ned14/HouseBuild/designs/20230313 Earth Tube Layout.pdf

Revision | Date | Details

NOTES

ALL DRAWINGS TO BE PRINTED AT 100% SCALE. DO NOT FIT TO PRINTER MARGINS WHEN PRINTING. DO NOT SCALE DIMENSIONS FROM THE DRAWING. USE FIGURED DIMENSIONS ONLY.

1. | This | drawing | is | copyright | of | Rebel Design Studio.
Reproduction is only to take place with written authority.

### 2. These plans are subject to Planning & Building Regulation

Approval or any other statute in law before building work commences.

### 3. Any structural work where mentioned on this drawing is

subject to a qualified structural and civil engineer calculations before building work commences.

### 4. All boundaries are assumed. To be confirmed on site before

building work commences.

### 5. Any discrepancies are to be brought to the attention of Rebel

Design Studio for rectification. If in doubt, ASK.

### 6. Only drawings marked as CONSTRUCTION status can be used to

build or manufacture from.

### 7. All windows and doors shown on schedules and drawings are

indicative only and no manufacturing should be carried out until a site survey has been conducted by manufacturer.

### 8. The survey information shown on this drawing is based on a

survey prepared by a third party. Rebel Design Studio accept no responsibility for the accuracy or completeness of the survey.

Project Leader | SOL

# Douglas - Ard Na Si, Banteer

Drawing:

Stage:

# Earth Tube Layout

Project

Revision

Project Number | 21/020

# Technical Design

Drawing Number
110-101
Date | 13 March 2023

## 1:200, 1:100 Scale

Address | Ard Na Si Banteer Cork. 22 Chestnut Avenue,

Yiewsley,
West Drayton, UB78BT

info@rebeldesign-studio.com rebeldesign-studio.com

## 3,000 6,000 6,000 6,000 6,000 Approx. 3m 1,000

1,000

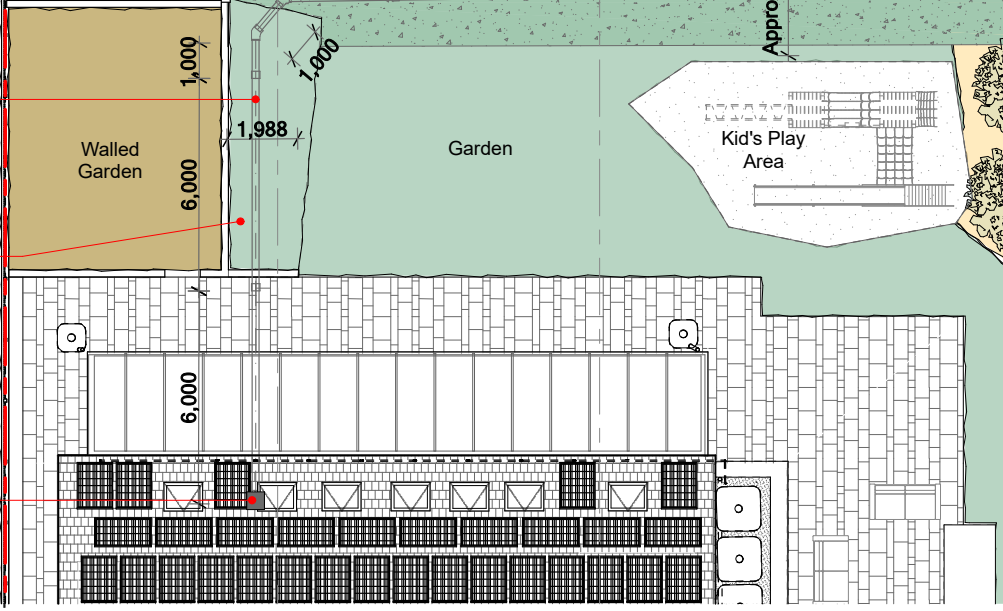
[picture p7: figure]
Walled Garden; Garden; Kid's Play Area

## Terrace Area

B
C

# Awadukt Thermo pipe DN 200 to have min. 1500mm cover . Exisng ground

levels to be made up where required.

# Condensaon collecon chamber DN 315/200 to be located in the Ulity

Room.

# Exisng mound to be excavated to allow for the installaon of the earth tube pipes. Mound to be be built up

to provide min. 1500mm cover.

# Exisng ground levels to be made up locally here to create 1500mm ground

cover - exact levels TBC on site.

# GAHE air inlet

tower DN 200.

## Reed Bed

+83,282

+80,259

+74,800 ²,700

+82,354 | Min. 1500mm cover
+74,534 | +74,493 | 2,200

1,000

## 6 m²

# Exisng tree and shrub planted embankment

and drainage channel.

# Secon of exisng embankment/ground to

be removed to allow for earth tube installaon.

# New earth tube laid at 4% fall from air inlet point

to change in direcon.

Approx. line of exisng embankment.

# New approx. outline of embankment to be created. Top of mound to be approx. 2.2m above the

proposed ground level for the enre length of the mound.

# New 2500mm deep condensaon collecon

sha. | New earth tube laid at 3%
| fall to chamber from
| change in direcon.

# Make up exisng ground levels locally to provide 1500mm min. ground

cover to earth tube run. | boundary line 2,500 | 500

1:100
0 | 2.5 | 5 | 7.5

1:200
0 | 7.5 | 15m

# Proposed GA Site Plan - Earth Tube Layout

1:200

# Proposed Secon CC - Earth Tube Dwg

1:100
