ned14/HouseBuild/designs/20220715 Diagram of works.pdf

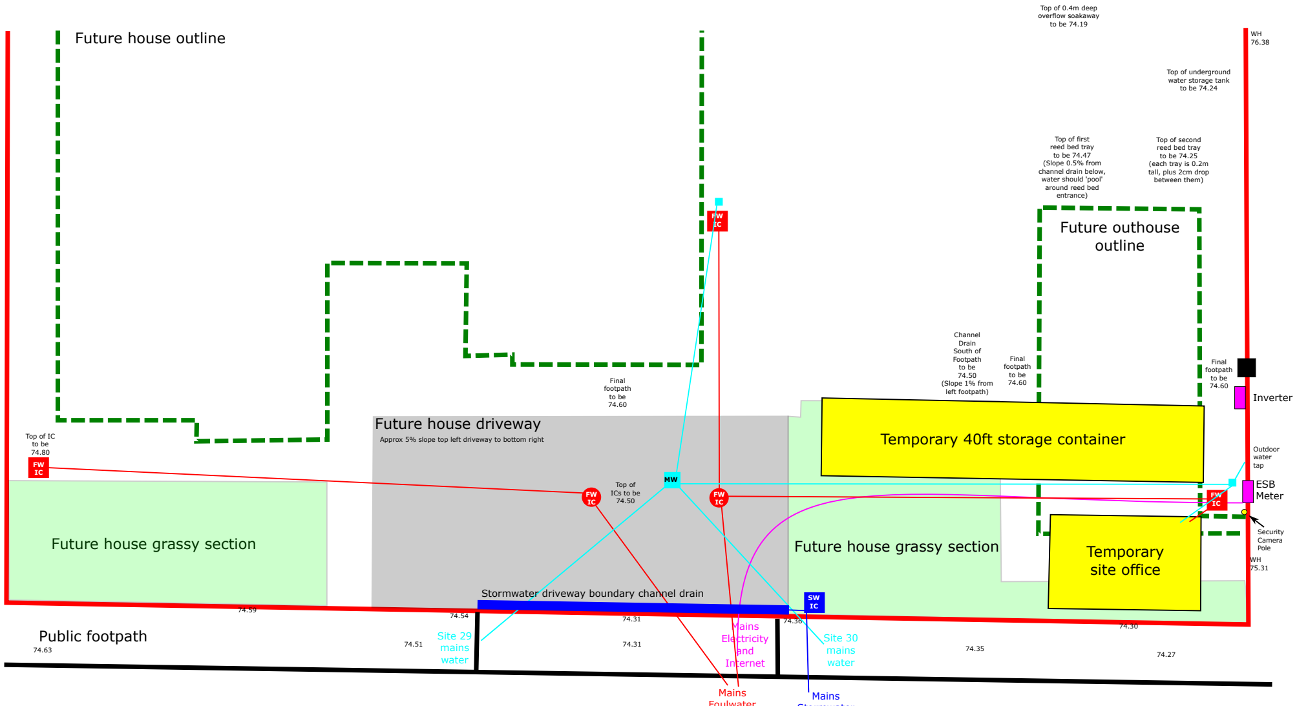
[picture p8: figure]
Future house driveway; Future house outline; Public footpath; Future outhouse outline; Final footpath to be 74.60; Top of IC to be 74.80; Channel Drain South of Footpath to be 74.50 (Slope 1% from left footpath); Top of first reed bed tray to be 74.47 (Slope 0.5% from channel drain below, water should 'pool' around reed bed entrance); Top of second reed bed tray to be 74.25 (each tray is 0.2m tall, plus 2cm drop between them); Top of ICs to be 74.50; Top of 0.4m deep overflow soakaway to be 74.19; Top of underground water storage tank to be 74.24; Temporary 40ft storage container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

Future house grassy section | Future house grassy section
74.36 | 74.27

Approx 5% slope top left driveway to bottom right

## Foulwater Stormwater

## Stormwater driveway boundary channel drain
