ned14/HouseBuild/tech_docs/CIG965 - Greenhouse.pdf

### Dimensions

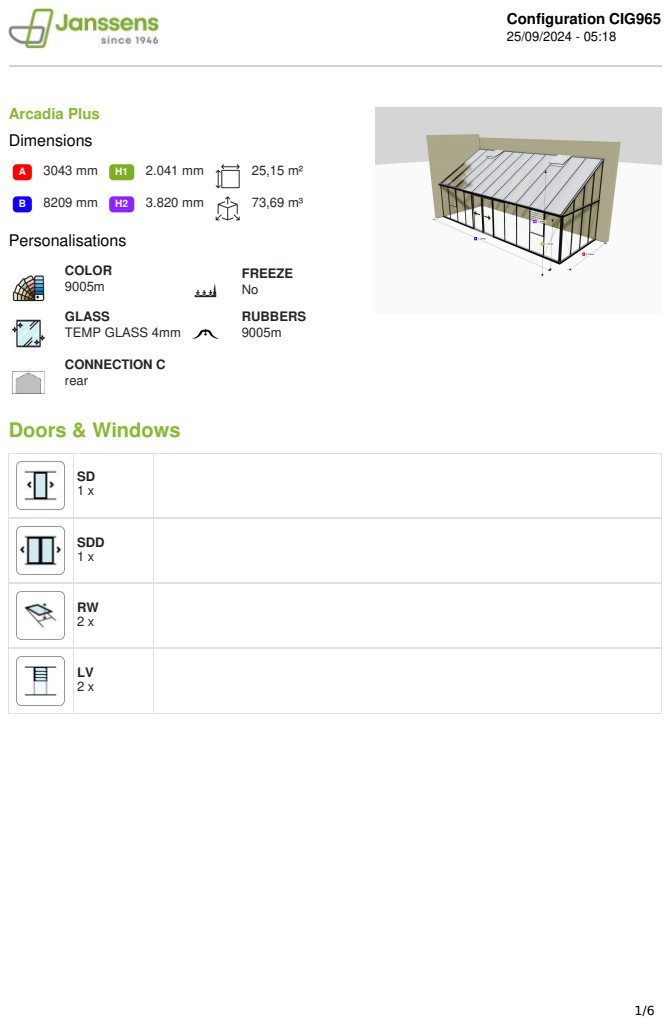
[picture p9: page 1]
Arcadia Plus; Personalisations; COLOR 9005m; FREEZE No; GLASS TEMP GLASS 4mm; RUBBERS 9005m; CONNECTION C rear; Doors & Windows; Configuration CIG965 25/09/2024 - 05:18

SDD 1 x

## 3D view

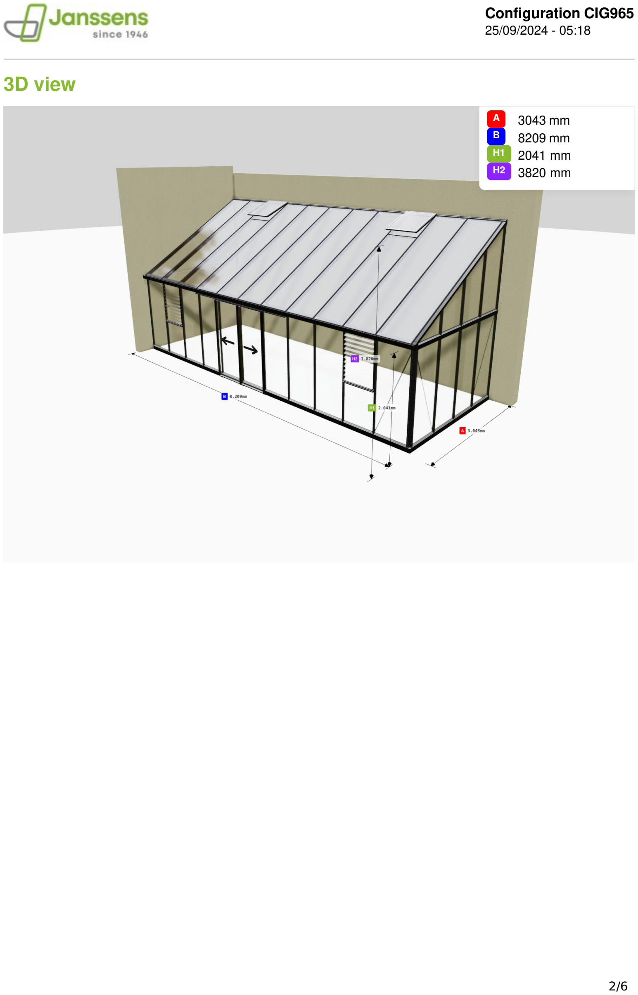
[picture p10: page 2]

25/09/2024 - 05:18

A
B
H1
H2

3043 mm
8209 mm
2041 mm
3820 mm

## Front side 1/100

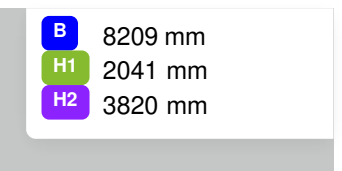
[picture p11: figure]

100cm

## Left side 1/100

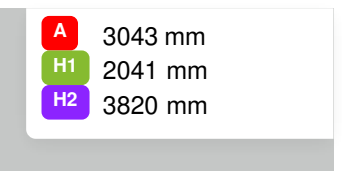
[picture p12: figure]

100cm

## Right side 1/100

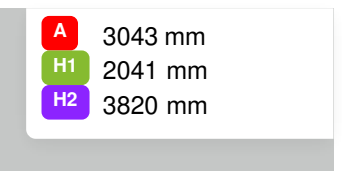
[picture p13: figure]

100cm

## Top side 1/100

100cm

A
B

3043 mm
8209 mm
