ned14/HouseBuild/tech_docs/LWR744 - Pool.pdf

### Dimensions

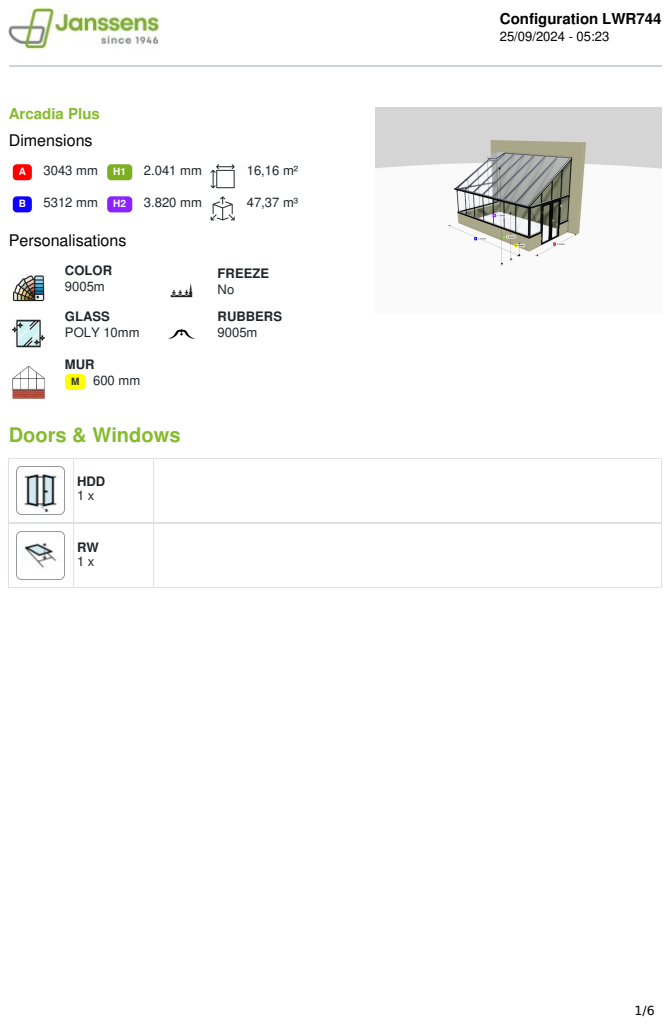
[picture p14: page 1]
Arcadia Plus; Personalisations; COLOR 9005m; FREEZE No; GLASS POLY 10mm; RUBBERS 9005m; MUR M 600 mm; Doors & Windows; Configuration LWR744 25/09/2024 - 05:23

HDD 1 x

## 3D view

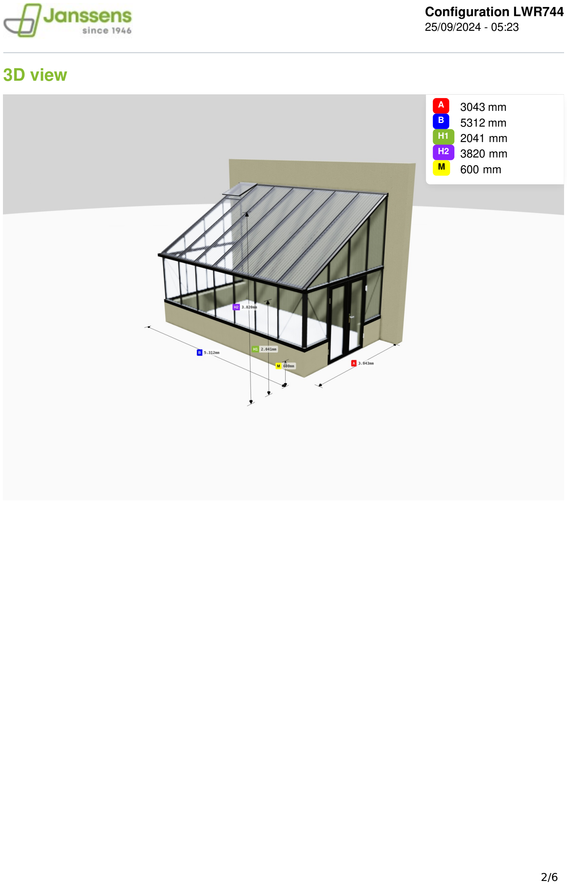
[picture p15: page 2]

25/09/2024 - 05:23

A
B
H1
H2
M

3043 mm
5312 mm
2041 mm
3820 mm
600 mm

## Front side 1/50

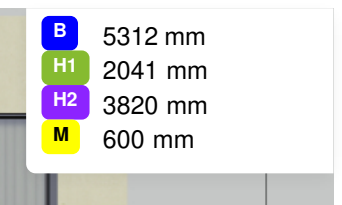
[picture p16: figure]

50cm

## Left side 1/50

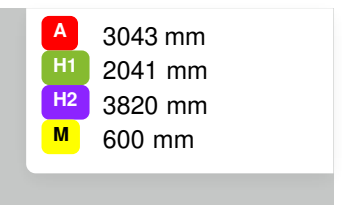
[picture p17: figure]

50cm

## Right side 1/50

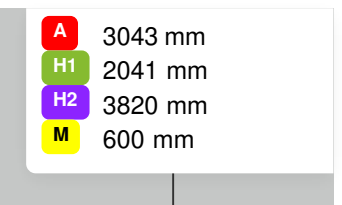
[picture p18: figure]

50cm

## Top side 1/50

50cm

A
B

3043 mm
5312 mm
