ned14/HouseBuild/tech_docs/ULS758 - Conservatory.pdf

### Dimensions

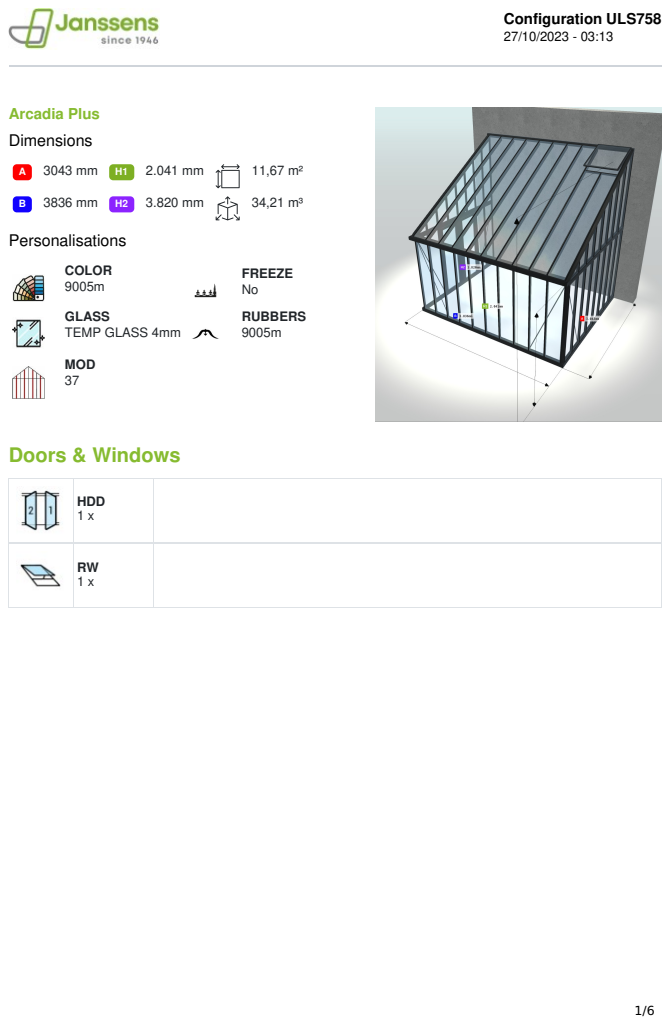
[picture p19: page 1]
Arcadia Plus; Personalisations; COLOR 9005m; FREEZE No; GLASS TEMP GLASS 4mm; RUBBERS 9005m; MOD 37; Doors & Windows; Configuration ULS758 27/10/2023 - 03:13

HDD 1 x

## 3D view

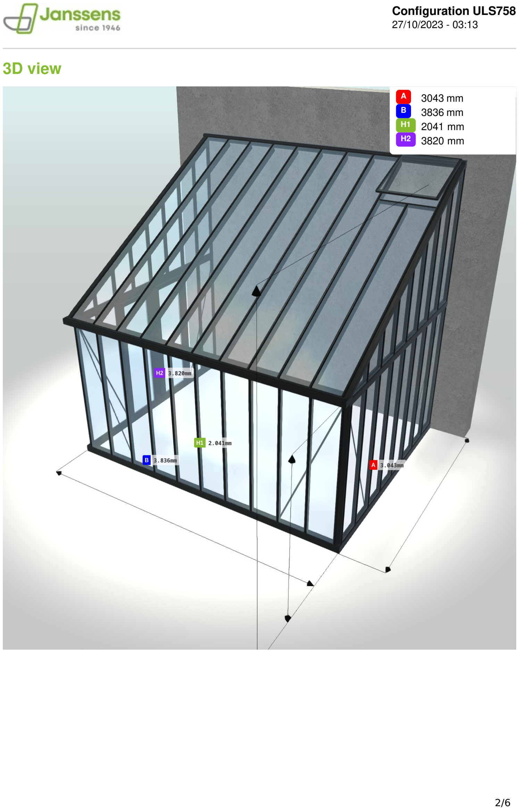
[picture p20: page 2]

27/10/2023 - 03:13

A
B
H1
H2

3043 mm
3836 mm
2041 mm
3820 mm

## Front side 1/50

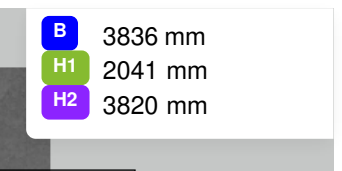
[picture p21: figure]

50cm

## Left side 1/50


50cm

## Right side 1/50

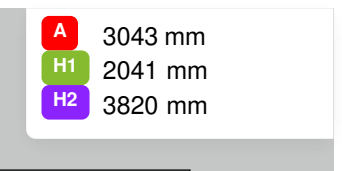
[picture p22: figure]

50cm

## Top side 1/50

50cm

A
B

3043 mm
3836 mm
