ned14/HouseBuild/designs/20210511 Original garden concept before house design.pdf

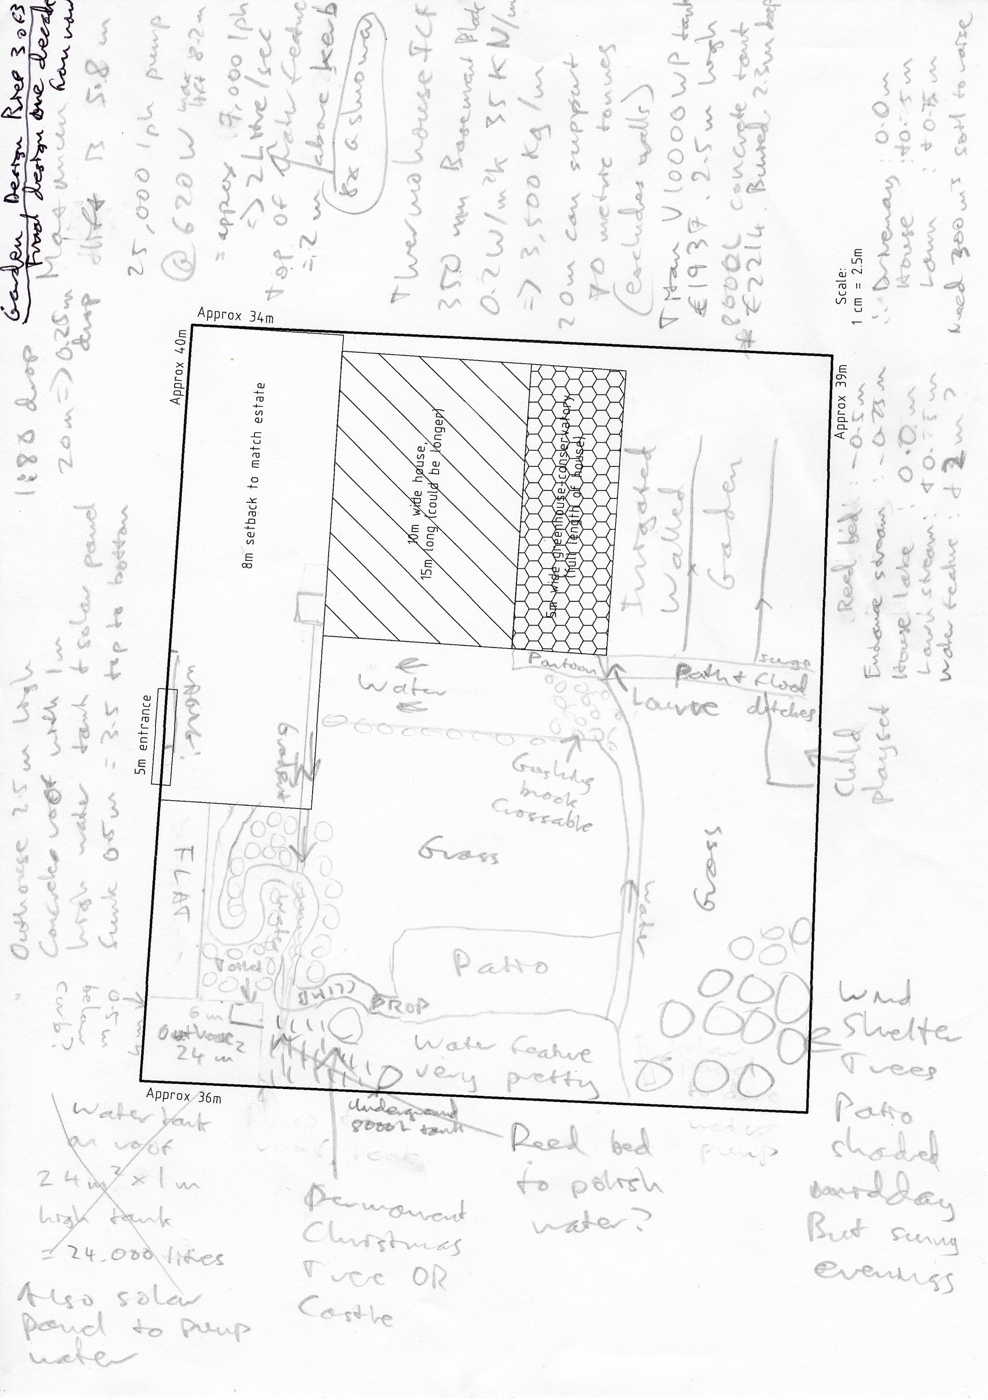
[picture p34: page 1]
