ned14/HouseBuild/designs/20220818 Large Scale Water Feature Concept.pdf

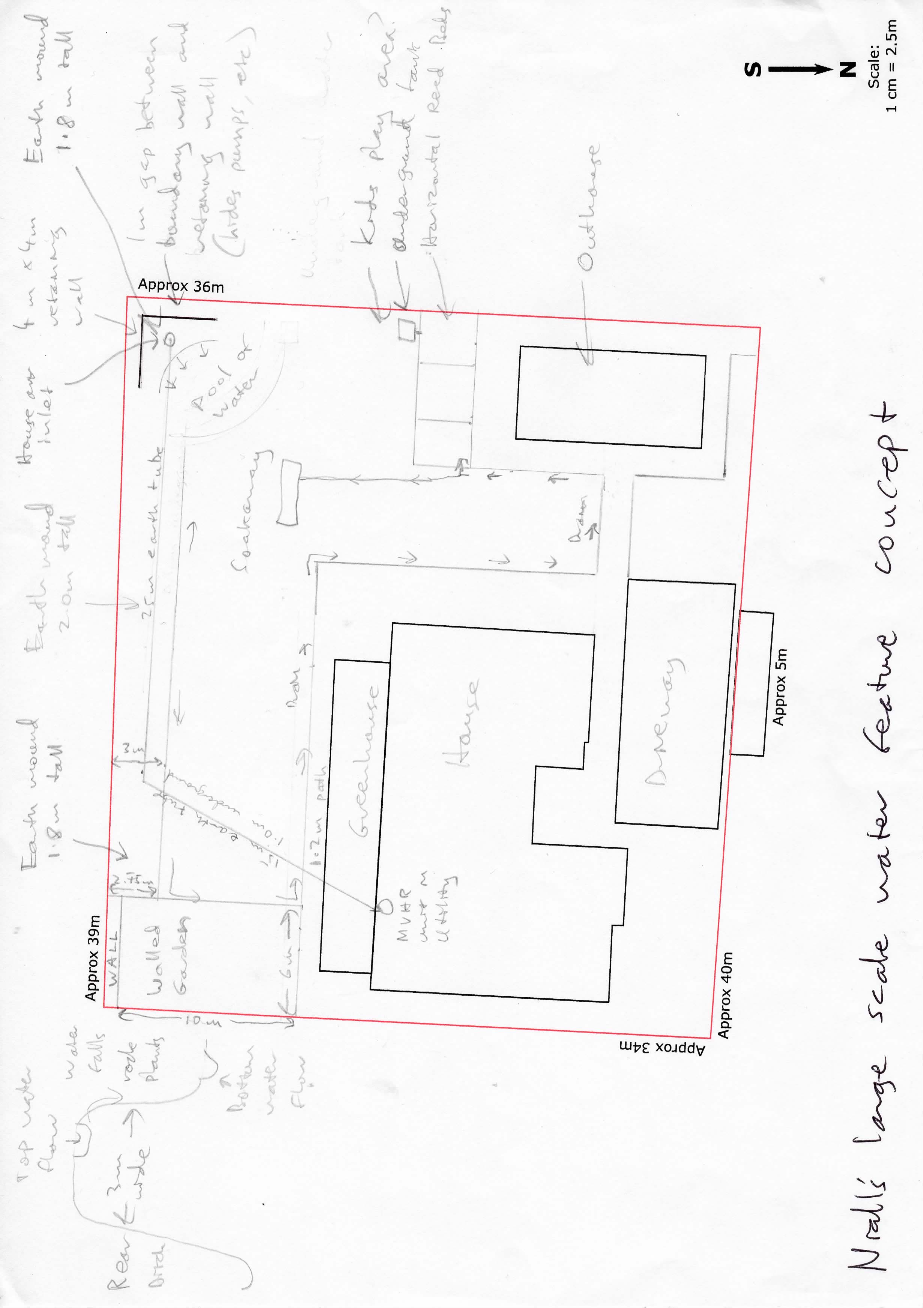
[picture p35: page 1]
