ned14/HouseBuild/images/202103/20210324_095312.jpg

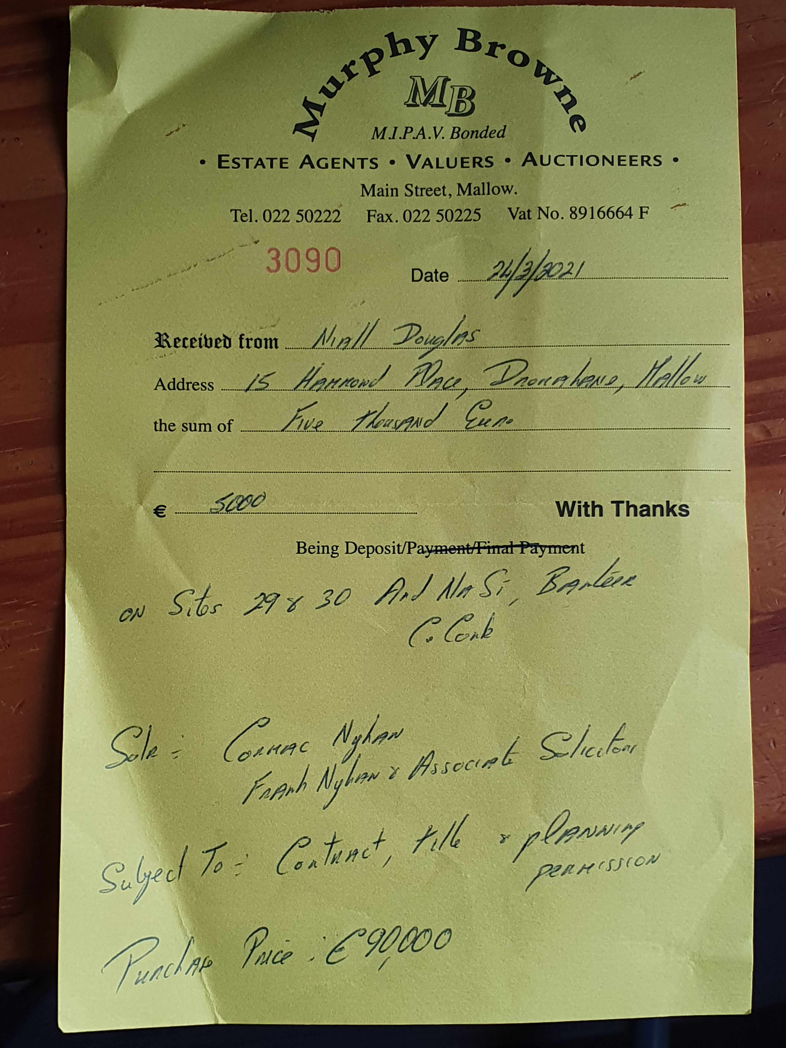
images/202103/20210324_095312.jpg
