ned14/HouseBuild/images/202103/surrounding_houses_sm.jpg

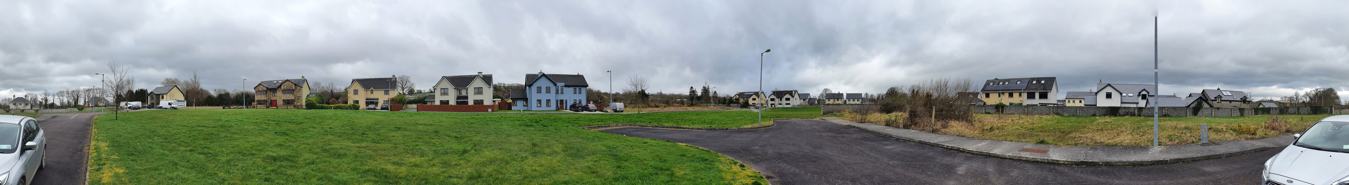
images/202103/surrounding_houses_sm.jpg
