ned14/HouseBuild/images/202103/view_to_the_south_zoomed_sm.jpg

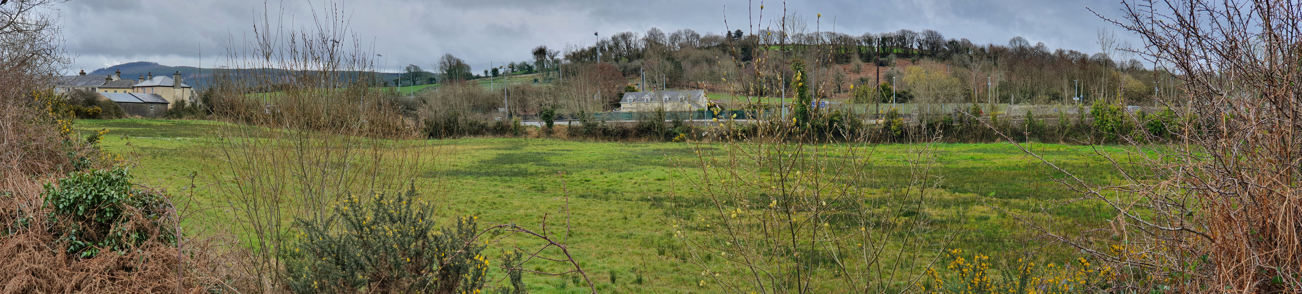
images/202103/view_to_the_south_zoomed_sm.jpg
