ned14/HouseBuild/images/202107/20210727_121713.jpeg

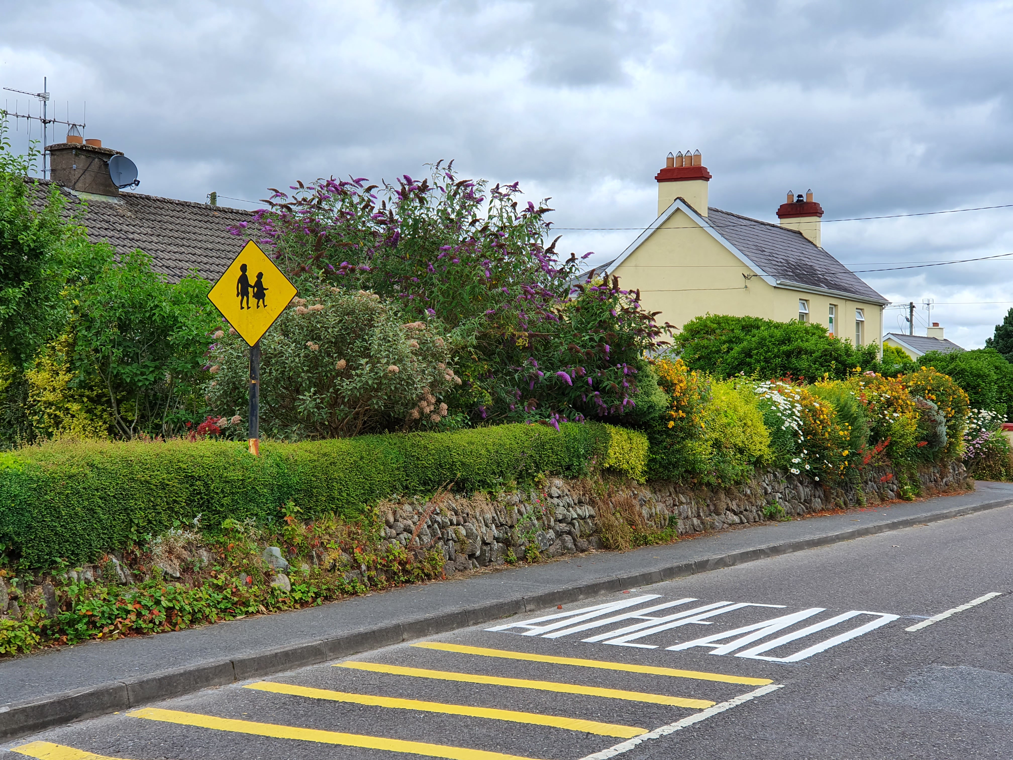
images/202107/20210727_121713.jpeg
