ned14/HouseBuild/images/202202/AerialView.jpg

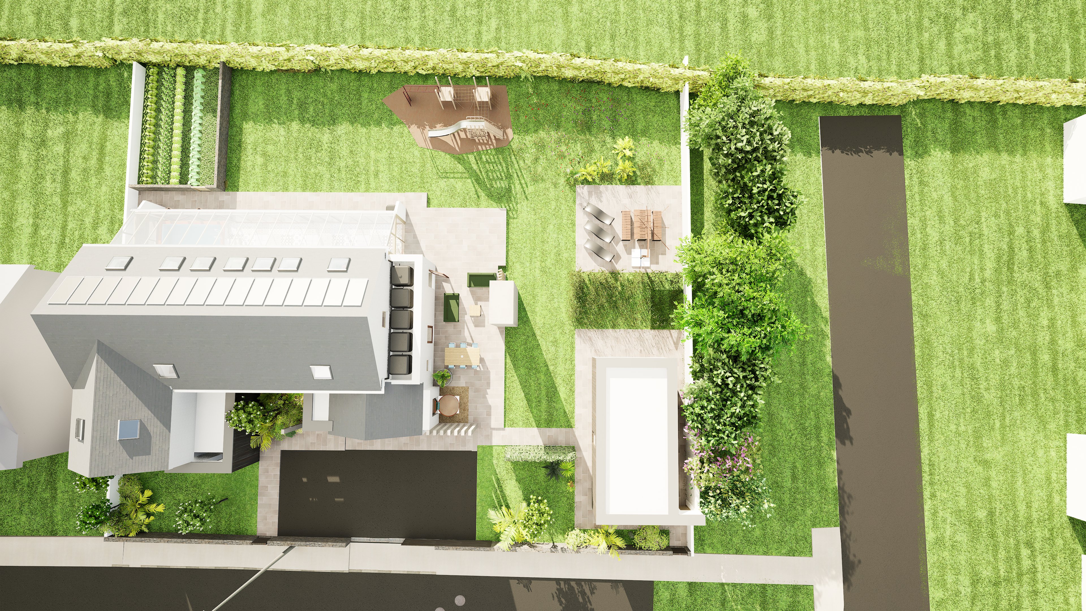
images/202202/AerialView.jpg
