ned14/HouseBuild/images/202202/BackCornerView.jpg

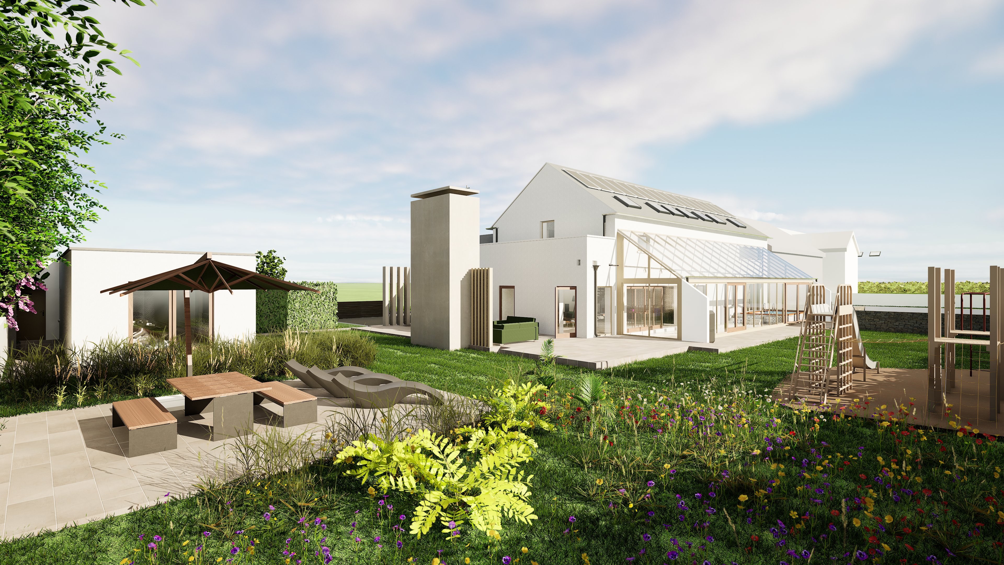
images/202202/BackCornerView.jpg
