ned14/HouseBuild/images/202202/BridgeLookingAtKitchen.jpg

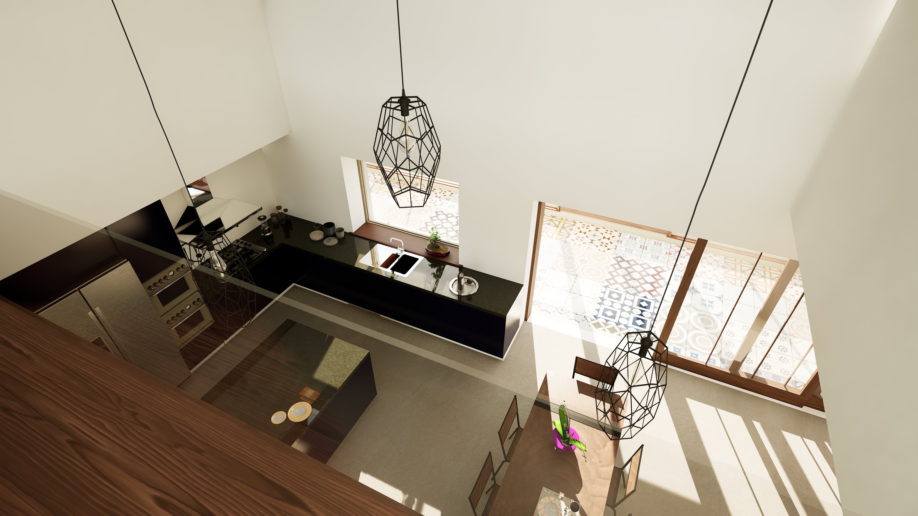
images/202202/BridgeLookingAtKitchen.jpg
