ned14/HouseBuild/images/202202/BridgeLookingAtMezzanine.jpg

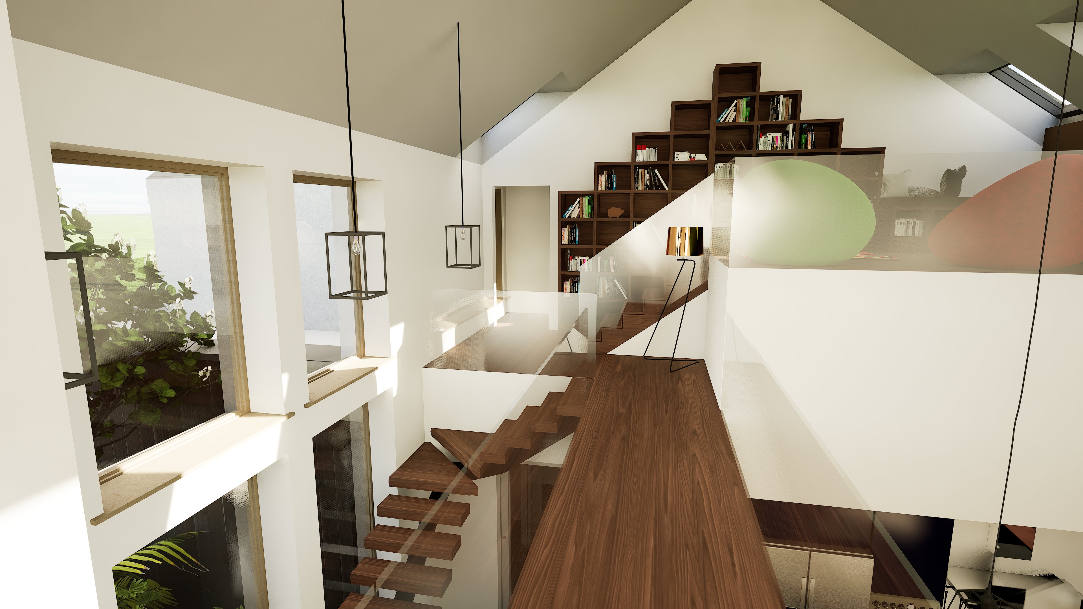
images/202202/BridgeLookingAtMezzanine.jpg
