ned14/HouseBuild/images/202202/GamesRoom.jpg

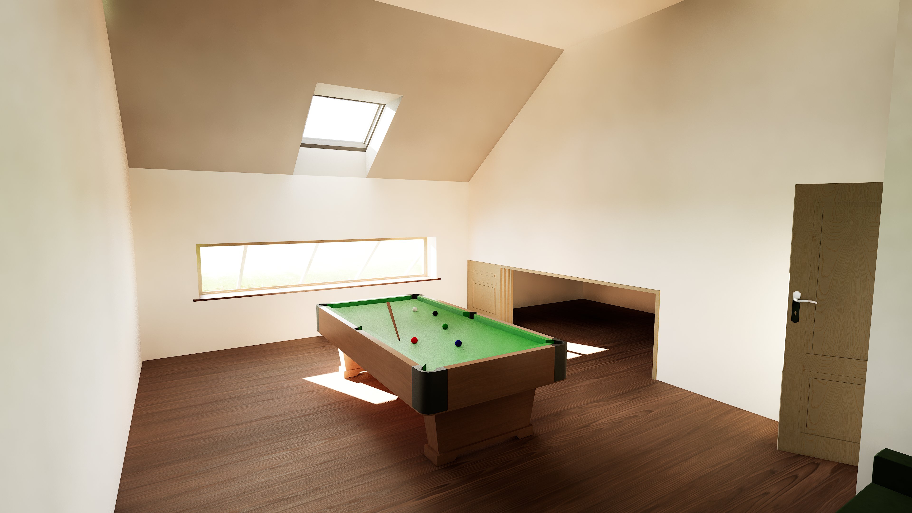
images/202202/GamesRoom.jpg
