ned14/HouseBuild/images/202202/GreenhouseDoorLookingUp.jpg

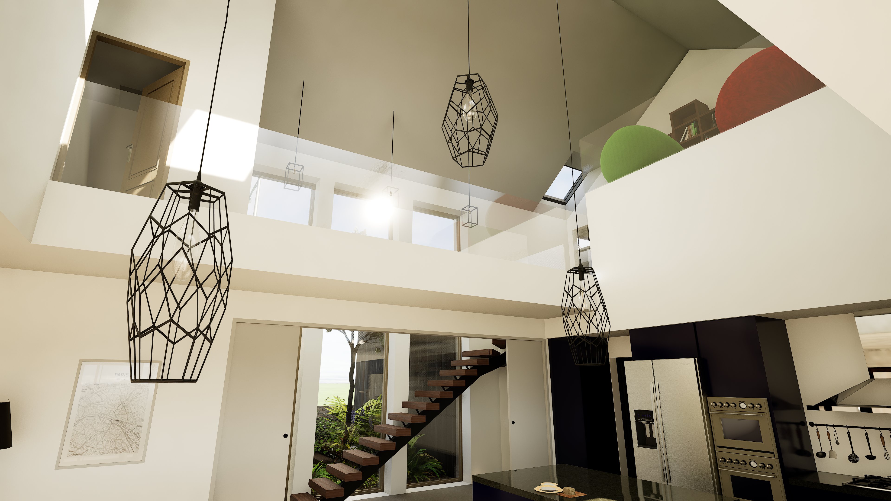
images/202202/GreenhouseDoorLookingUp.jpg
