ned14/HouseBuild/images/202202/KitchenLookingForwards.jpg

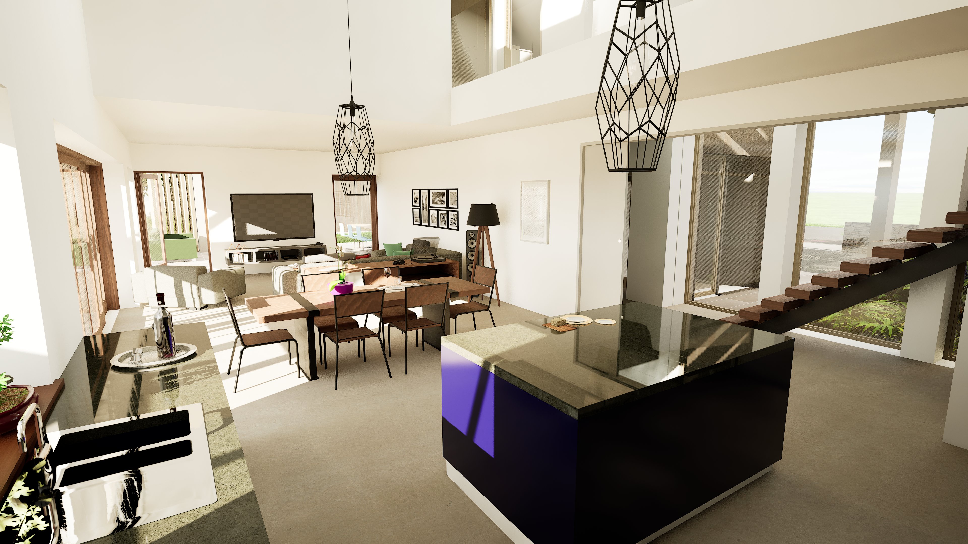
images/202202/KitchenLookingForwards.jpg
