ned14/HouseBuild/images/202202/KitchenLookingUp.jpg

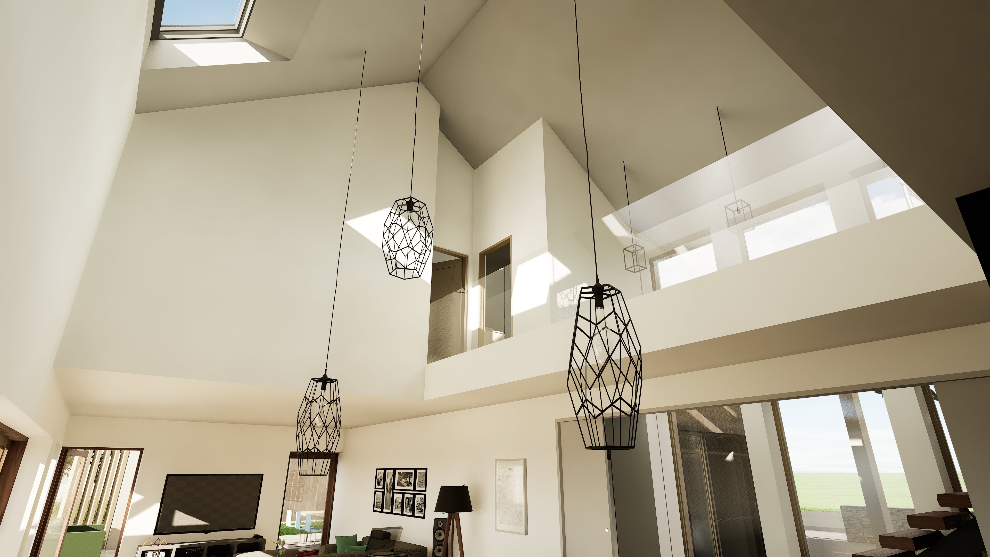
images/202202/KitchenLookingUp.jpg
