ned14/HouseBuild/images/202202/LarderDoorLookingOut.jpg

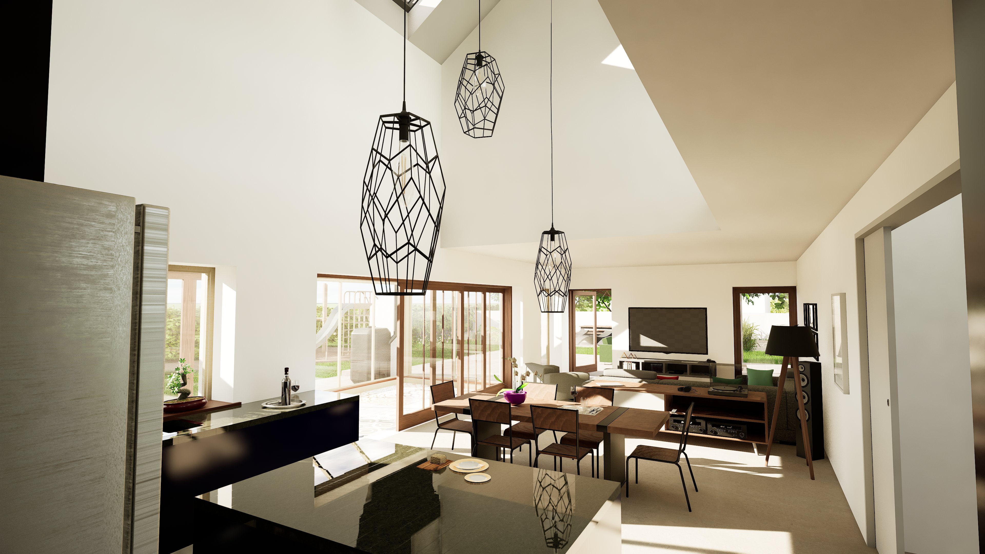
images/202202/LarderDoorLookingOut.jpg
