ned14/HouseBuild/images/202202/LivingRoomLookingAtKitchen.jpg

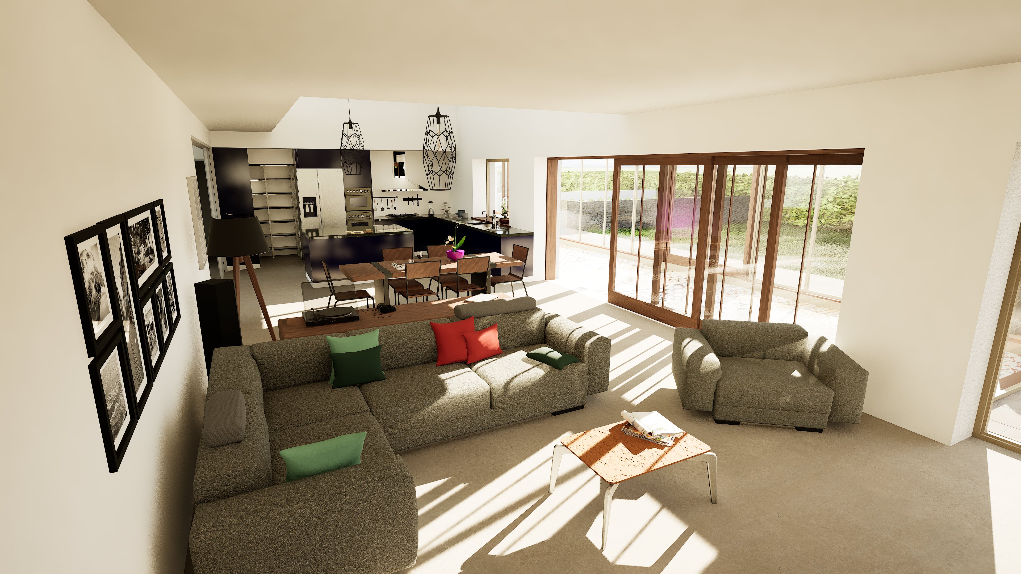
images/202202/LivingRoomLookingAtKitchen.jpg
