ned14/HouseBuild/images/202202/LobbyExitLookingAtKitchen.jpg

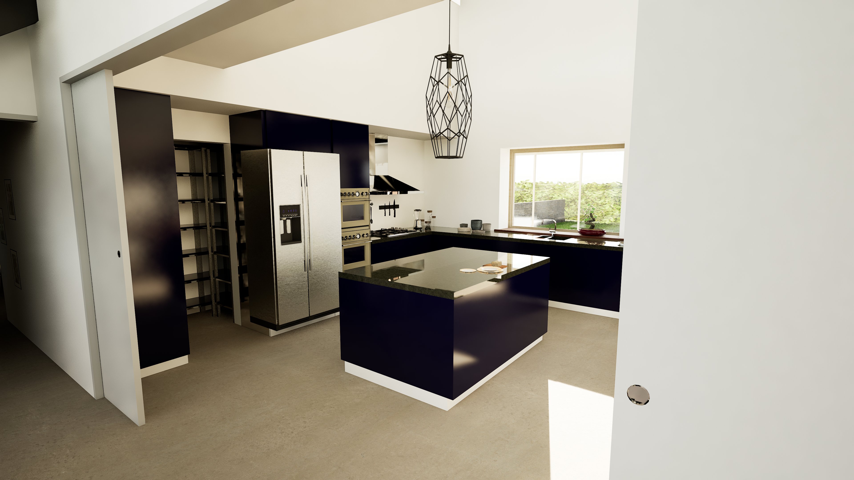
images/202202/LobbyExitLookingAtKitchen.jpg
