ned14/HouseBuild/images/202202/MainRoadAwayFromHouse.jpg

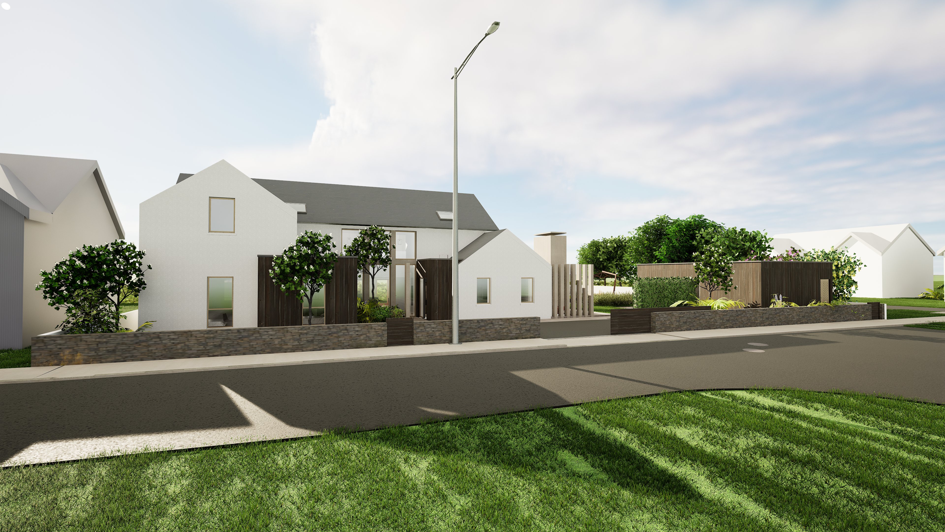
images/202202/MainRoadAwayFromHouse.jpg
