ned14/HouseBuild/images/202202/MainRoadFrontOfHouse.jpg

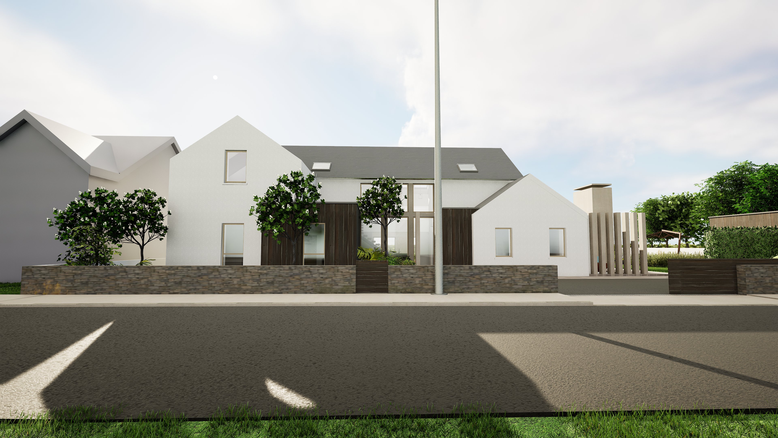
images/202202/MainRoadFrontOfHouse.jpg
