ned14/HouseBuild/images/202202/MainRoadOutsideSideView.jpg

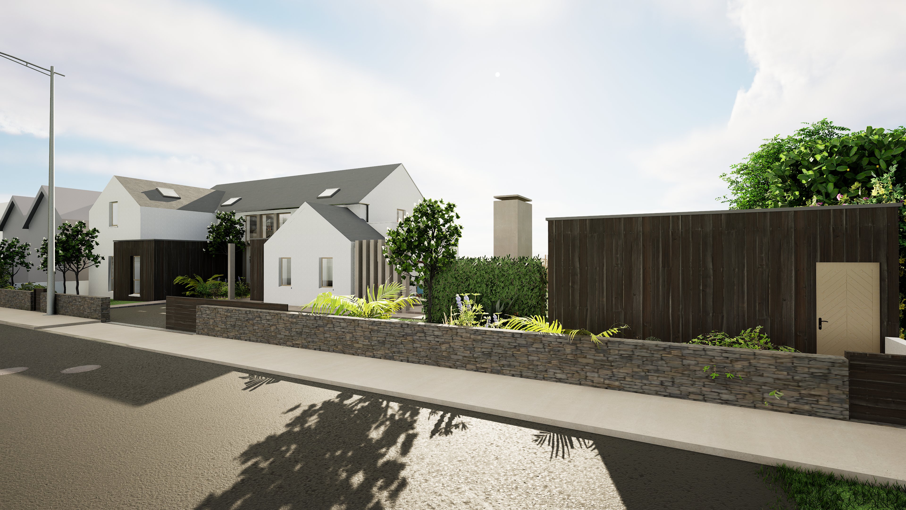
images/202202/MainRoadOutsideSideView.jpg
