ned14/HouseBuild/images/202202/MasterBedroom.jpg

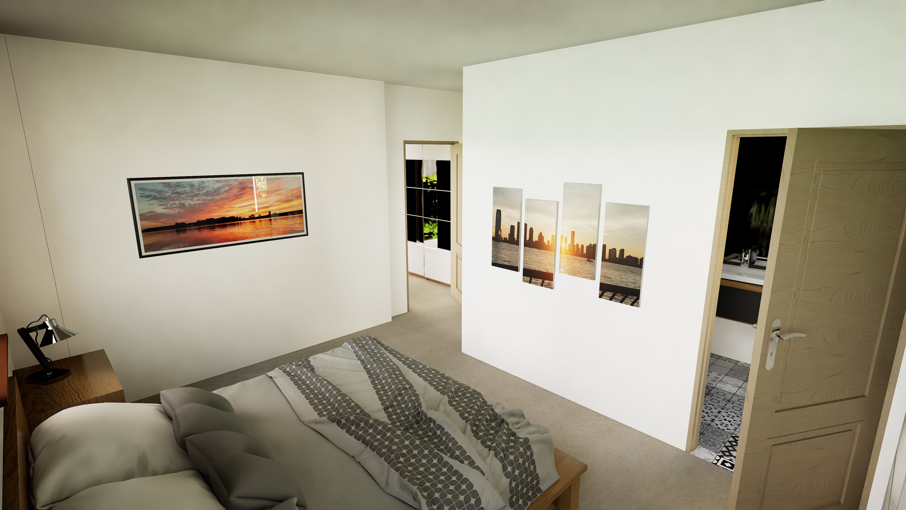
images/202202/MasterBedroom.jpg
