ned14/HouseBuild/images/202202/MezzanineLookingAtLiving.jpg

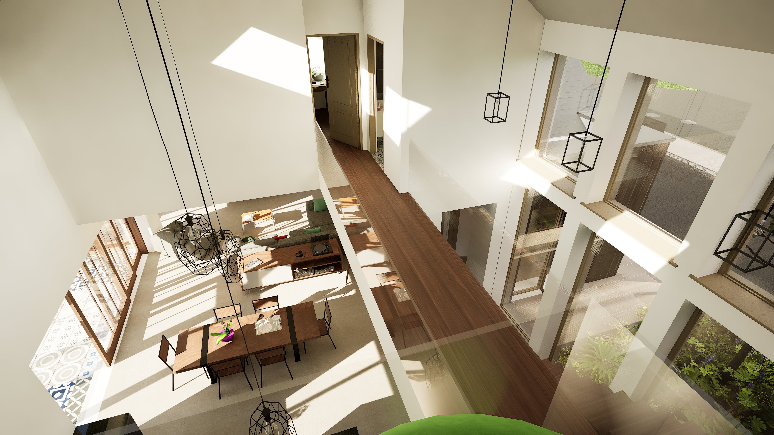
images/202202/MezzanineLookingAtLiving.jpg
