ned14/HouseBuild/images/202202/PatioDoorLookingIn.jpg

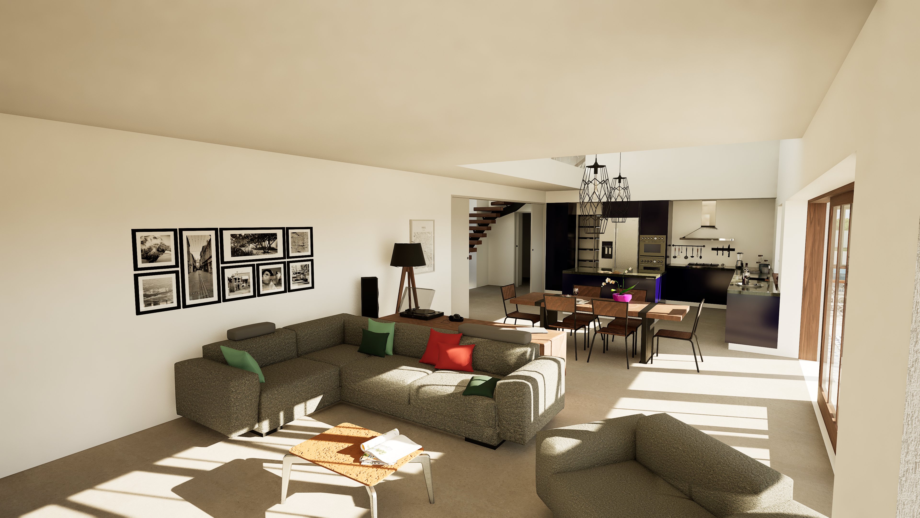
images/202202/PatioDoorLookingIn.jpg
