ned14/HouseBuild/images/202202/TopOfStairsLookingAtMezzanine.jpg

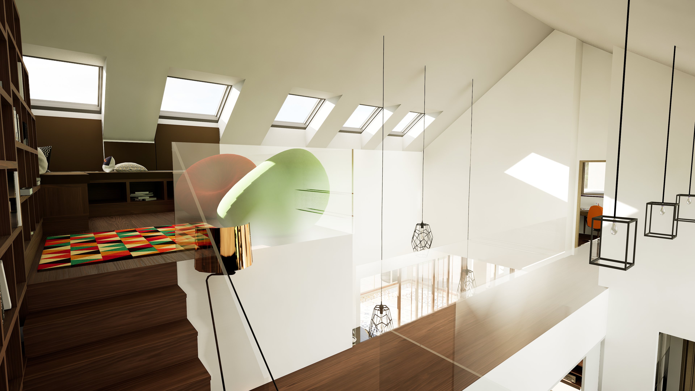
images/202202/TopOfStairsLookingAtMezzanine.jpg
