ned14/HouseBuild/images/202202/WalledGardenView.jpg

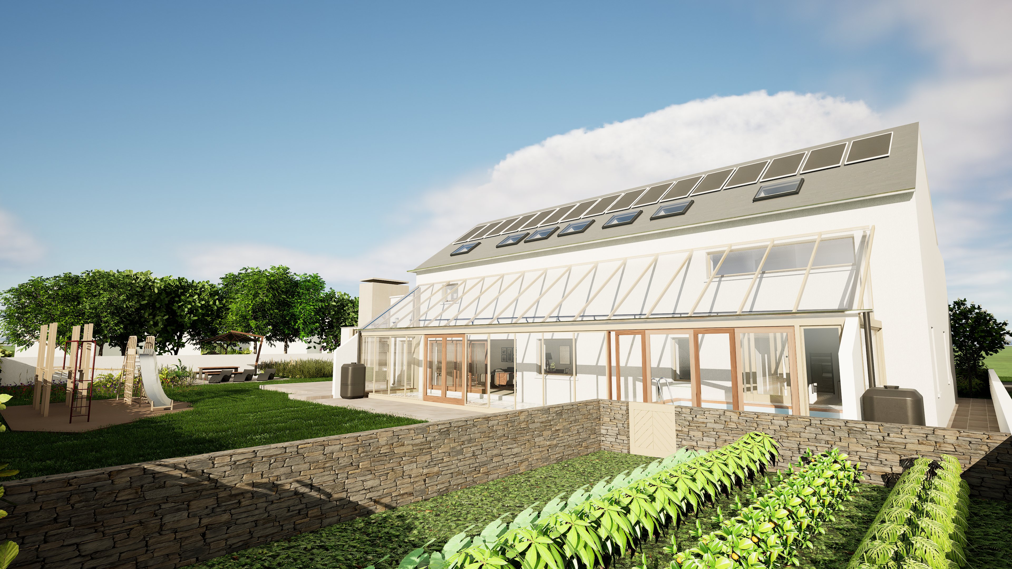
images/202202/WalledGardenView.jpg
