ned14/HouseBuild/images/202207/20220730_164701.jpg

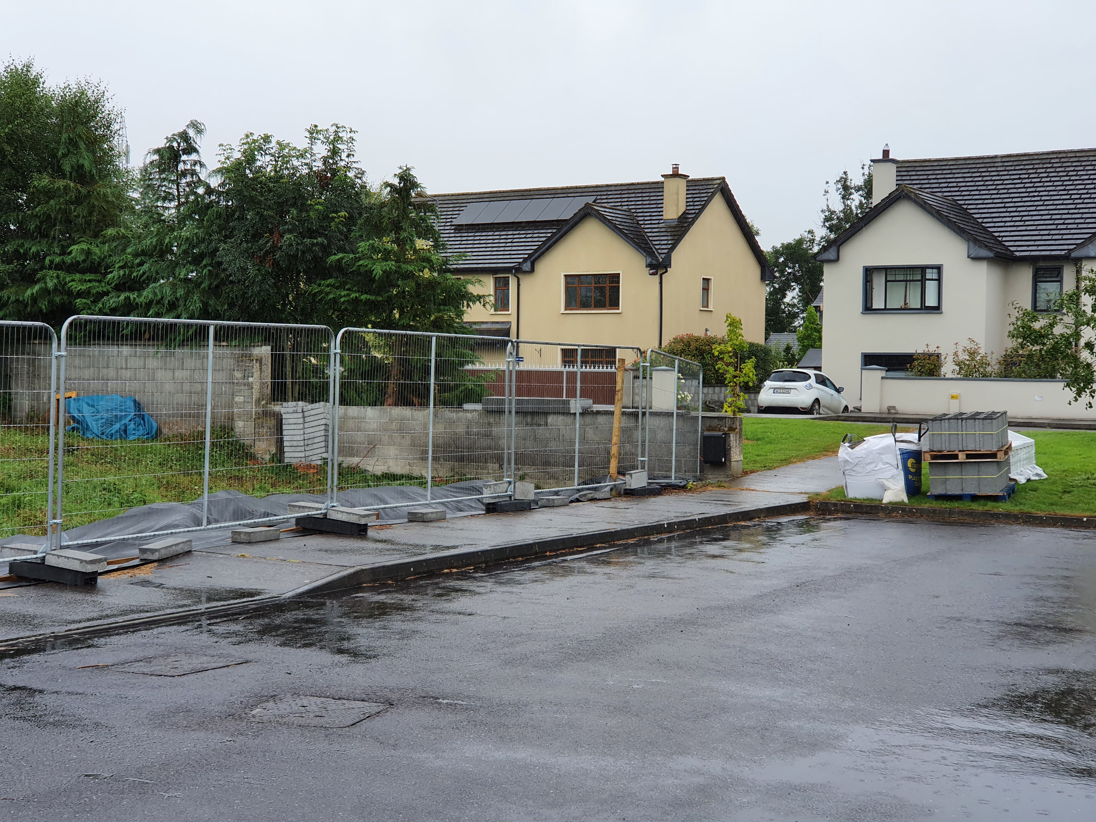
images/202207/20220730_164701.jpg
