ned14/HouseBuild/images/202208/20220801_213918.jpg

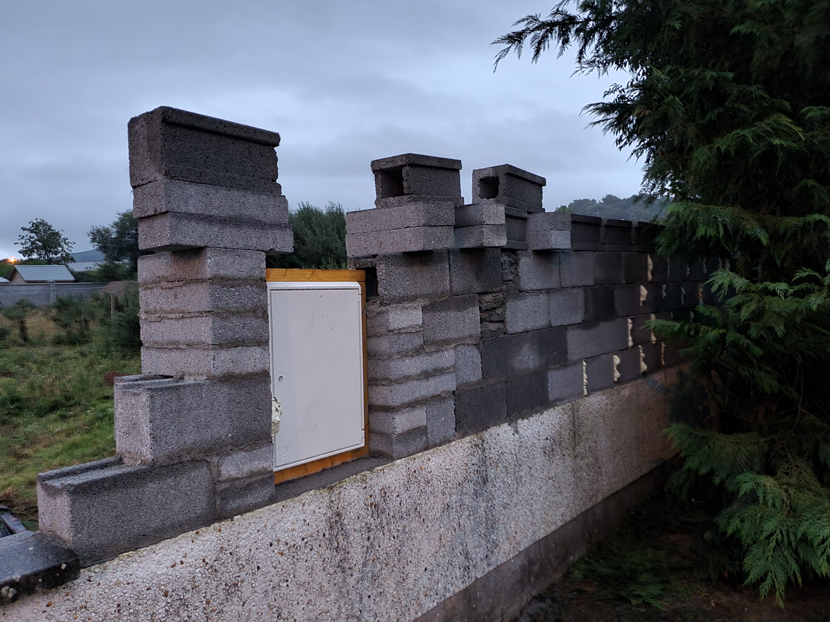
images/202208/20220801_213918.jpg
