ned14/HouseBuild/images/202208/20220801_213933.jpg

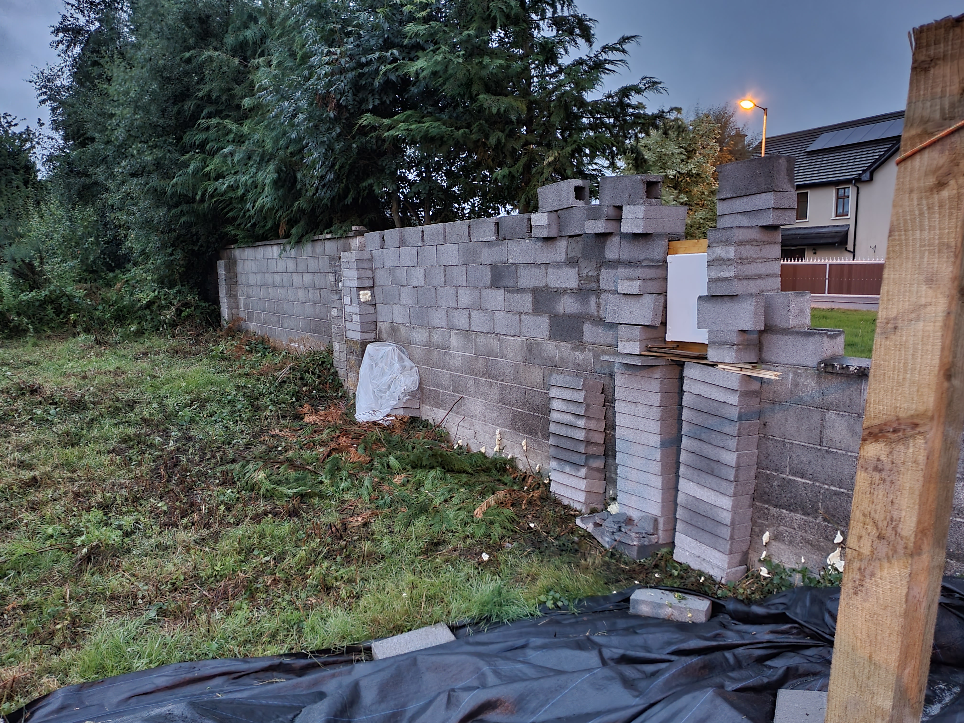
images/202208/20220801_213933.jpg
