ned14/HouseBuild/images/202208/20220814_213747.jpg

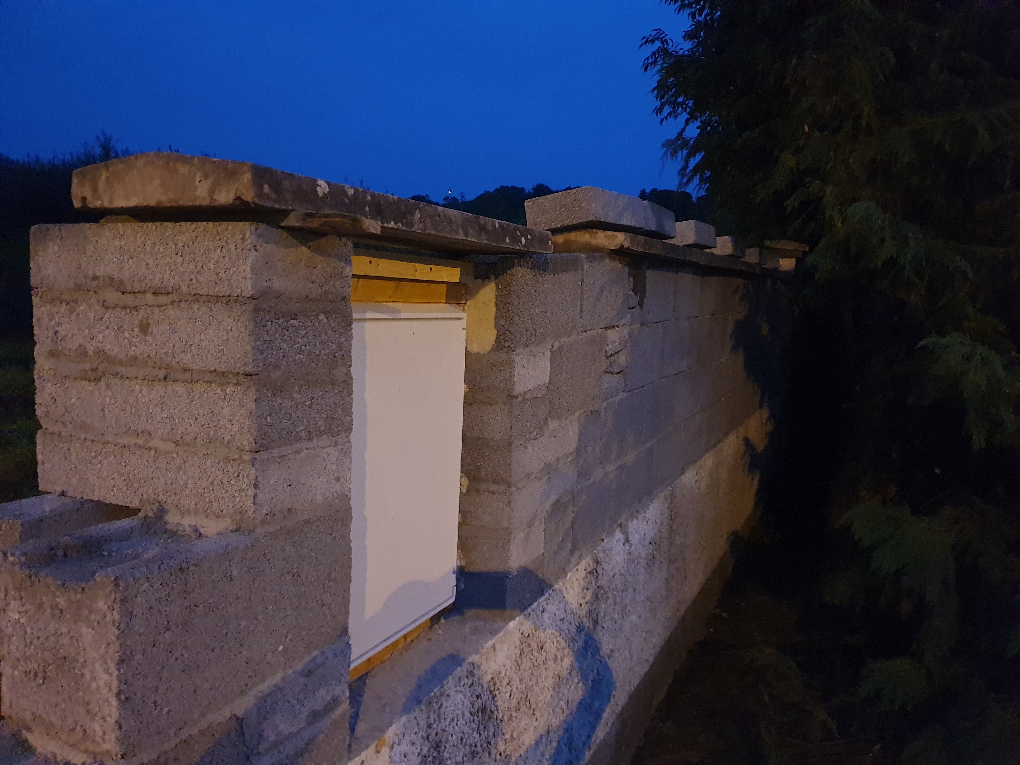
images/202208/20220814_213747.jpg
