ned14/HouseBuild/images/202209/20220919 Wngu5059960 - 3.jpg

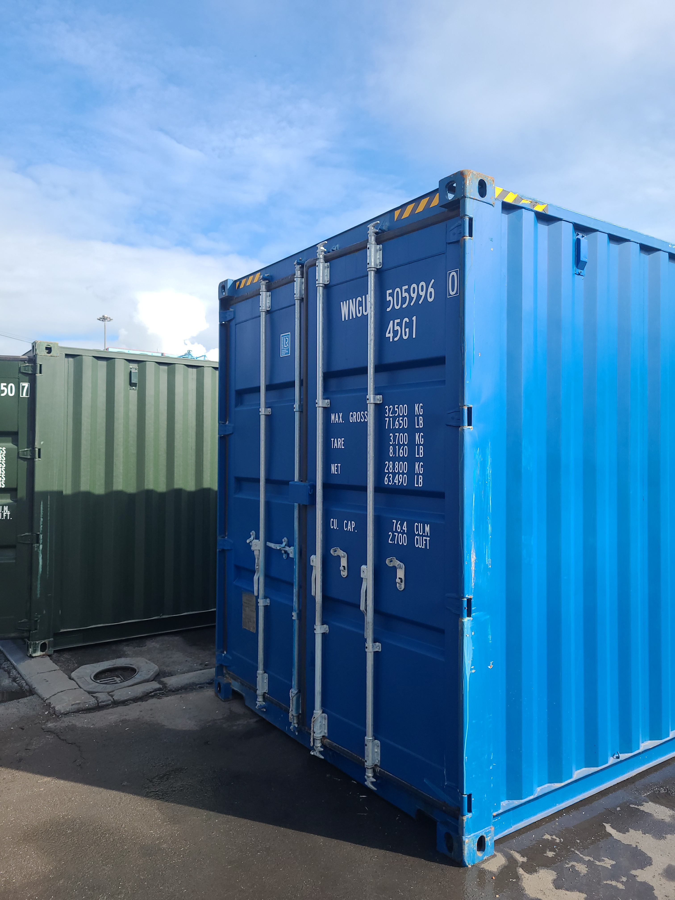
images/202209/20220919 Wngu5059960 - 3.jpg
