ned14/HouseBuild/images/202210/20221004_120137.jpg

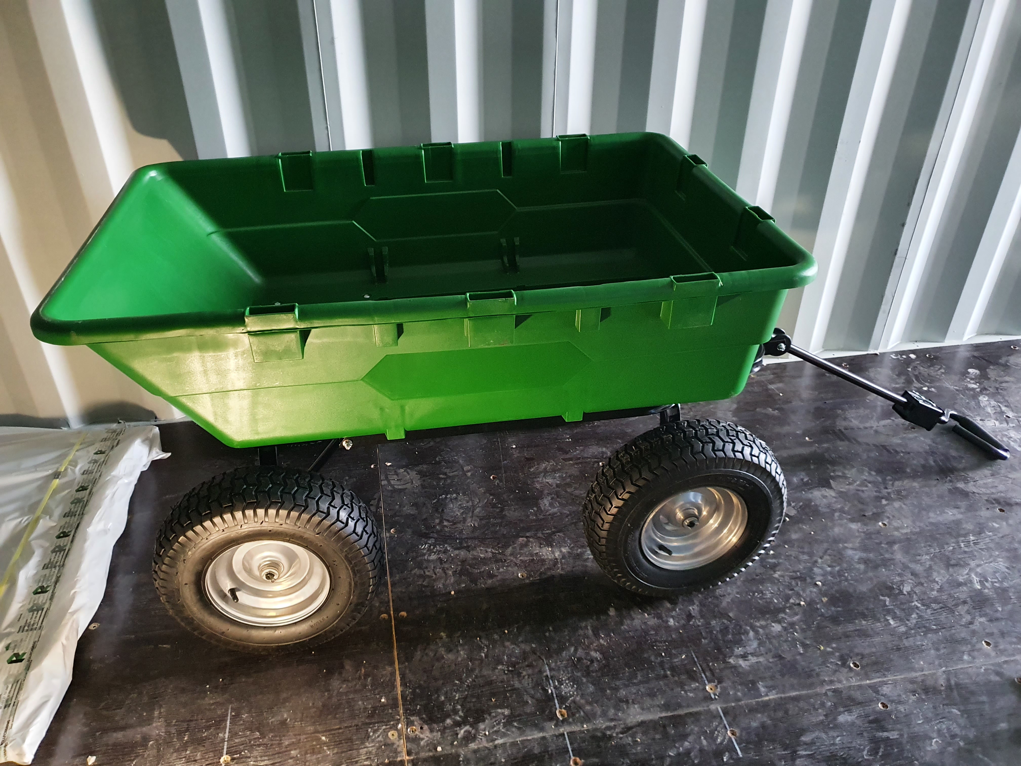
images/202210/20221004_120137.jpg
