ned14/HouseBuild/images/202210/20221008_222303.jpg

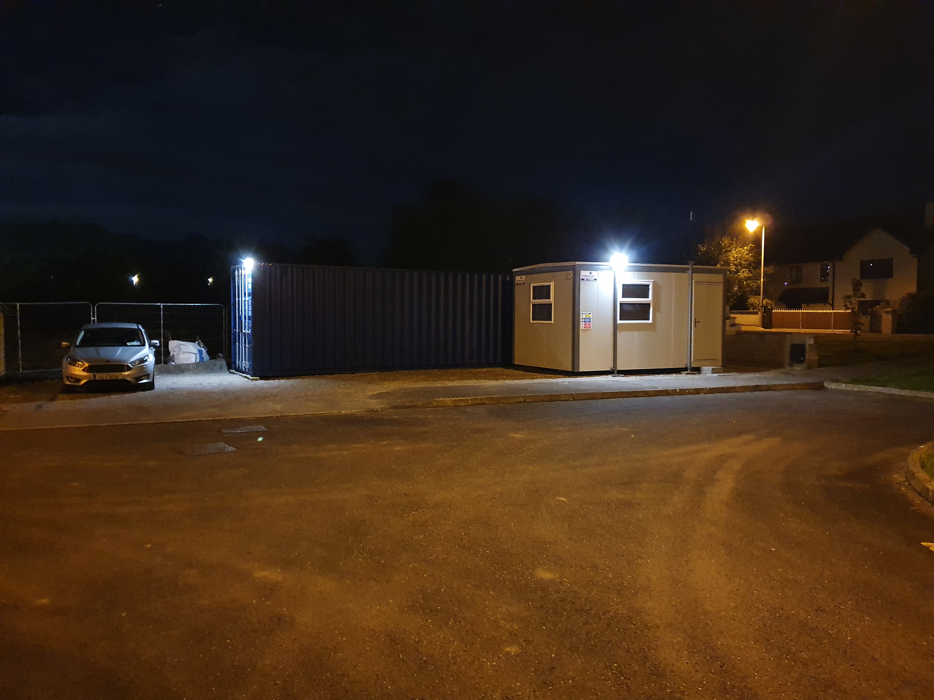
images/202210/20221008_222303.jpg
