ned14/HouseBuild/images/202210/20221022_191231.jpg

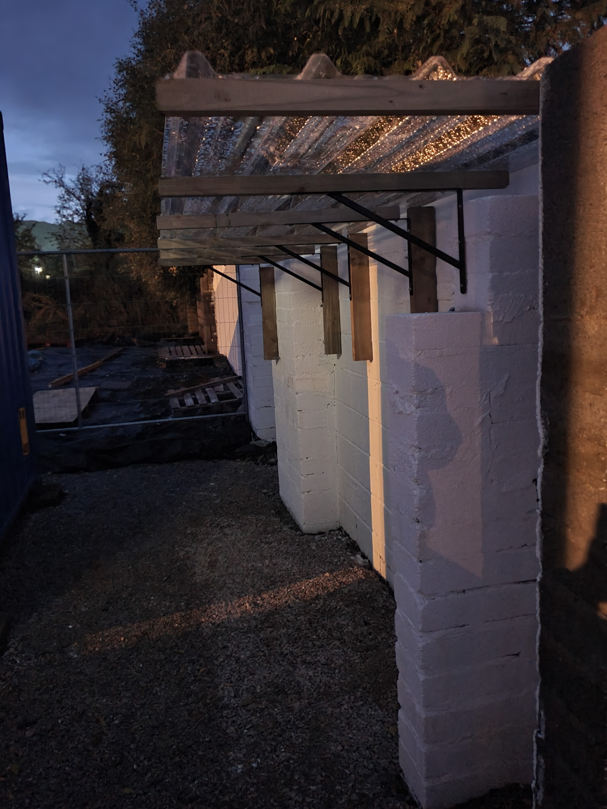
images/202210/20221022_191231.jpg
