ned14/HouseBuild/images/202210/20221028_125330.jpg

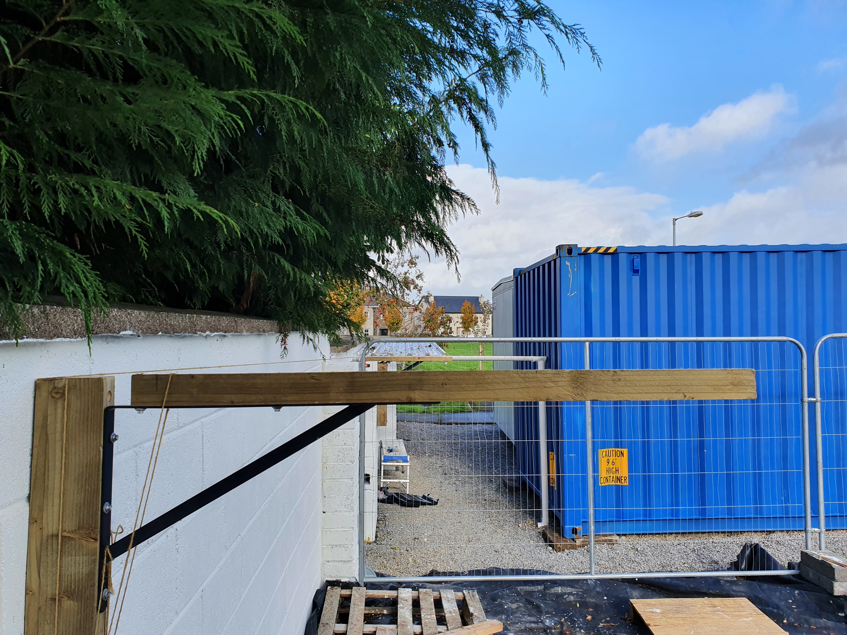
images/202210/20221028_125330.jpg
