ned14/HouseBuild/images/202210/20221029_183744.jpg

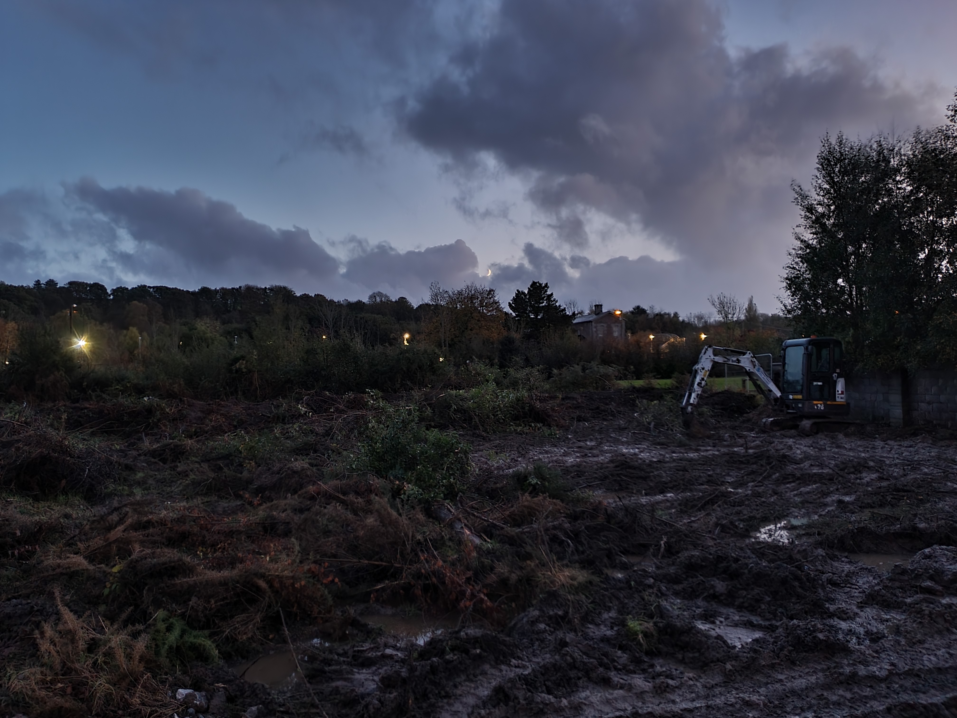
images/202210/20221029_183744.jpg
