ned14/HouseBuild/images/202212/20221205_033924.jpg

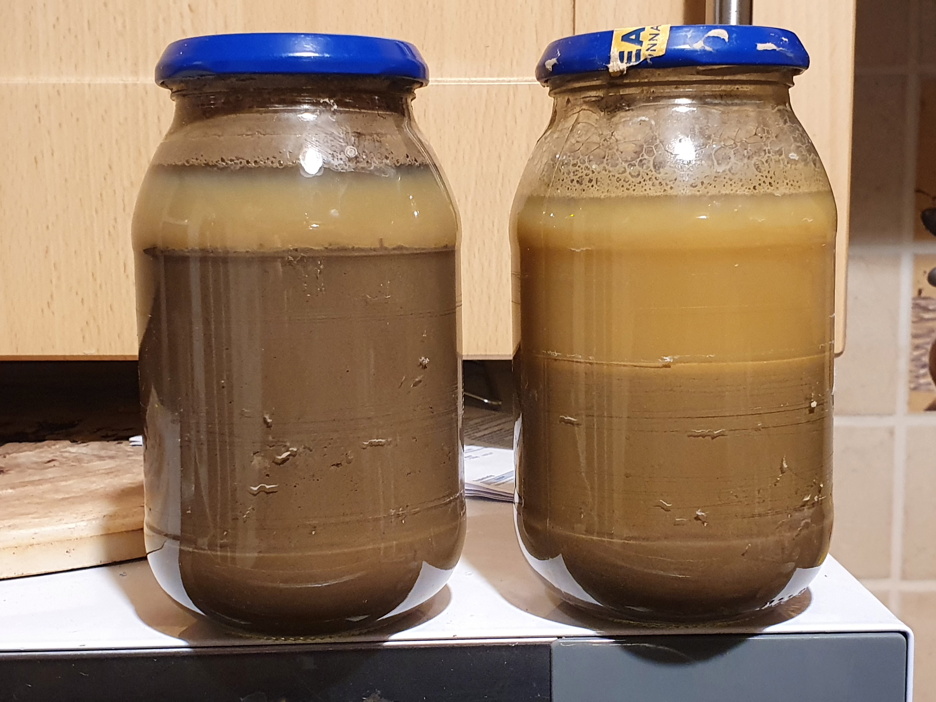
images/202212/20221205_033924.jpg
