ned14/HouseBuild/images/202212/20221208_101856.jpg

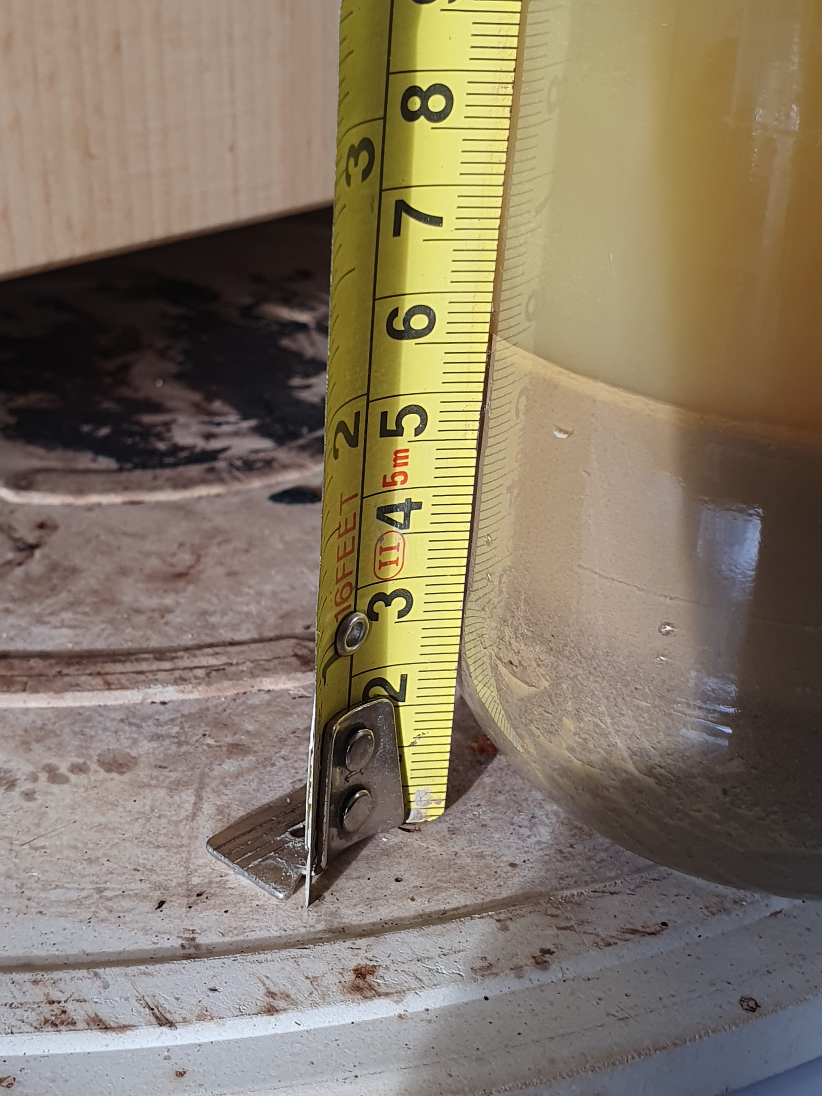
images/202212/20221208_101856.jpg
