ned14/HouseBuild/images/202212/20221208_102116.jpg

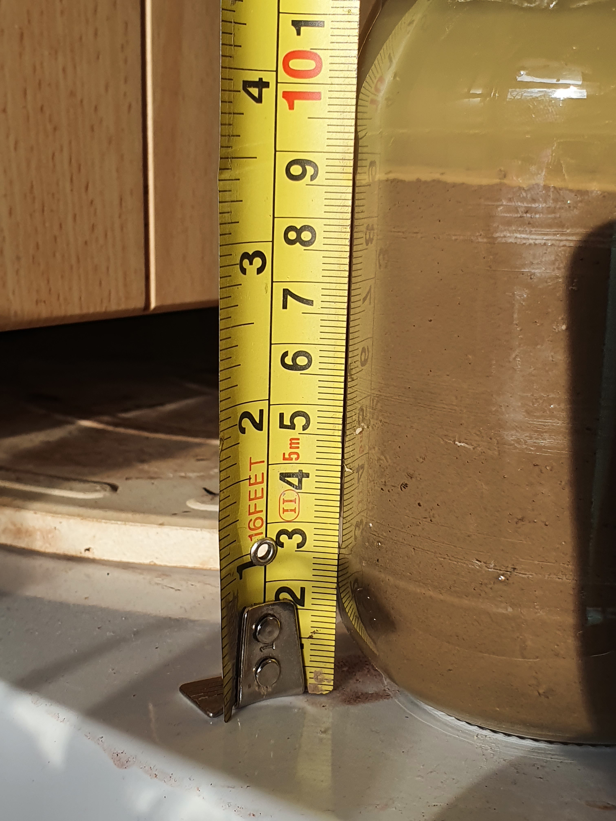
images/202212/20221208_102116.jpg
