ned14/HouseBuild/images/202212/20221210_172432.jpg

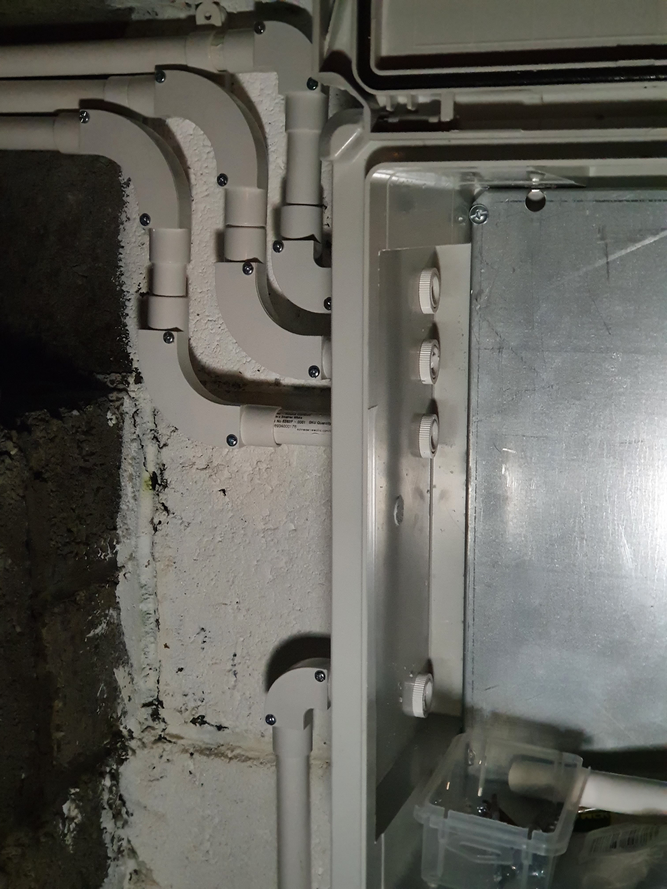
images/202212/20221210_172432.jpg
