ned14/HouseBuild/images/202302/20230202_111918.jpg

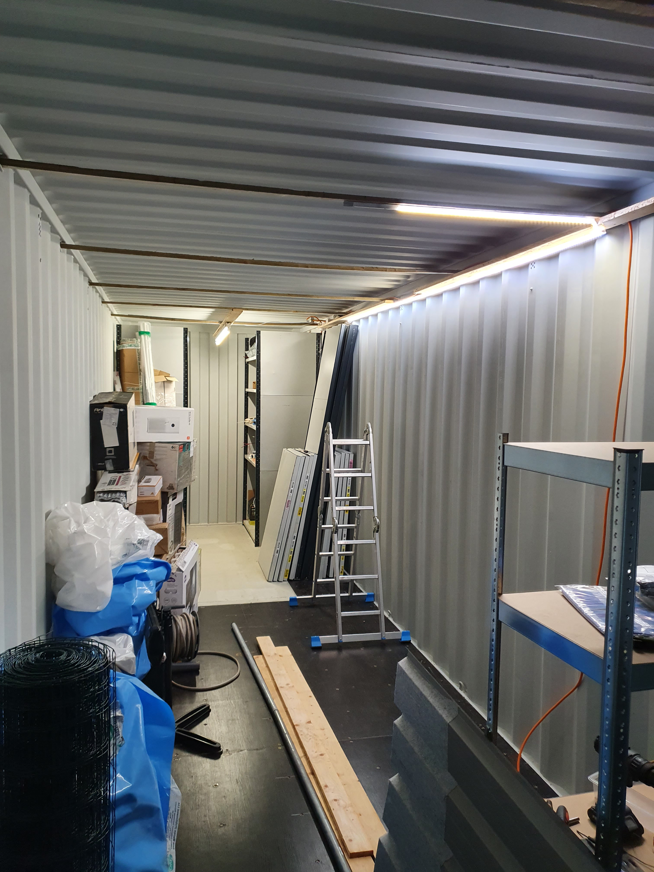
images/202302/20230202_111918.jpg
