ned14/HouseBuild/images/202302/20230220_171055.jpg

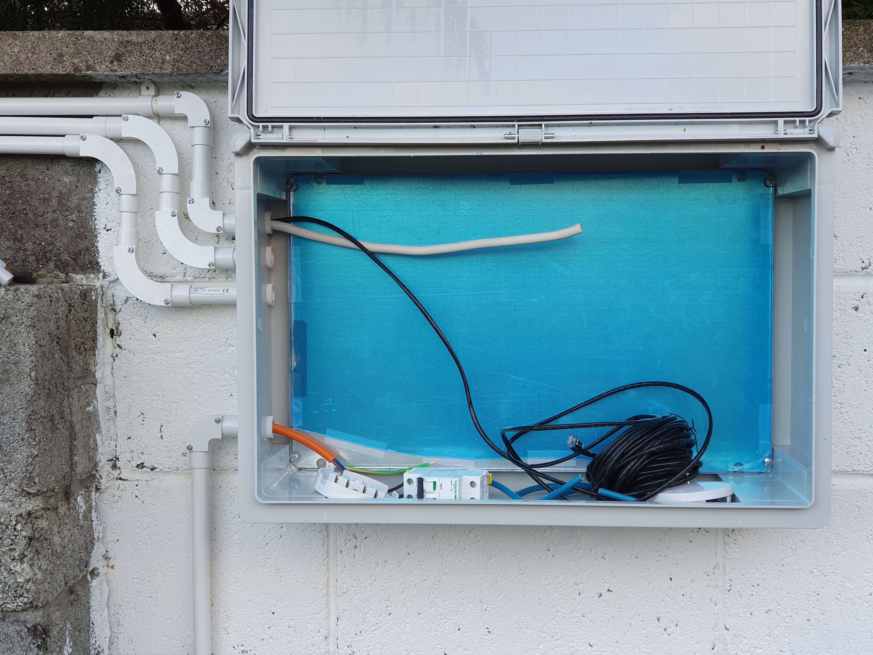
images/202302/20230220_171055.jpg
