ned14/HouseBuild/images/202302/20230224_111422.jpg

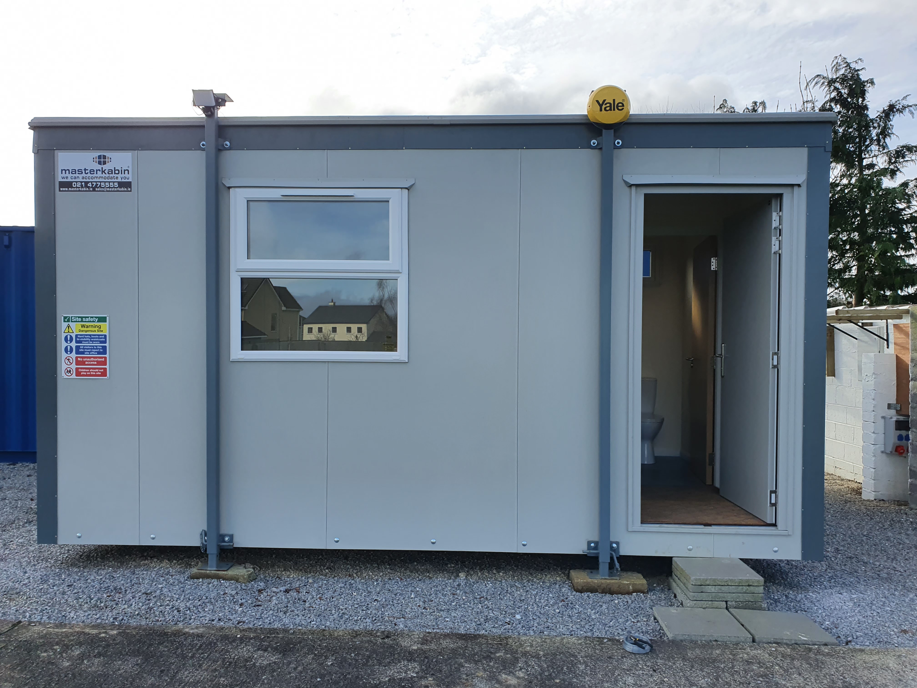
images/202302/20230224_111422.jpg
