ned14/HouseBuild/images/202303/20230301_123719.jpg

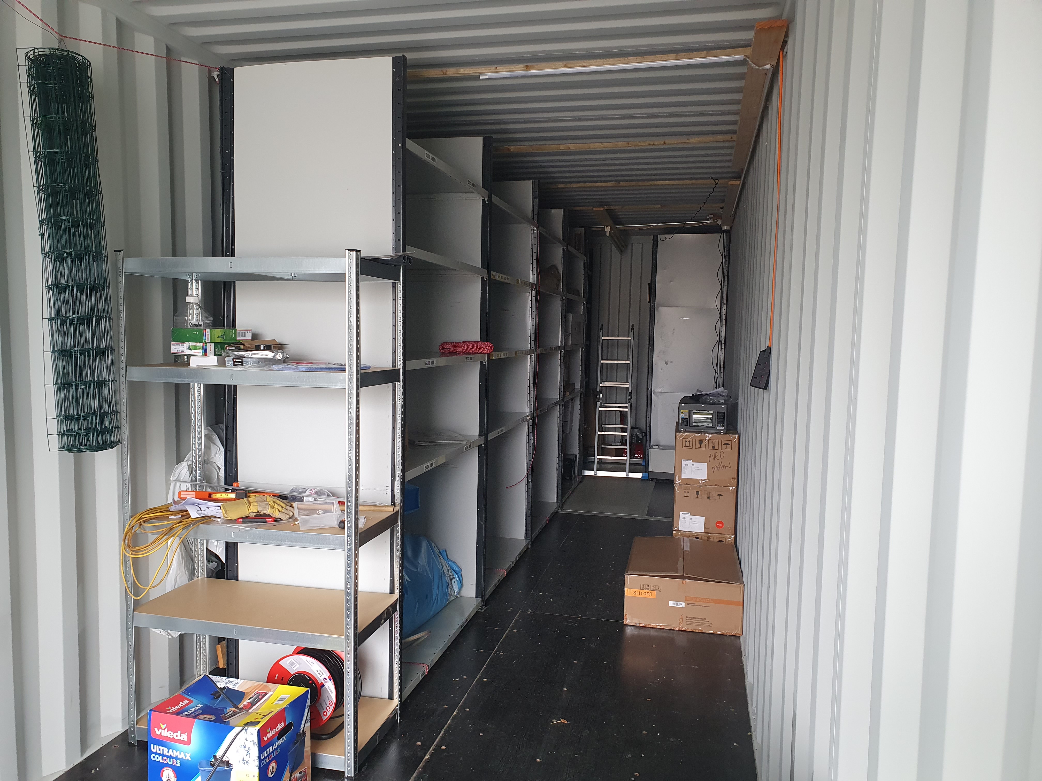
images/202303/20230301_123719.jpg
