ned14/HouseBuild/images/202304/20230415_144313.jpg

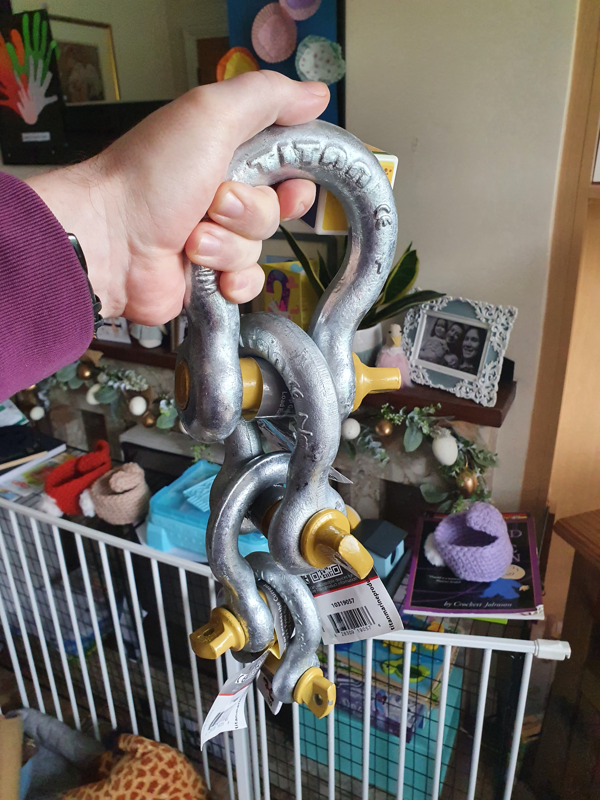
images/202304/20230415_144313.jpg
