ned14/HouseBuild/images/202304/20230430_212558.jpg

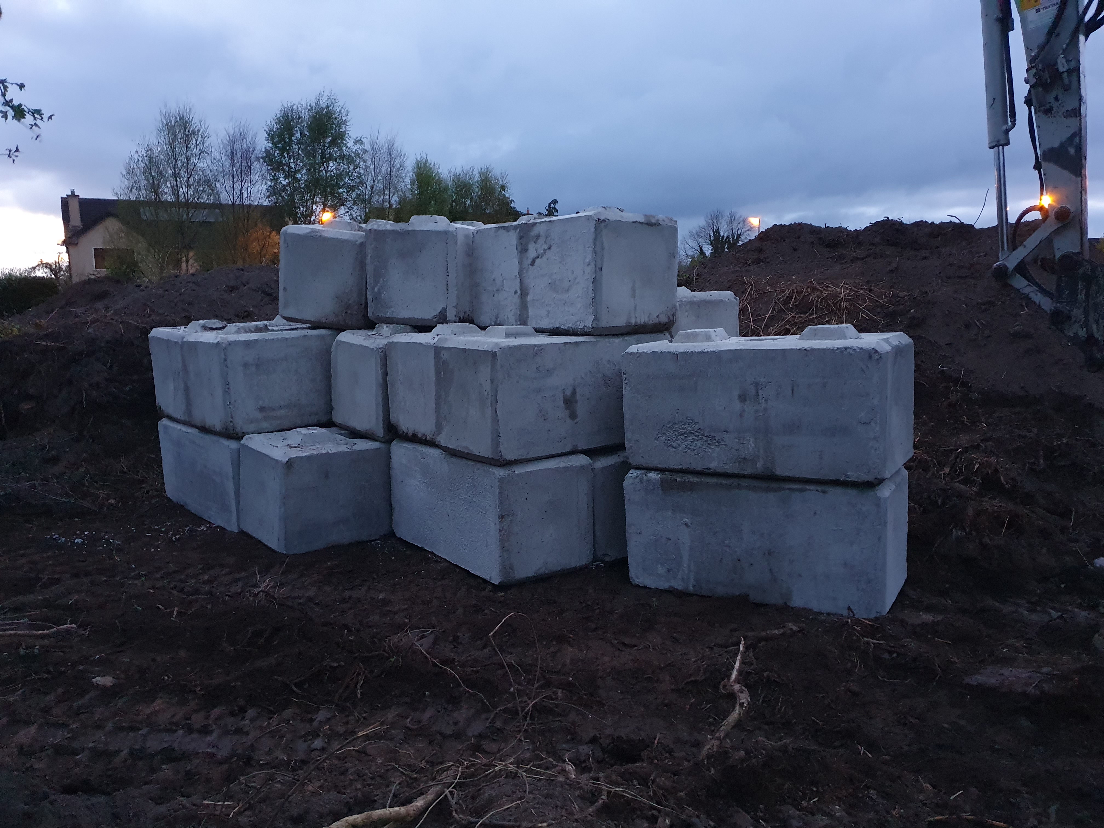
images/202304/20230430_212558.jpg
