ned14/HouseBuild/images/202305/20230504_075740.jpg

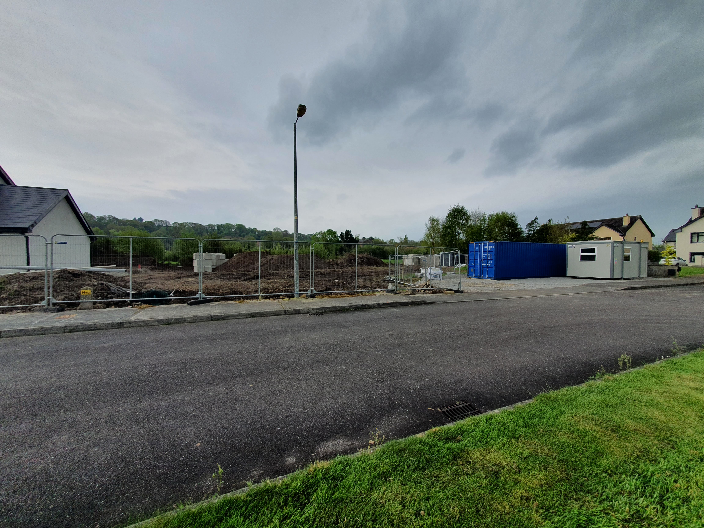
images/202305/20230504_075740.jpg
