ned14/HouseBuild/images/202305/20230504_080122.jpg

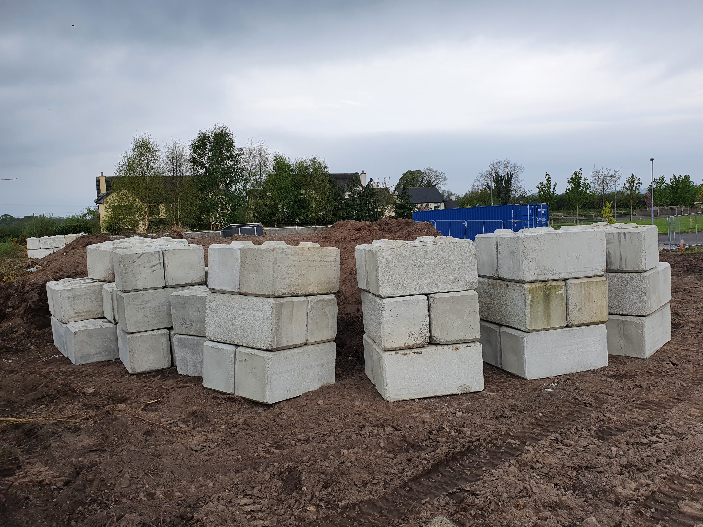
images/202305/20230504_080122.jpg
