ned14/HouseBuild/images/202305/20230504_080417.jpg

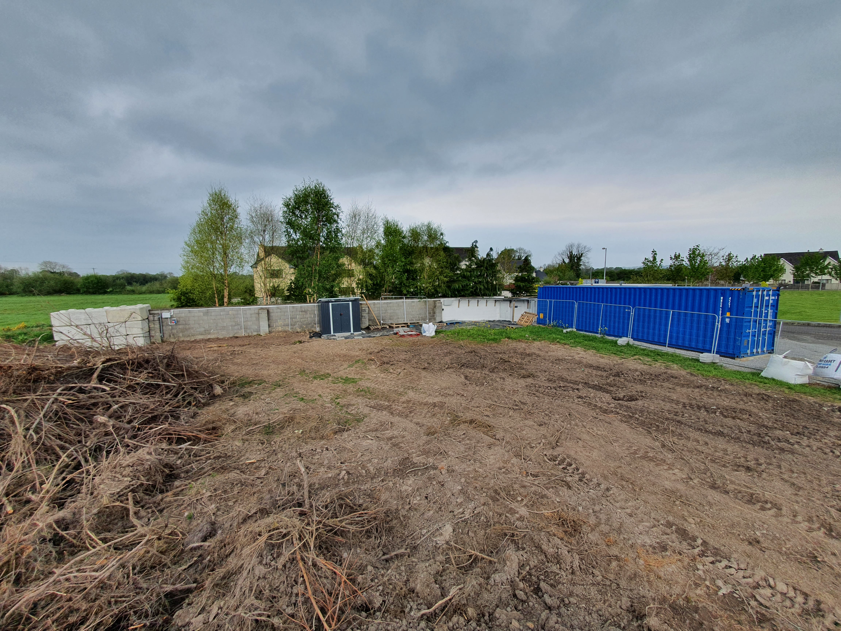
images/202305/20230504_080417.jpg
