ned14/HouseBuild/images/202305/20230504_080820.jpg

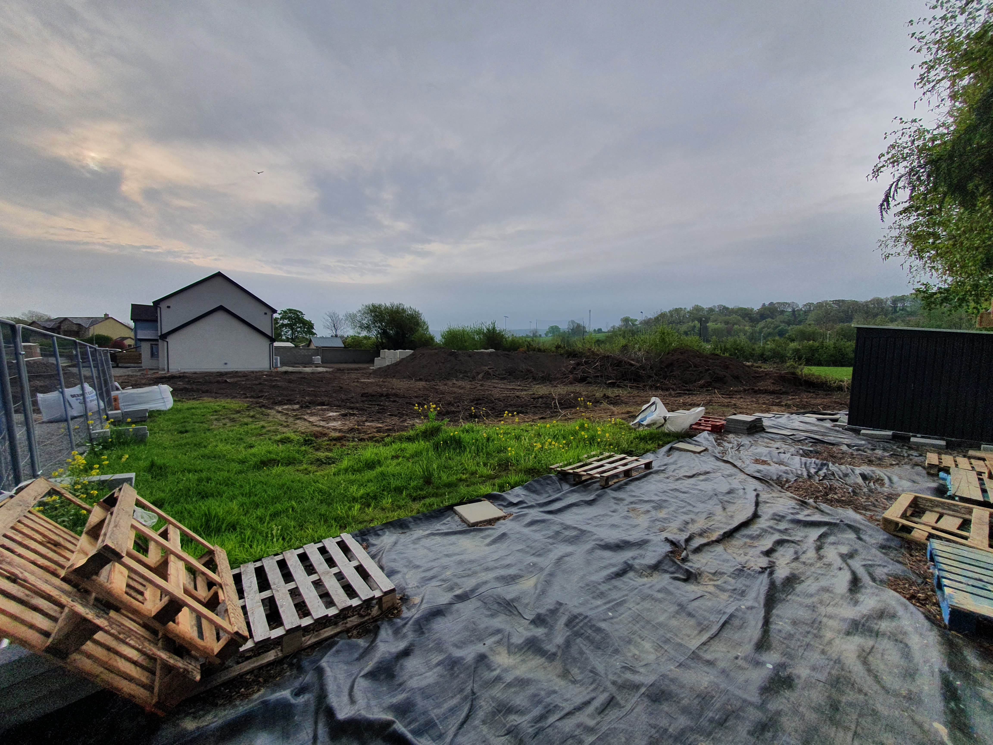
images/202305/20230504_080820.jpg
