ned14/HouseBuild/images/202305/20230504_082318.jpg

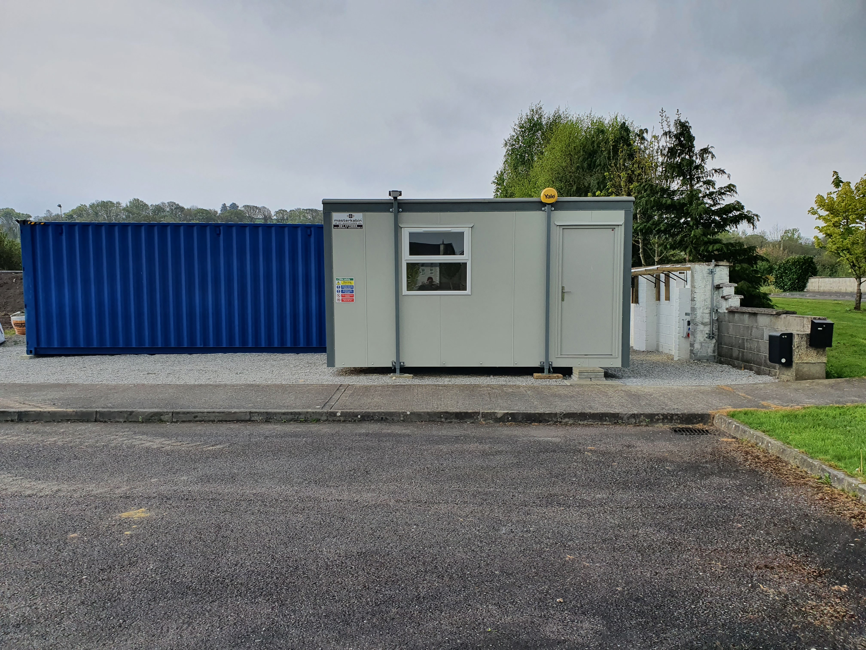
images/202305/20230504_082318.jpg
