ned14/HouseBuild/images/202305/20230531_124432.jpg

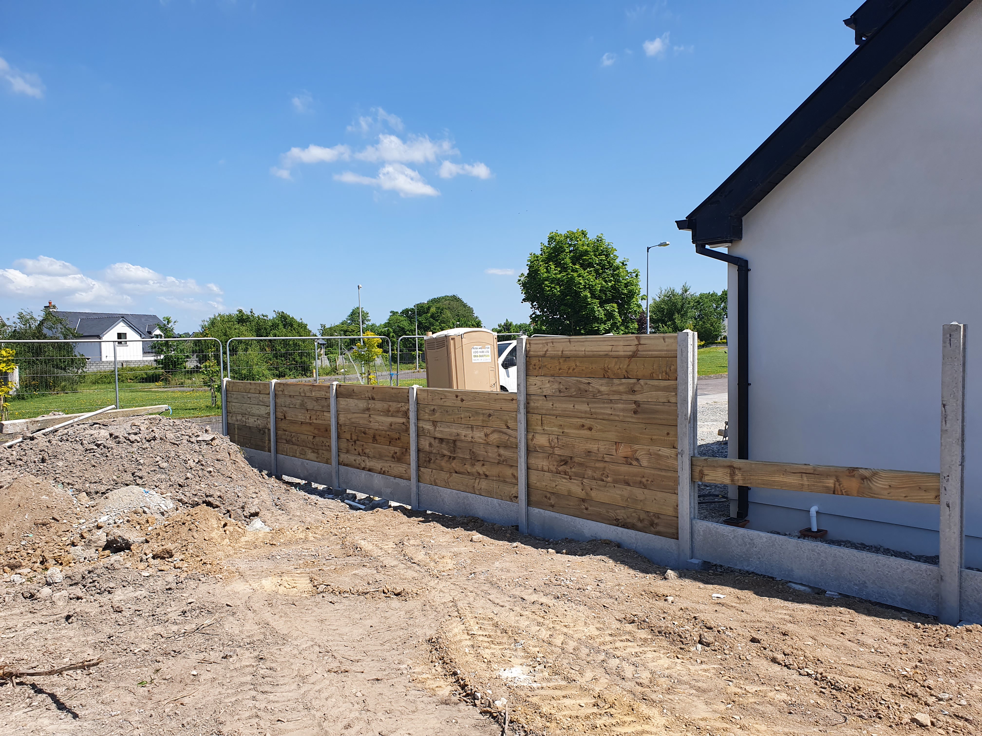
images/202305/20230531_124432.jpg
