ned14/HouseBuild/images/202306/20230604_201457.jpg

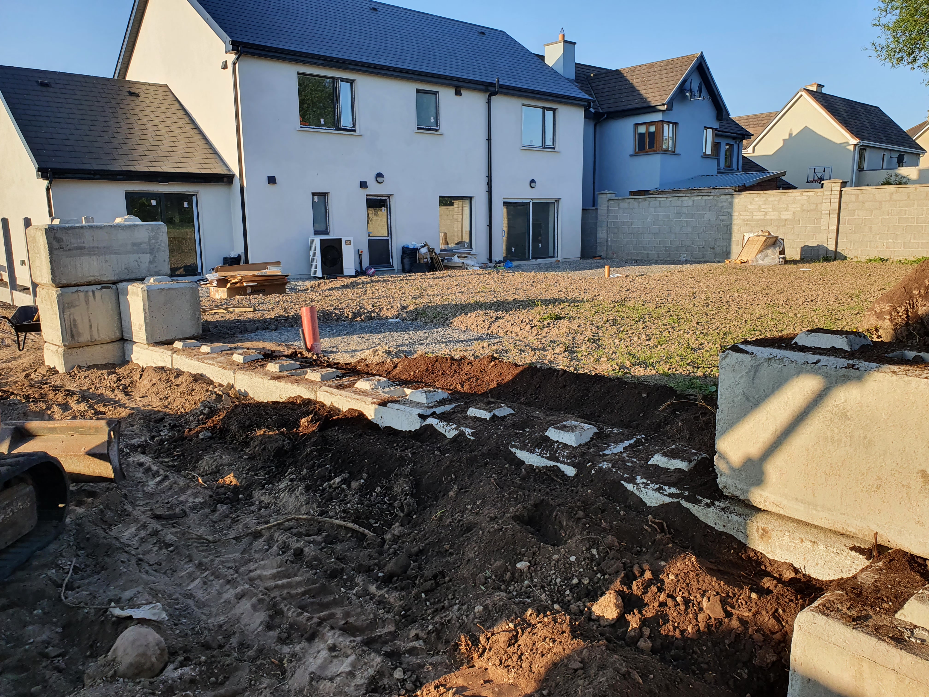
images/202306/20230604_201457.jpg
