ned14/HouseBuild/images/202306/20230605_171815.jpg

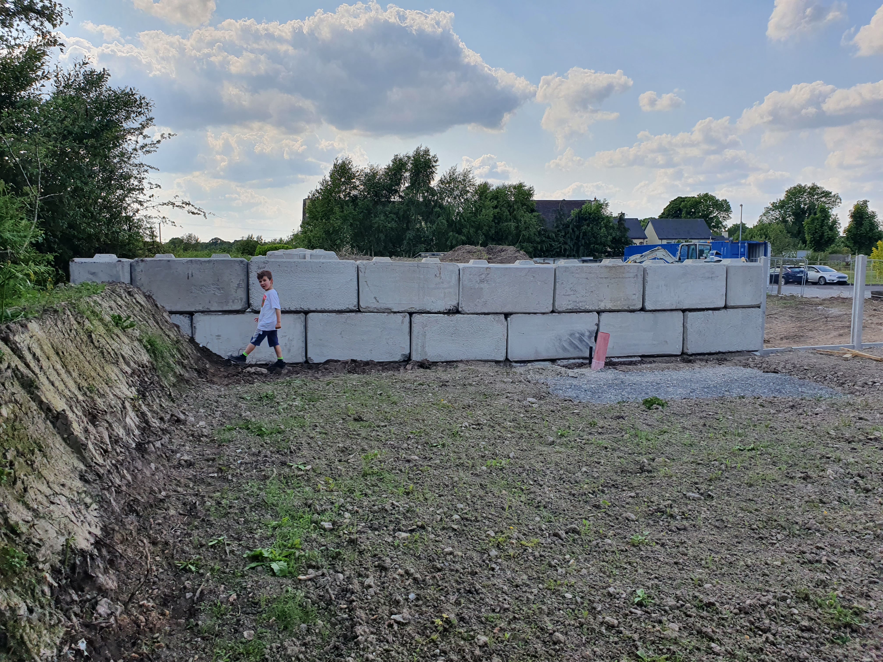
images/202306/20230605_171815.jpg
