ned14/HouseBuild/images/202307/20230716_192511.jpg

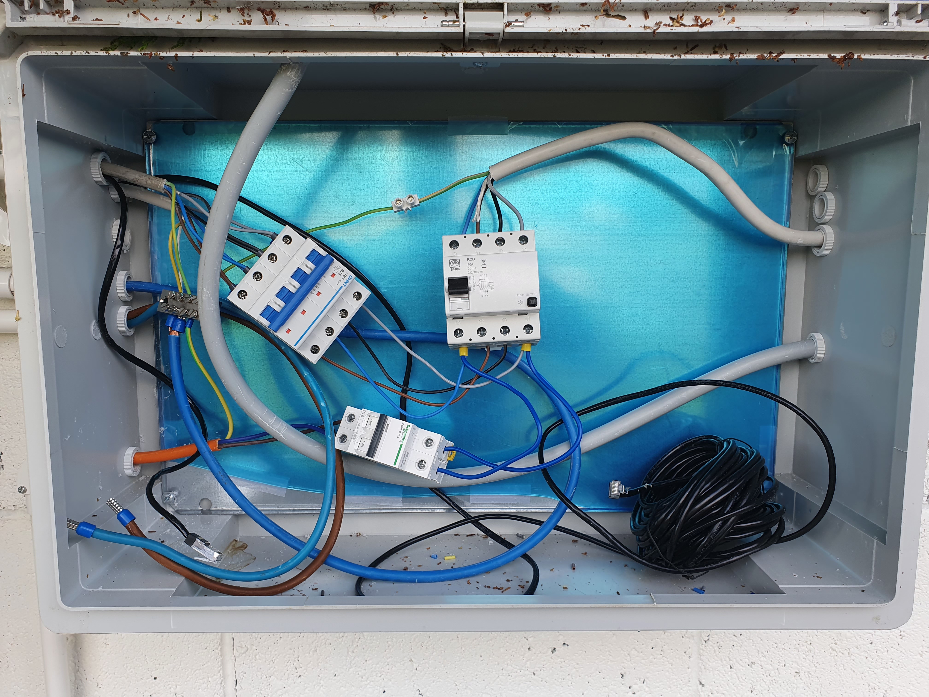
images/202307/20230716_192511.jpg
