ned14/HouseBuild/images/202307/20230716_193727.jpg

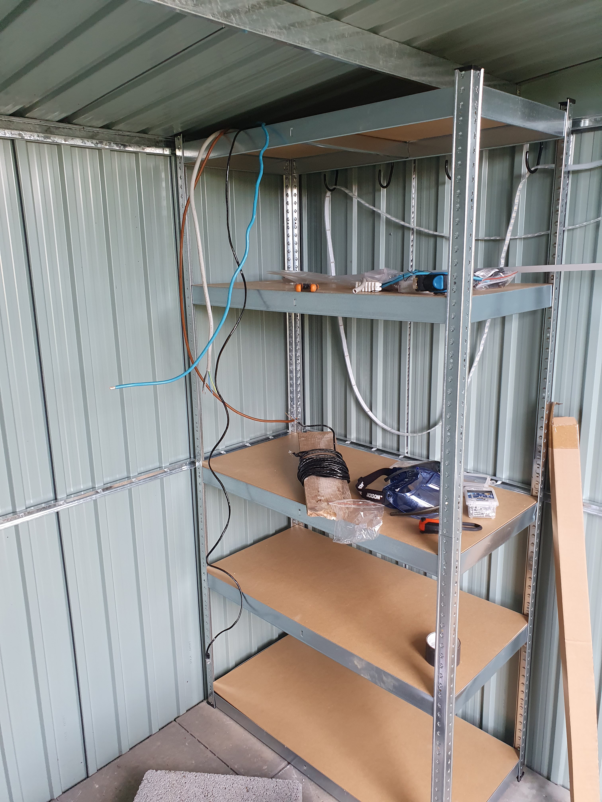
images/202307/20230716_193727.jpg
