ned14/HouseBuild/images/202307/20230730_160750.jpg

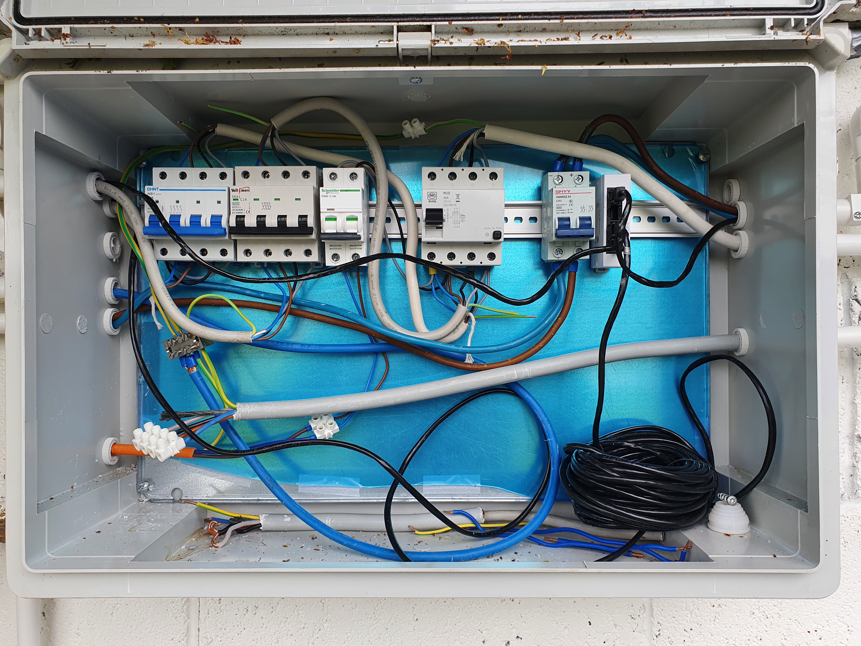
images/202307/20230730_160750.jpg
