ned14/HouseBuild/images/202308/20230805_200303.jpg

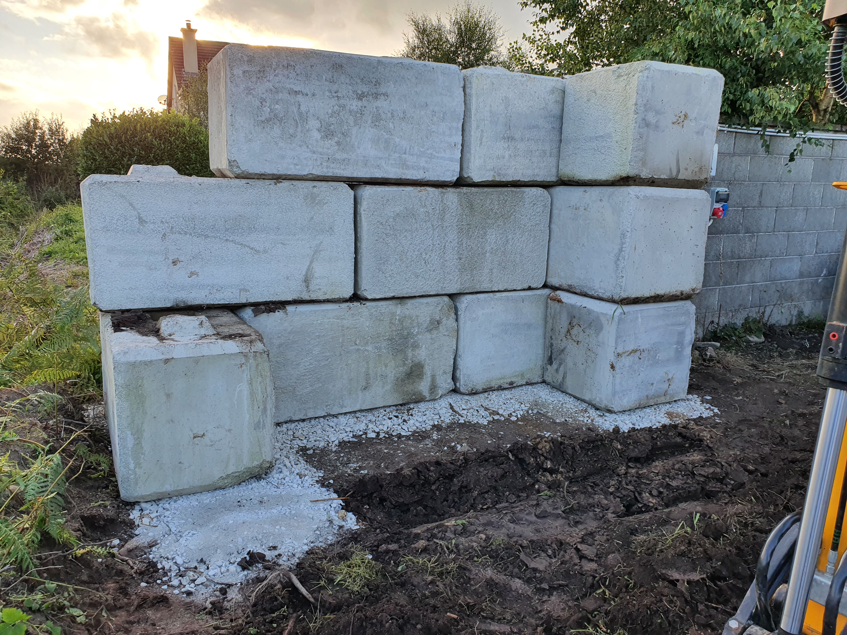
images/202308/20230805_200303.jpg
