ned14/HouseBuild/images/202308/20230806_180509.jpg

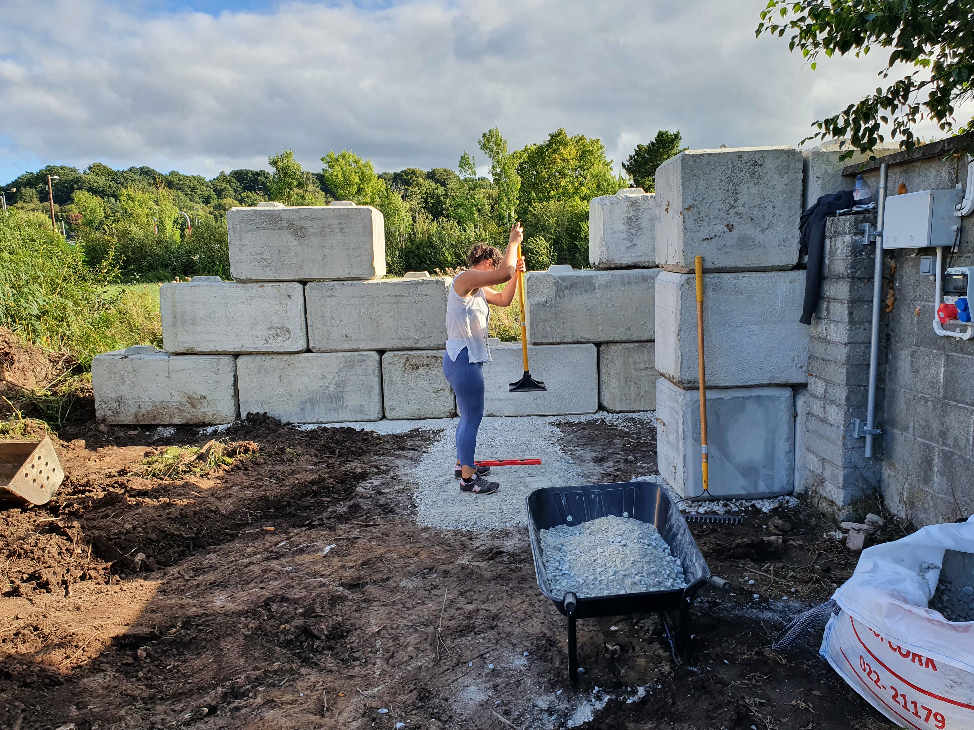
images/202308/20230806_180509.jpg
