ned14/HouseBuild/images/202308/20230808_110750.jpg

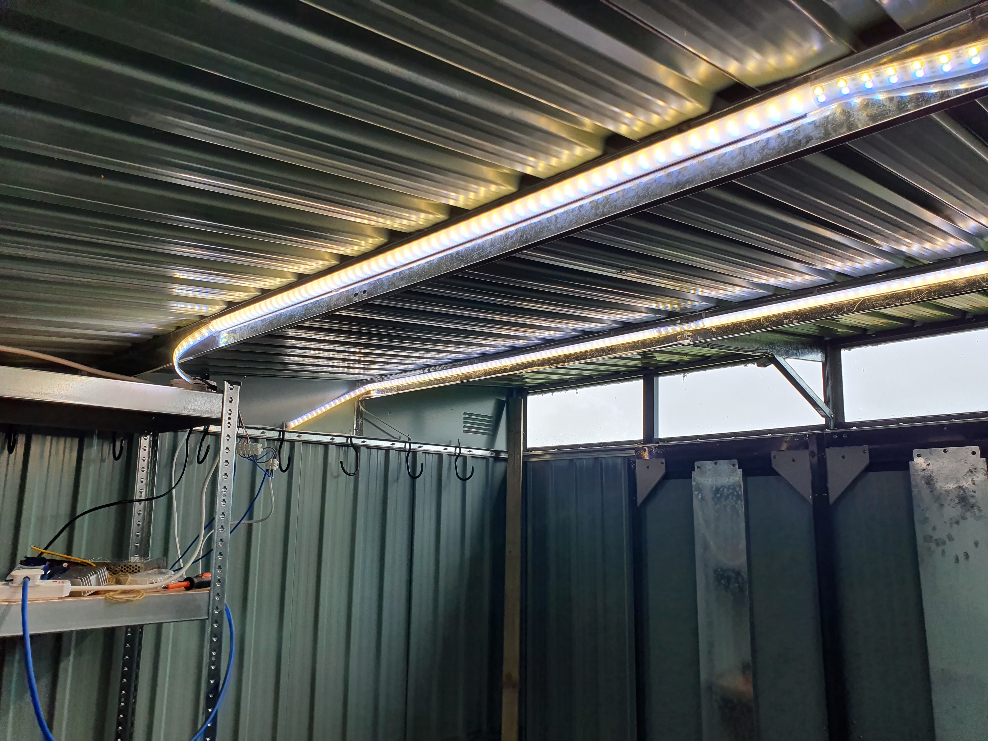
images/202308/20230808_110750.jpg
