ned14/HouseBuild/images/202308/20230809_113628.jpg

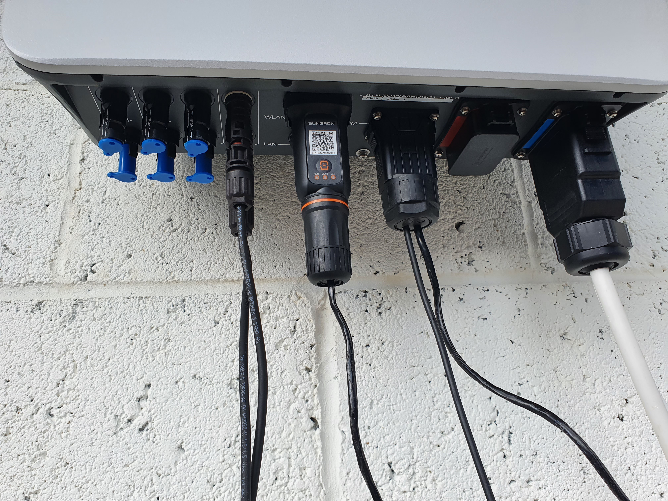
images/202308/20230809_113628.jpg
