ned14/HouseBuild/images/202308/20230815_120303.jpg

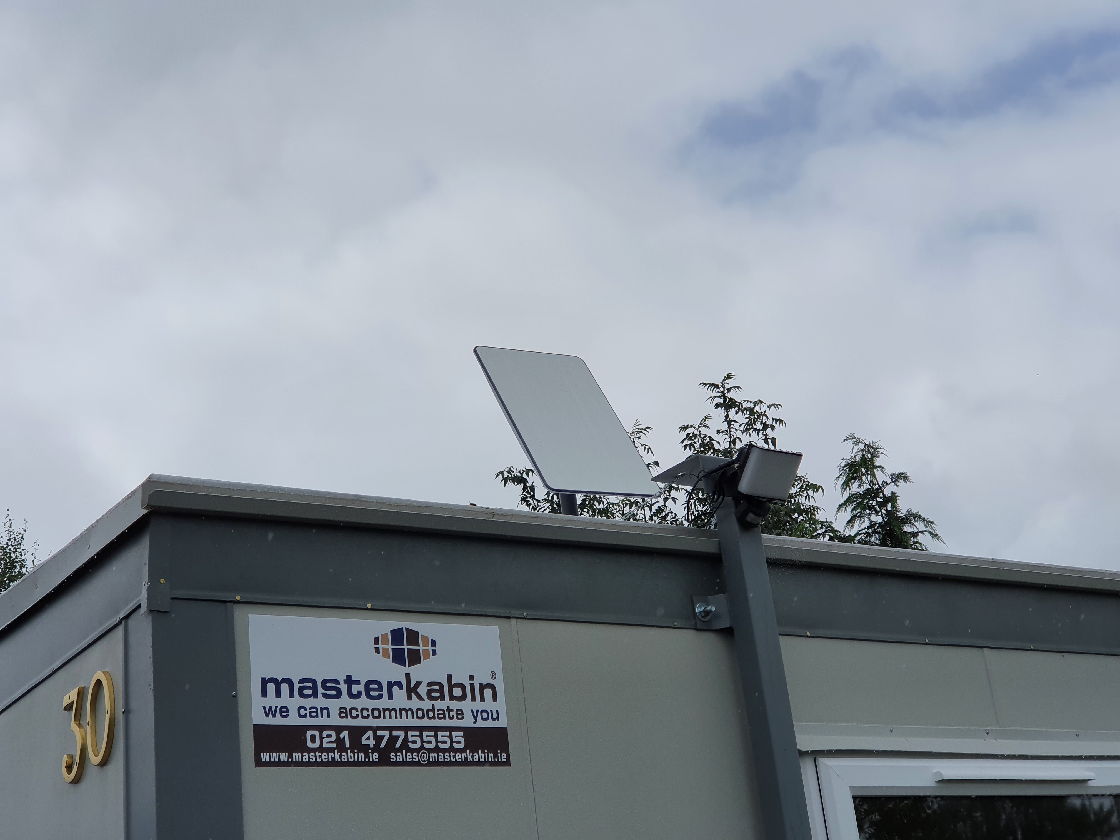
images/202308/20230815_120303.jpg
