ned14/HouseBuild/images/202308/20230819_191747.jpg

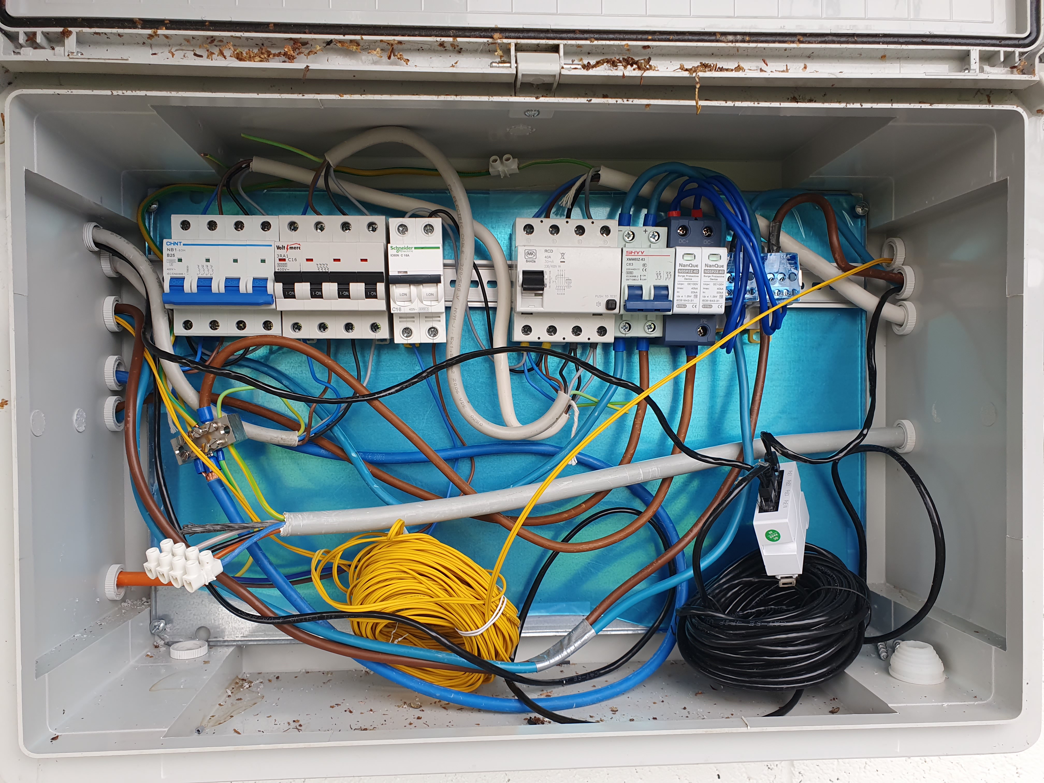
images/202308/20230819_191747.jpg
