ned14/HouseBuild/images/202308/20230826_131255.jpg

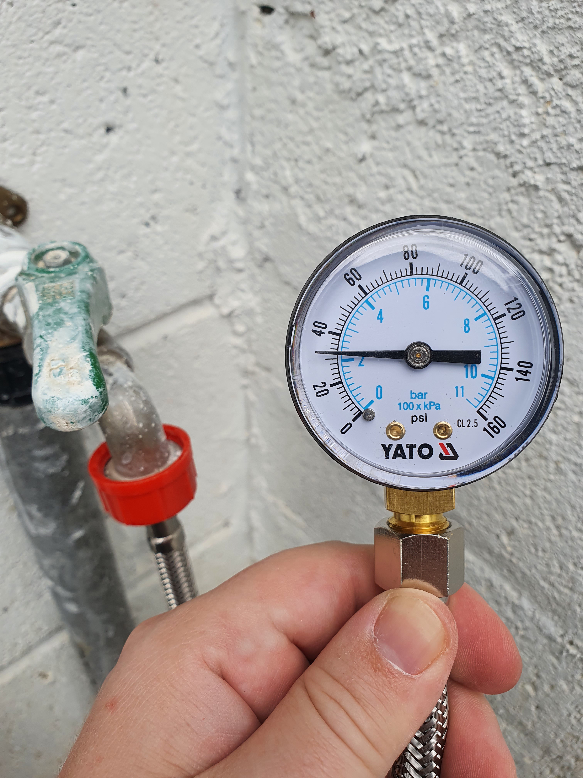
images/202308/20230826_131255.jpg
