ned14/HouseBuild/images/202308/20230826_173330.jpg

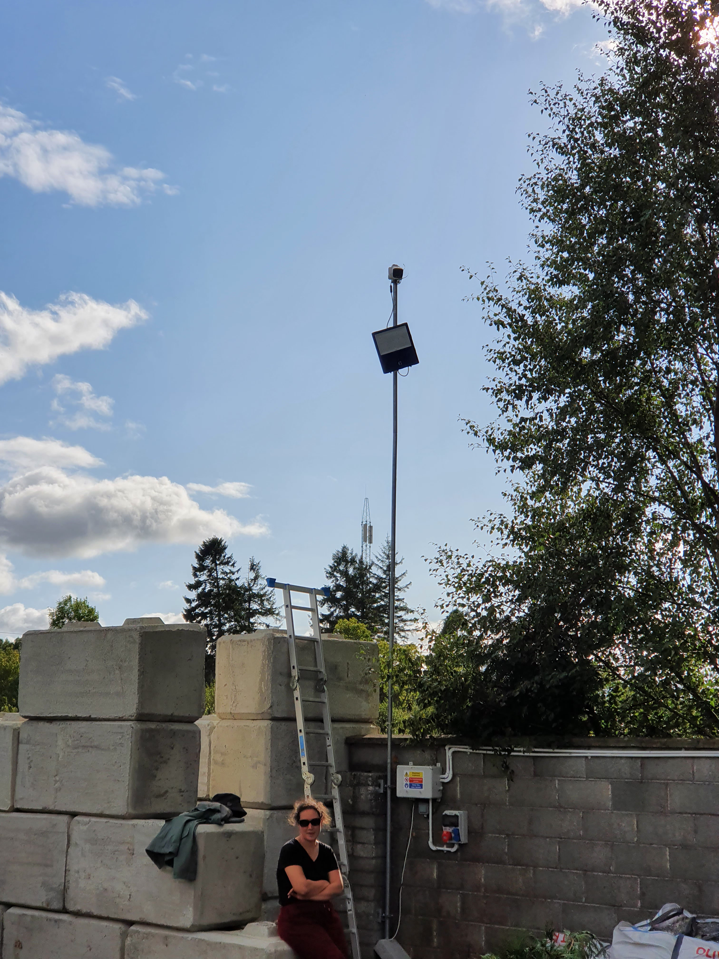
images/202308/20230826_173330.jpg
