ned14/HouseBuild/images/202308/20230826_173940.jpg

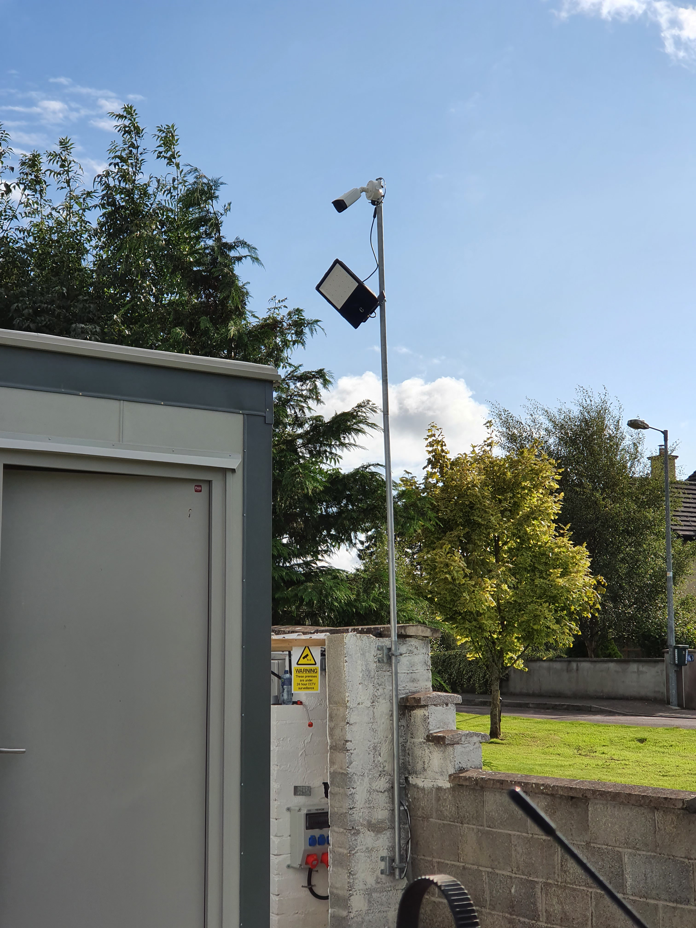
images/202308/20230826_173940.jpg
