ned14/HouseBuild/images/202308/20230827_150827.jpg

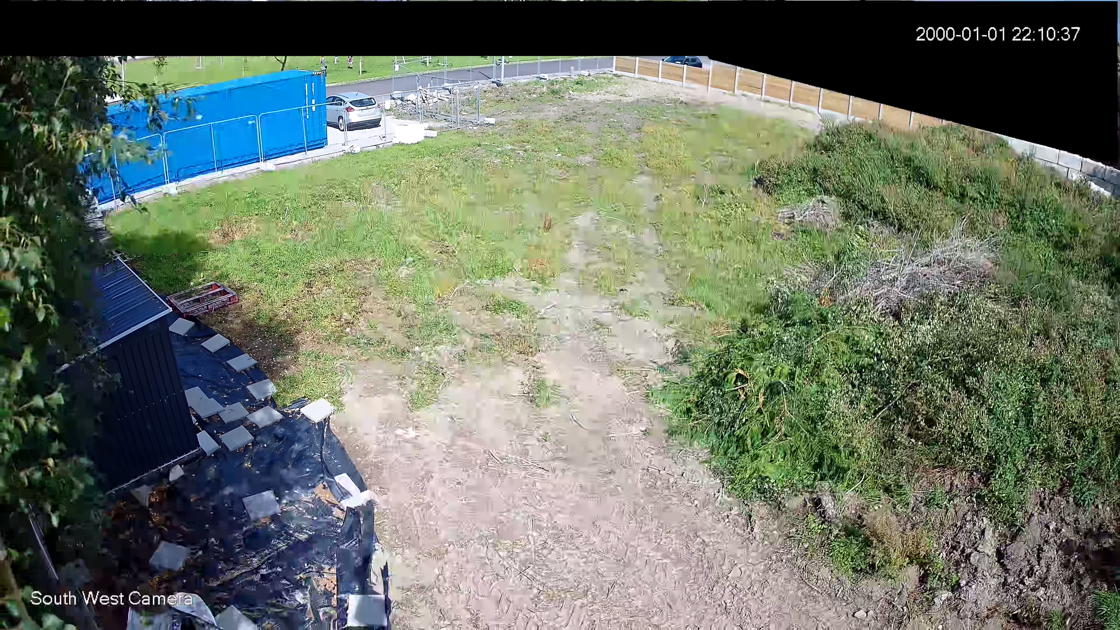
images/202308/20230827_150827.jpg
