ned14/HouseBuild/images/202308/20230827_155122.jpg

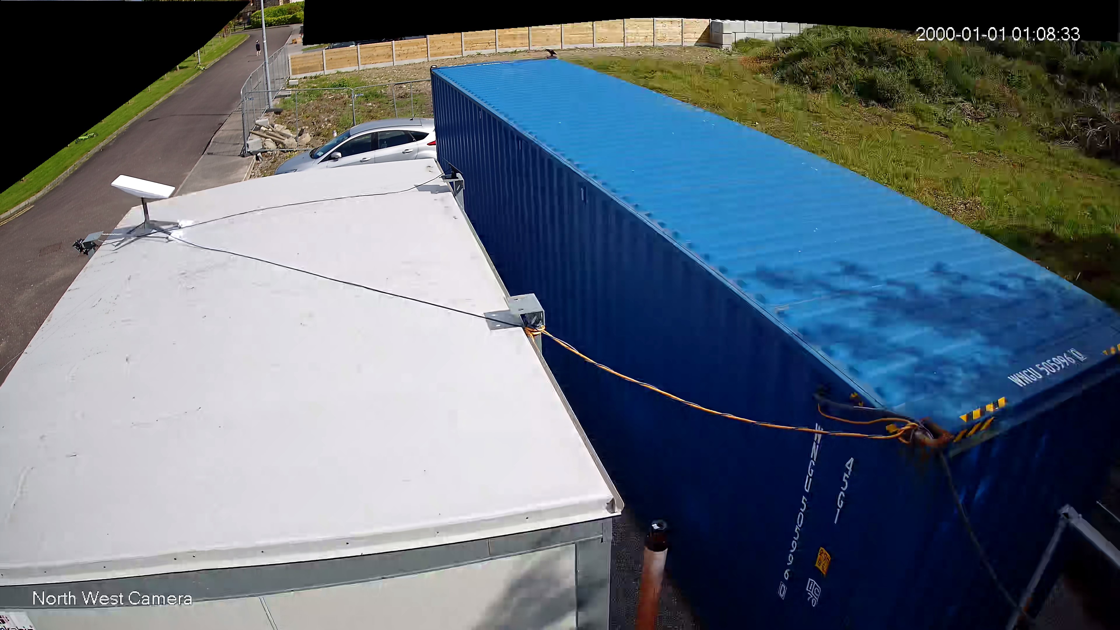
images/202308/20230827_155122.jpg
