ned14/HouseBuild/images/202308/IMG-20230805-WA0002.jpeg

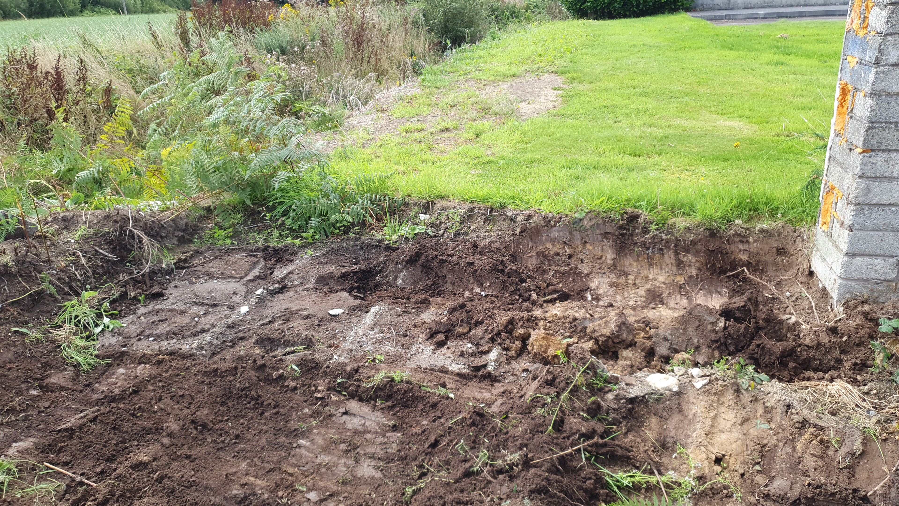
images/202308/IMG-20230805-WA0002.jpeg
