ned14/HouseBuild/images/202308/Screenshot_20230816-081340_Starlink.jpg

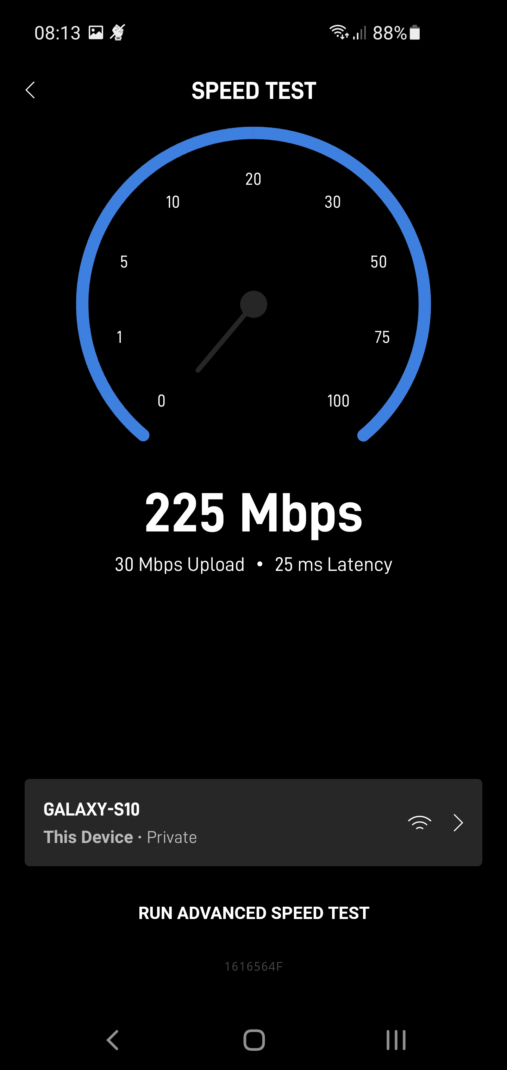
images/202308/Screenshot_20230816-081340_Starlink.jpg
