ned14/HouseBuild/images/202309/20230901_092515.jpg

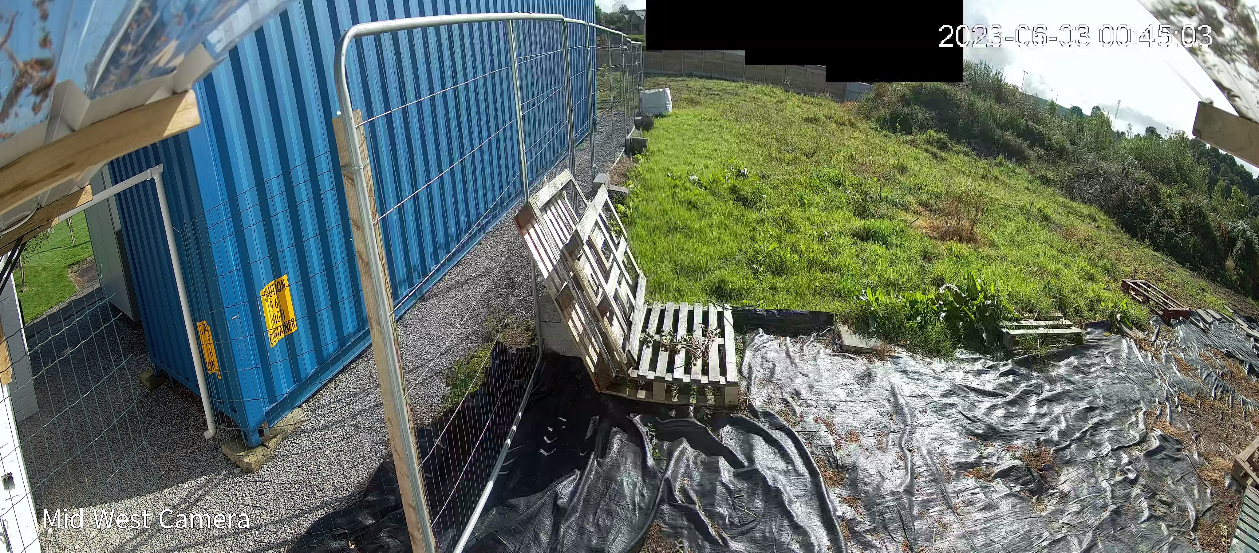
images/202309/20230901_092515.jpg
