ned14/HouseBuild/images/202309/20230906_110806.jpg

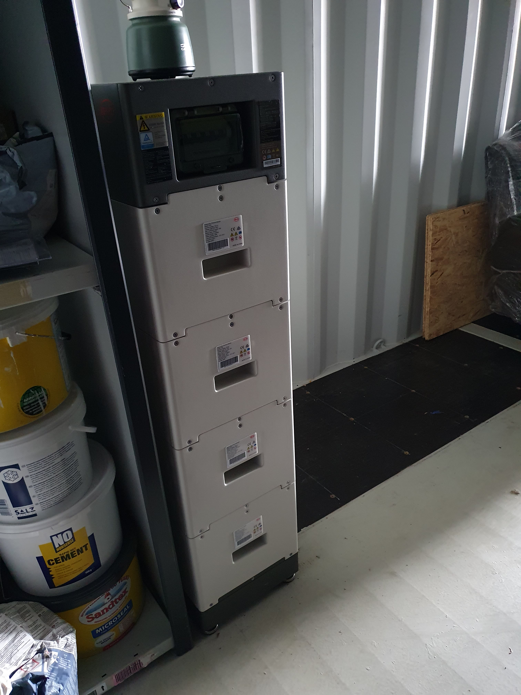
images/202309/20230906_110806.jpg
