ned14/HouseBuild/images/202309/20230910_144644.jpg

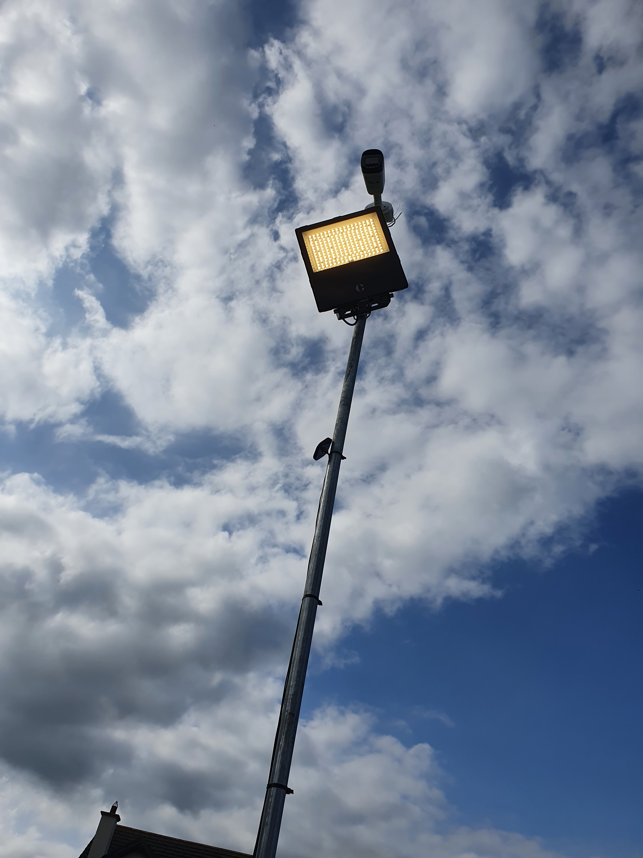
images/202309/20230910_144644.jpg
