ned14/HouseBuild/images/202309/20230915_114532.jpg

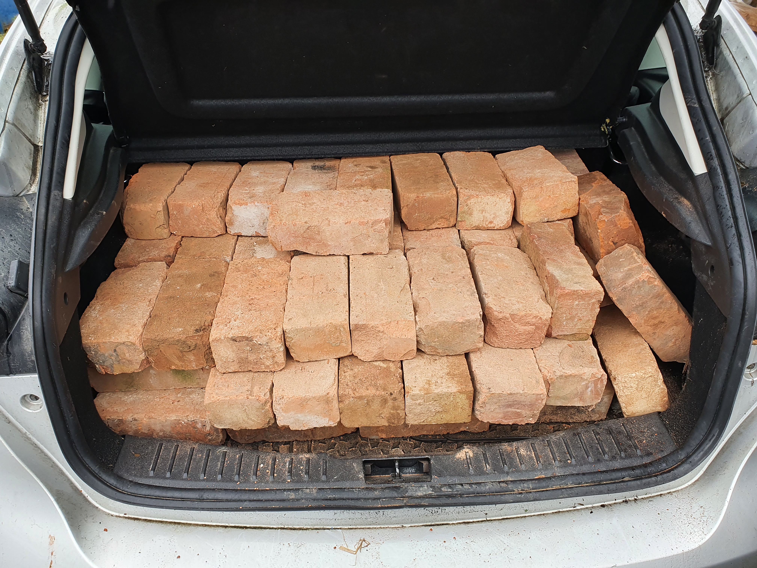
images/202309/20230915_114532.jpg
