ned14/HouseBuild/images/202309/20230917_184847.jpg

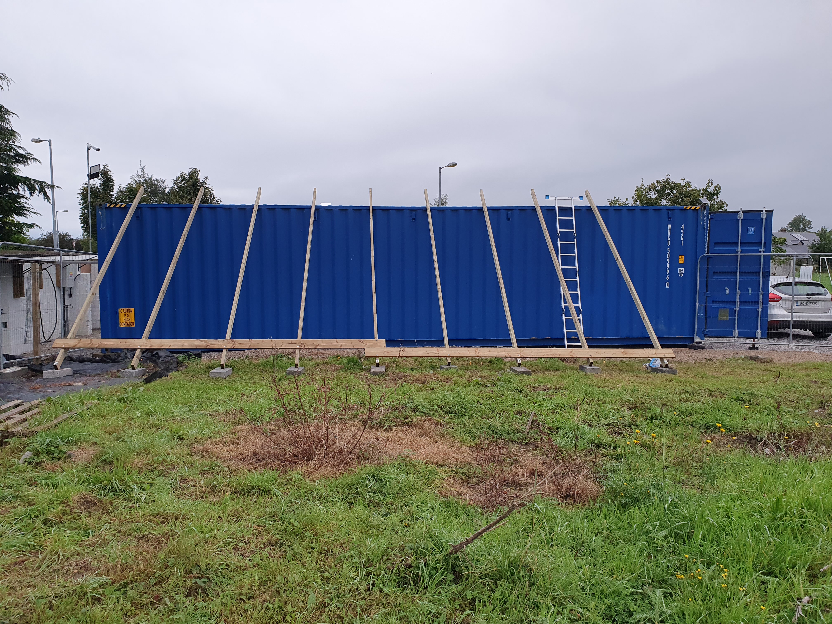
images/202309/20230917_184847.jpg
