ned14/HouseBuild/images/202309/20230918_085516.jpg

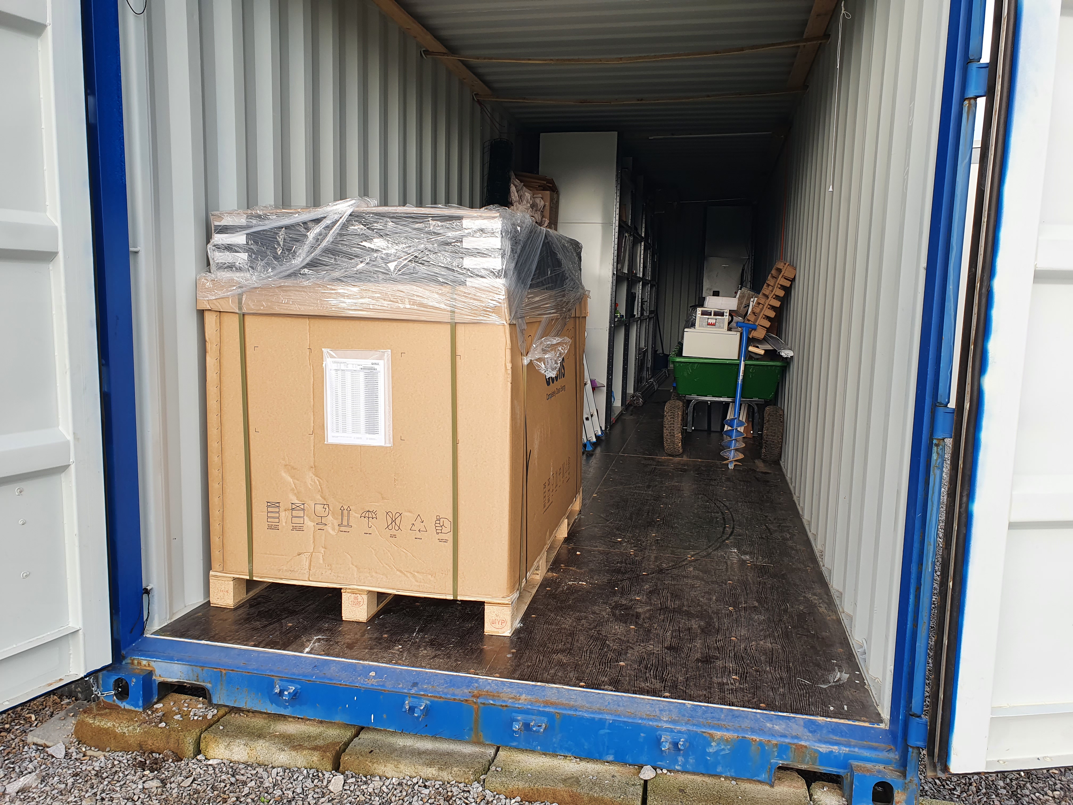
images/202309/20230918_085516.jpg
