ned14/HouseBuild/images/202309/20230922_112049.jpg

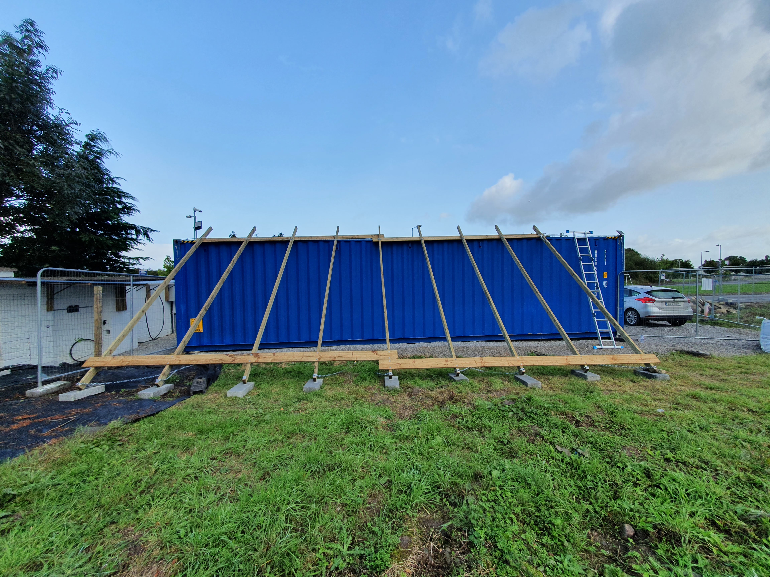
images/202309/20230922_112049.jpg
