ned14/HouseBuild/images/202309/20230922_112138.jpg

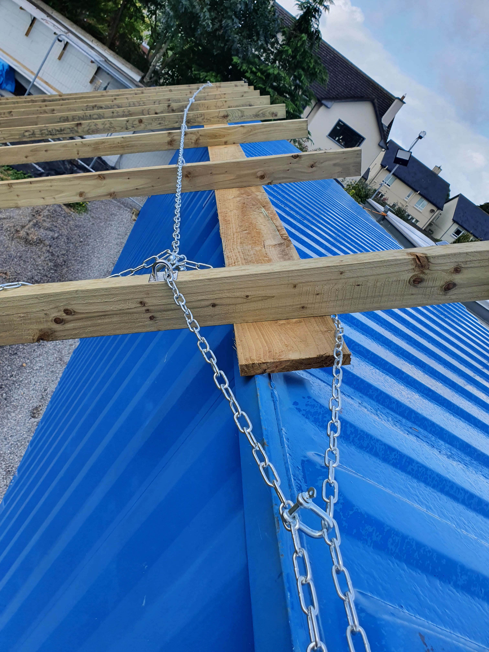
images/202309/20230922_112138.jpg
