ned14/HouseBuild/images/202309/20230922_171319.jpg

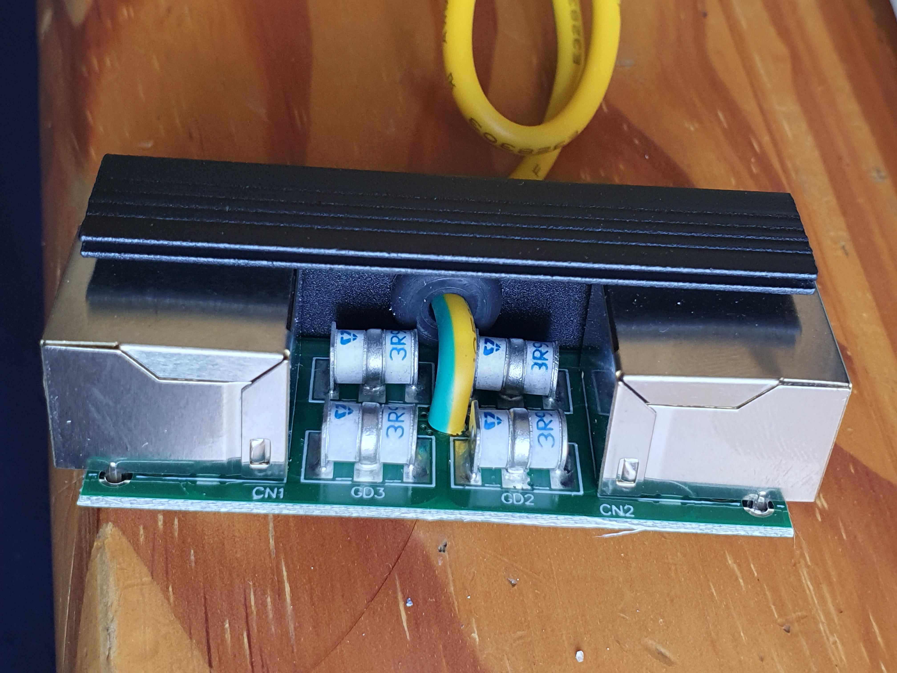
images/202309/20230922_171319.jpg
