ned14/HouseBuild/images/202309/IMG-20230930-WA0001.jpeg

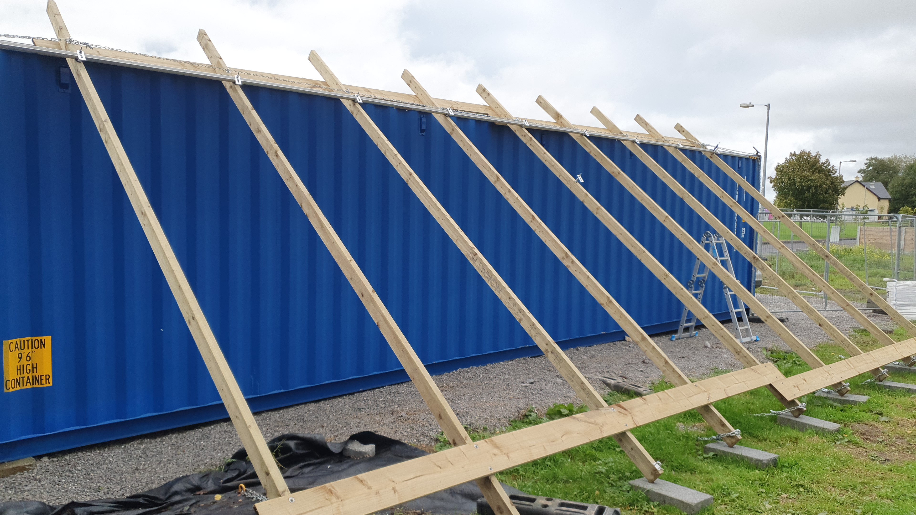
images/202309/IMG-20230930-WA0001.jpeg
