ned14/HouseBuild/images/202310/20231001_183956.jpg

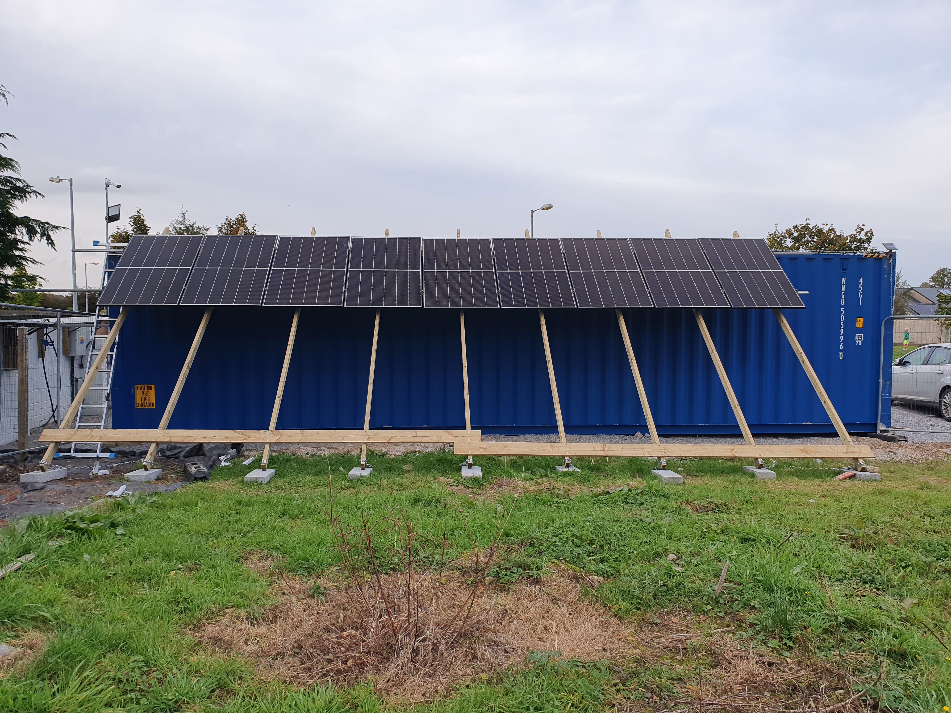
images/202310/20231001_183956.jpg
