ned14/HouseBuild/images/202310/20231007_190923.jpg

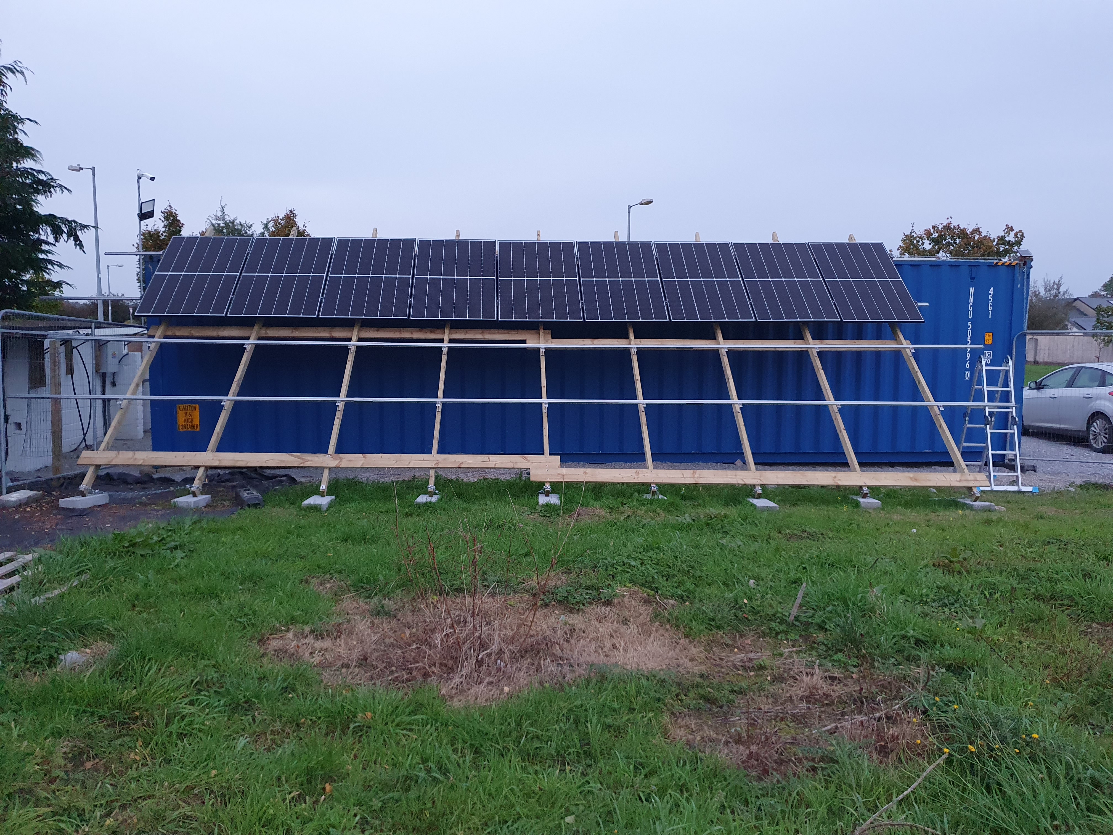
images/202310/20231007_190923.jpg
