ned14/HouseBuild/images/202310/20231008_180816.jpg

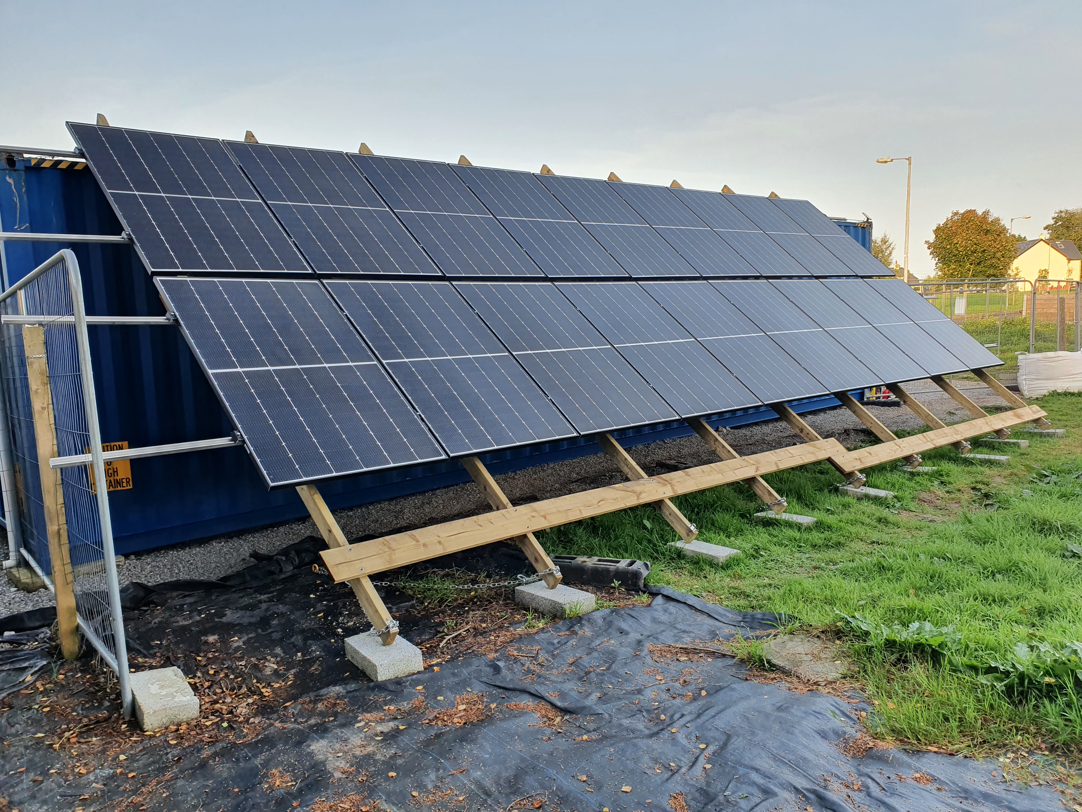
images/202310/20231008_180816.jpg
