ned14/HouseBuild/images/202310/20231008_180836.jpg

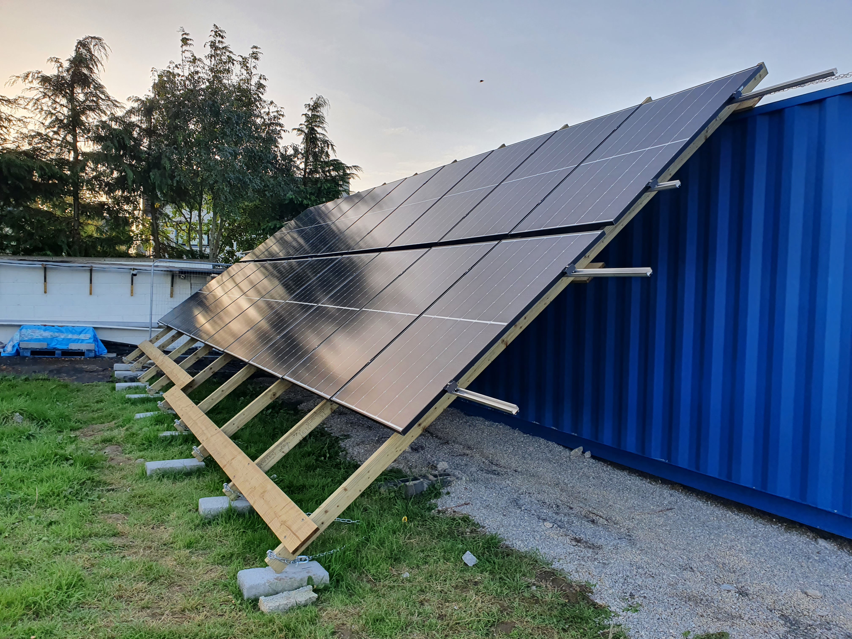
images/202310/20231008_180836.jpg
