ned14/HouseBuild/images/202310/20231014_191945.jpg

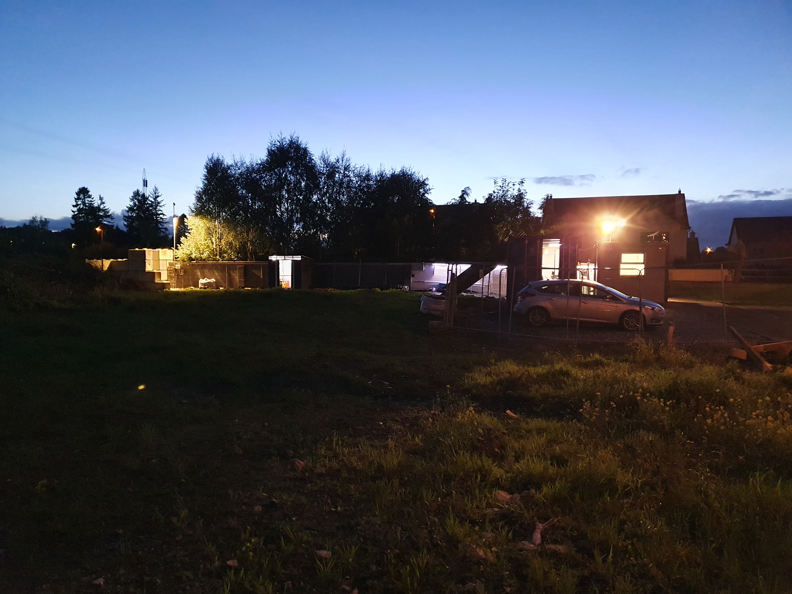
images/202310/20231014_191945.jpg
