ned14/HouseBuild/images/202310/20231024_233303.jpg

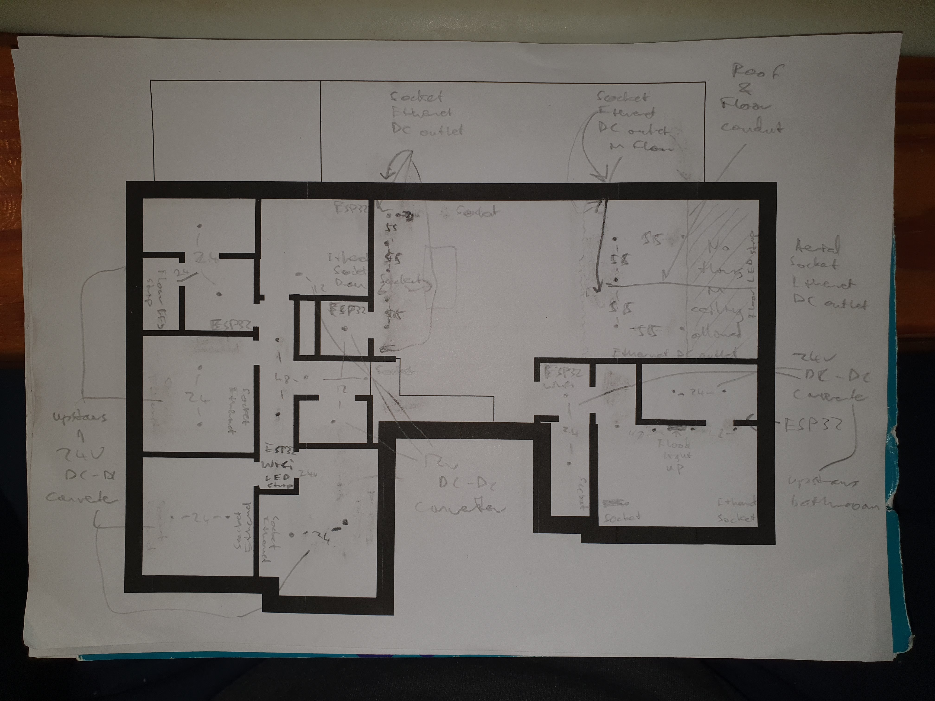
images/202310/20231024_233303.jpg
