ned14/HouseBuild/images/202310/20231024_233327.jpg

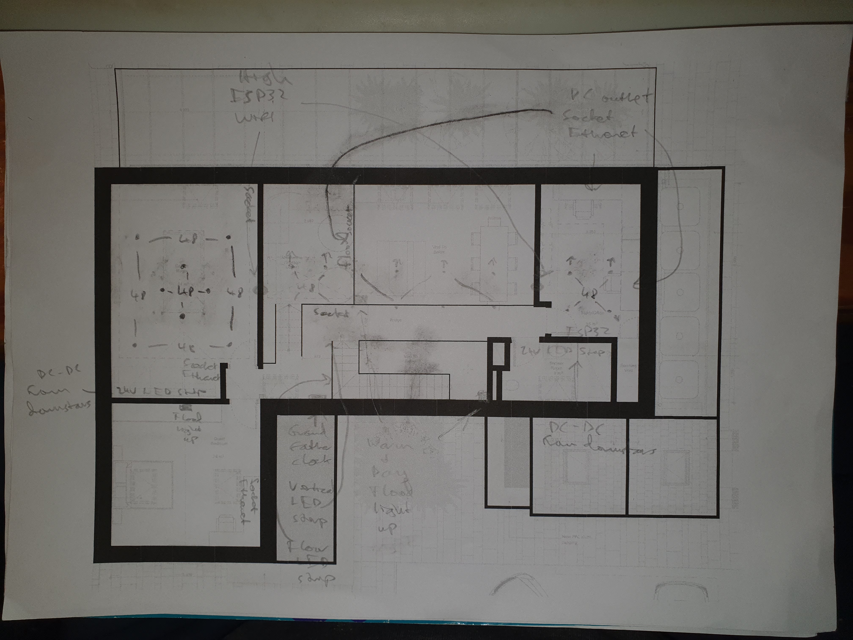
images/202310/20231024_233327.jpg
