ned14/HouseBuild/images/202310/20231030_151954.jpg

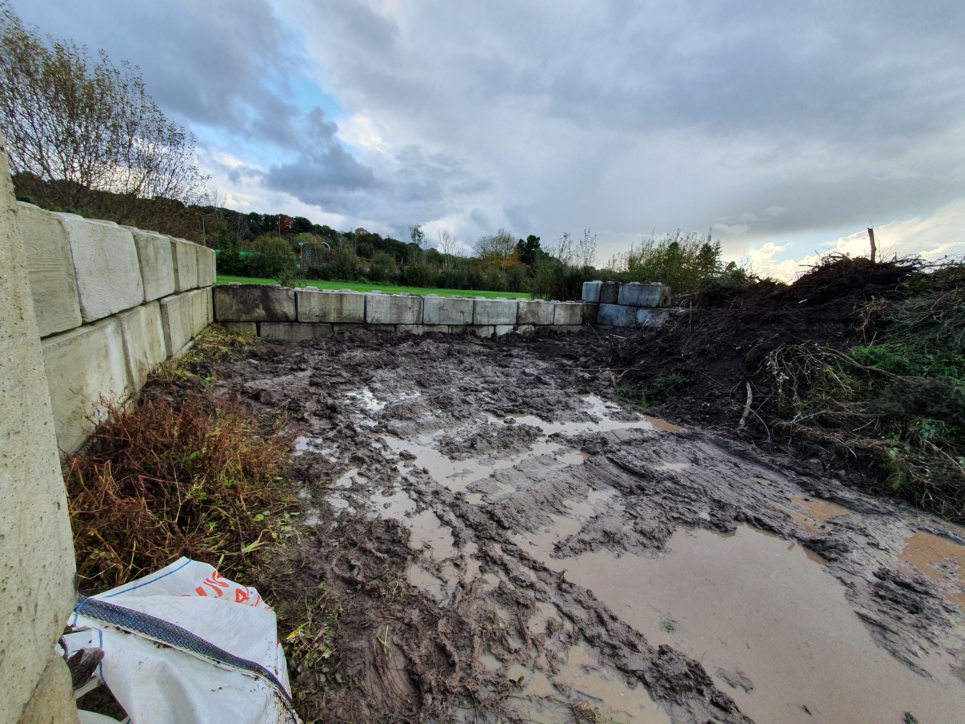
images/202310/20231030_151954.jpg
