ned14/HouseBuild/images/202310/20231030_152235.jpg

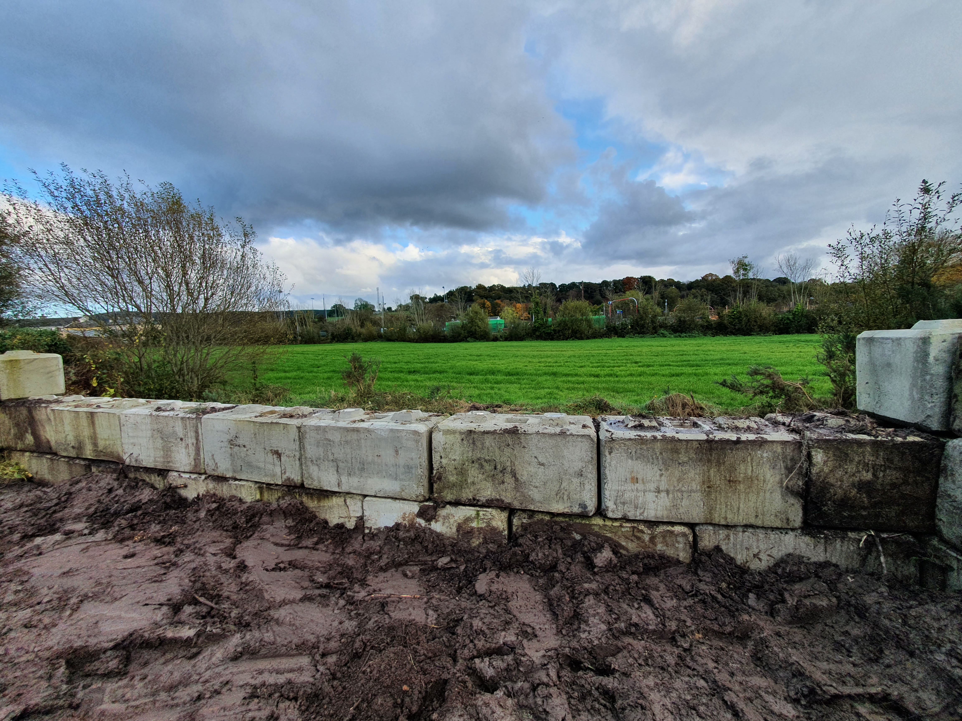
images/202310/20231030_152235.jpg
