ned14/HouseBuild/images/202310/20231031_145912.jpg

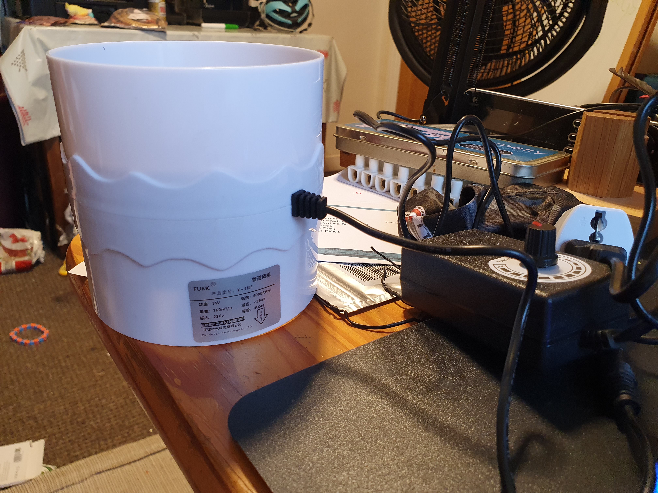
images/202310/20231031_145912.jpg
