ned14/HouseBuild/images/202310/Screenshot_20231013-123707_iSolarCloud.jpg

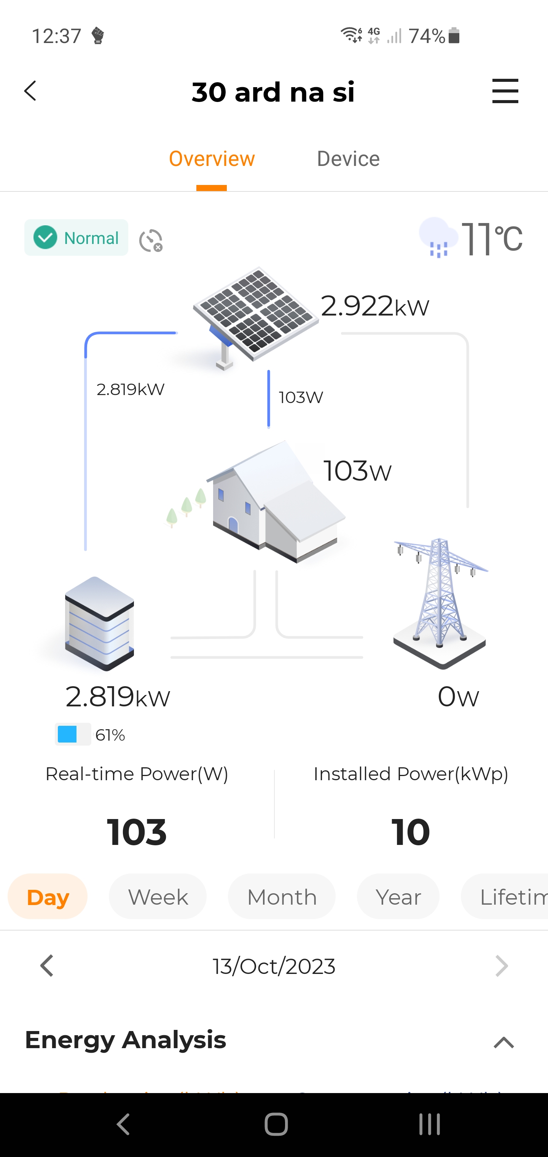
images/202310/Screenshot_20231013-123707_iSolarCloud.jpg
