ned14/HouseBuild/images/202310/Screenshot_20231014-134135_Starlink.jpg

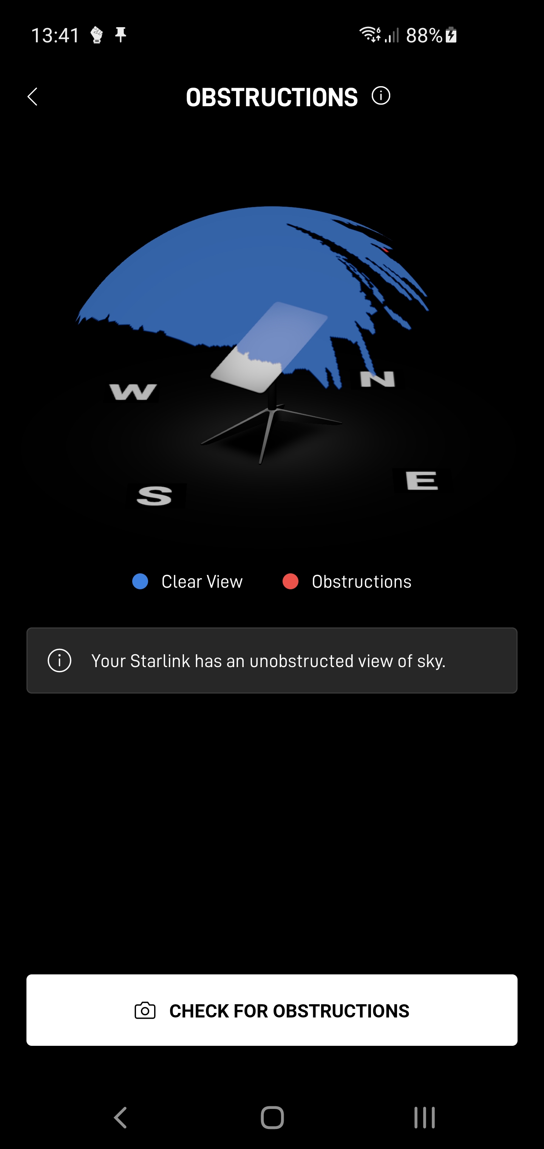
images/202310/Screenshot_20231014-134135_Starlink.jpg
