ned14/HouseBuild/images/202310/Screenshot_20231022-113052_iSolarCloud.jpg

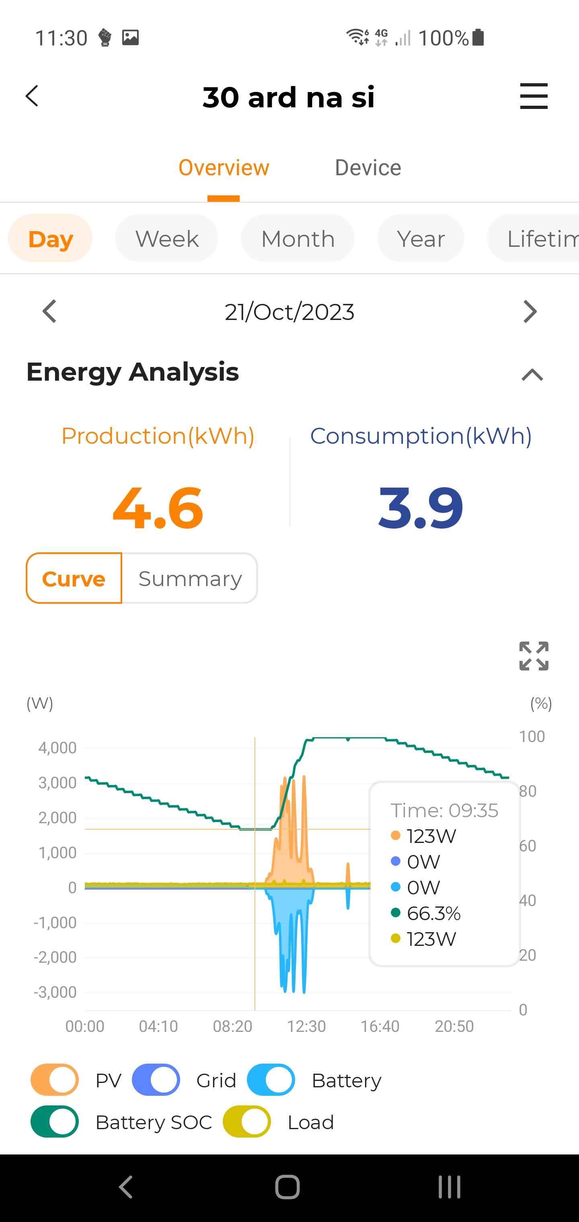
images/202310/Screenshot_20231022-113052_iSolarCloud.jpg
