ned14/HouseBuild/images/202312/20231207_002535.jpg

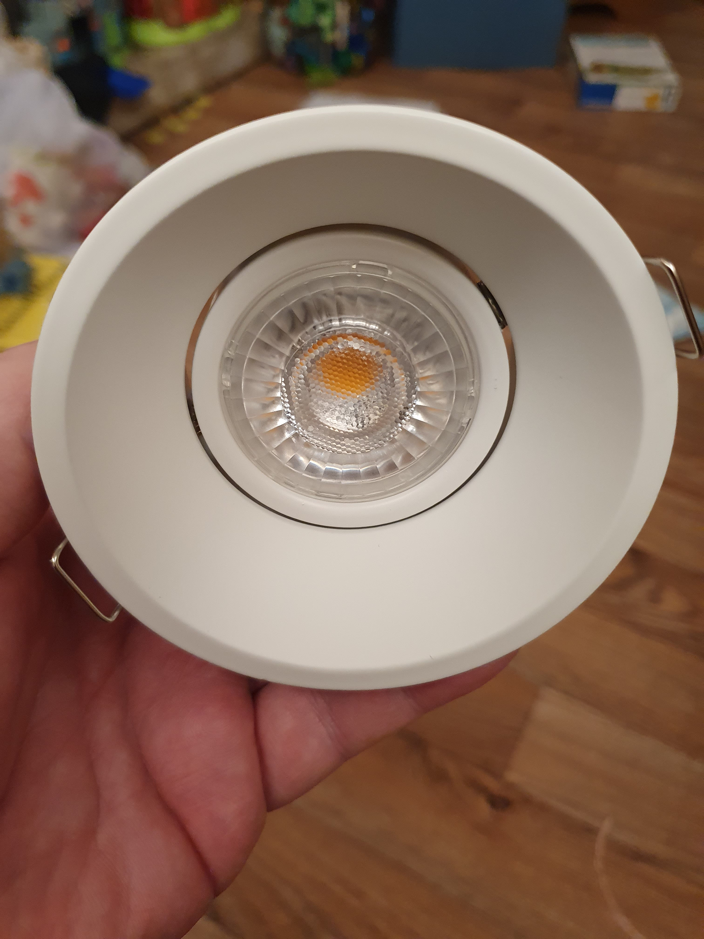
images/202312/20231207_002535.jpg
