ned14/HouseBuild/images/202312/20231207_002618.jpg

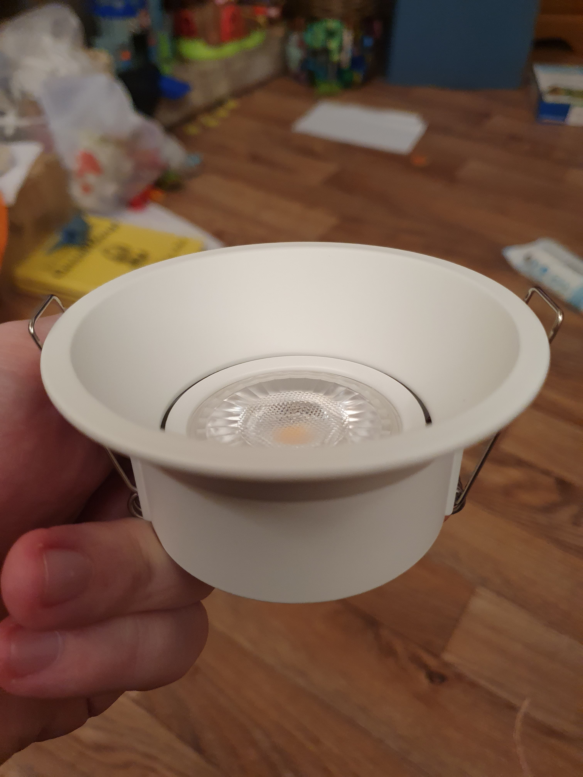
images/202312/20231207_002618.jpg
