ned14/HouseBuild/images/202312/20231214_150604.jpg

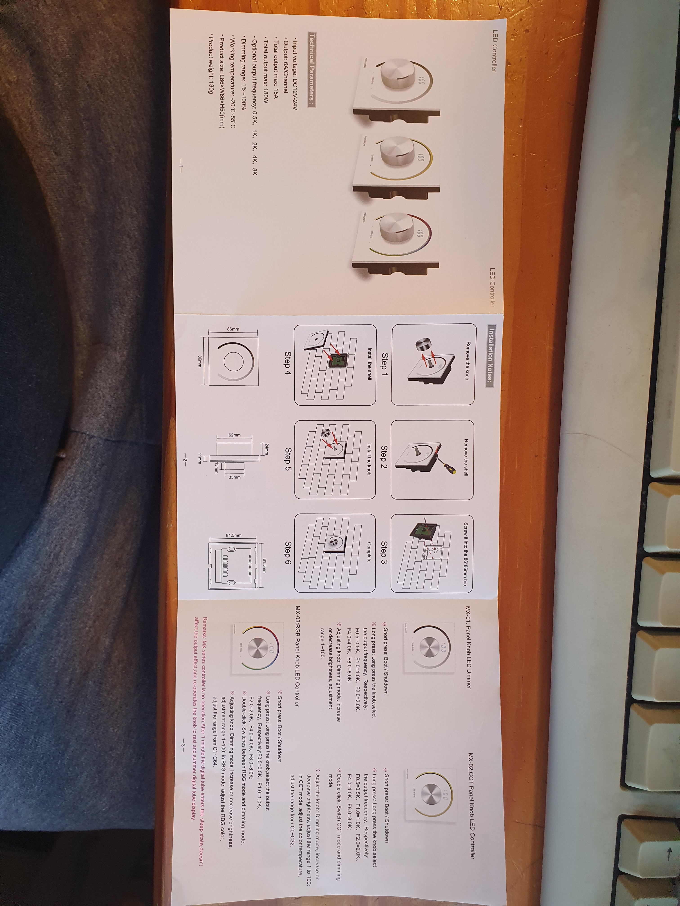
images/202312/20231214_150604.jpg
