ned14/HouseBuild/images/202312/20231215_133214.jpg

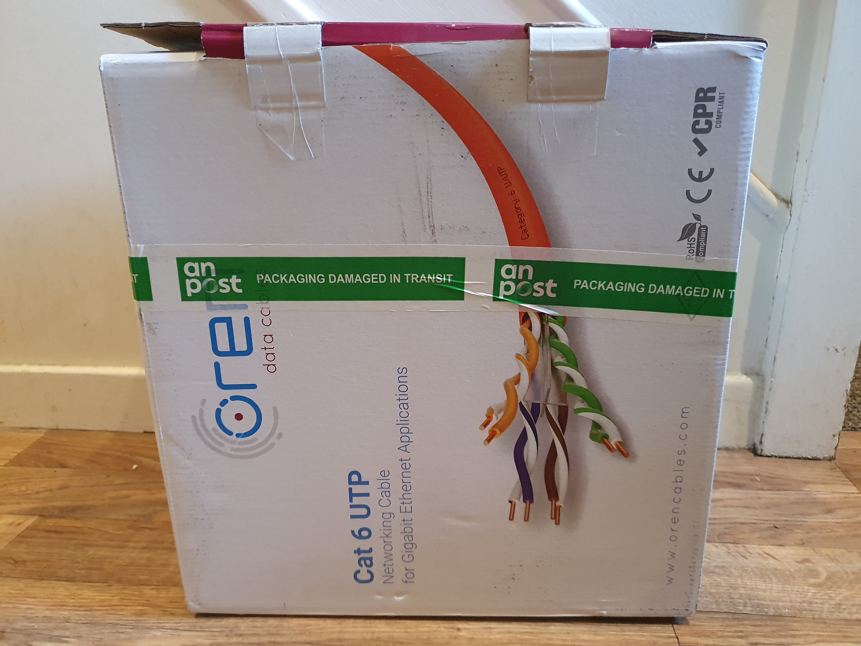
images/202312/20231215_133214.jpg
