ned14/HouseBuild/images/202312/20231215_133229.jpg

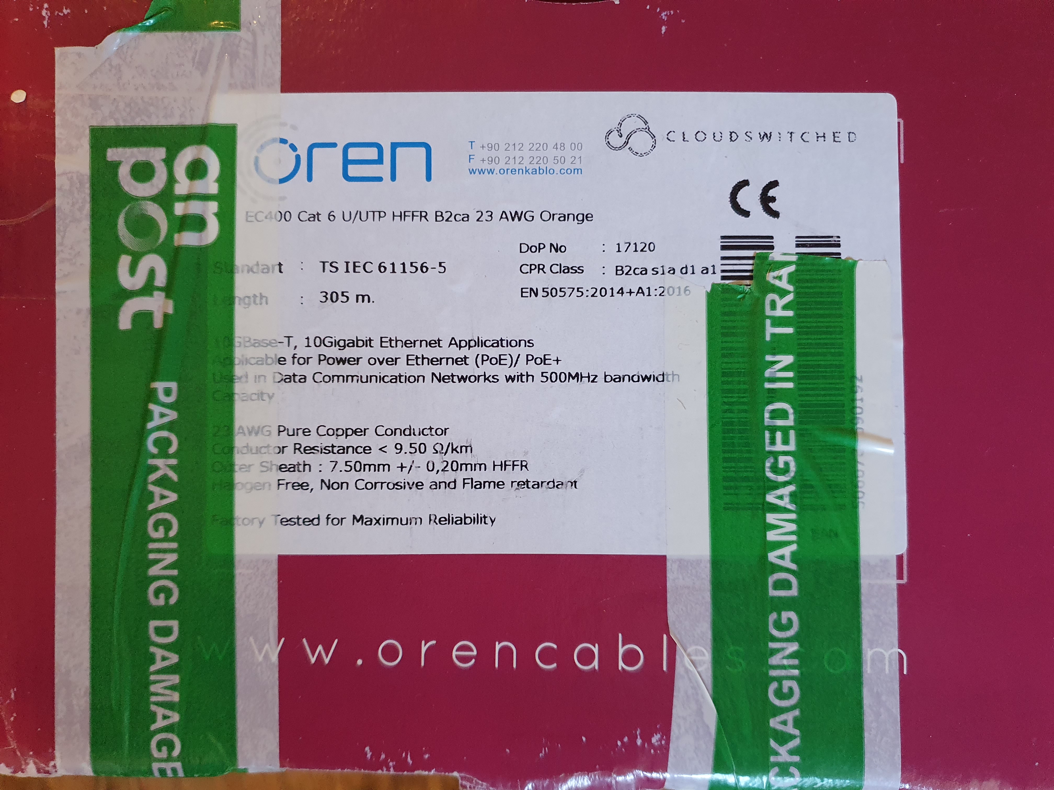
images/202312/20231215_133229.jpg
