ned14/HouseBuild/images/202312/20231217_002118.jpg

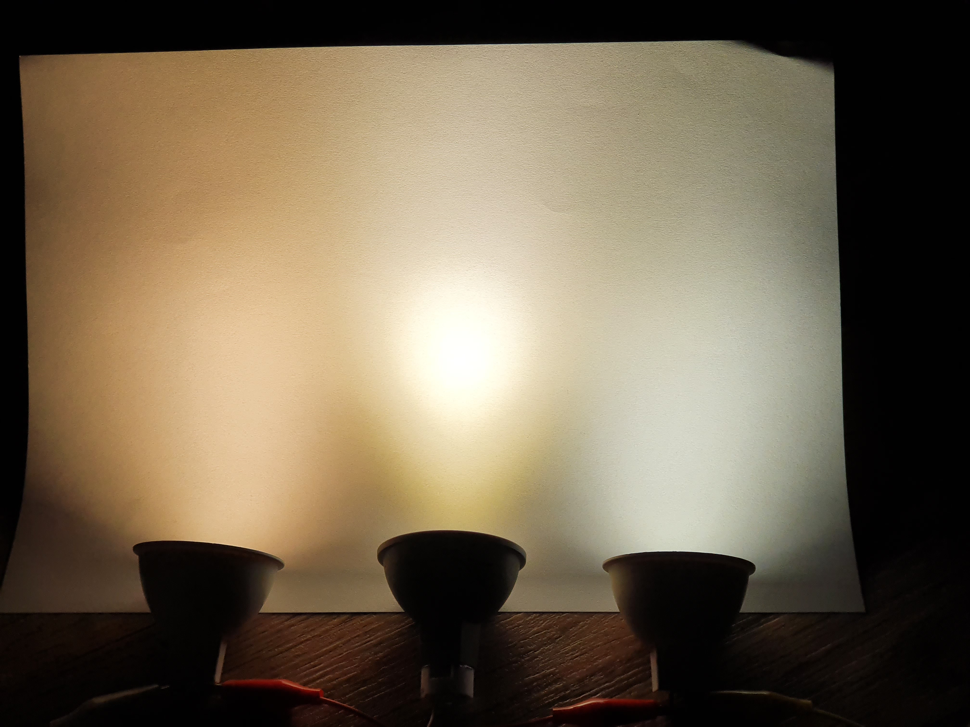
images/202312/20231217_002118.jpg
