ned14/HouseBuild/images/202312/20231217_002348.jpg

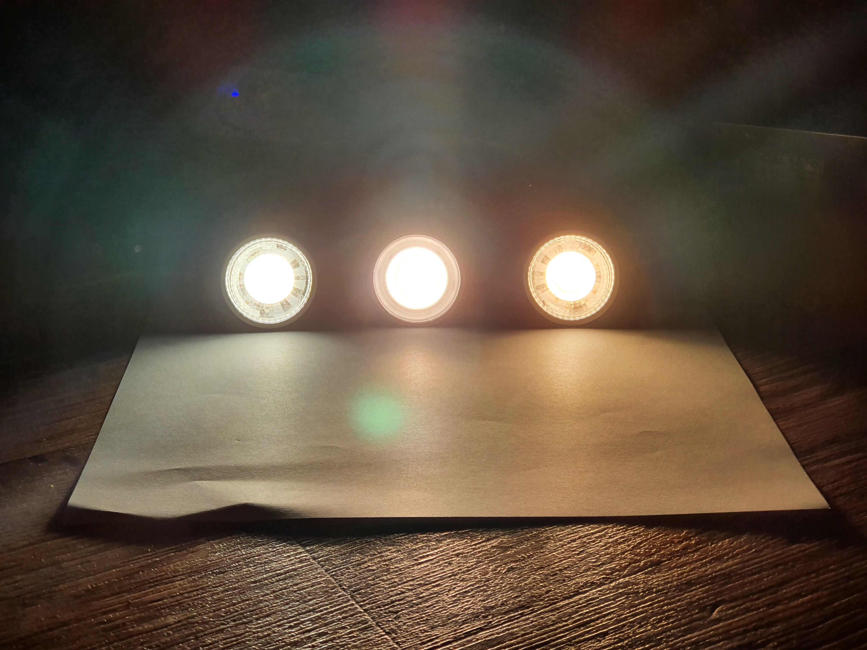
images/202312/20231217_002348.jpg
