ned14/HouseBuild/images/202312/20231217_020253.jpg

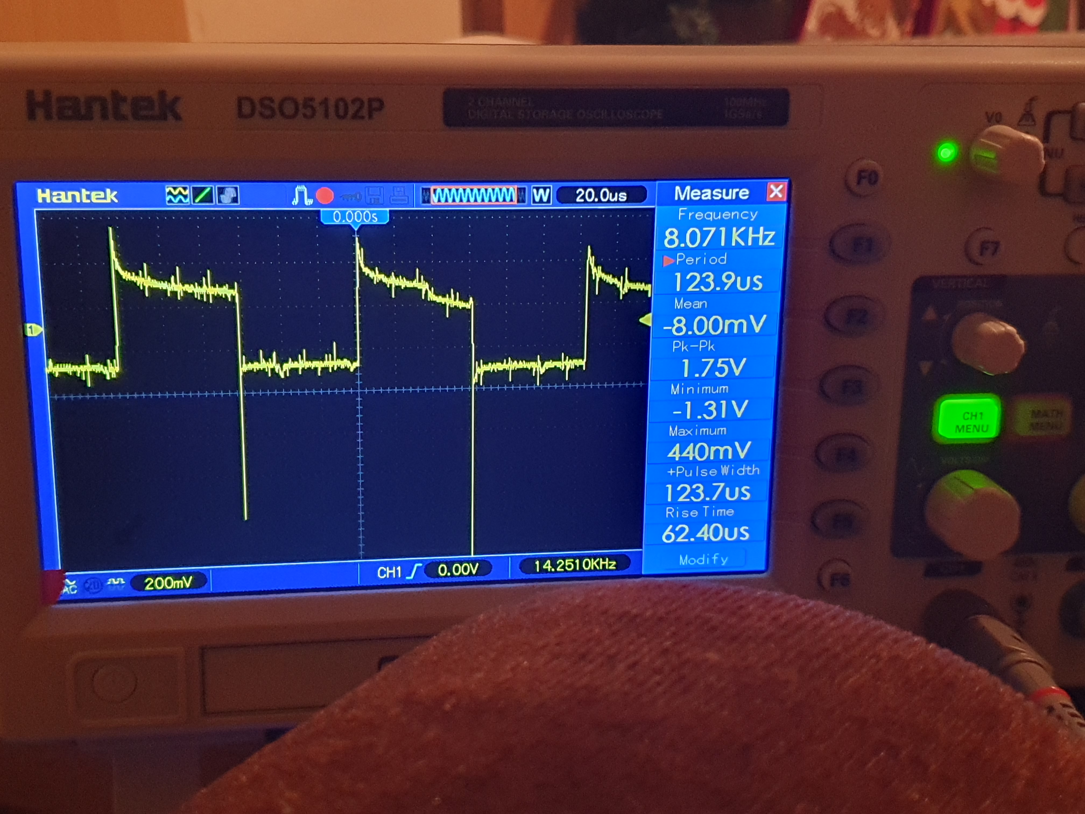
images/202312/20231217_020253.jpg
