ned14/HouseBuild/images/202312/20231217_025354.jpg

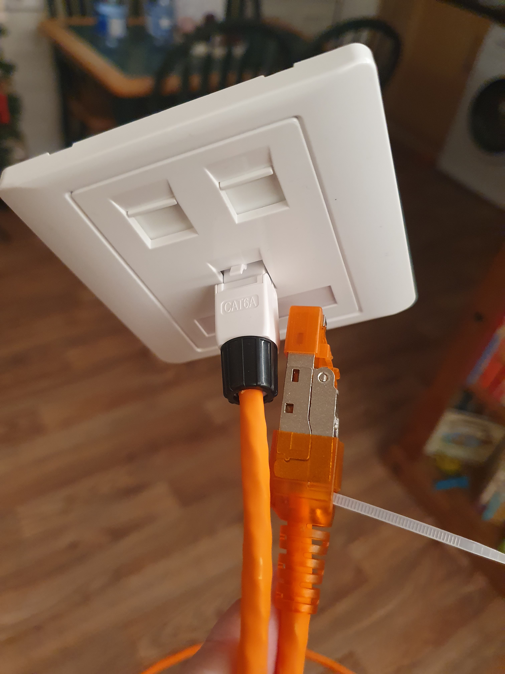
images/202312/20231217_025354.jpg
