ned14/HouseBuild/images/202312/20231222_134206.jpg

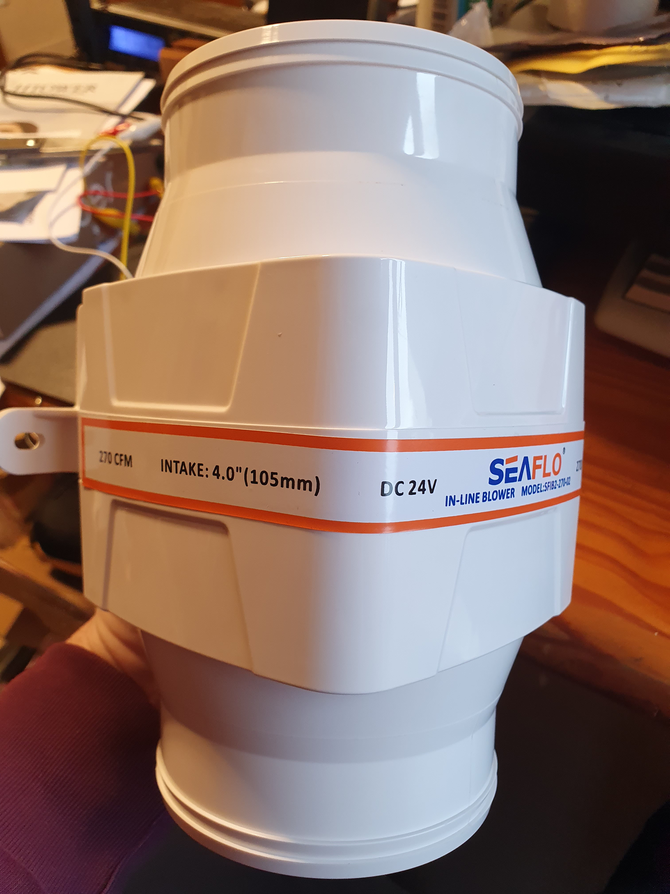
images/202312/20231222_134206.jpg
