ned14/HouseBuild/images/202401/front_left.jpg

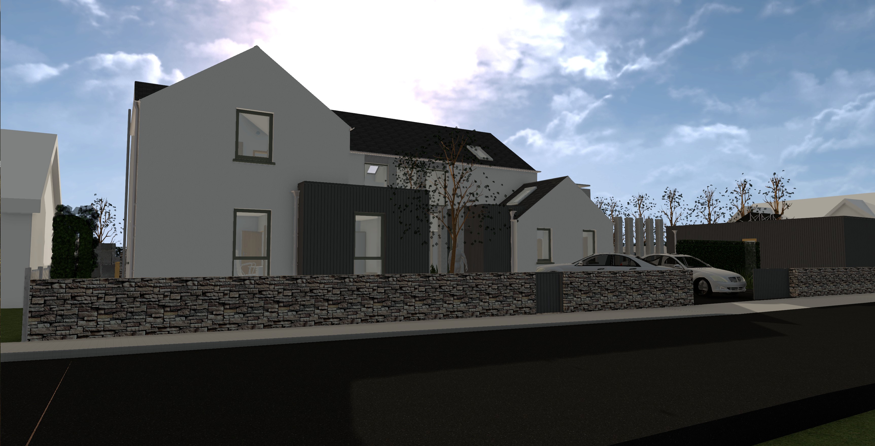
images/202401/front_left.jpg
