ned14/HouseBuild/images/202401/front_middle.jpg

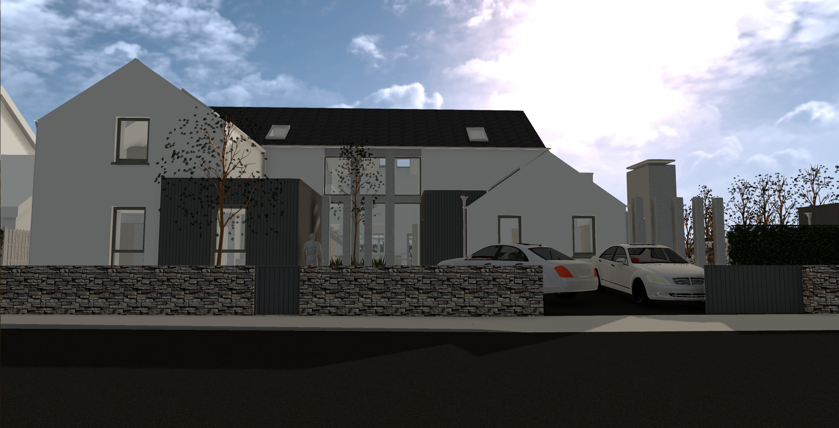
images/202401/front_middle.jpg
