ned14/HouseBuild/images/202401/front_right.jpg

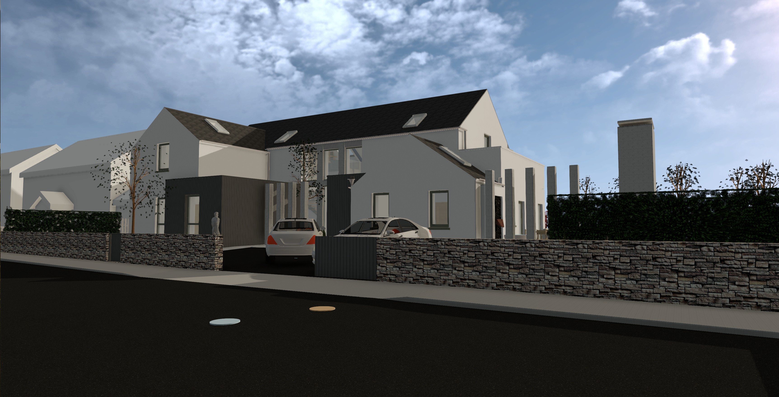
images/202401/front_right.jpg
