ned14/HouseBuild/images/202401/kitchen_at_living_room.jpg

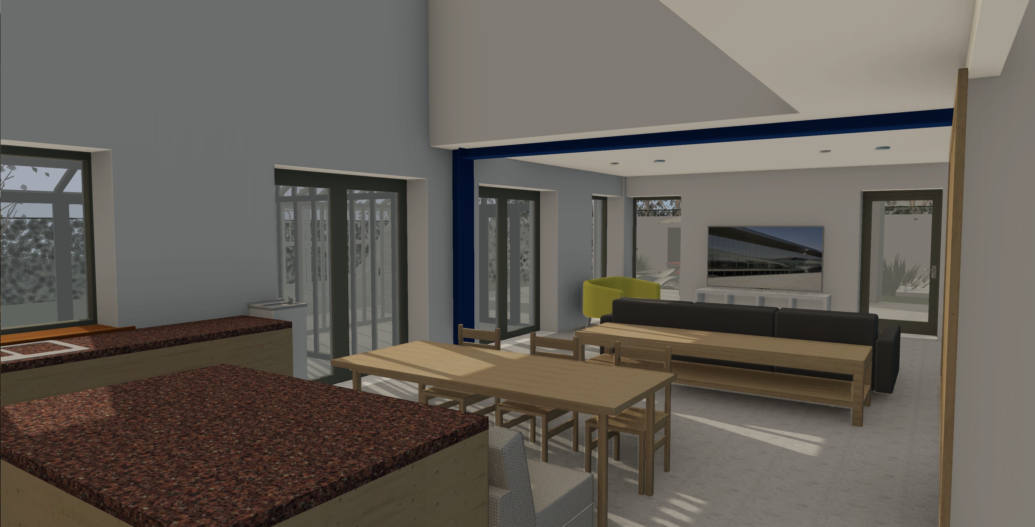
images/202401/kitchen_at_living_room.jpg
