ned14/HouseBuild/images/202401/living_room_at_mezzanine.jpg

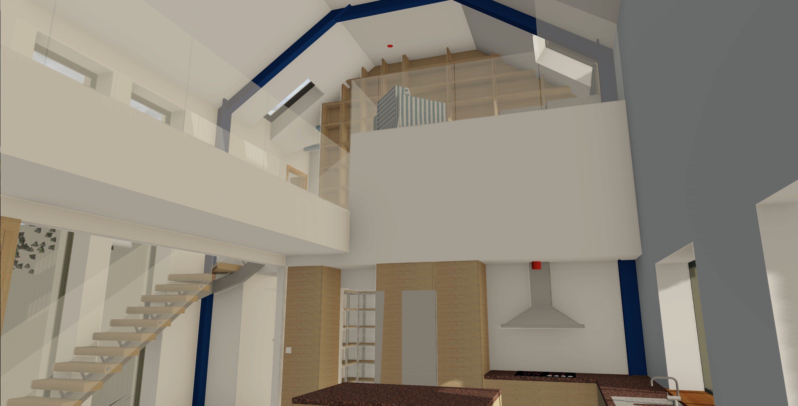
images/202401/living_room_at_mezzanine.jpg
