ned14/HouseBuild/images/202401/mezzanine_at_curtain_windows.jpg

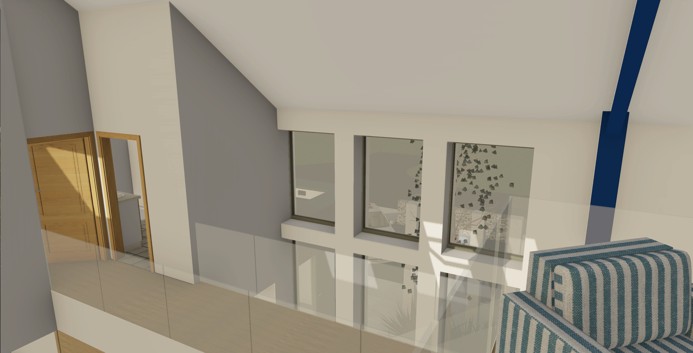
images/202401/mezzanine_at_curtain_windows.jpg
