ned14/HouseBuild/images/202401/office_at_ceiling.jpg

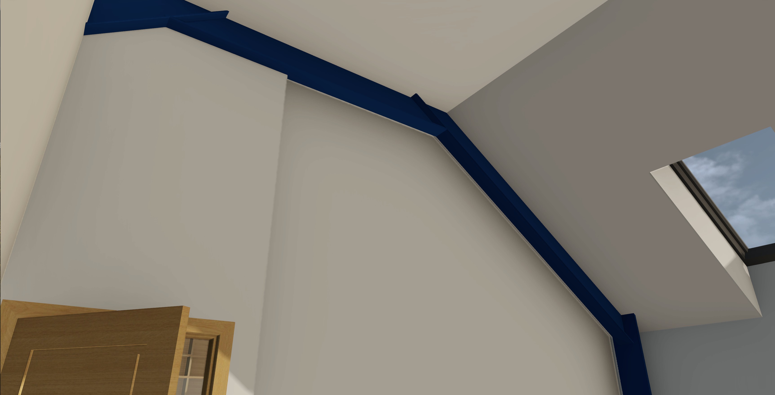
images/202401/office_at_ceiling.jpg
