ned14/HouseBuild/images/202401/office_at_workspace.jpg

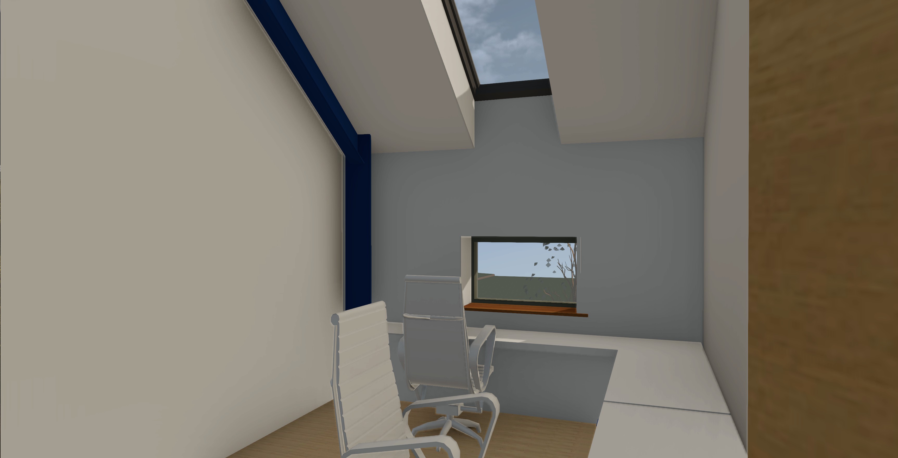
images/202401/office_at_workspace.jpg
