ned14/HouseBuild/images/202401/patio_left.jpg

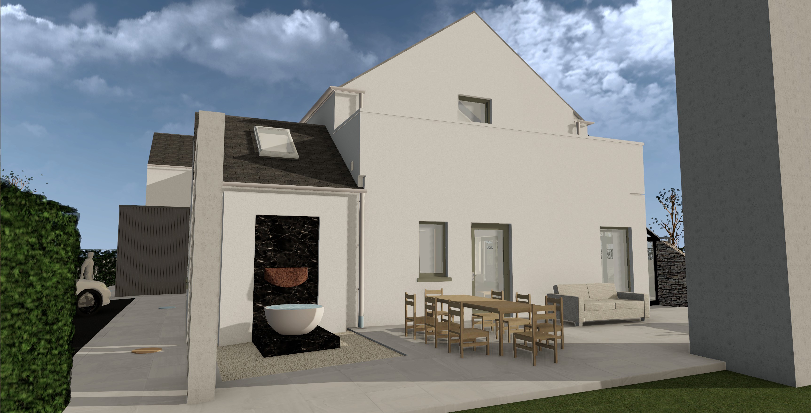
images/202401/patio_left.jpg
