ned14/HouseBuild/images/202401/patio_right.jpg

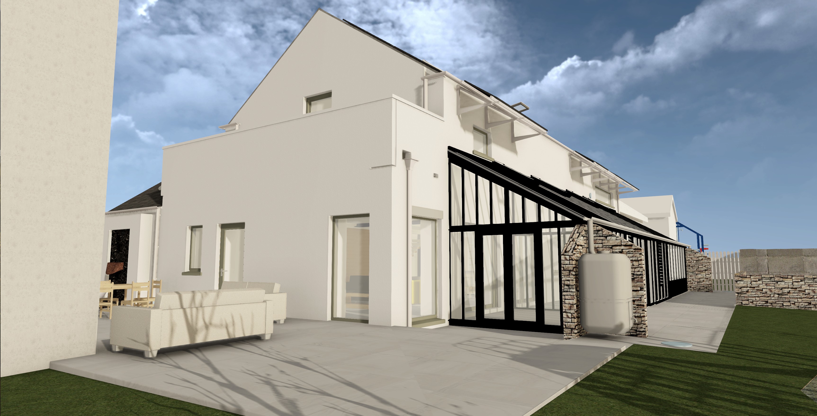
images/202401/patio_right.jpg
