ned14/HouseBuild/images/202401/rear_left.jpg

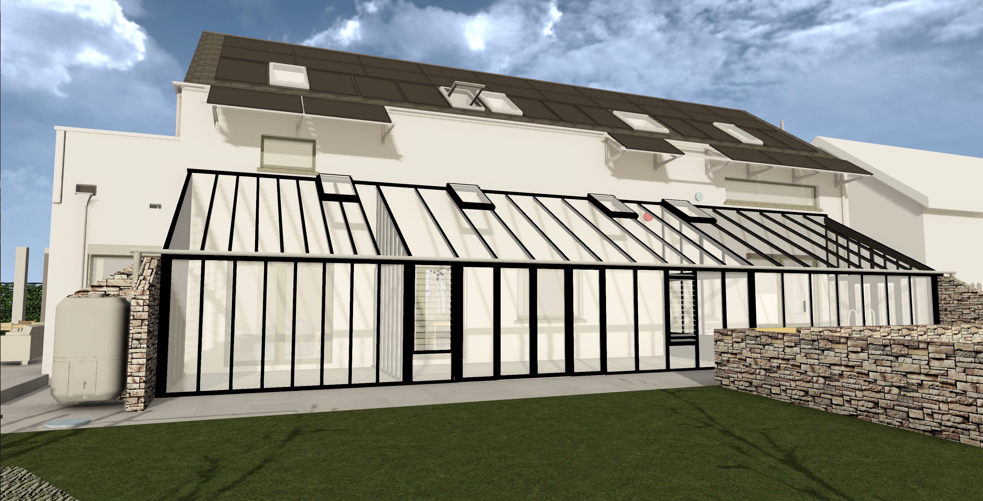
images/202401/rear_left.jpg
