ned14/HouseBuild/images/202401/rear_right.jpg

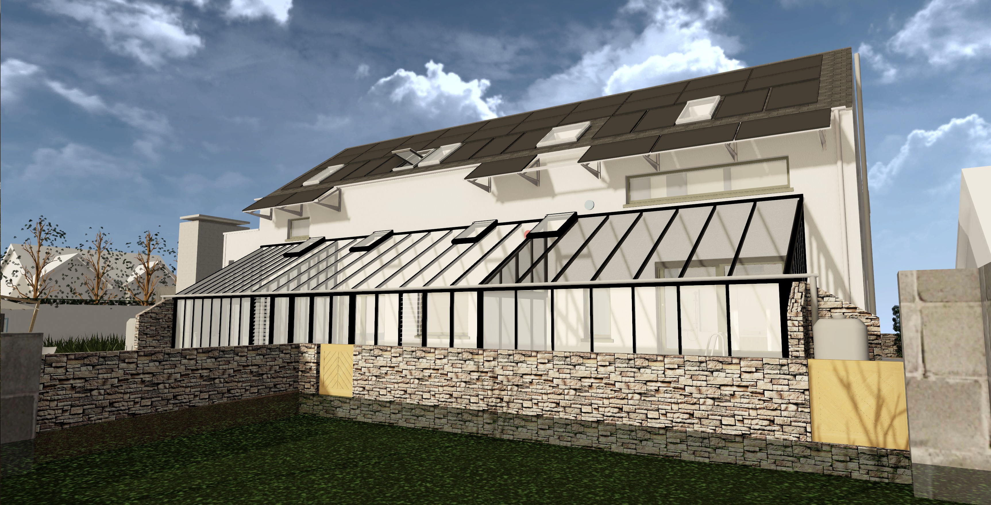
images/202401/rear_right.jpg
