ned14/HouseBuild/images/202401/structure_and_services.jpg

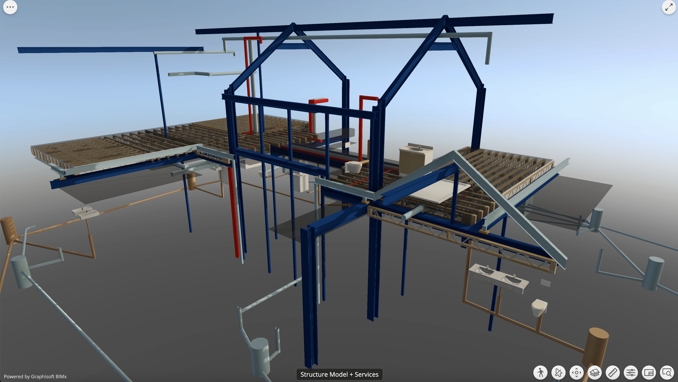
images/202401/structure_and_services.jpg
