ned14/HouseBuild/images/202401/top_of_stairs_at_roof.jpg

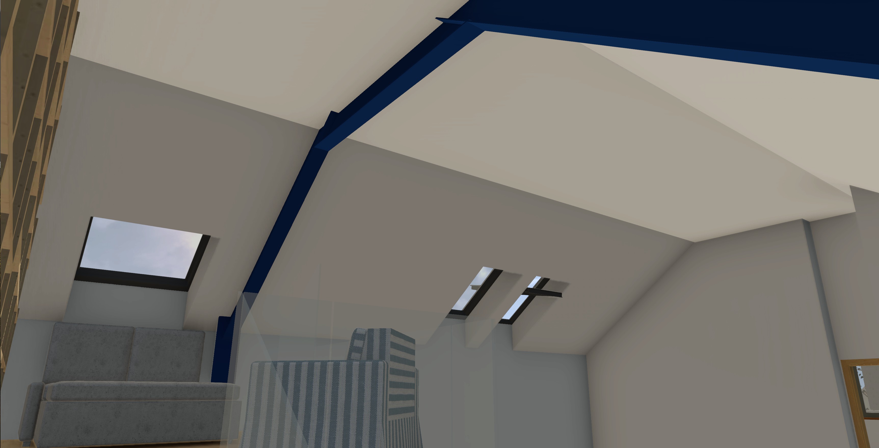
images/202401/top_of_stairs_at_roof.jpg
