ned14/HouseBuild/images/202403/20240303_220623.jpg

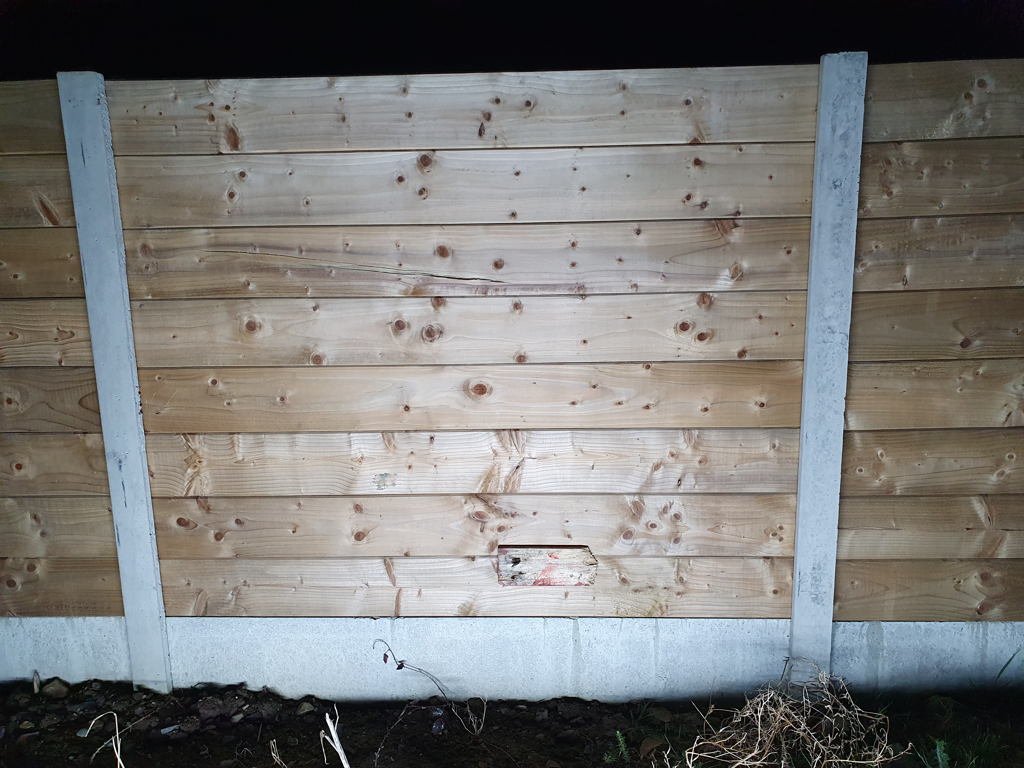
images/202403/20240303_220623.jpg
