ned14/HouseBuild/images/202403/20240303_221524.jpg

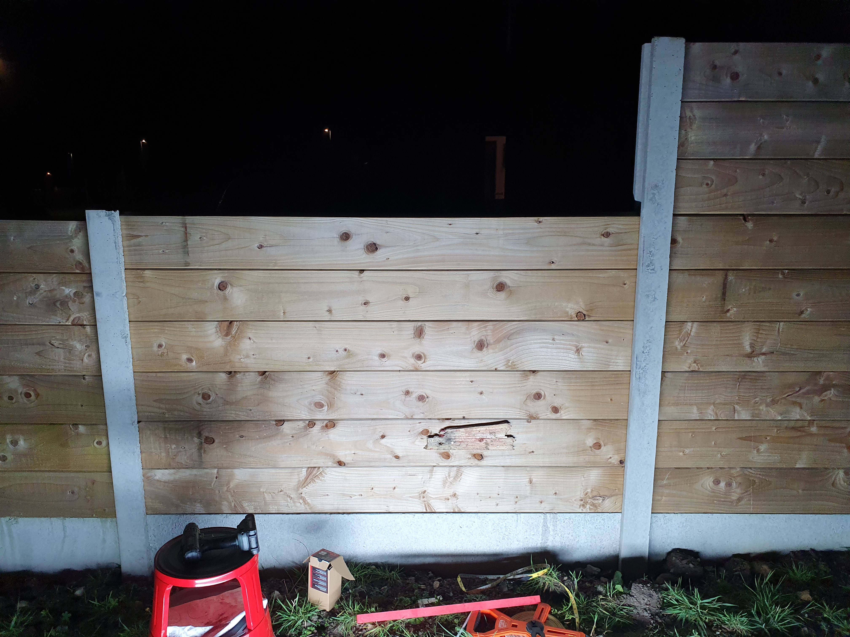
images/202403/20240303_221524.jpg
