ned14/HouseBuild/images/202403/20240303_222211.jpg

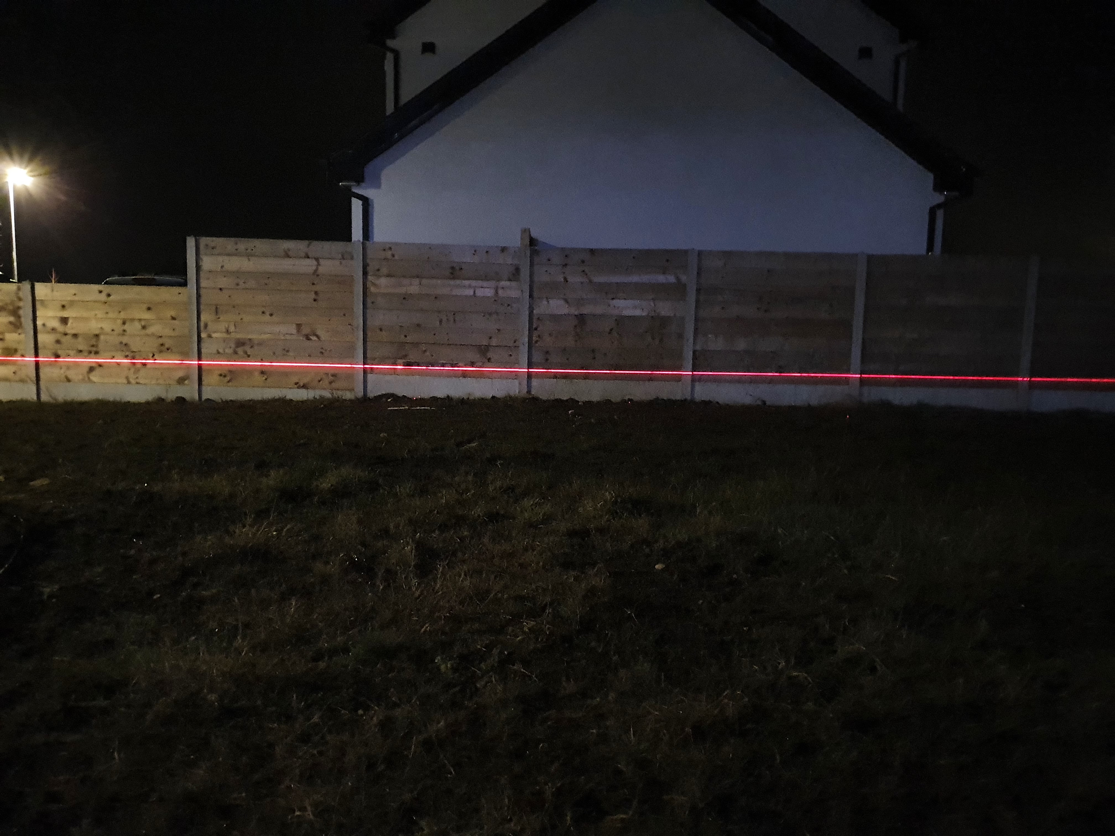
images/202403/20240303_222211.jpg
