ned14/HouseBuild/images/202405/20240520_130316.jpg

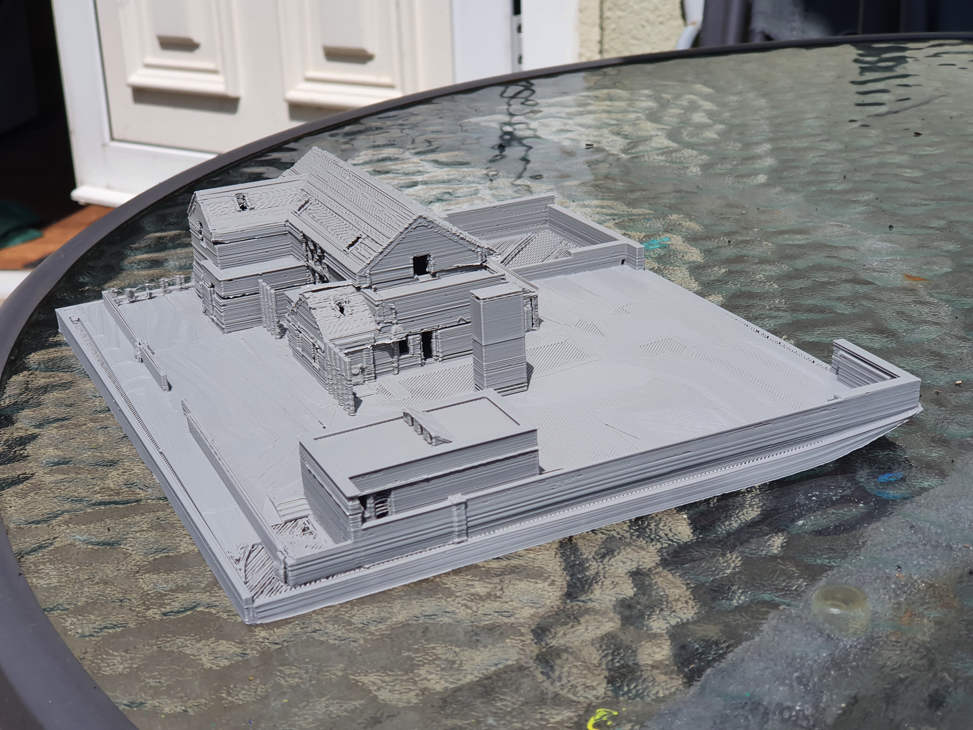
images/202405/20240520_130316.jpg
