ned14/HouseBuild/images/202405/20240520_130325.jpg

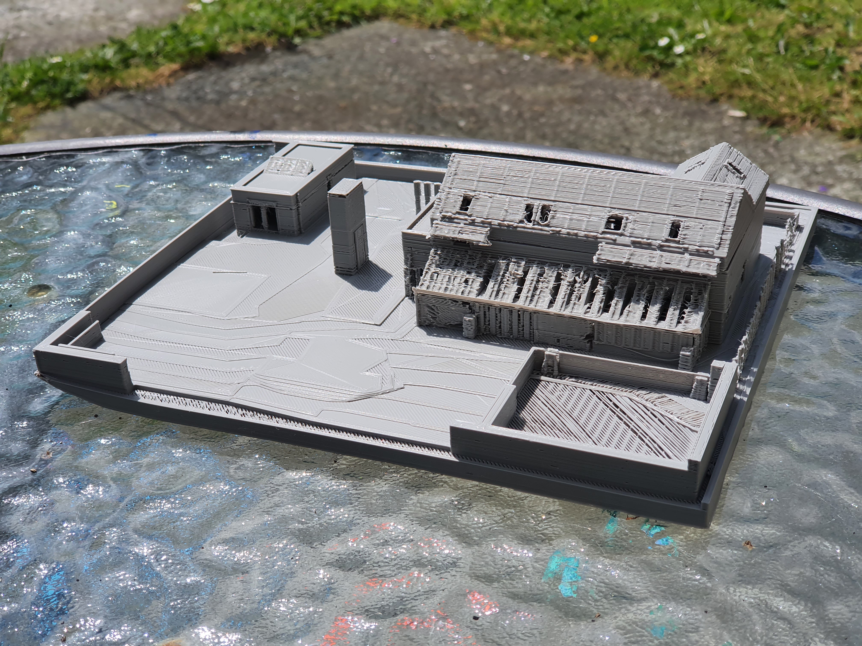
images/202405/20240520_130325.jpg
