ned14/HouseBuild/images/202405/20240530_122030.jpg

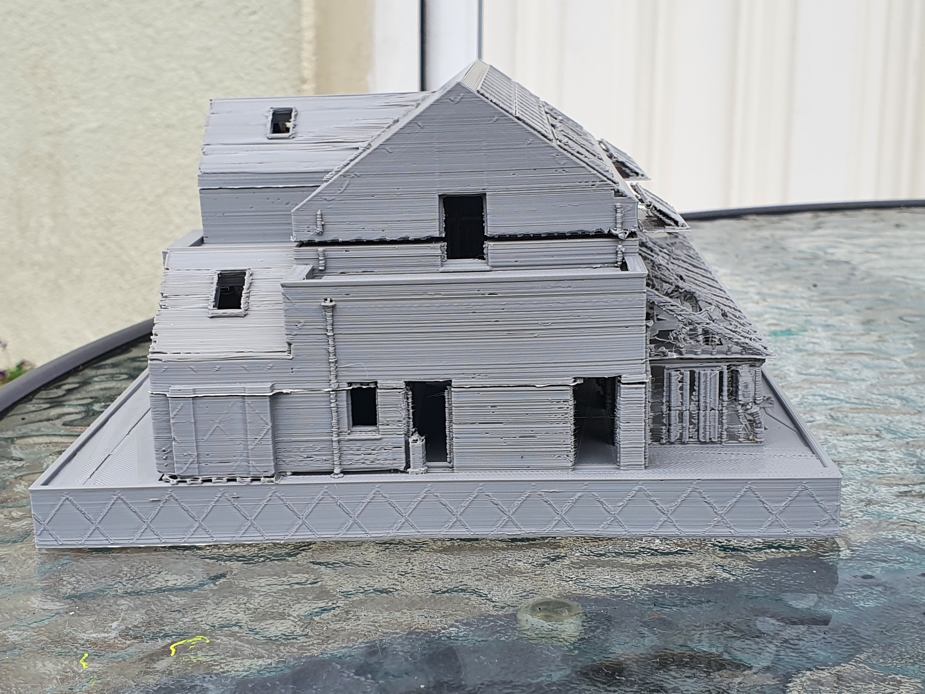
images/202405/20240530_122030.jpg
