ned14/HouseBuild/images/202405/IMG-20240511-WA0012.jpg

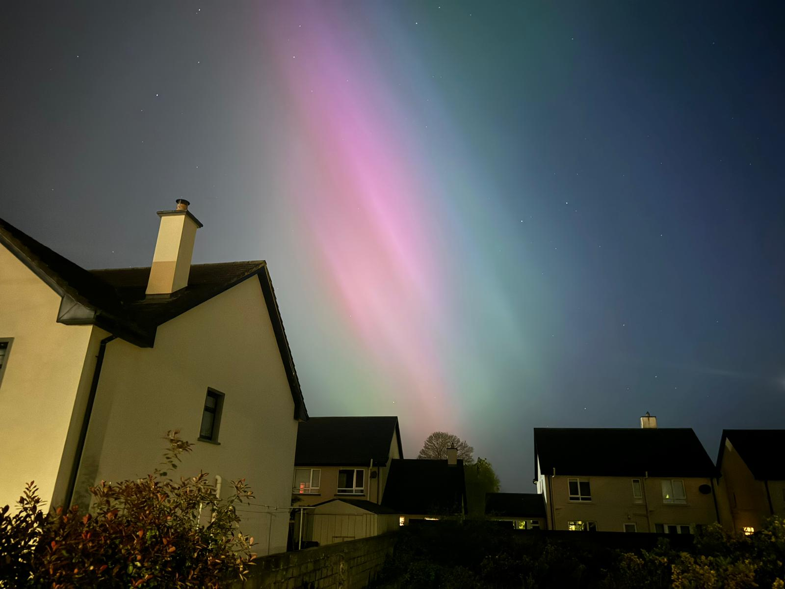
images/202405/IMG-20240511-WA0012.jpg
