ned14/HouseBuild/images/202406/20240611_125422.jpg

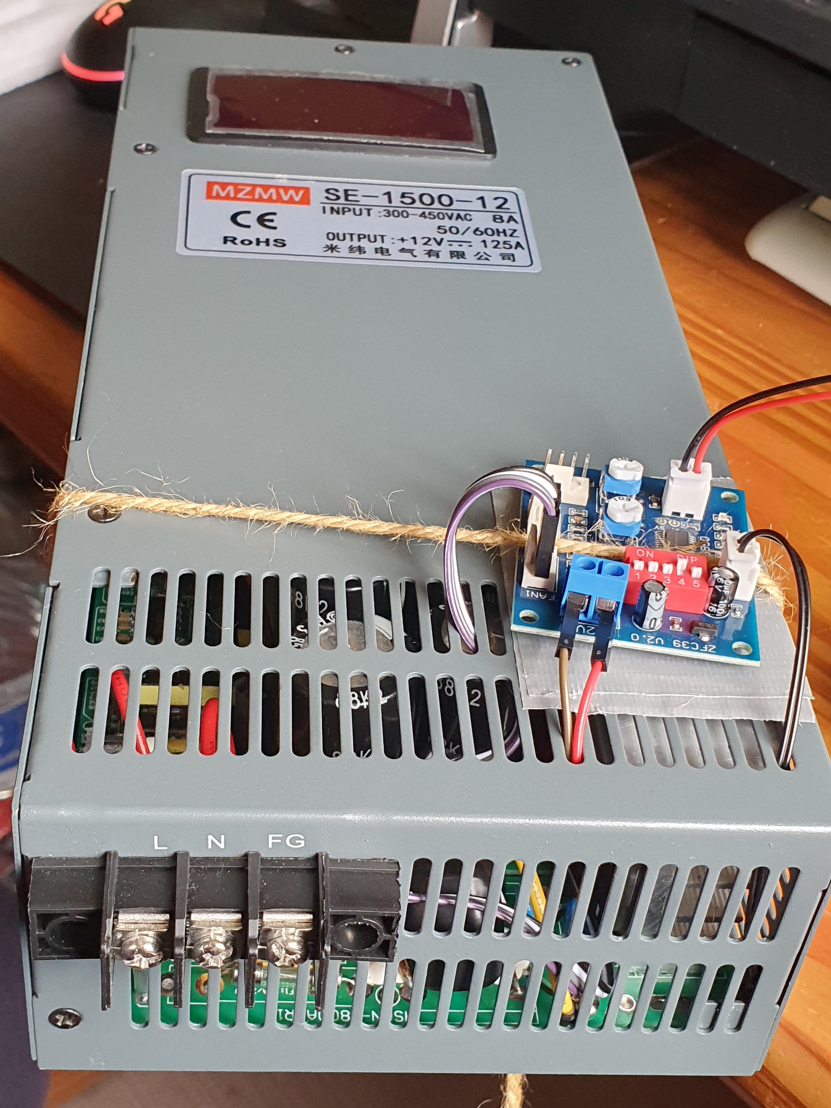
images/202406/20240611_125422.jpg
