ned14/HouseBuild/images/202406/20240616_202558.jpg

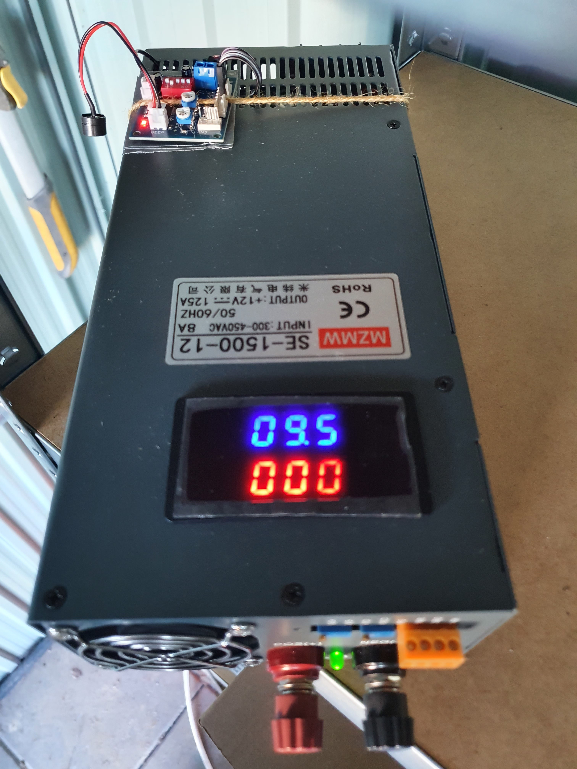
images/202406/20240616_202558.jpg
