ned14/HouseBuild/images/202406/20240627_113109.jpg

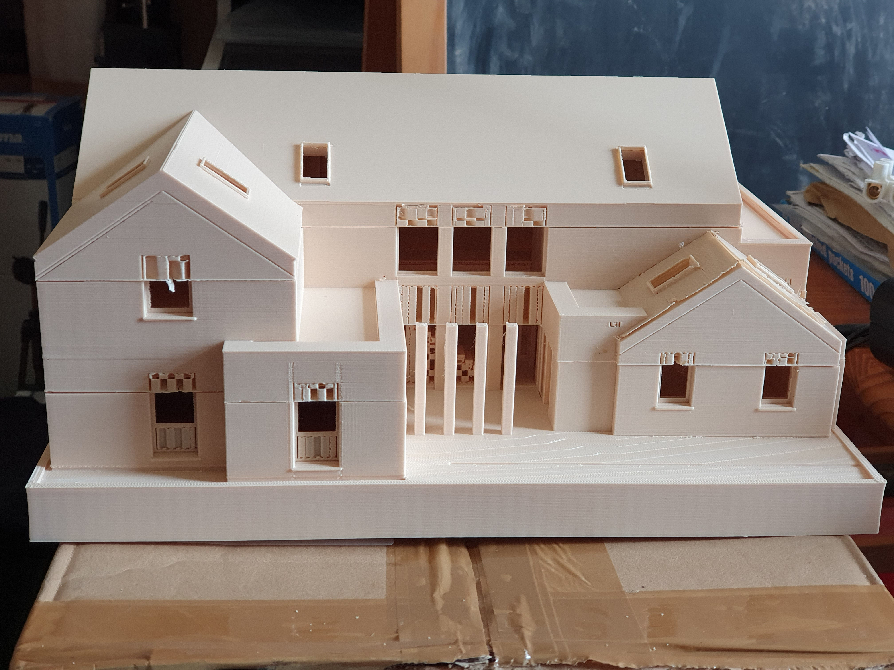
images/202406/20240627_113109.jpg
