ned14/HouseBuild/images/202406/20240628_104328.jpg

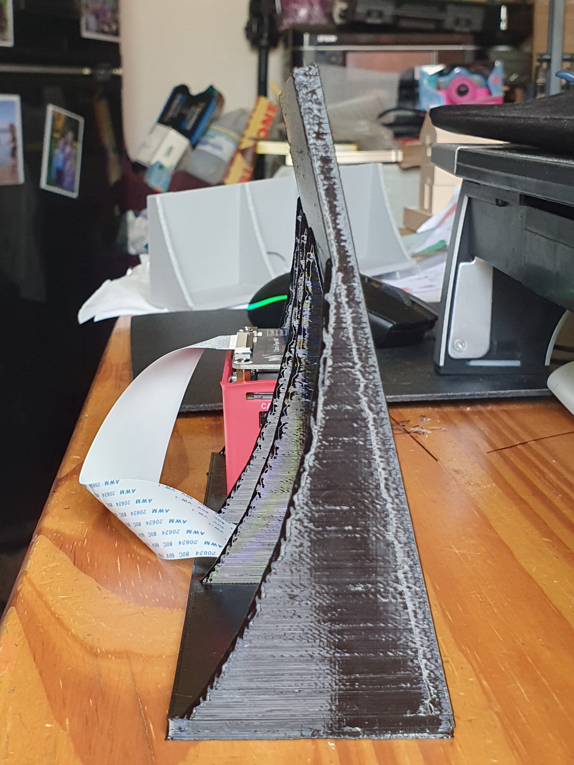
images/202406/20240628_104328.jpg
