ned14/HouseBuild/images/202406/20240701_011122.jpg

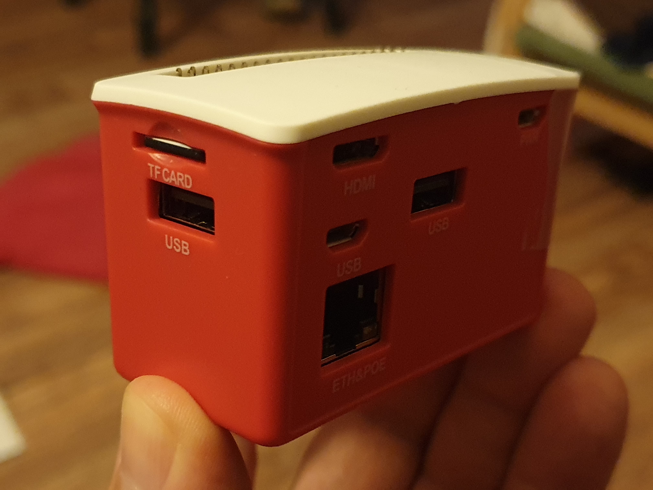
images/202406/20240701_011122.jpg
