ned14/HouseBuild/images/202406/20240701_011129.jpg

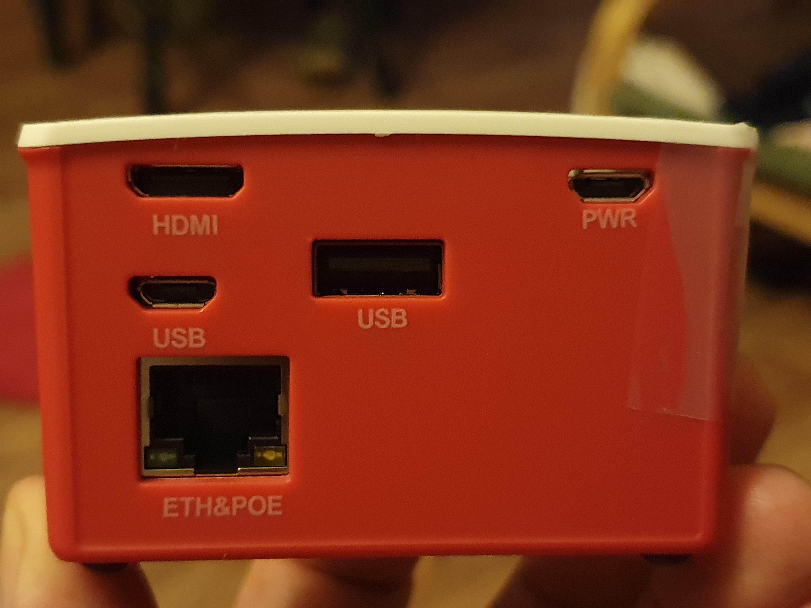
images/202406/20240701_011129.jpg
