ned14/HouseBuild/images/202407/20240709_220115.jpg

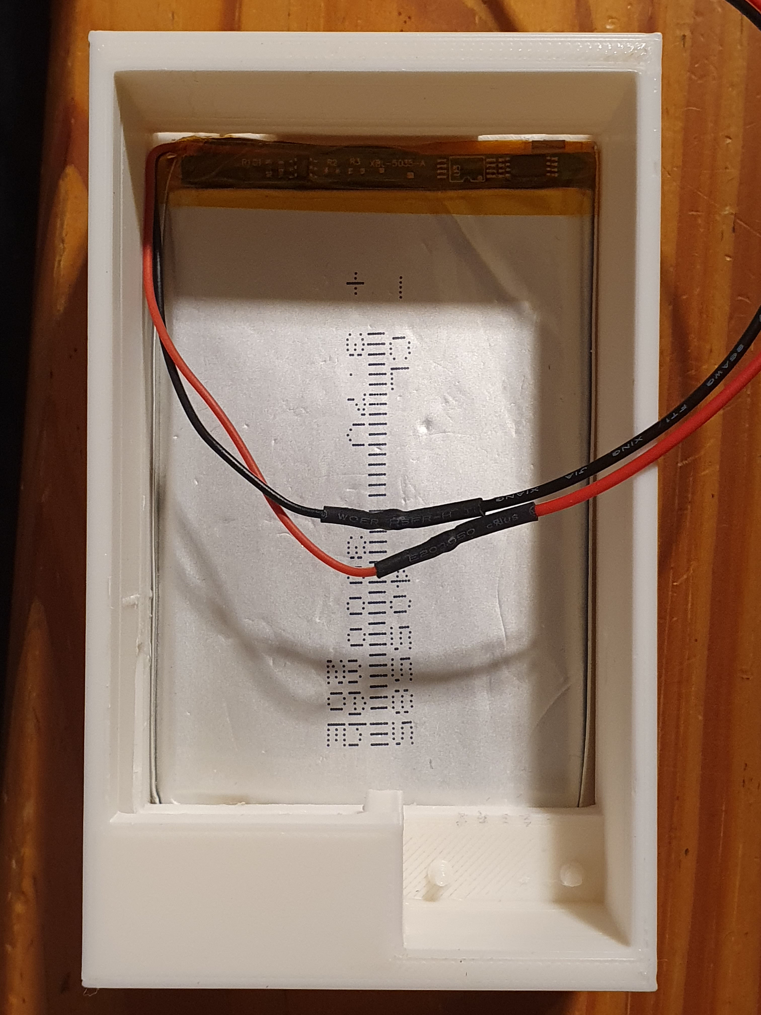
images/202407/20240709_220115.jpg
