ned14/HouseBuild/images/202407/20240709_220431.jpg

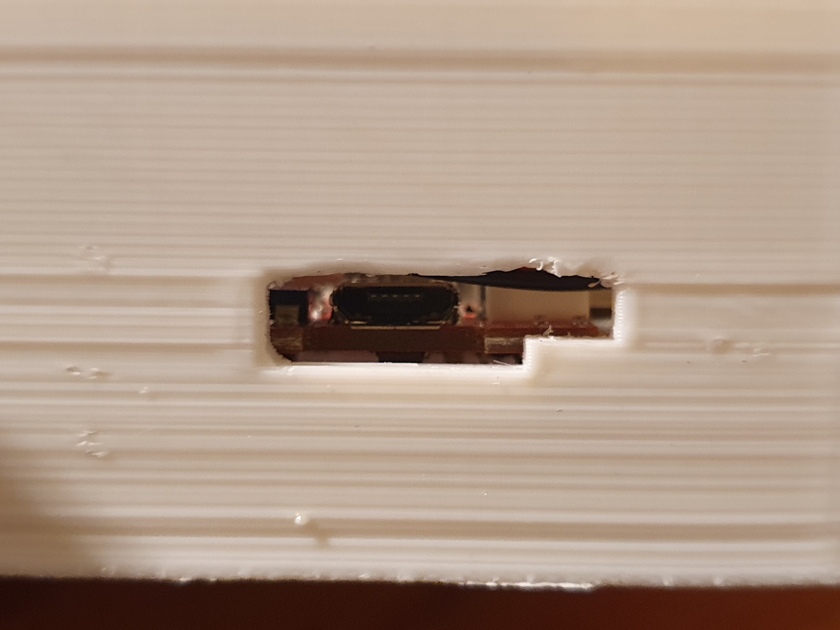
images/202407/20240709_220431.jpg
