ned14/HouseBuild/images/202407/20240714_013126.jpg

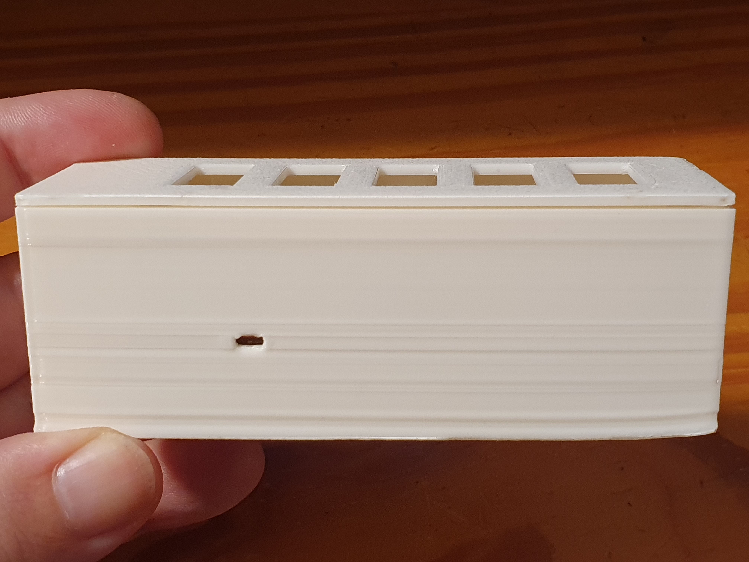
images/202407/20240714_013126.jpg
