ned14/HouseBuild/images/202407/20240714_013135.jpg

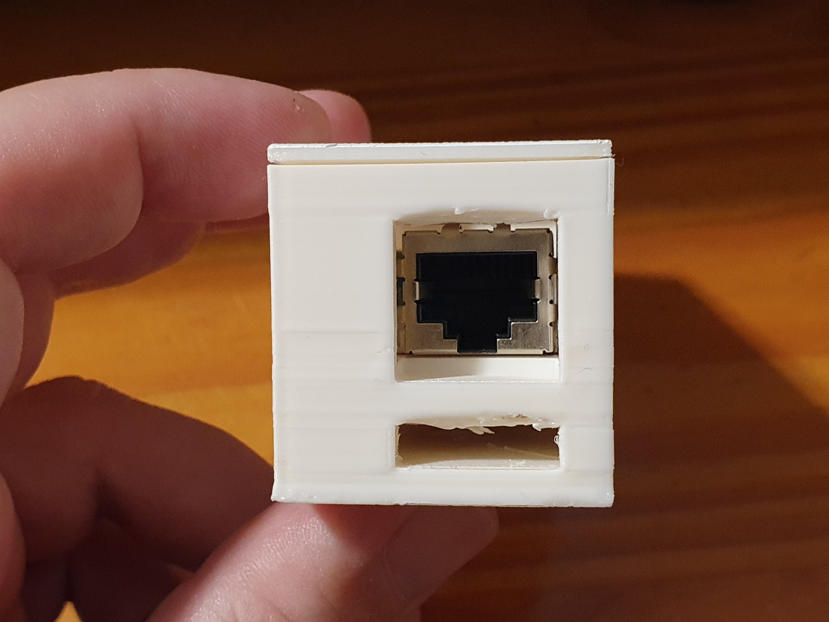
images/202407/20240714_013135.jpg
