ned14/HouseBuild/images/202407/20240714_013145.jpg

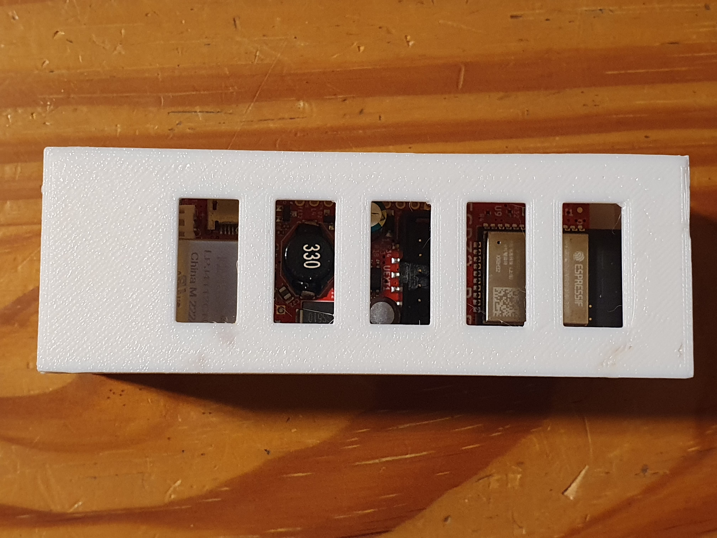
images/202407/20240714_013145.jpg
