ned14/HouseBuild/images/202407/20240714_013223.jpg

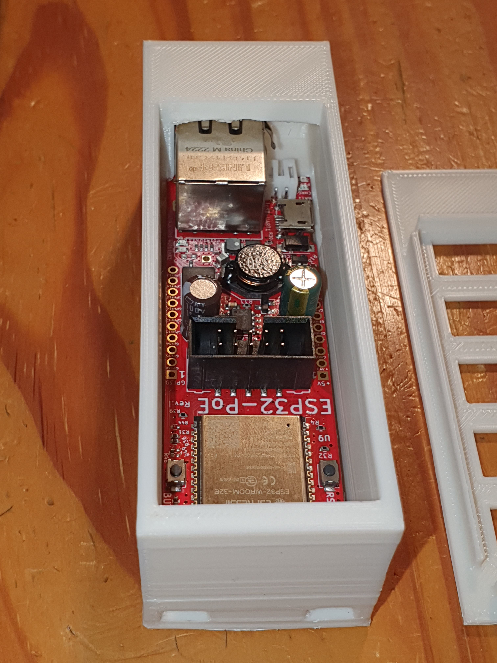
images/202407/20240714_013223.jpg
