ned14/HouseBuild/images/202407/20240717_140440.jpg

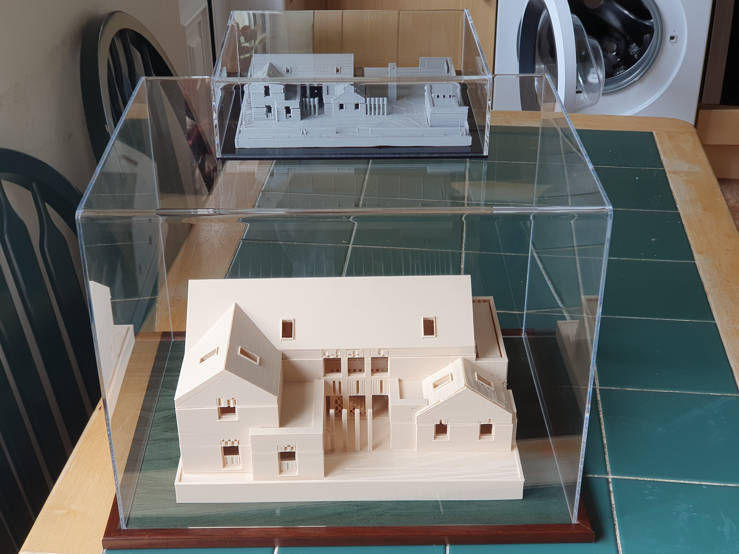
images/202407/20240717_140440.jpg
