ned14/HouseBuild/images/202408/20240824_224708.jpg

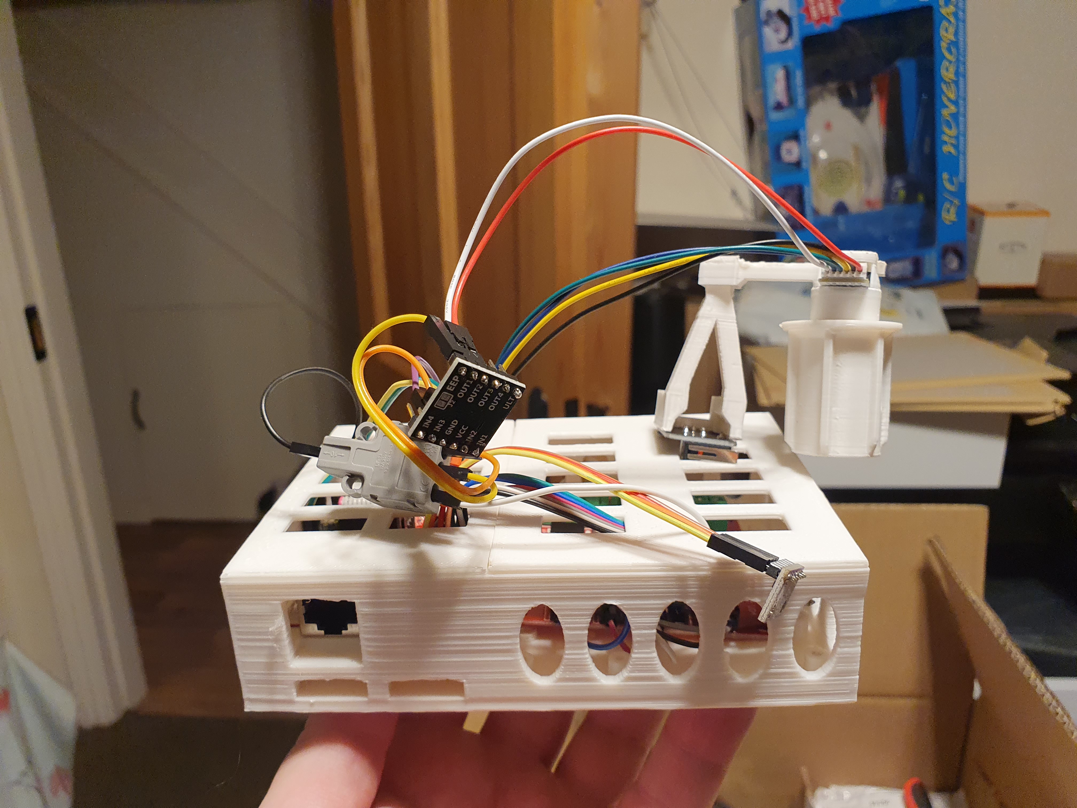
images/202408/20240824_224708.jpg
