ned14/HouseBuild/images/202408/20240824_224733.jpg

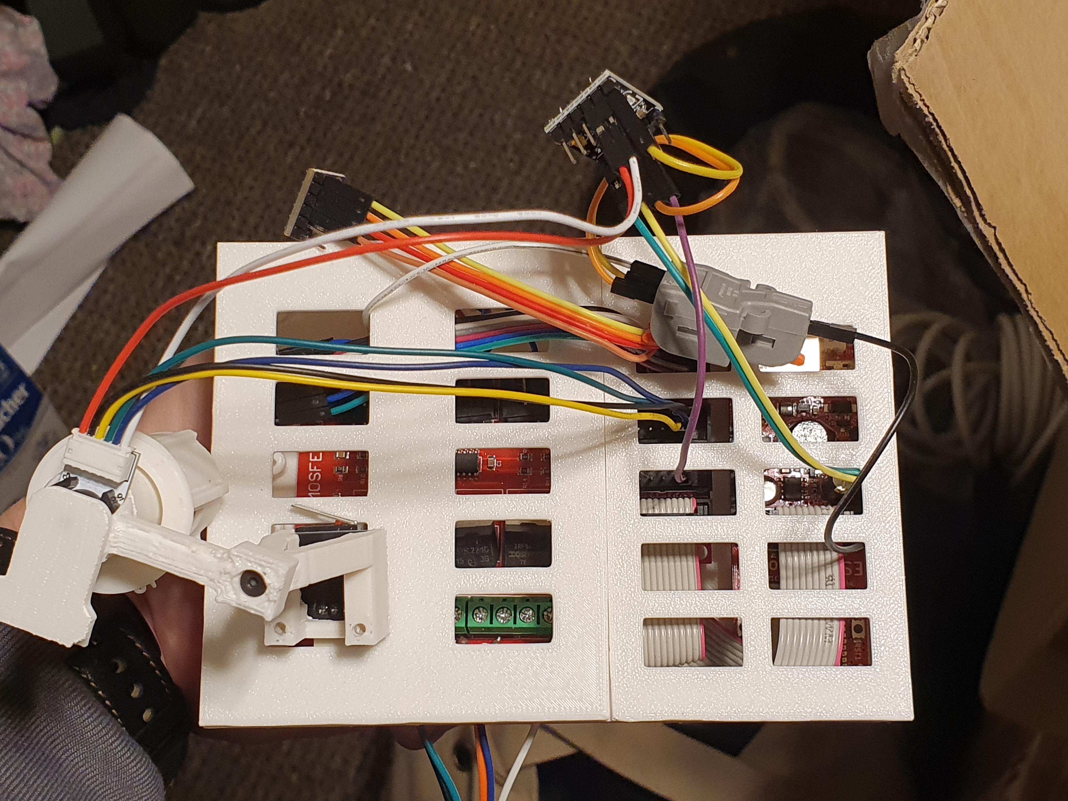
images/202408/20240824_224733.jpg
