ned14/HouseBuild/images/202408/20240825_000551.jpg

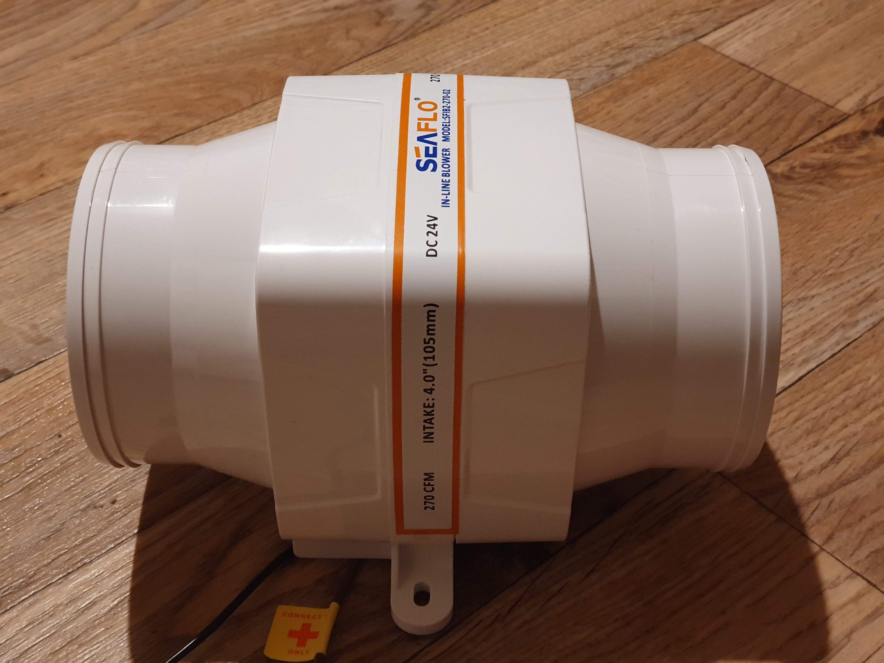
images/202408/20240825_000551.jpg
