ned14/HouseBuild/quotes/20221012_EcoTechHomes/ECO220-Flush-Eaves-detail-1030x863.jpg

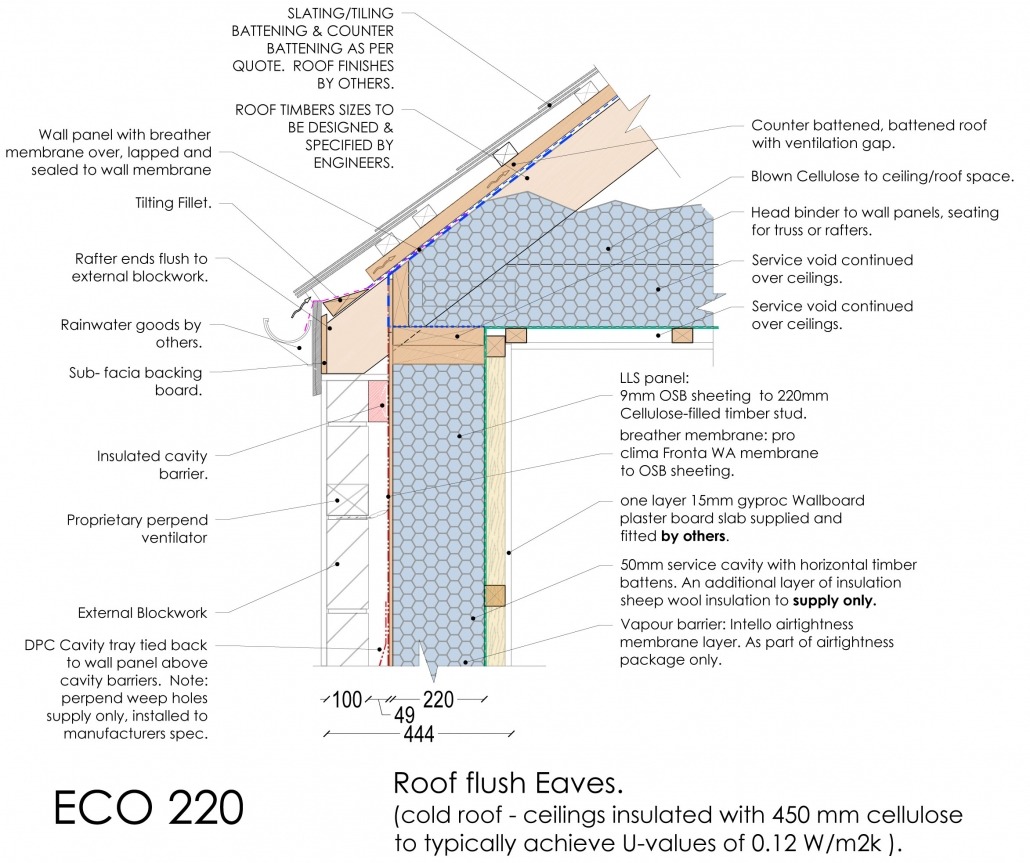
quotes/20221012_EcoTechHomes/ECO220-Flush-Eaves-detail-1030x863.jpg
