ned14/HouseBuild/quotes/20221012_EcoTechHomes/ECO220-Foundation-Raft-1030x974.jpg

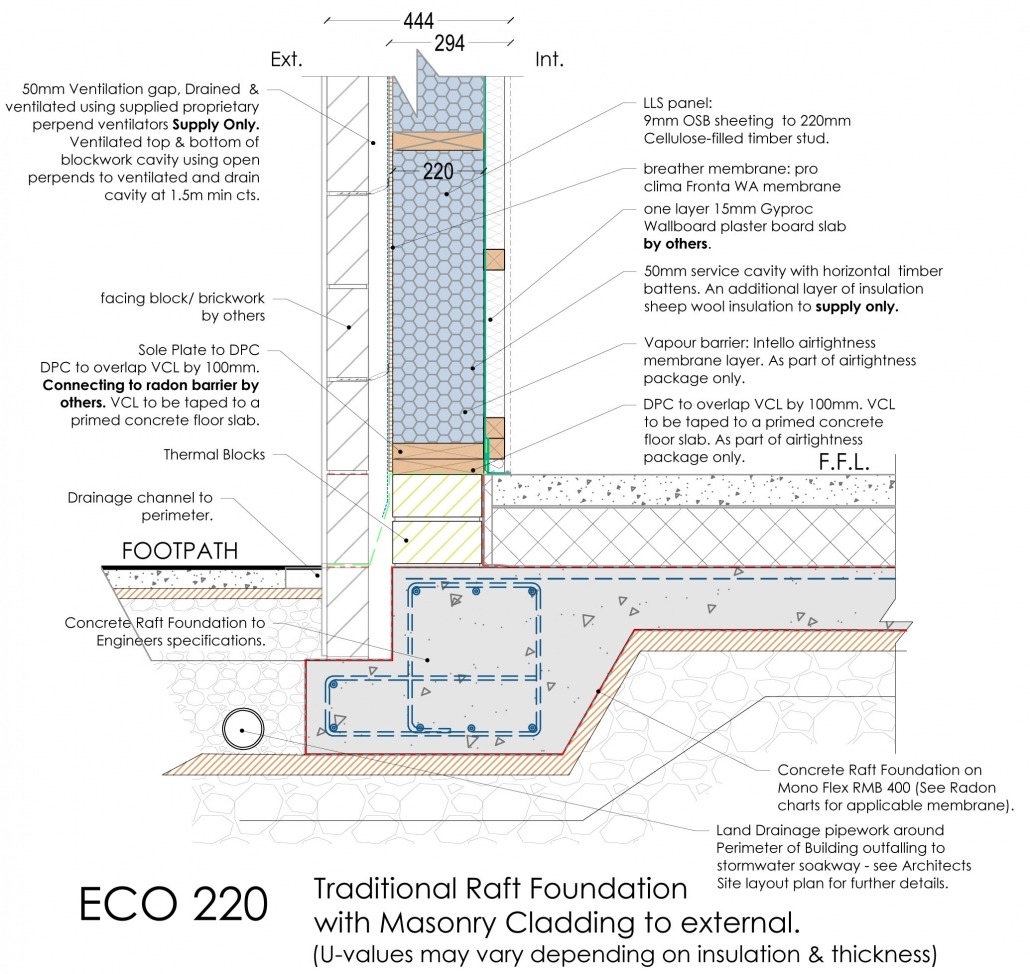
quotes/20221012_EcoTechHomes/ECO220-Foundation-Raft-1030x974.jpg
