ned14/HouseBuild/quotes/20221012_EcoTechHomes/ECO220-Insulated-Foundation-1014x1030.jpg

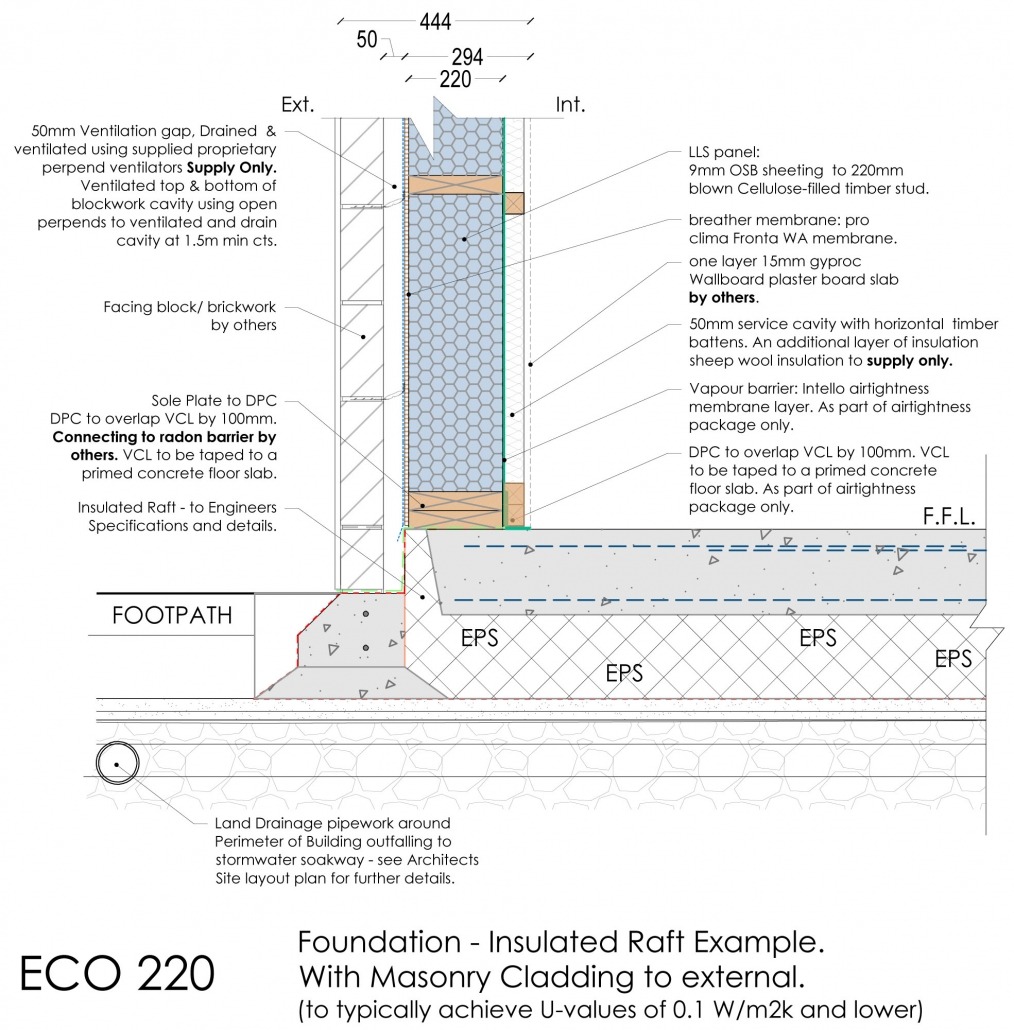
quotes/20221012_EcoTechHomes/ECO220-Insulated-Foundation-1014x1030.jpg
