ned14/HouseBuild/quotes/20221012_EcoTechHomes/ECO220-Thermal-Envelope-1-1030x556.jpg

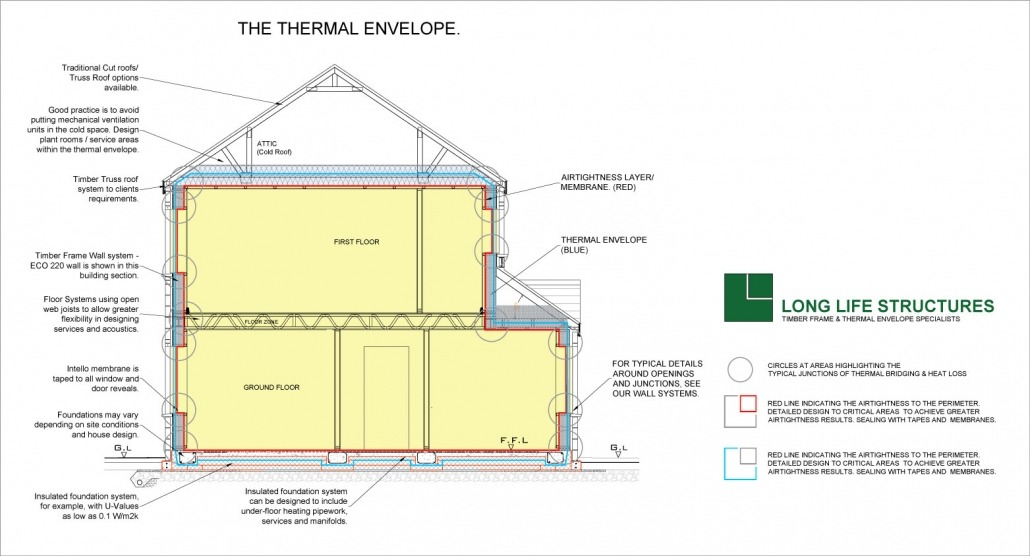
quotes/20221012_EcoTechHomes/ECO220-Thermal-Envelope-1-1030x556.jpg
