ned14/HouseBuild/quotes/20221012_EcoTechHomes/ECO220-Wall-Corner-Section-1015x1030.jpg

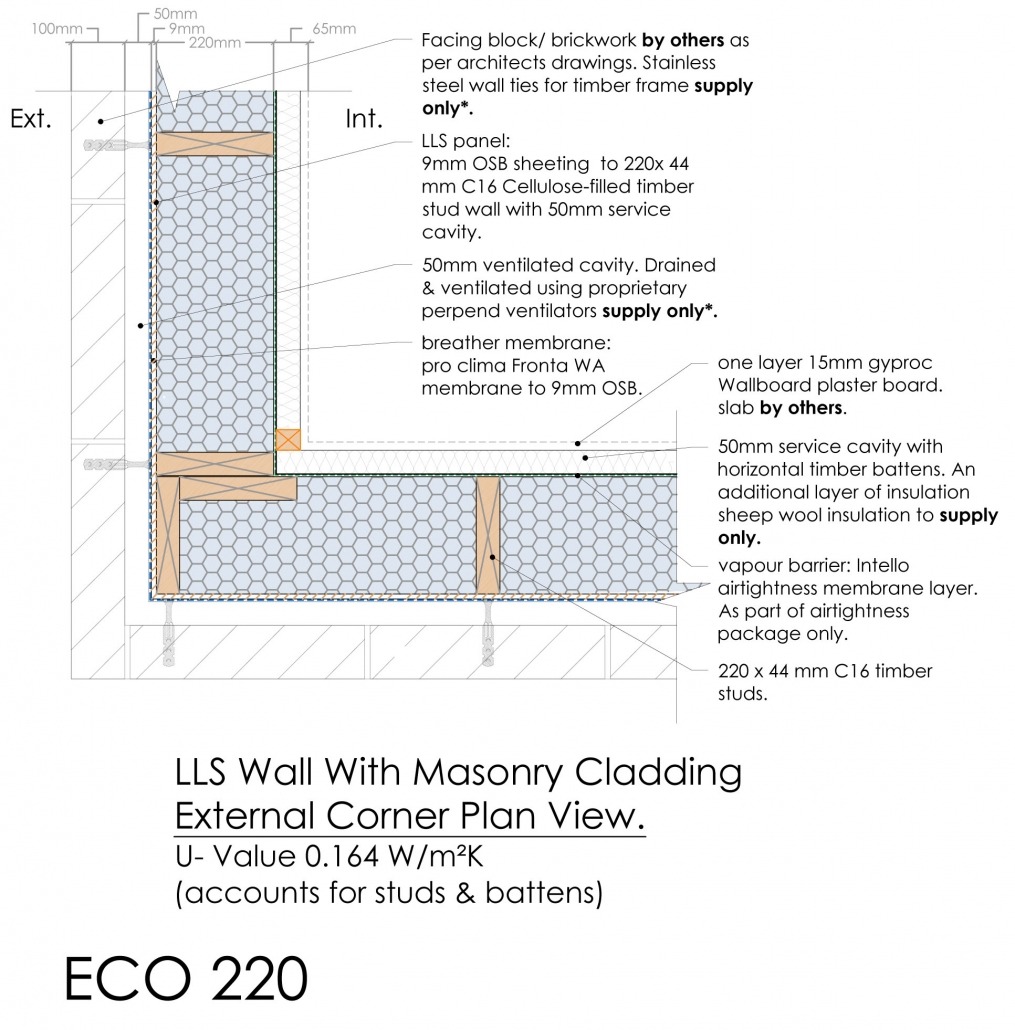
quotes/20221012_EcoTechHomes/ECO220-Wall-Corner-Section-1015x1030.jpg
