ned14/HouseBuild/quotes/20221012_EcoTechHomes/ECO220-Wall-Elements-scaled-1030x839.jpg

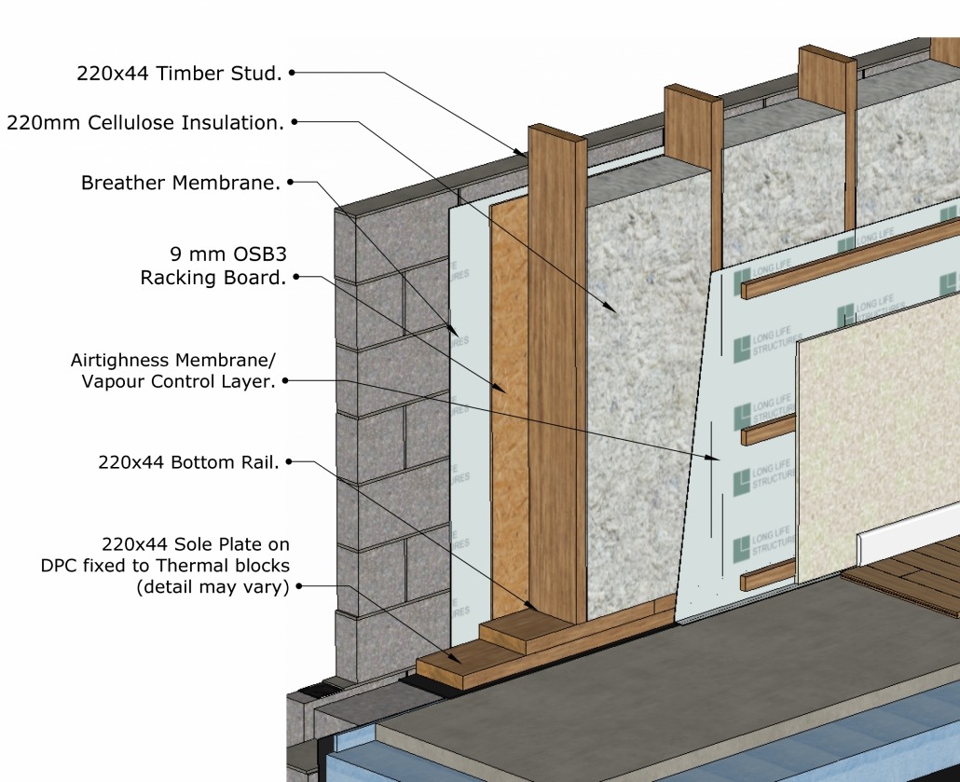
quotes/20221012_EcoTechHomes/ECO220-Wall-Elements-scaled-1030x839.jpg
