ned14/HouseBuild/quotes/20240131_LongLifeStructures/Insulated Foundation timberframe connection.png

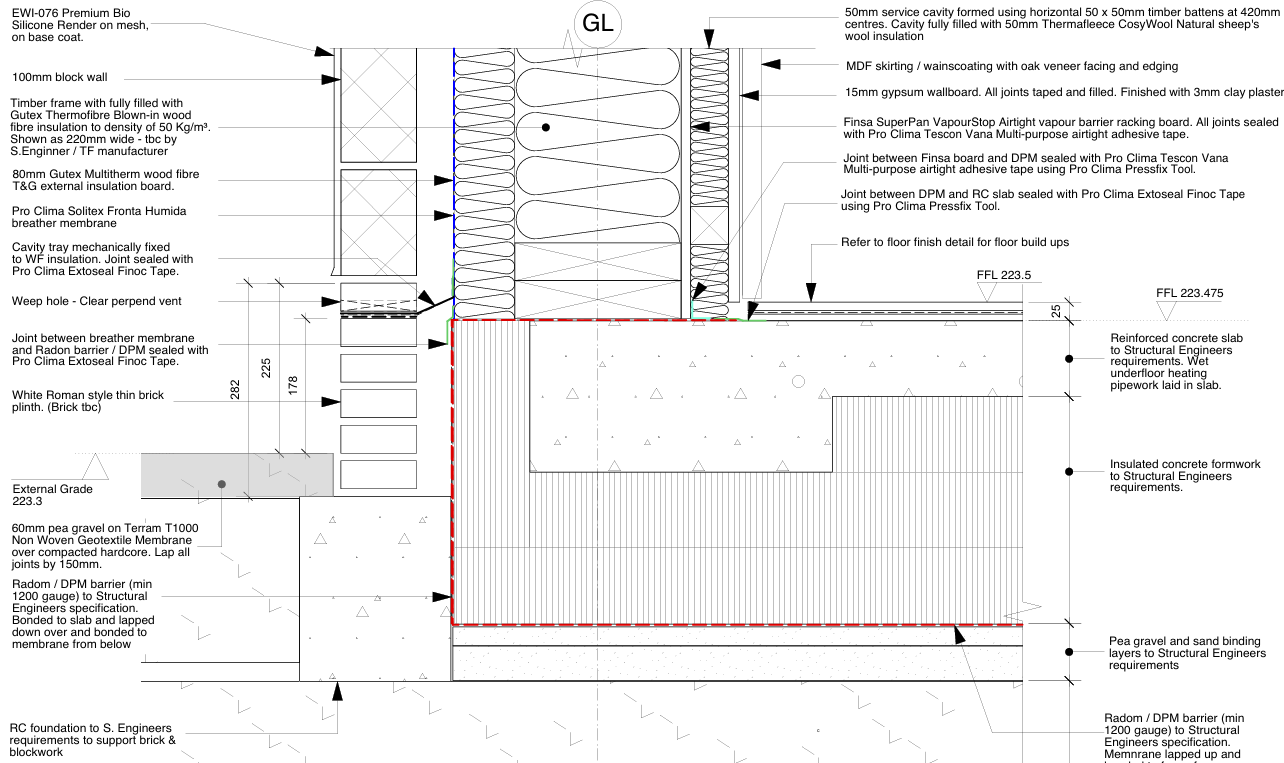
quotes/20240131_LongLifeStructures/Insulated Foundation timberframe connection.png
