ned14/HouseBuild/quotes/20240131_LongLifeStructures/Window Head Detail.png

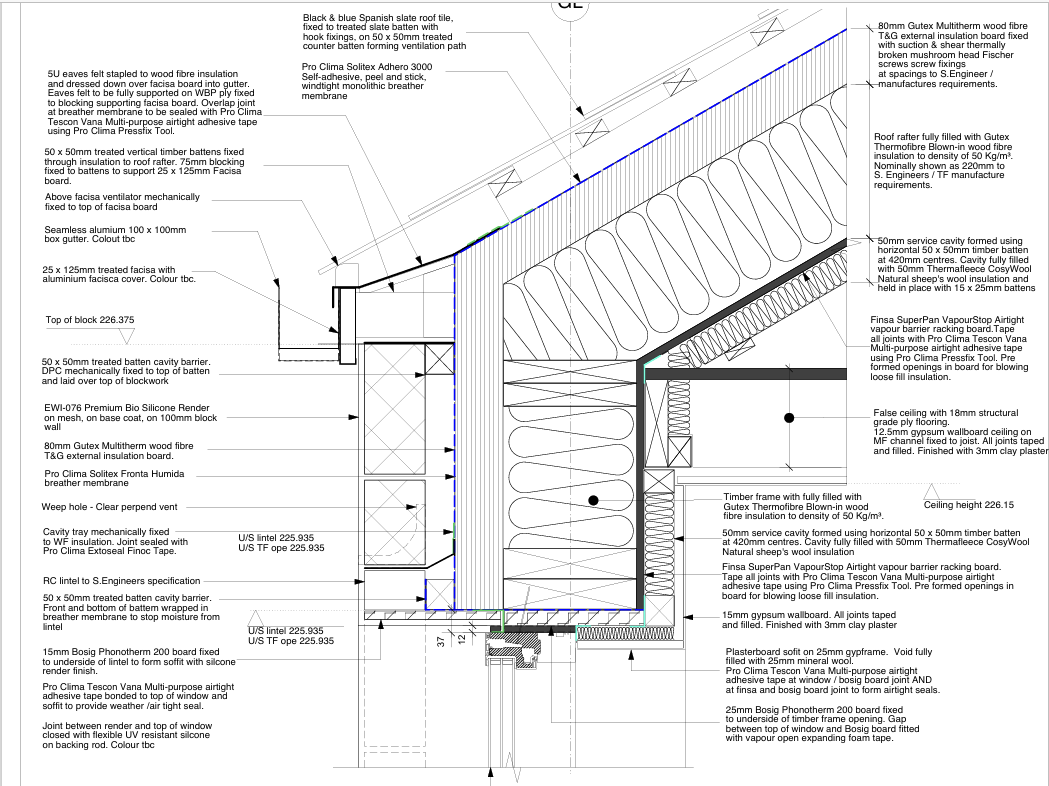
quotes/20240131_LongLifeStructures/Window Head Detail.png
