ned14/HouseBuild/quotes/20240131_LongLifeStructures/Window Jamb & Sill detail Timber Rainscreen detail.png

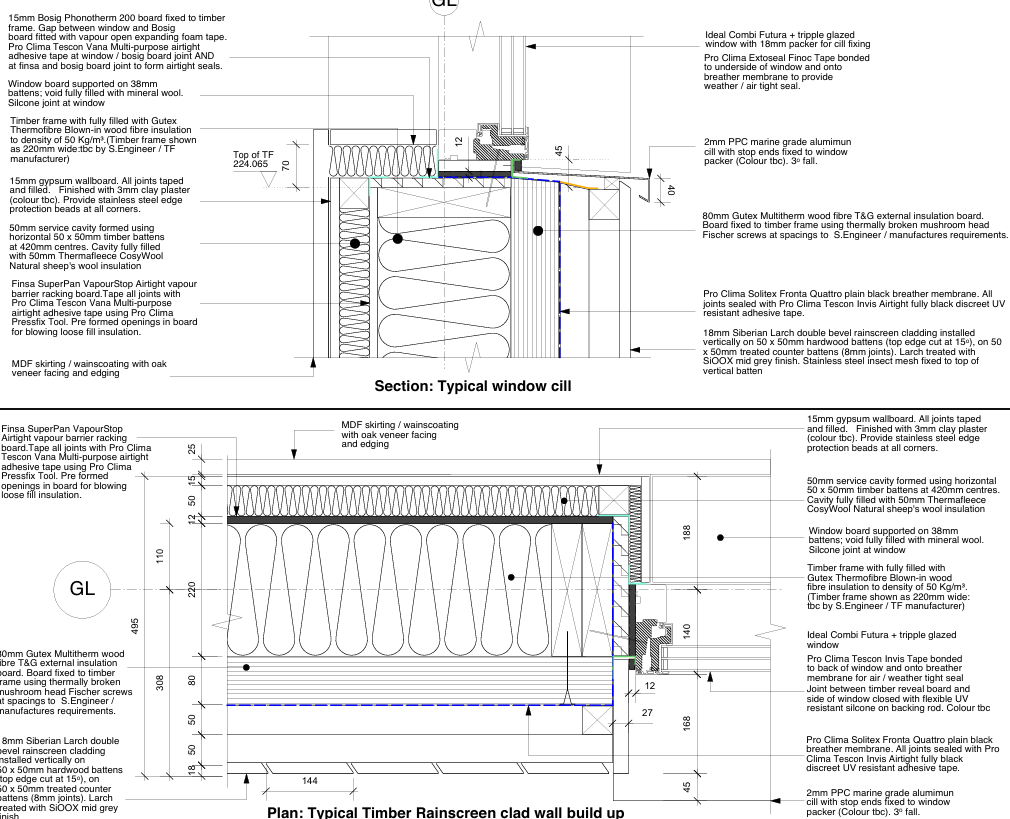
quotes/20240131_LongLifeStructures/Window Jamb & Sill detail Timber Rainscreen detail.png
