ned14/HouseBuild/quotes/20240131_LongLifeStructures/Window sill and Jamb detail .png

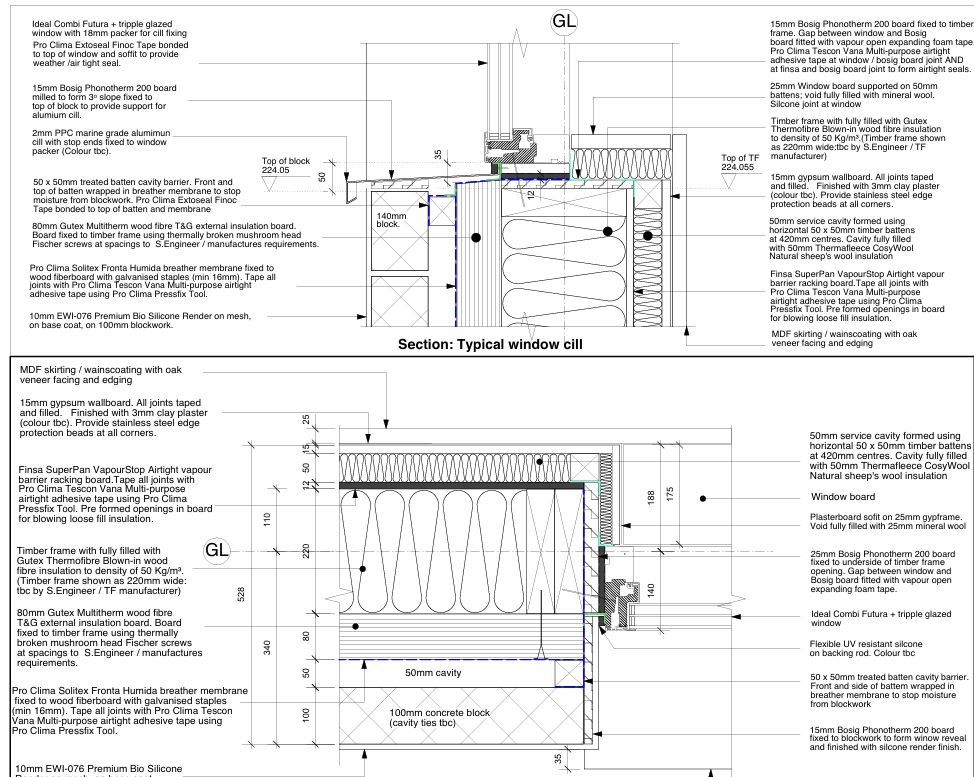
quotes/20240131_LongLifeStructures/Window sill and Jamb detail .png
