ned14/HouseBuild/surveys_maps_docs/eircom_ducting_map.png

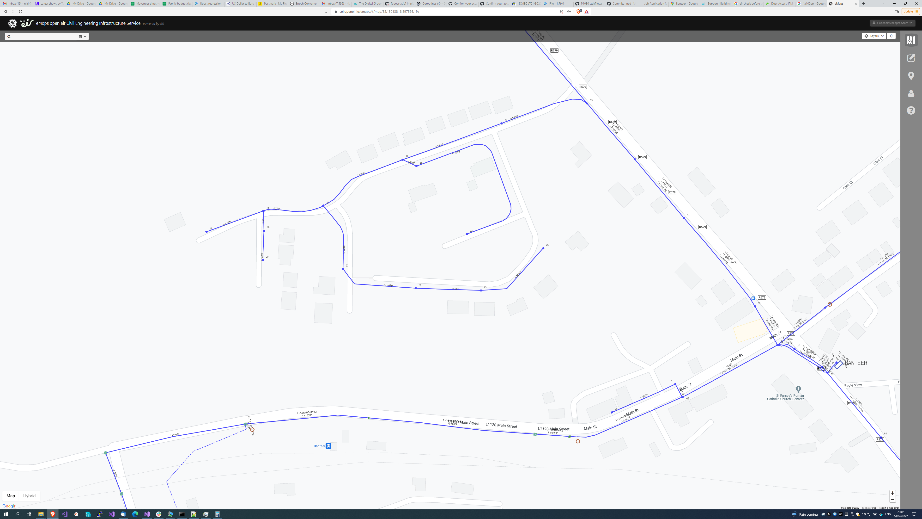
surveys_maps_docs/eircom_ducting_map.png
