ned14/HouseBuild/tech_docs/Endless Pool/Drawings.png

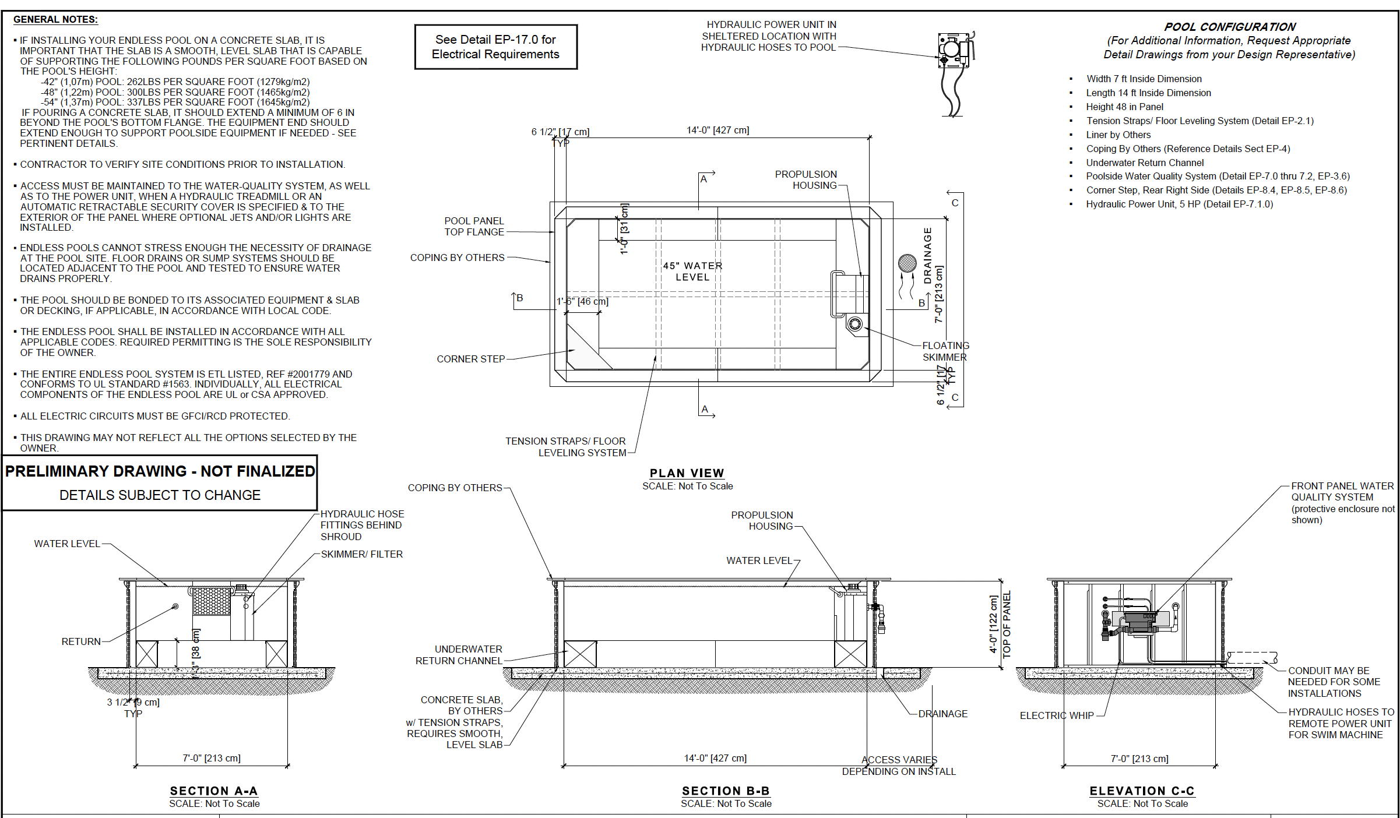
tech_docs/Endless Pool/Drawings.png
