ned14/HouseBuild/tech_docs/Greenhouse/Base profile section.JPG

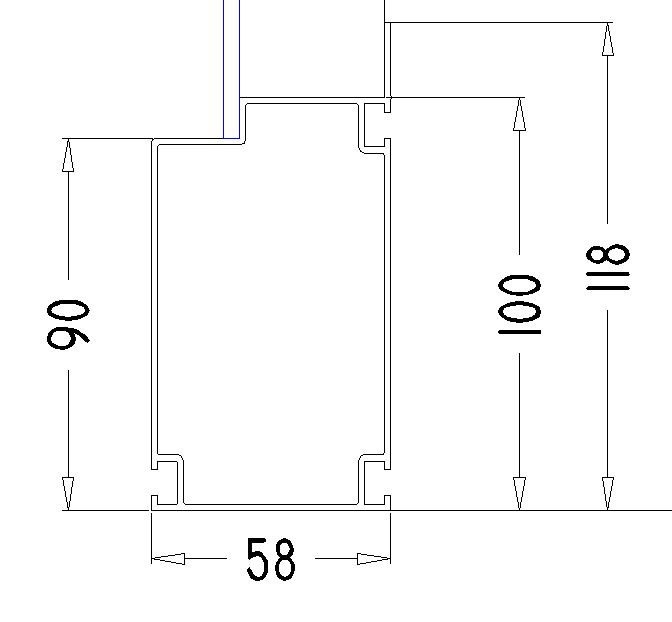
tech_docs/Greenhouse/Base profile section.JPG
