ned14/HouseBuild/tech_docs/Greenhouse/fixings.jpg

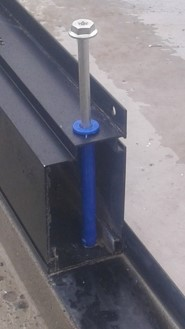
tech_docs/Greenhouse/fixings.jpg
