ned14/HouseBuild/designs/DC Wiring/20240121_house_dc_wiring.pdf

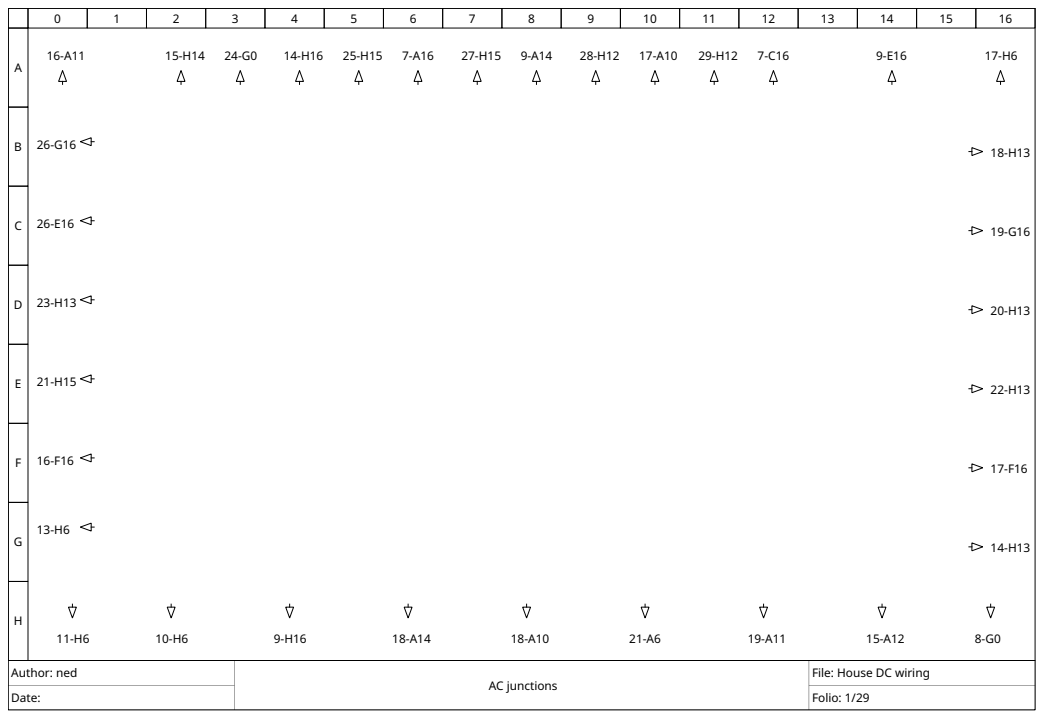
[picture p259: page 1]

Author: ned | AC junctions | File: House DC wiring
Date: | | Folio: 1/29

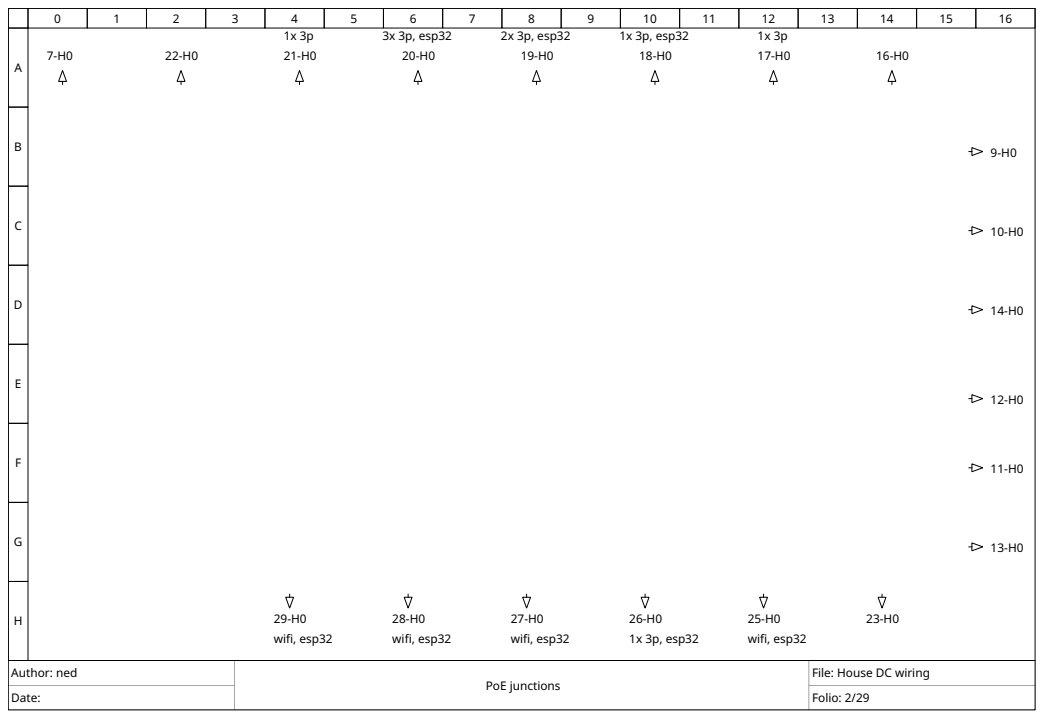
[picture p260: page 2]
Author: ned; PoE junctions; 2x 3p, esp32; 3x 3p, esp32; 1x 3p, esp32; 25-H0 wifi, esp32; 26-H0 1x 3p, esp32; 27-H0 wifi, esp32; 28-H0 wifi, esp32; 29-H0 wifi, esp32

File: House DC wiring

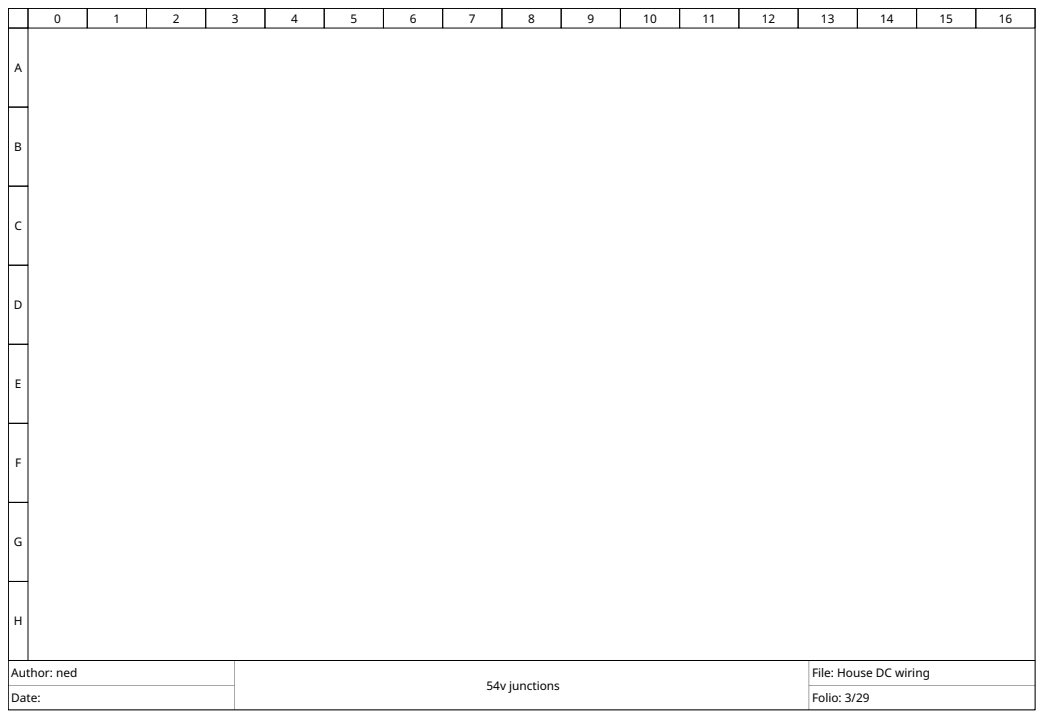
[picture p261: page 3]
Author: ned; 54v junctions

File: House DC wiring

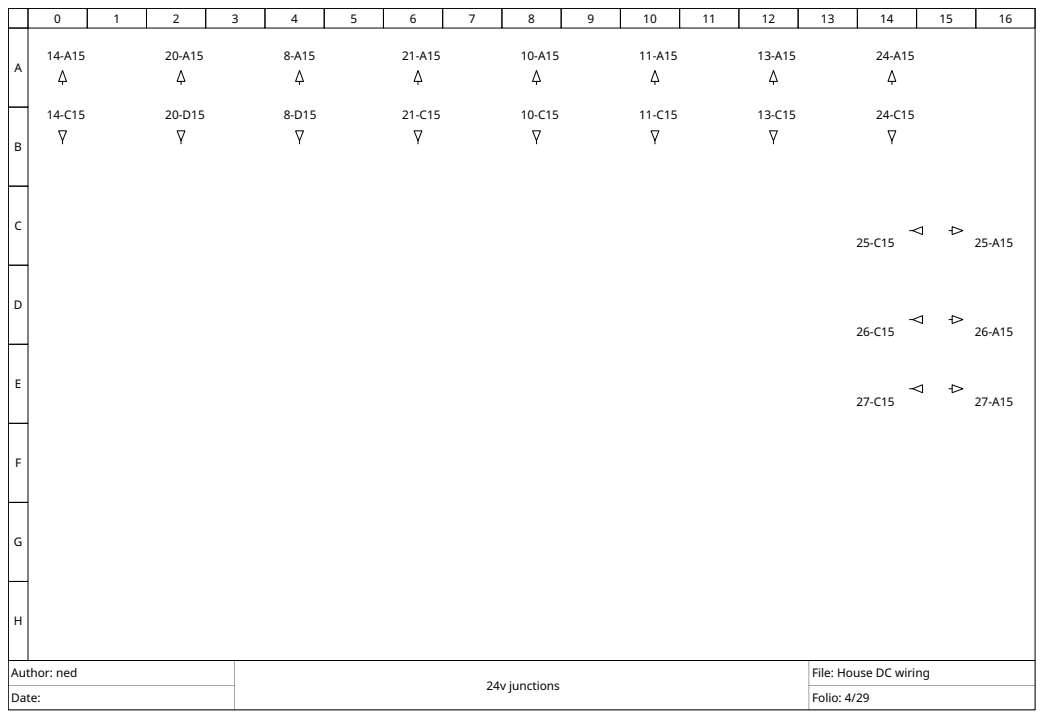
[picture p262: page 4]
Author: ned; 24v junctions

File: House DC wiring

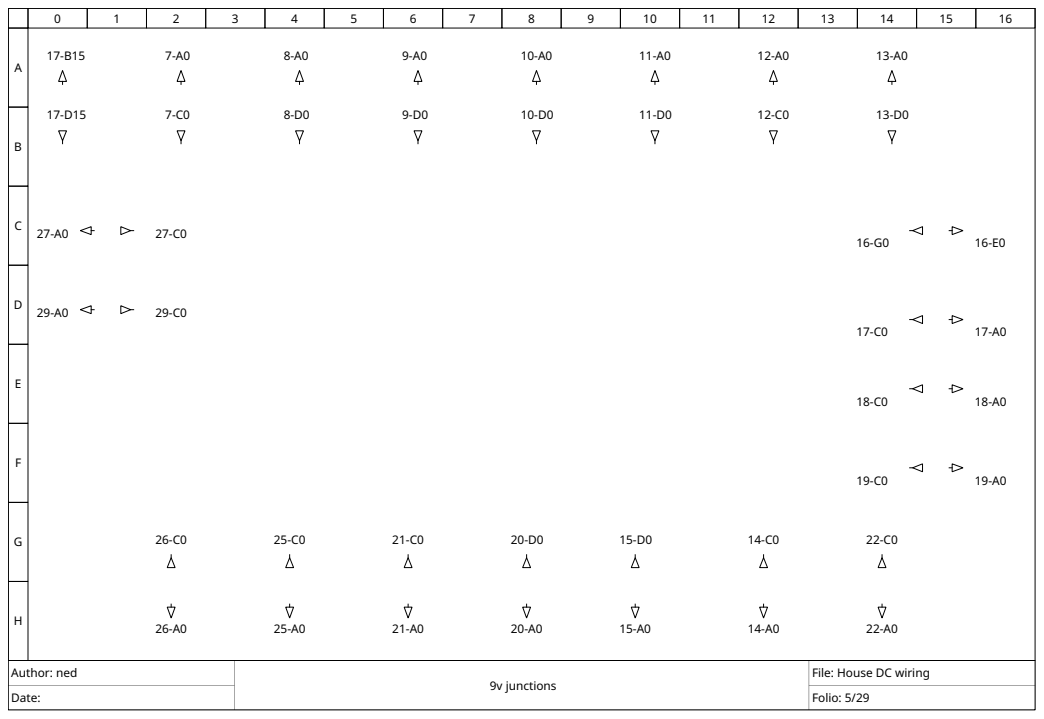
[picture p263: page 5]
Author: ned; 9v junctions

File: House DC wiring

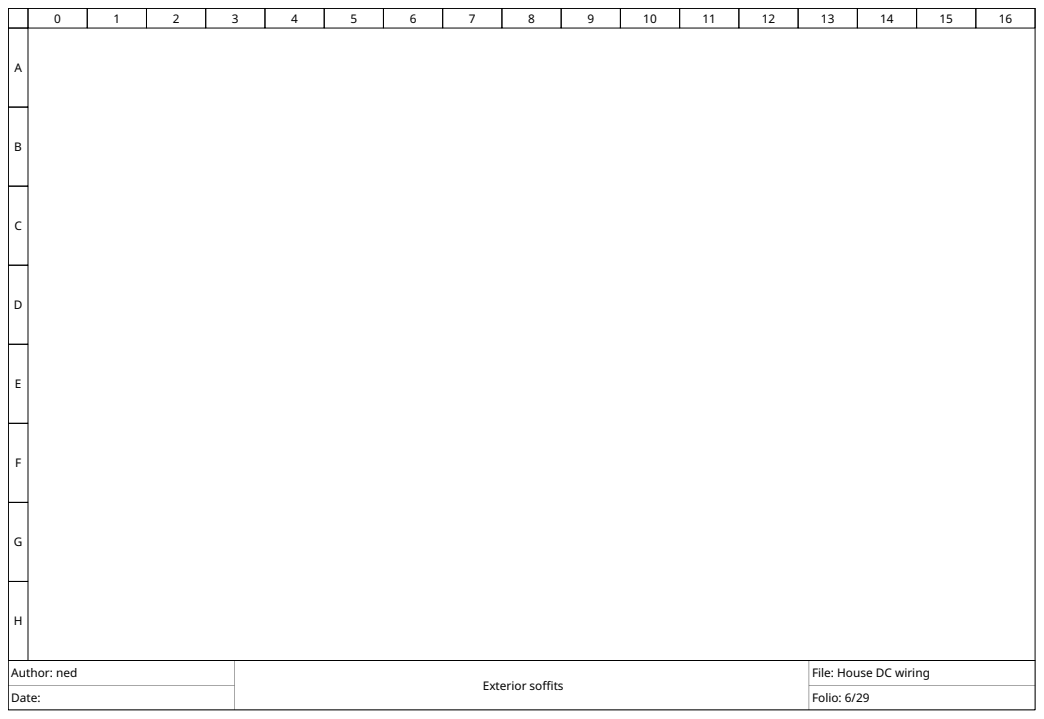
[picture p264: page 6]
Author: ned; Exterior soffits

File: House DC wiring

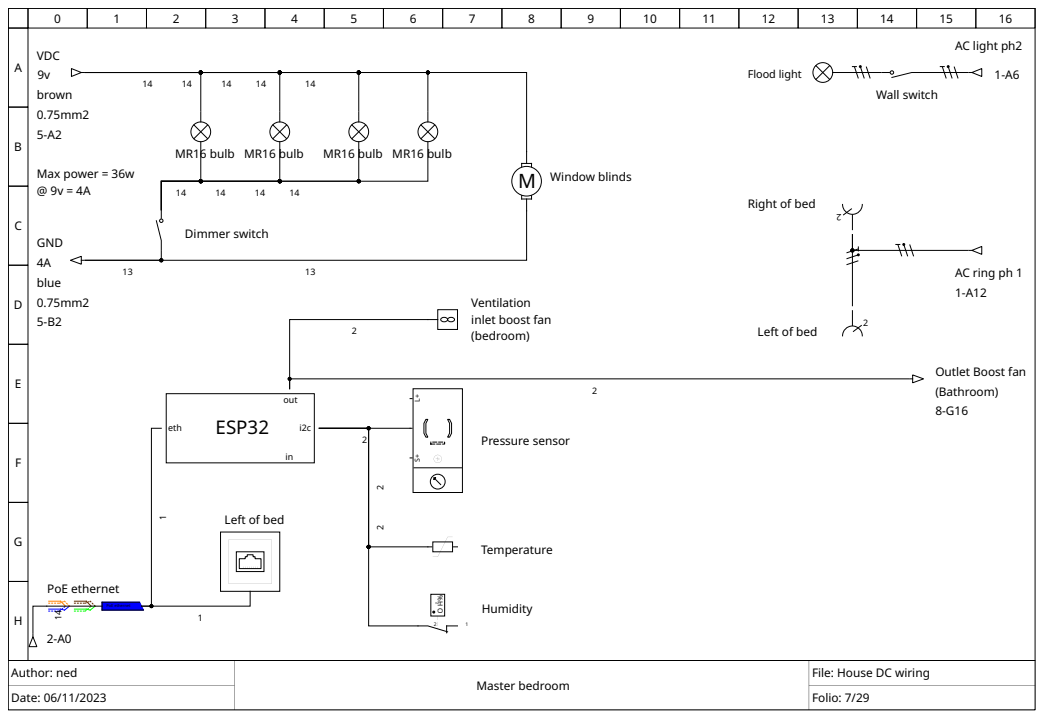
[picture p265: page 7]
MR16 bulb MR16 bulb; MR16 bulb; Pressure sensor; Outlet Boost fan (Bathroom) 8-G16; Flood light; M Window blinds; AC light ph2; PoE ethernet; Humidity; Dimmer switch; Wall switch; out; eth; ESP32 i2c; Temperature; VDC 9v brown 0.75mm2 5-A2; GND 4A blue 0.75mm2 5-B2; Max power = 36w @ 9v = 4A

Right of bed

AC ring ph 1

Ventilation
inlet boost fan
(bedroom)

Left of bed

Author: ned | Master bedroom | File: House DC wiring
Date: 06/11/2023 | | Folio: 7/29

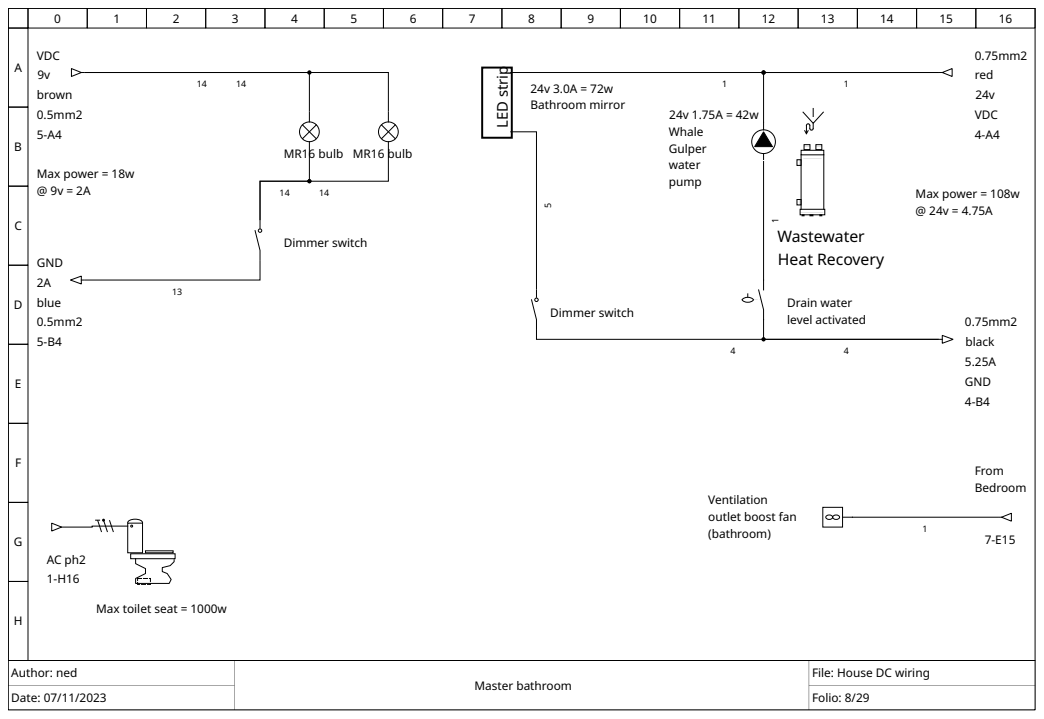
[picture p266: page 8]
MR16 bulb; GND 2A blue 0.5mm2 5-B4; Dimmer switch; Drain water level activated; 24v 1.75A = 42w Whale Gulper water pump; VDC 9v brown 0.5mm2 5-A4; From Bedroom; Wastewater Heat Recovery; D strip; VDC; red; GND; black; Max power = 18w @ 9v = 2A; 24v 3.0A = 72w Bathroom mirror; Max power = 108w @ 24v = 4.75A

Ventilation
outlet boost fan
(bathroom)

Max toilet seat = 1000w

Author: ned | Master bathroom | File: House DC wiring
Date: 07/11/2023 | | Folio: 8/29

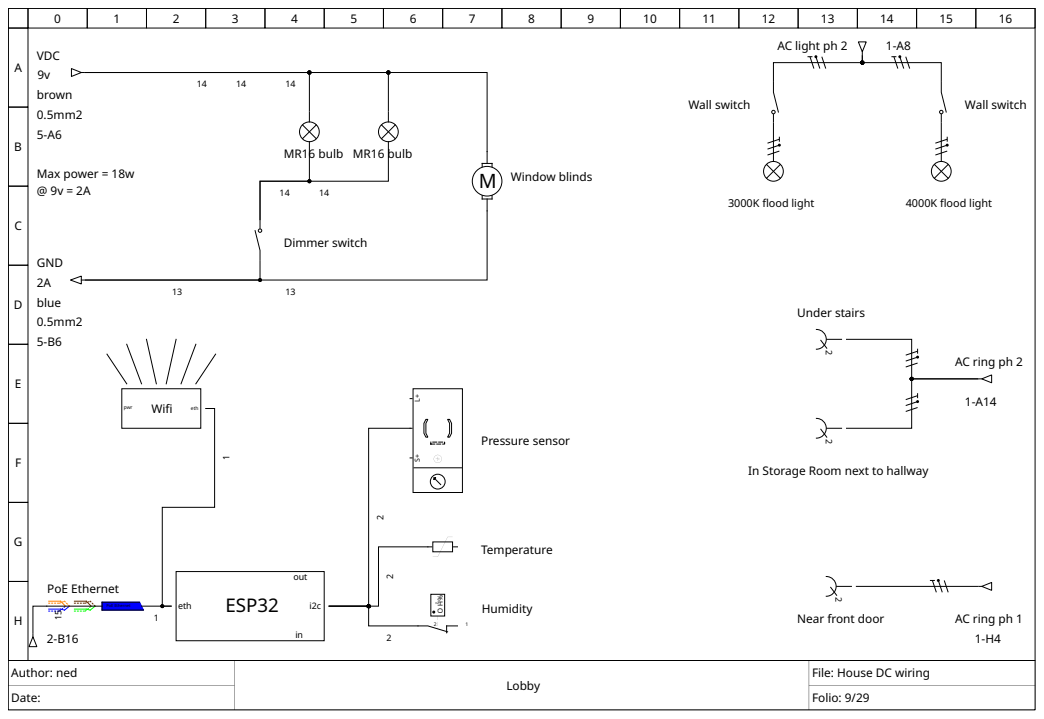
[picture p267: page 9]
Author: ned; Lobby; Dimmer switch; VDC 9v brown 0.5mm2 5-A6; Wifi; pwr; eth; M Window blinds; GND 2A blue 0.5mm2 5-B6; out; ESP32 i2c; Under stairs; Temperature; Wall switch; 4000K flood light; Humidity; 3000K flood light; Pressure sensor; PoE Ethernet; MR16 bulb MR16 bulb; AC light ph 2; Max power = 18w @ 9v = 2A

AC ring ph 2

In Storage Room next to hallway

Near front door

AC ring ph 1

File: House DC wiring

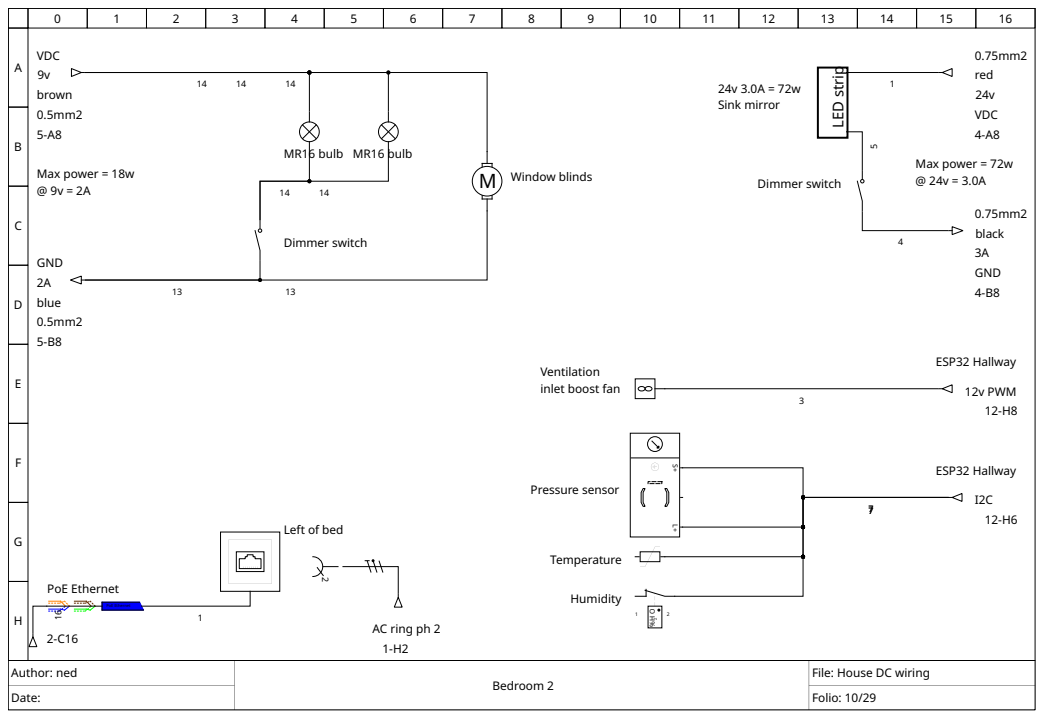
[picture p268: page 10]
Author: ned; Bedroom 2; Temperature; MR16 bulb; M Window blinds; VDC 9v brown 0.5mm2 5-A8; Pressure sensor; PoE Ethernet; Humidity; GND 2A blue 0.5mm2 5-B8; Dimmer switch; ESP32 Hallway; 12v PWM; Max power = 18w @ 9v = 2A; GND; black; VDC; red; D strip; Max power = 72w @ 24v = 3.0A; 24v 3.0A = 72w Sink mirror

Ventilation
inlet boost fan

Left of bed

AC ring ph 2

File: House DC wiring

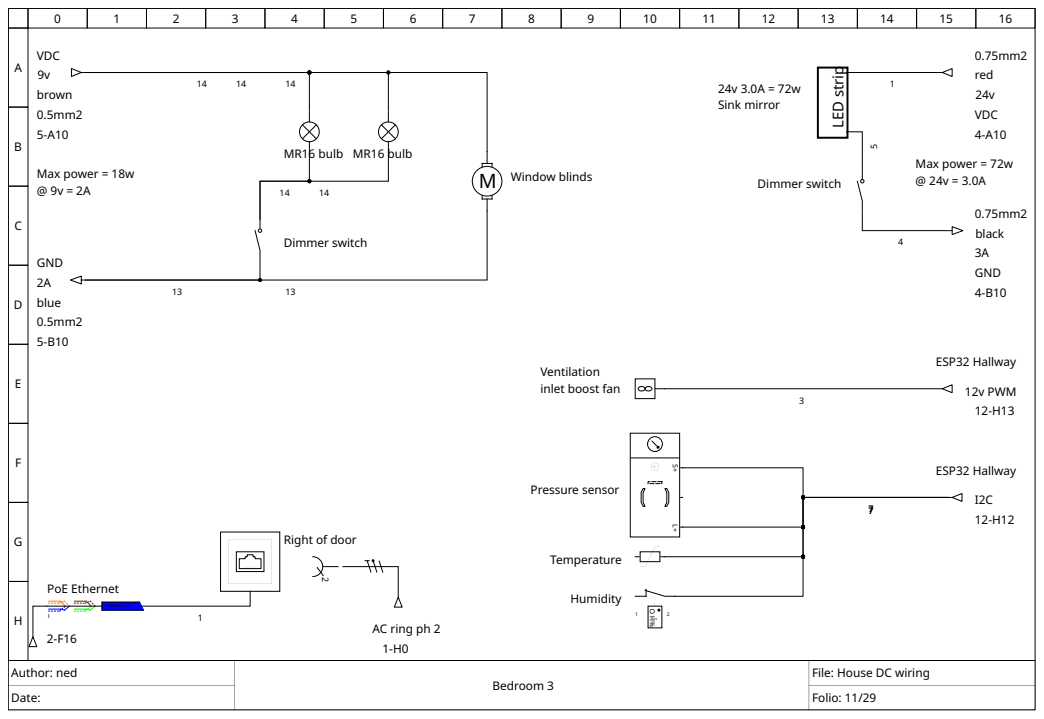
[picture p269: page 11]
Author: ned; Bedroom 3; Dimmer switch; MR16 bulb MR16 bulb; M Window blinds; VDC 9v brown 0.5mm2 5-A10; Pressure sensor; Humidity; Temperature; GND 2A blue 0.5mm2 5-B10; PoE Ethernet; ESP32 Hallway; 12v PWM; Max power = 18w @ 9v = 2A; GND; black; VDC; red; D strip; Max power = 72w @ 24v = 3.0A; 24v 3.0A = 72w Sink mirror

Ventilation
inlet boost fan

Right of door

AC ring ph 2

File: House DC wiring

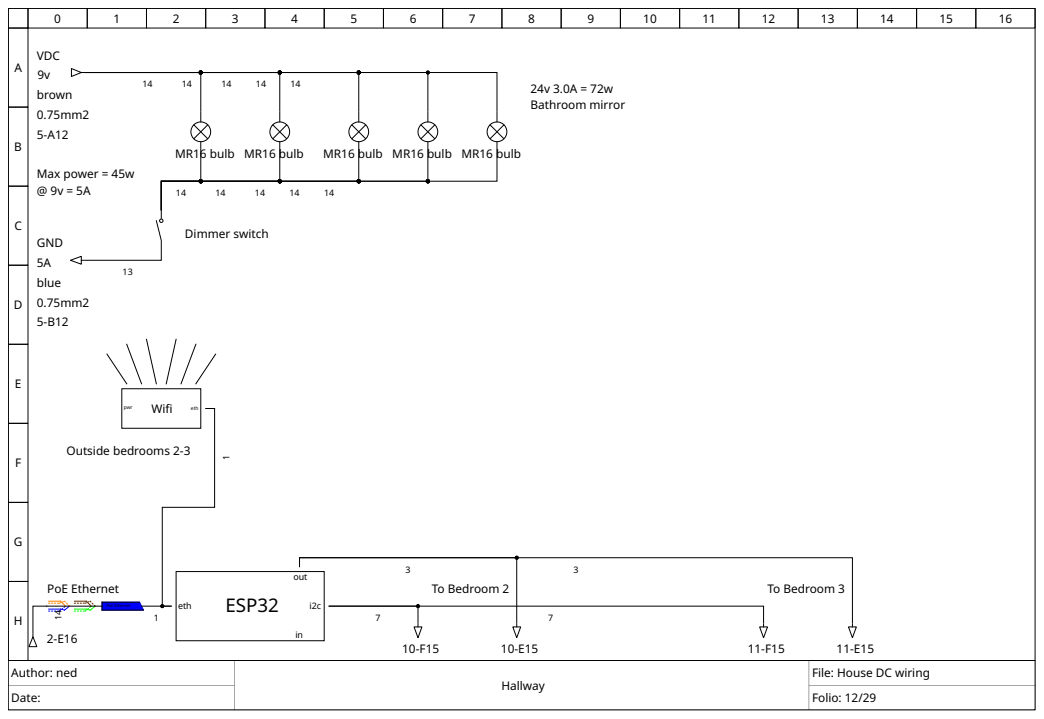
[picture p270: page 12]
Author: ned; Hallway; MR16 bulb; Wifi; pwr; eth; Outside bedrooms 2-3; To Bedroom 3; MR16 bulb MR16 bulb; PoE Ethernet; Dimmer switch; out; ESP32 i2c; GND 5A blue 0.75mm2 5-B12; To Bedroom 2; VDC 9v brown 0.75mm2 5-A12; Max power = 45w @ 9v = 5A; 24v 3.0A = 72w Bathroom mirror

File: House DC wiring

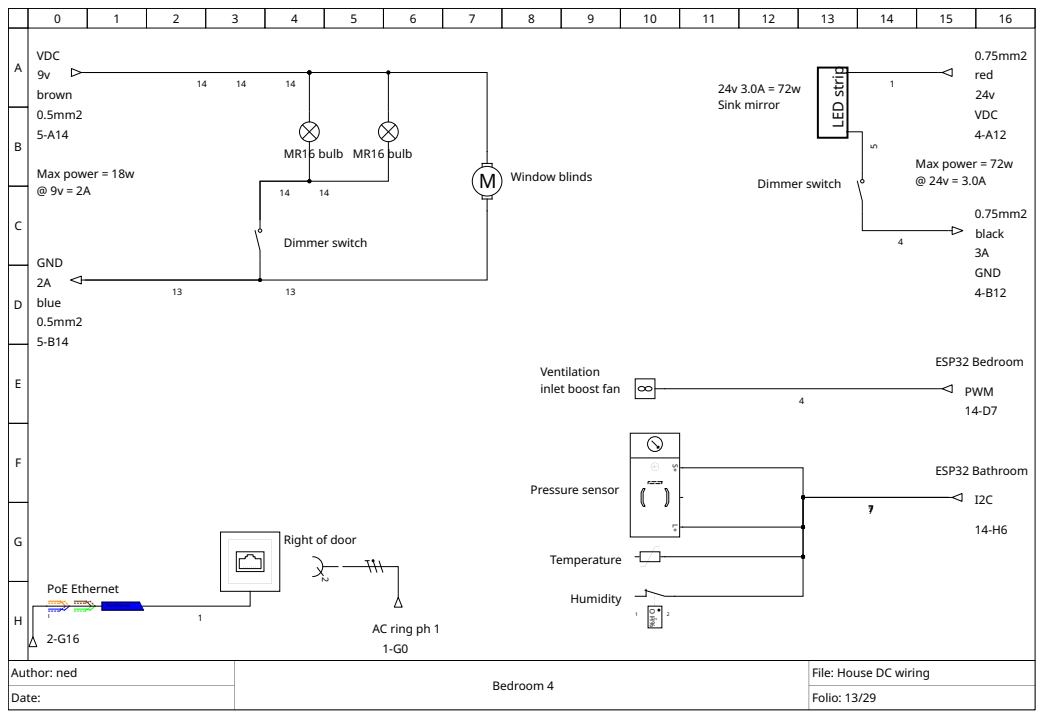
[picture p271: page 13]
Author: ned; Bedroom 4; MR16 bulb MR16 bulb; Dimmer switch; VDC 9v brown 0.5mm2 5-A14; Humidity; GND 2A blue 0.5mm2 5-B14; Temperature; PoE Ethernet; Pressure sensor; M Window blinds; ESP32 Bathroom; ESP32 Bedroom; PWM; Max power = 18w @ 9v = 2A; VDC; red; D strip; GND; black; Max power = 72w @ 24v = 3.0A; 24v 3.0A = 72w Sink mirror

Ventilation
inlet boost fan

Right of door

AC ring ph 1

File: House DC wiring

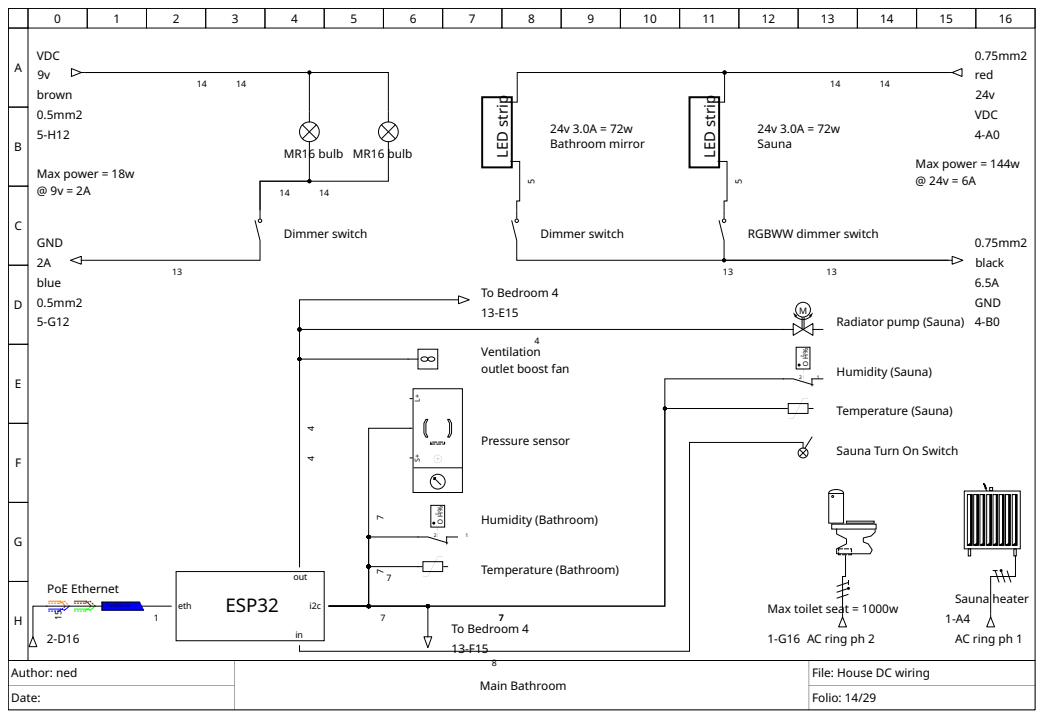
[picture p272: page 14]
Author: ned; Main Bathroom; MR16 bulb MR16 bulb; VDC 9v brown 0.5mm2 5-H12; Humidity (Sauna); GND 2A blue 0.5mm2 5-G12; Temperature (Sauna); To Bedroom 4; Humidity (Bathroom); D strip; Temperature (Bathroom); PoE Ethernet; out; eth; ESP32 i2c; Pressure sensor; GND; black; Dimmer switch; VDC; red; Max power = 144w @ 24v = 6A; 24v 3.0A = 72w Sauna; 24v 3.0A = 72w Bathroom mirror; Max power = 18w @ 9v = 2A

RGBWW dimmer switch

Radiator pump (Sauna)

Ventilation
outlet boost fan

Sauna Turn On Switch

Sauna heater
AC ring ph 1

Max toilet seat = 1000w
1-G16 AC ring ph 2

File: House DC wiring

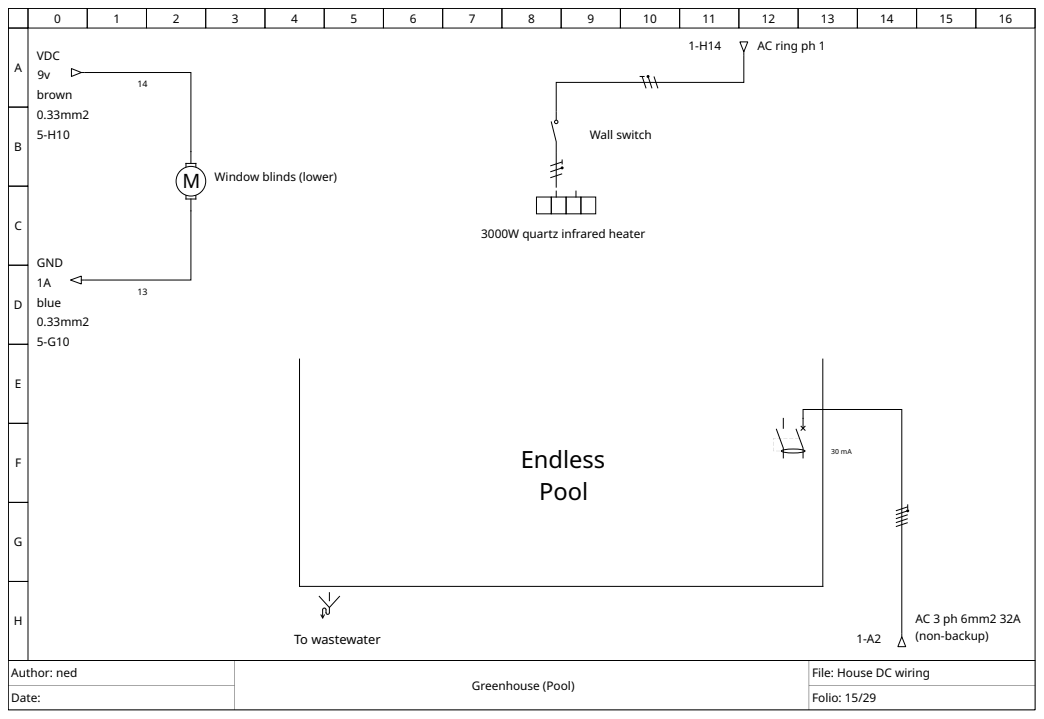
[picture p273: page 15]
Author: ned; Greenhouse (Pool); To wastewater; Wall switch; VDC 9v brown 0.33mm2 5-H10; AC ring ph 1; GND 1A blue 0.33mm2 5-G10; (non-backup) -A2; Endless Pool

M Window blinds (lower)

3000W quartz infrared heater

File: House DC wiring

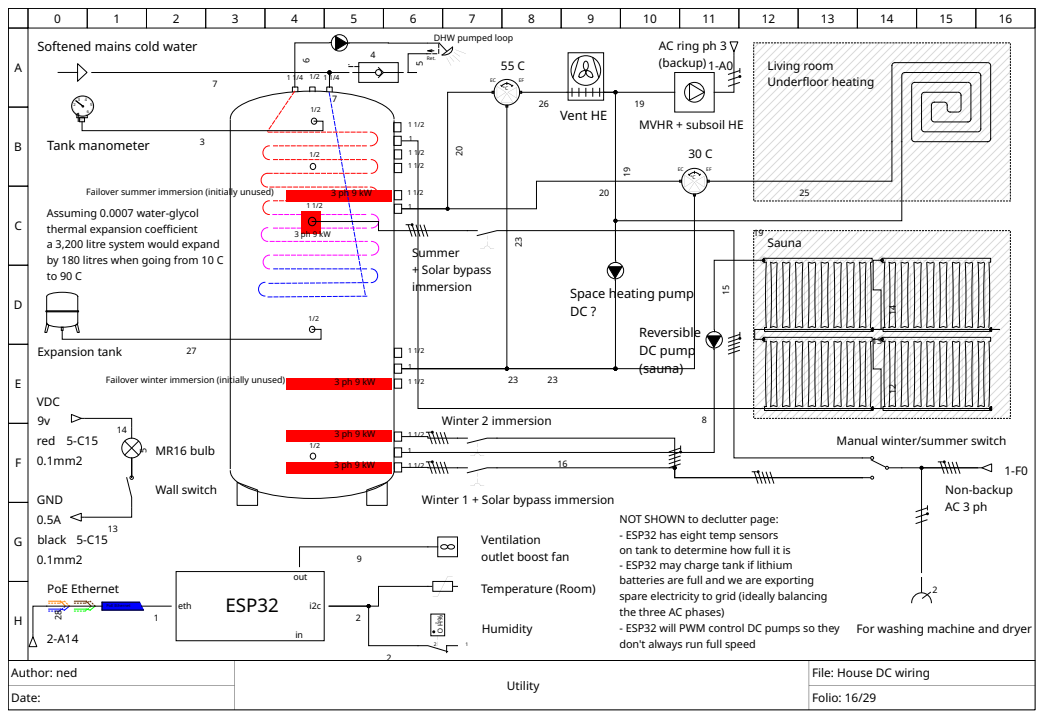
[picture p274: page 16]
Author: ned; Utility; Ret.; Winter 2 immersion; Tank manometer; VDC 9v red 0.1mm2; GND 0.5A black 0.1mm2; Vent HE; Expansion tank; Reversible DC pump (sauna); Humidity; Summer + Solar bypass immersion; out; eth; ESP32 i2c; MR16 bulb; PoE Ethernet; Temperature (Room); Wall switch; Non-backup AC 3 ph; Living room Underfloor heating; Sauna

Softened mains cold water

DHW pumped loop

AC ring ph 3
(backup) 1-A0

MVHR + subsoil HE

Failover summer immersion (initially unused)
Assuming 0.0007 water-glycol
thermal expansion coefficient
a 3,200 litre system would expand
by 180 litres when going from 10 C

Space heating pump

Failover winter immersion (initially unused)

Manual winter/summer switch

Winter 1 + Solar bypass immersion

NOT SHOWN to declutter page:
- ESP32 has eight temp sensors
on tank to determine how full it is
- ESP32 may charge tank if lithium
batteries are full and we are exporting
spare electricity to grid (ideally balancing
the three AC phases)
- ESP32 will PWM control DC pumps so they
don't always run full speed

Ventilation
outlet boost fan

For washing machine and dryer

File: House DC wiring

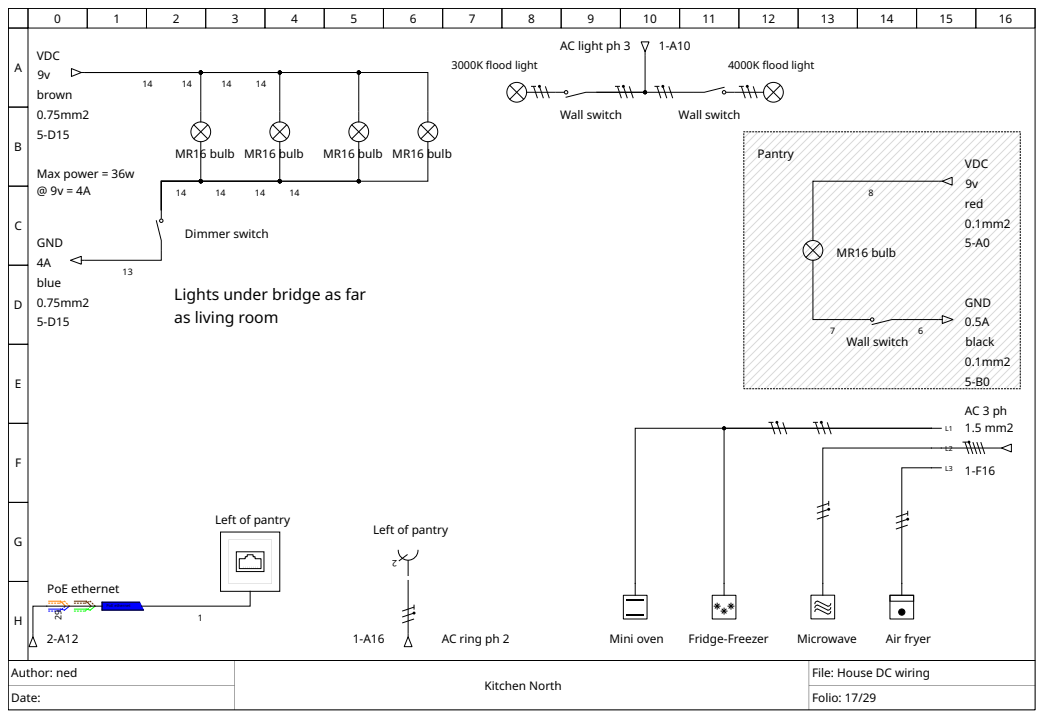
[picture p275: page 17]
Author: ned; Kitchen North; Microwave; Air fryer; MR16 bulb; VDC 9v brown 0.75mm2 5-D15; Mini oven; GND 4A blue 0.75mm2 5-D15; Dimmer switch; Wall switch; Fridge-Freezer; 3000K flood light; 4000K flood light; GND 0.5A black 0.1mm2 5-B0; VDC 9v red 0.1mm2 5-A0; PoE ethernet; AC ring ph 2; AC light ph 3; Max power = 36w @ 9v = 4A; Pantry

Lights under bridge as far
as living room

Left of pantry

File: House DC wiring

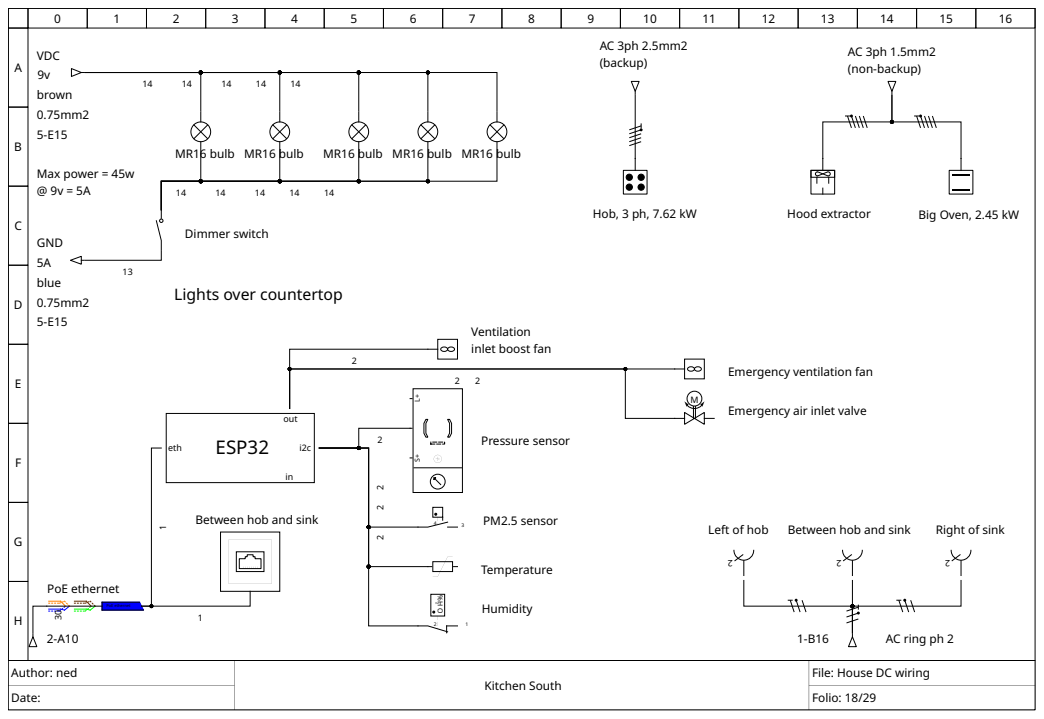
[picture p276: page 18]
Author: ned; Kitchen South; MR16 bulb MR16 bulb; MR16 bulb; Dimmer switch; AC ring ph 2; Humidity; PoE ethernet; Temperature; AC 3ph 2.5mm2 (backup); GND 5A blue 0.75mm2 5-E15; AC 3ph 1.5mm2 (non-backup); Pressure sensor; Hood extractor; VDC 9v brown 0.75mm2 5-E15; out; eth; ESP32 i2c; PM2.5 sensor; Max power = 45w @ 9v = 5A

Hob, 3 ph, 7.62 kW

Big Oven, 2.45 kW

Lights over countertop

Ventilation
inlet boost fan

Emergency ventilation fan

Emergency air inlet valve

Between hob and sink

Left of hob

Right of sink

File: House DC wiring

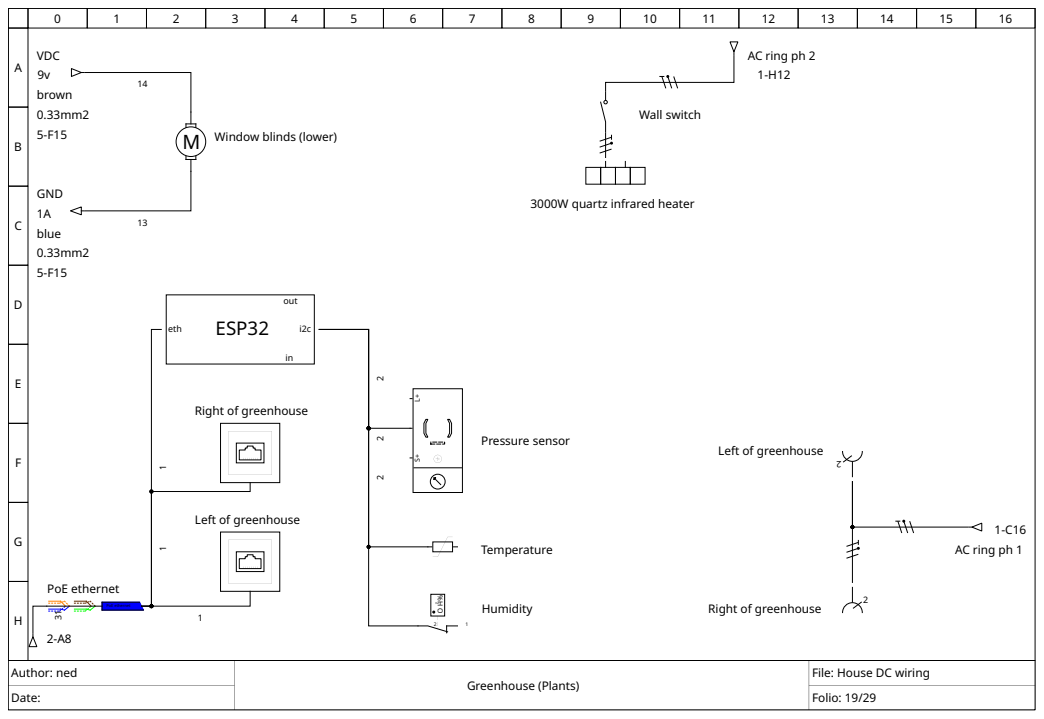
[picture p277: page 19]
Author: ned; Greenhouse (Plants); PoE ethernet; Humidity; VDC 9v brown 0.33mm2 5-F15; Wall switch; Pressure sensor; Temperature; out; eth; ESP32 i2c; GND 1A blue 0.33mm2 5-F15

AC ring ph 2

M Window blinds (lower)

3000W quartz infrared heater

Right of greenhouse

Left of greenhouse

AC ring ph 1

File: House DC wiring

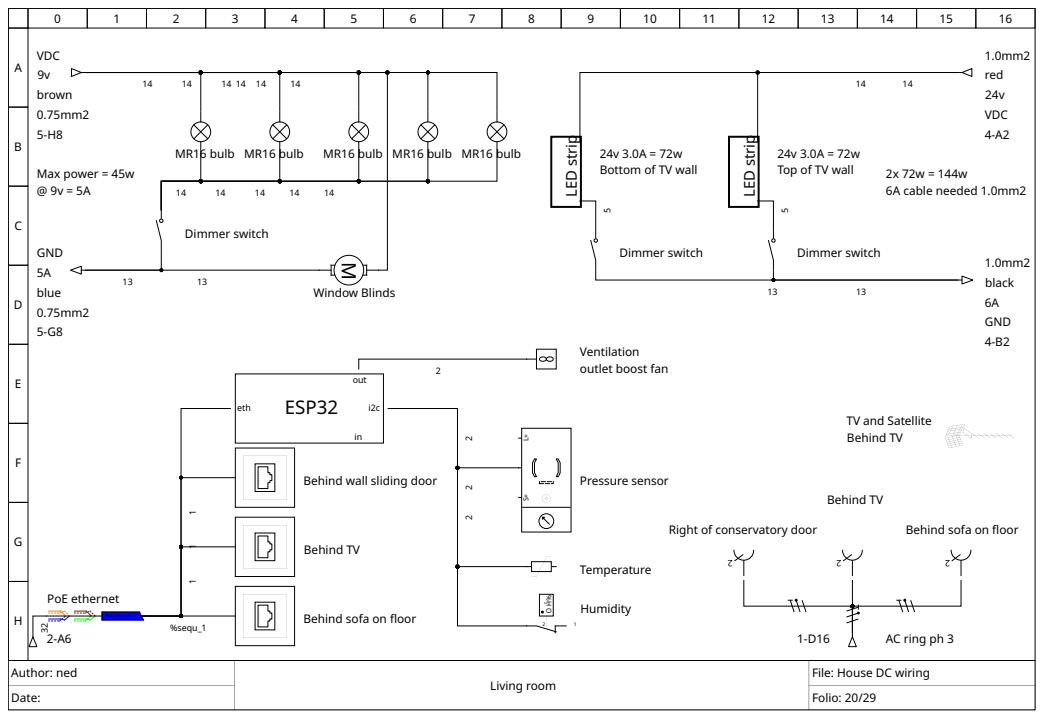
[picture p278: page 20]
Author: ned; Living room; MR16 bulb; MR16 bulb MR16 bulb MR16 bulb; Dimmer switch; Behind TV; VDC 9v brown 0.75mm2 5-H8; PoE ethernet; AC ring ph 3; VDC; red; GND; black; out; eth; ESP32 i2c; Humidity; Temperature; Pressure sensor; GND 5A blue 0.75mm2 5-G8; Max power = 45w @ 9v = 5A; 2x 72w = 144w 6A cable needed 1.0mm2; M Window Blinds; %sequ_1

D strip
Bottom of TV wall

Top of TV wall

Ventilation
outlet boost fan

TV and Satellite
Behind TV

Behind wall sliding door

Right of conservatory door

Behind sofa on floor

File: House DC wiring

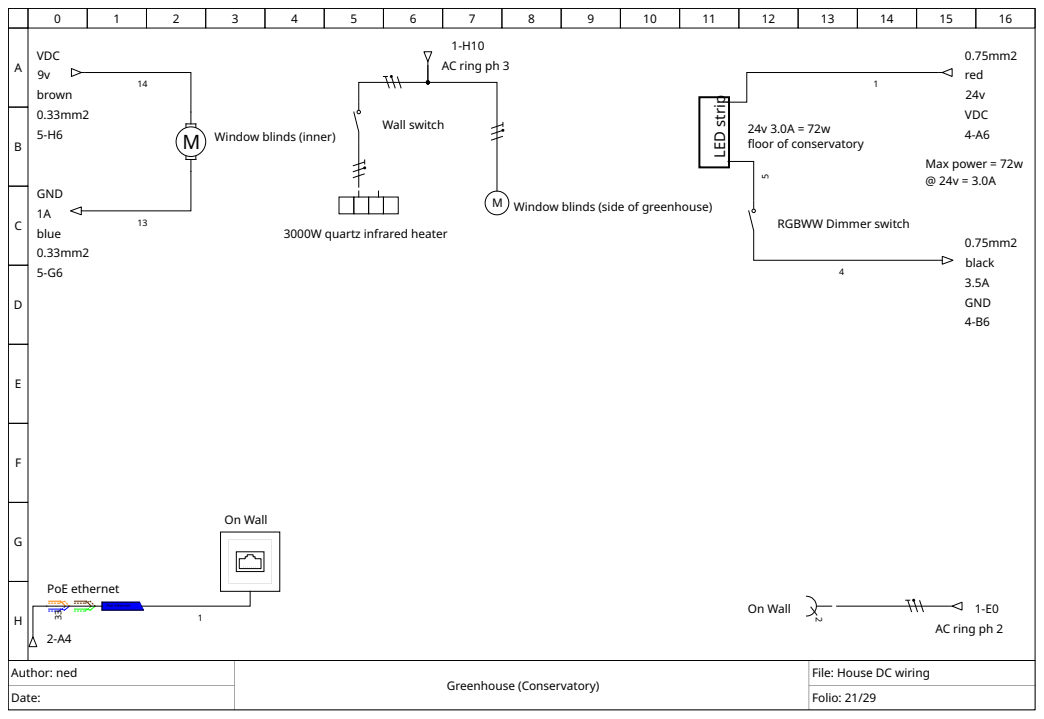
[picture p279: page 21]
Author: ned; Greenhouse (Conservatory); n Wall; On Wall; VDC 9v brown 0.33mm2 5-H6; GND; black; PoE ethernet; VDC; red; D strip; Wall switch; GND 1A blue 0.33mm2 5-G6; 24v 3.0A = 72w floor of conservatory; Max power = 72w @ 24v = 3.0A

AC ring ph 3

M Window blinds (inner)

M Window blinds (side of greenhouse)

RGBWW Dimmer switch

3000W quartz infrared heater

AC ring ph 2

File: House DC wiring

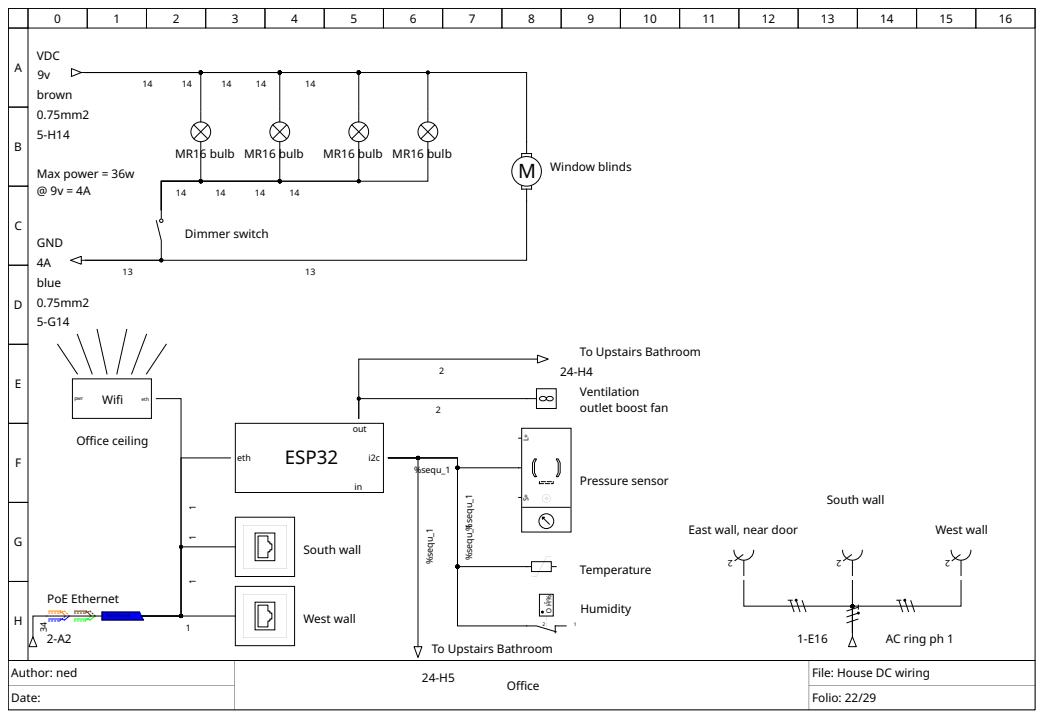
[picture p280: page 22]
Author: ned; Office; MR16 bulb MR16 bulb; MR16 bulb; Wifi; pwr; eth; Office ceiling; Dimmer switch; GND 4A blue 0.75mm2 5-G14; Humidity We; 2 st wall; out; ESP32 i2c; Temperature; Pressure sensor; VDC 9v brown 0.75mm2 5-H14; PoE Ethernet; South wall; AC ring ph 1; West wall; Max power = 36w @ 9v = 4A; M Window blinds; %sequ_1

To Upstairs Bathroom
Ventilation
outlet boost fan

East wall, near door

File: House DC wiring

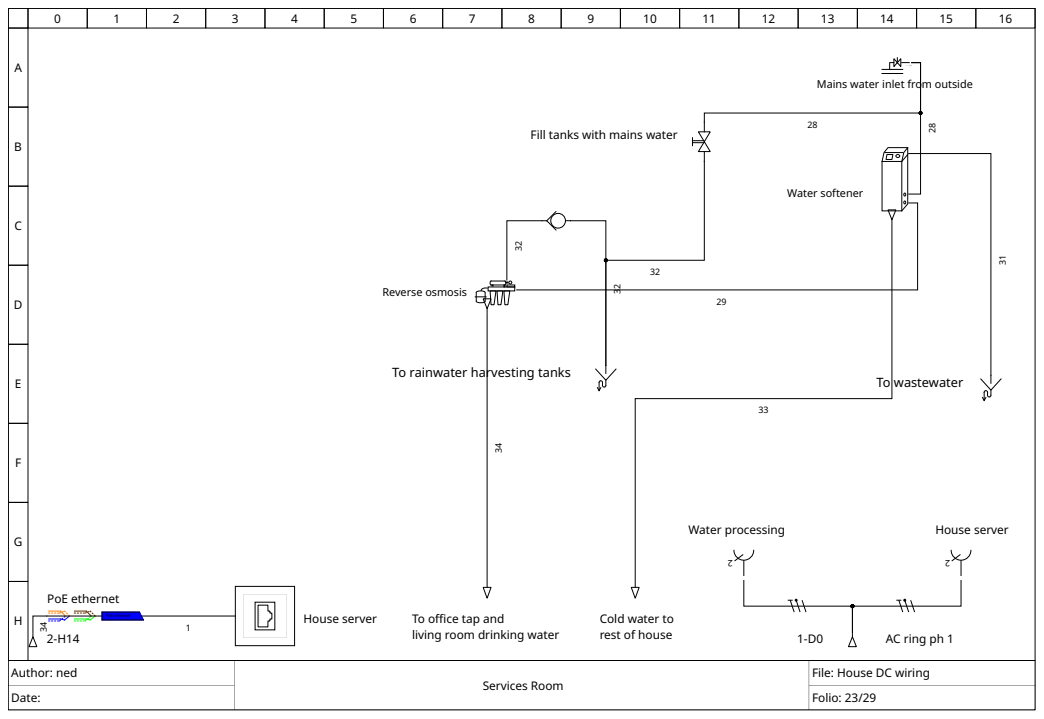
[picture p281: page 23]
Author: ned; Services Room; House server; PoE ethernet; Water processing; AC ring ph 1; To wastewater; Reverse osmosis; Water softener

Mains water inlet from outside

Fill tanks with mains water

To rainwater harvesting tanks

To office tap and
living room drinking water

Cold water to
rest of house

File: House DC wiring

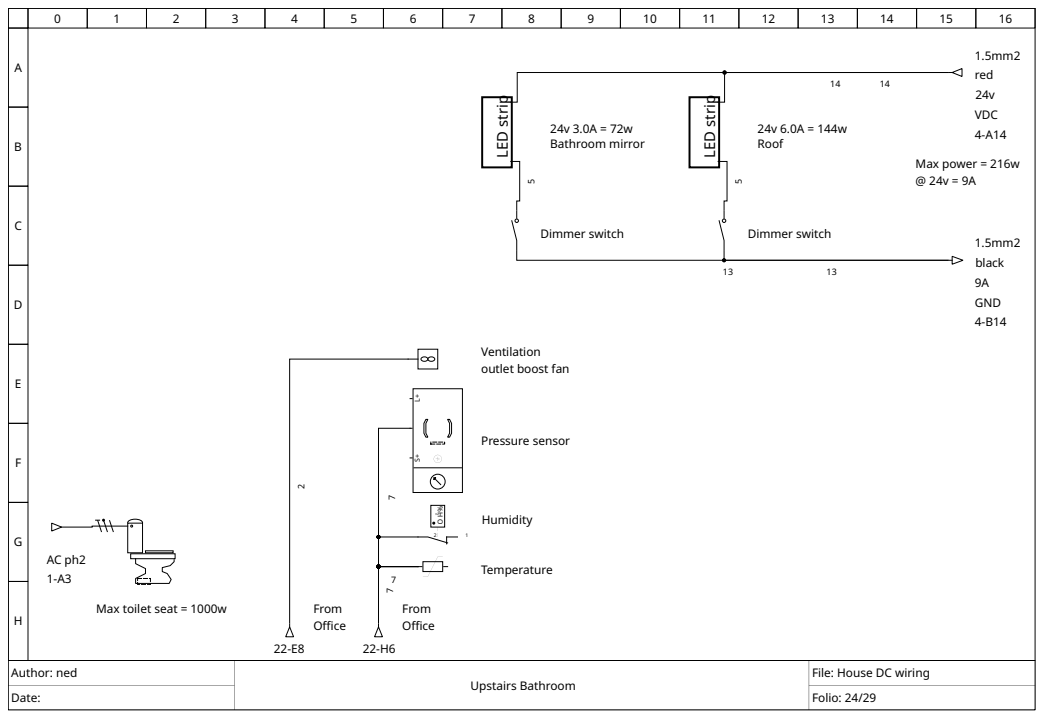
[picture p282: page 24]
Author: ned; Upstairs Bathroom; D strip; Temperature; Humidity; Pressure sensor; Dimmer switch; GND; black; VDC; red; Max power = 216w @ 24v = 9A; 24v 6.0A = 144w Roof; 24v 3.0A = 72w Bathroom mirror; From Office

Ventilation
outlet boost fan

Max toilet seat = 1000w

File: House DC wiring

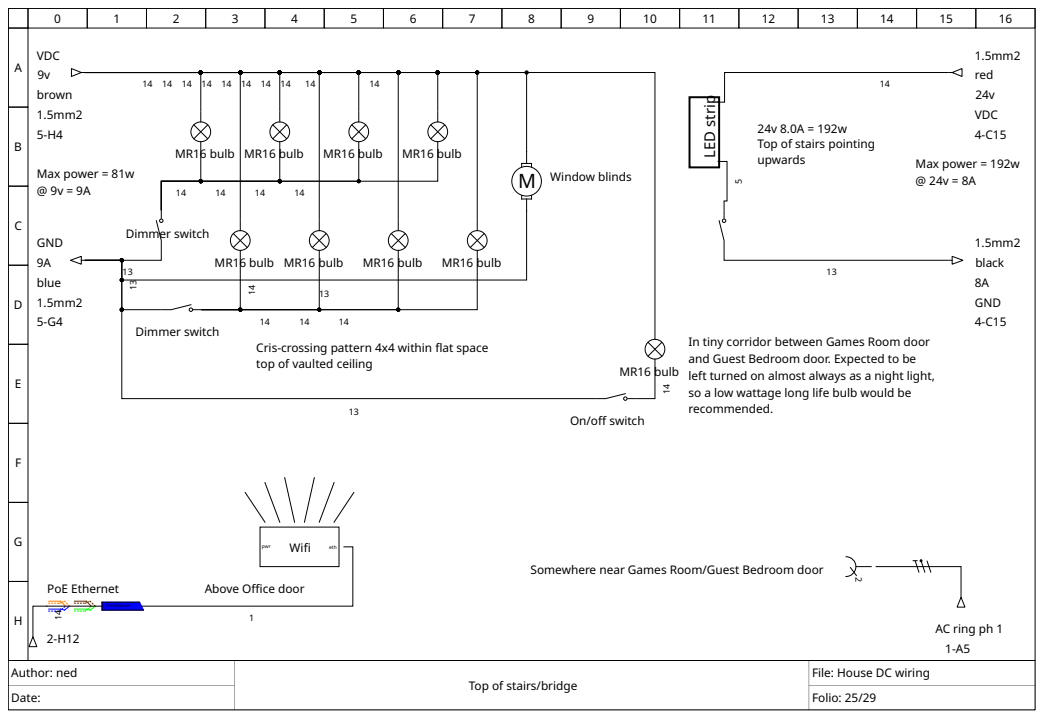
[picture p283: page 25]
Author: ned; MR16 bulb MR16 bulb; MR16 bulb; Dimmer switch; GND 9A blue 1.5mm2 5-G4; VDC 9v brown 1.5mm2 5-H4; Max power = 81w @ 9v = 9A; GND; black; VDC; red; D strip; Max power = 192w @ 24v = 8A; M Window blinds; Wifi; pwr; eth; PoE Ethernet

Top of stairs pointing
upwards

Cris-crossing pattern 4x4 within flat space
top of vaulted ceiling

In tiny corridor between Games Room door
and Guest Bedroom door. Expected to be
left turned on almost always as a night light,
so a low wattage long life bulb would be
recommended.

On/off switch

Somewhere near Games Room/Guest Bedroom door

Above Office door

AC ring ph 1

File: House DC wiring

Top of stairs/bridge

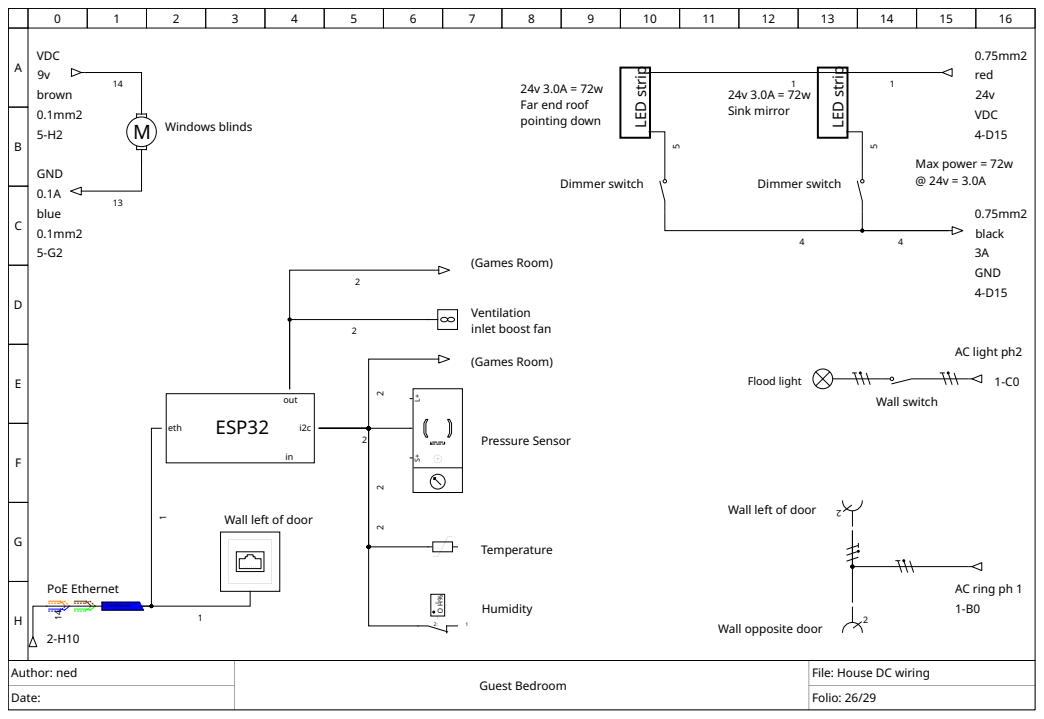
[picture p284: page 26]
Author: ned; Guest Bedroom; Pressure Sensor; 2 all left of door; M Windows blinds; Flood light; Humidity; AC light ph2; PoE Ethernet; Wall switch; out; eth; ESP32 i2c; Temperature; VDC 9v brown 0.1mm2 5-H2; GND 0.1A blue 0.1mm2 5-G2; Dimmer switch; VDC; red; GND; black; D strip; Max power = 72w @ 24v = 3.0A; 24v 3.0A = 72w Sink mirror; (Games Room)

Far end roof
pointing down

Ventilation
inlet boost fan

Wall left of door

AC ring ph 1

Wall opposite door

File: House DC wiring

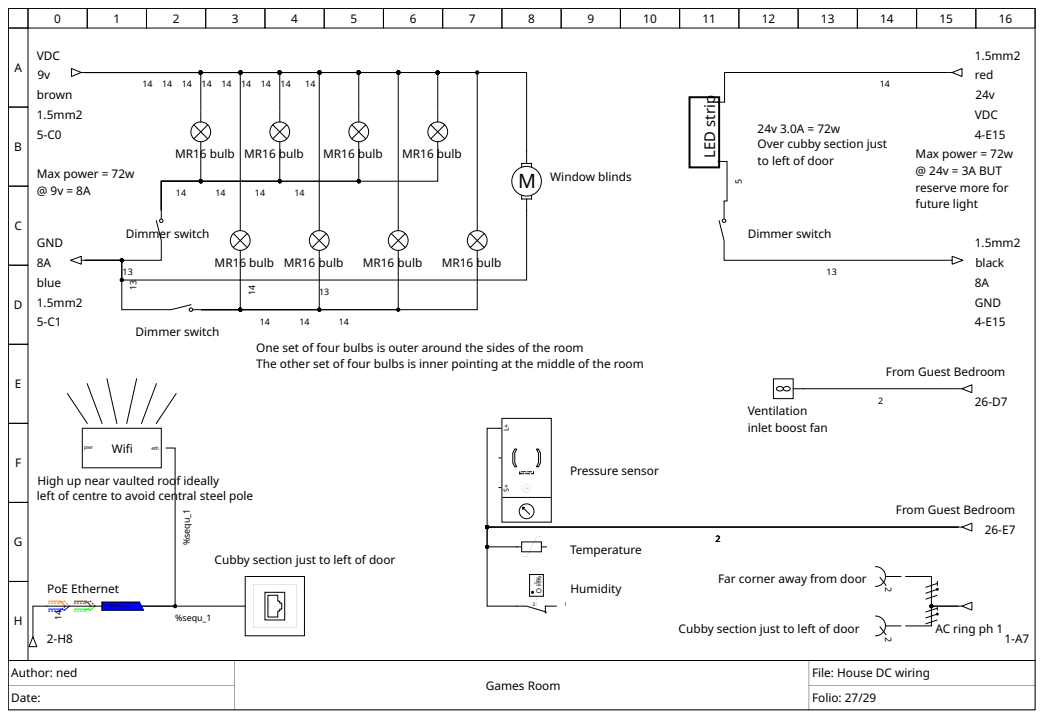
[picture p285: page 27]
Author: ned; Games Room; D strip; M Window blinds; Dimmer switch; VDC; red; MR16 bulb; GND; black; GND 8A blue 1.5mm2 5-C1; VDC 9v brown 1.5mm2 5-C0; PoE Ethernet; Wifi; pwr; eth; Max power = 72w @ 9v = 8A; Humidity; Pressure sensor; Temperature; %sequ_1

Over cubby section just
to left of door

Max power = 72w
@ 24v = 3A BUT
reserve more for
future light

One set of four bulbs is outer around the sides of the room
The other set of four bulbs is inner pointing at the middle of the room

From Guest Bedroom

Ventilation
inlet boost fan

High up near vaulted roof ideally
left of centre to avoid central steel pole

Cubby section just to left of door

Far corner away from door

AC ring ph 1

File: House DC wiring

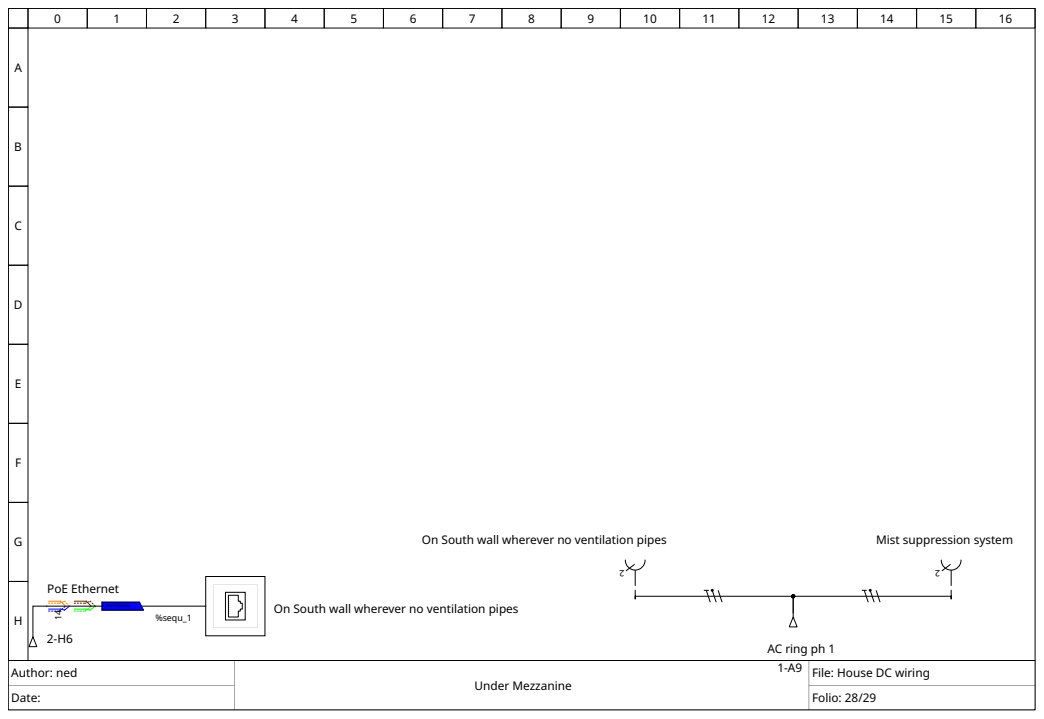
[picture p286: page 28]
Author: ned; Under Mezzanine; PoE Ethernet; %sequ_1

On South wall wherever no ventilation pipes

Mist suppression system

AC ring ph 1
File: House DC wiring

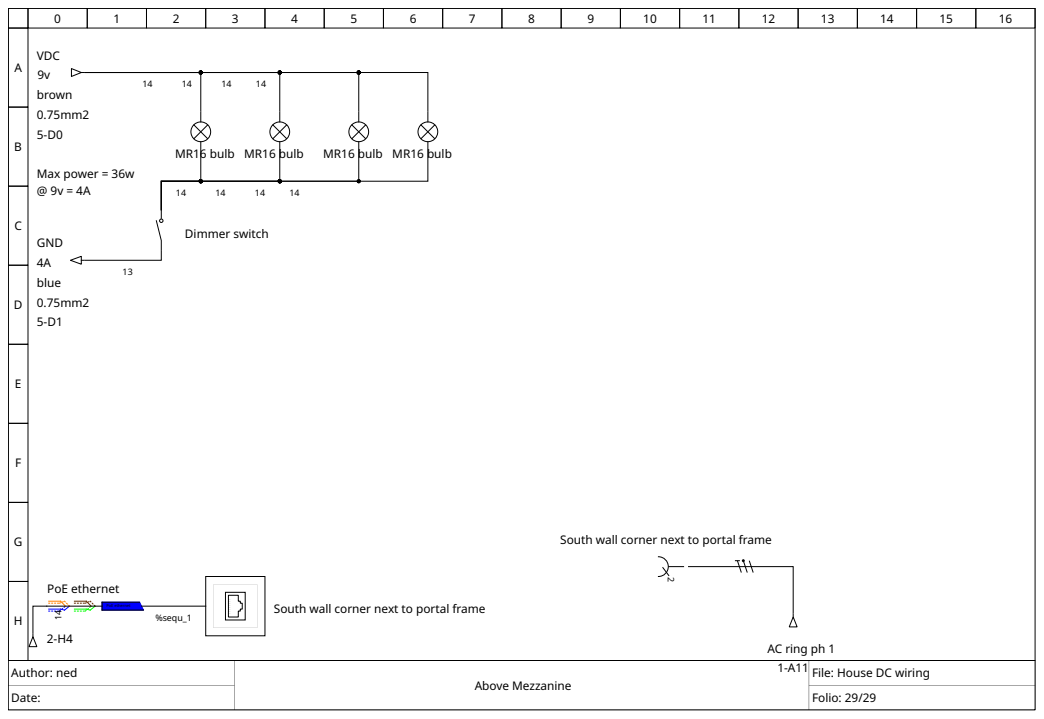
[picture p287: page 29]
Author: ned; Above Mezzanine; MR16 bulb MR16 bulb; MR16 bulb; Dimmer switch; GND 4A blue 0.75mm2 5-D1; VDC 9v brown 0.75mm2 5-D0; Max power = 36w @ 9v = 4A; PoE ethernet; %sequ_1

South wall corner next to portal frame

AC ring ph 1
File: House DC wiring
