ned14/HouseBuild/tech_docs/Endless pool installation instructions 1.jpg

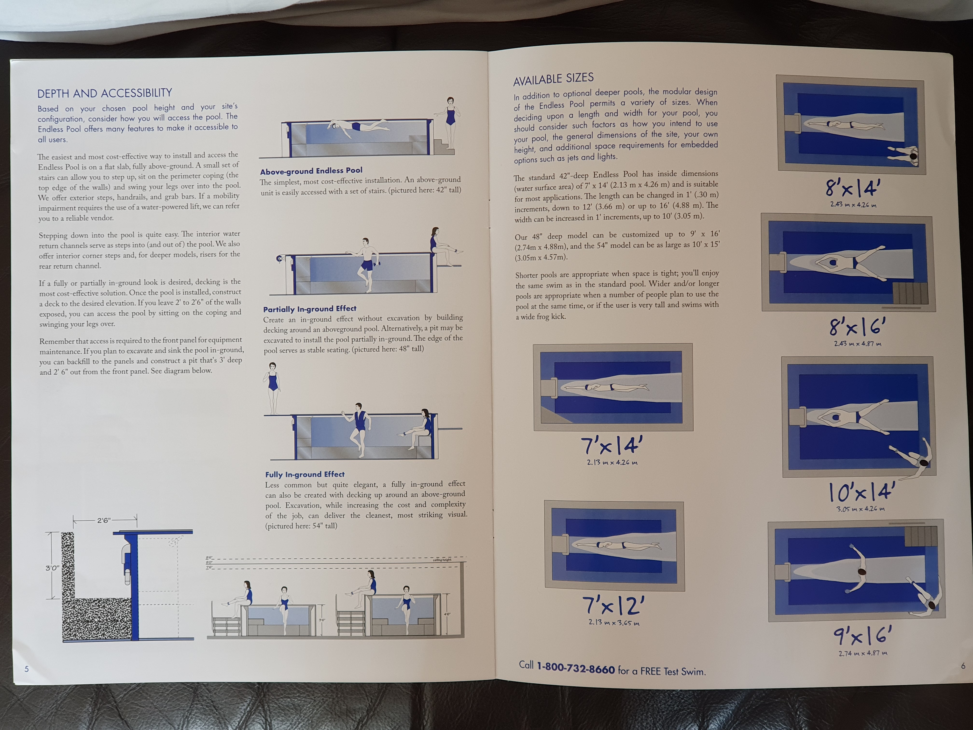
tech_docs/Endless pool installation instructions 1.jpg
