ned14/HouseBuild/tech_docs/Endless pool installation instructions 2.jpg

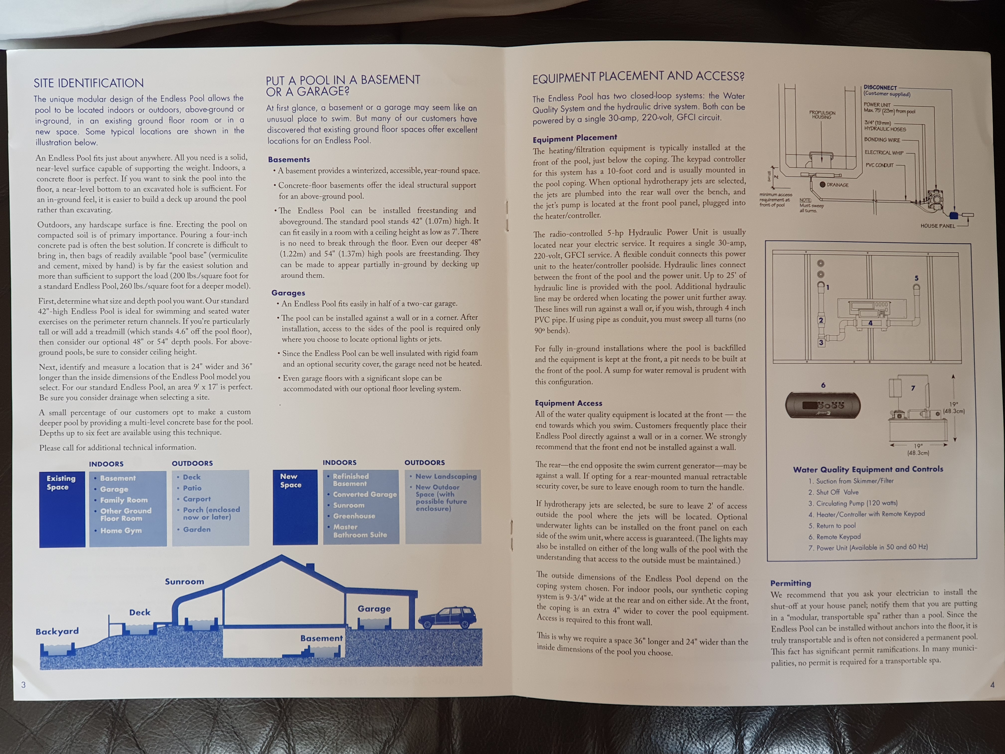
tech_docs/Endless pool installation instructions 2.jpg
