ned14/HouseBuild/designs/20220628 Masterkabin 221027-01 28.6.22 rev1.pdf

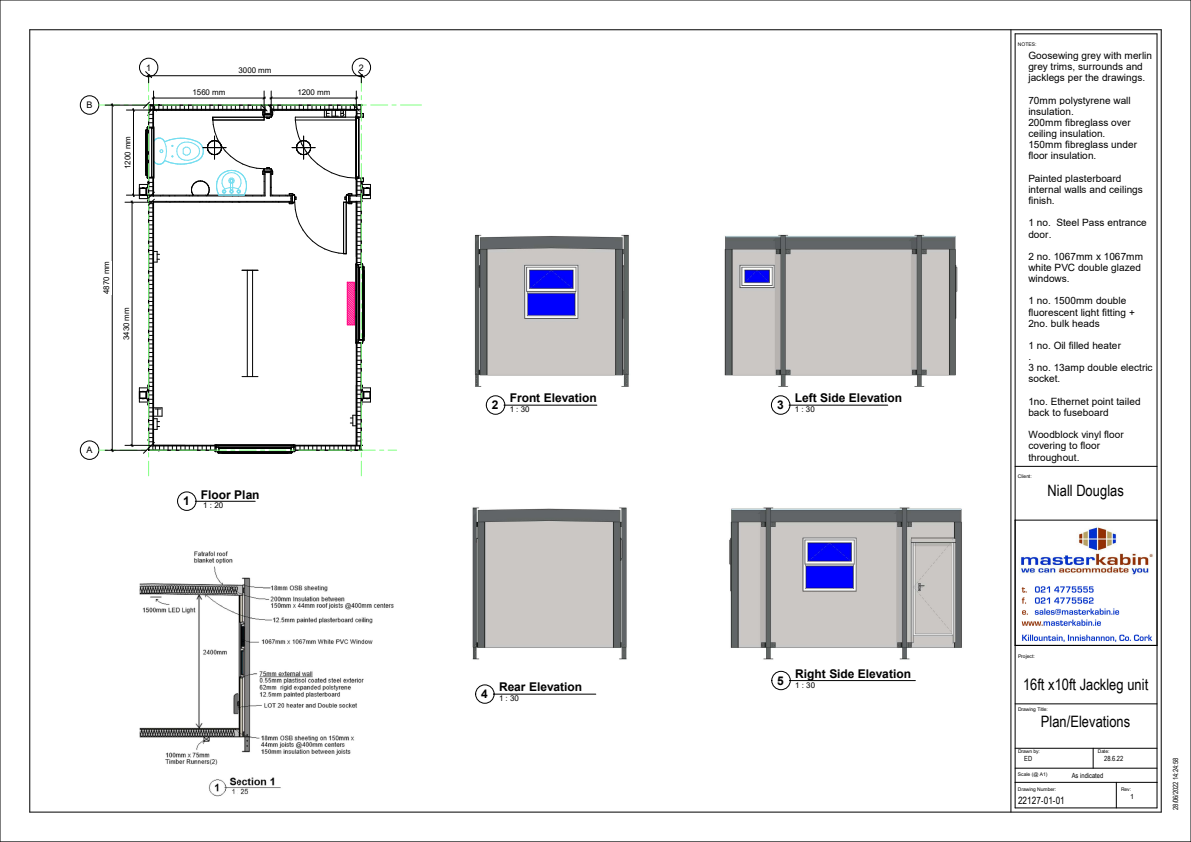
[picture p291: page 1]
Scale (@ A1); Drawing Title:; Client:; Project:; Drawing Number:; Rev: Drawn by:; Date:; As indicated; Plan/Elevations; 16ft x10ft Jackleg unit; Floor Plan 1; Front Elevation 2; Rear Elevation 4; 70mm polystyrene wall insulation. 200mm fibreglass over ceiling insulation. 150mm fibreglass under floor insulation.; socket.; throughout.

NOTES:
Goosewing grey with merlin
grey trims, surrounds and
jacklegs per the drawings.

Painted plasterboard
internal walls and ceilings
finish.

1 no. Steel Pass entrance
door.

white PVC double glazed
windows.
Niall Douglas

1 no. 1500mm double
fluorescent light fitting +
2no. bulk heads

1 no. Oil filled heater .3 no. 13amp double electric

Left Side Elevation 3

1no. Ethernet point tailed
back to fuseboard

Woodblock vinyl floor
covering to floor

Right Side Elevation 5
