ned14/HouseBuild/quotes/20240604_NordanWindows2/Energy Report.pdf

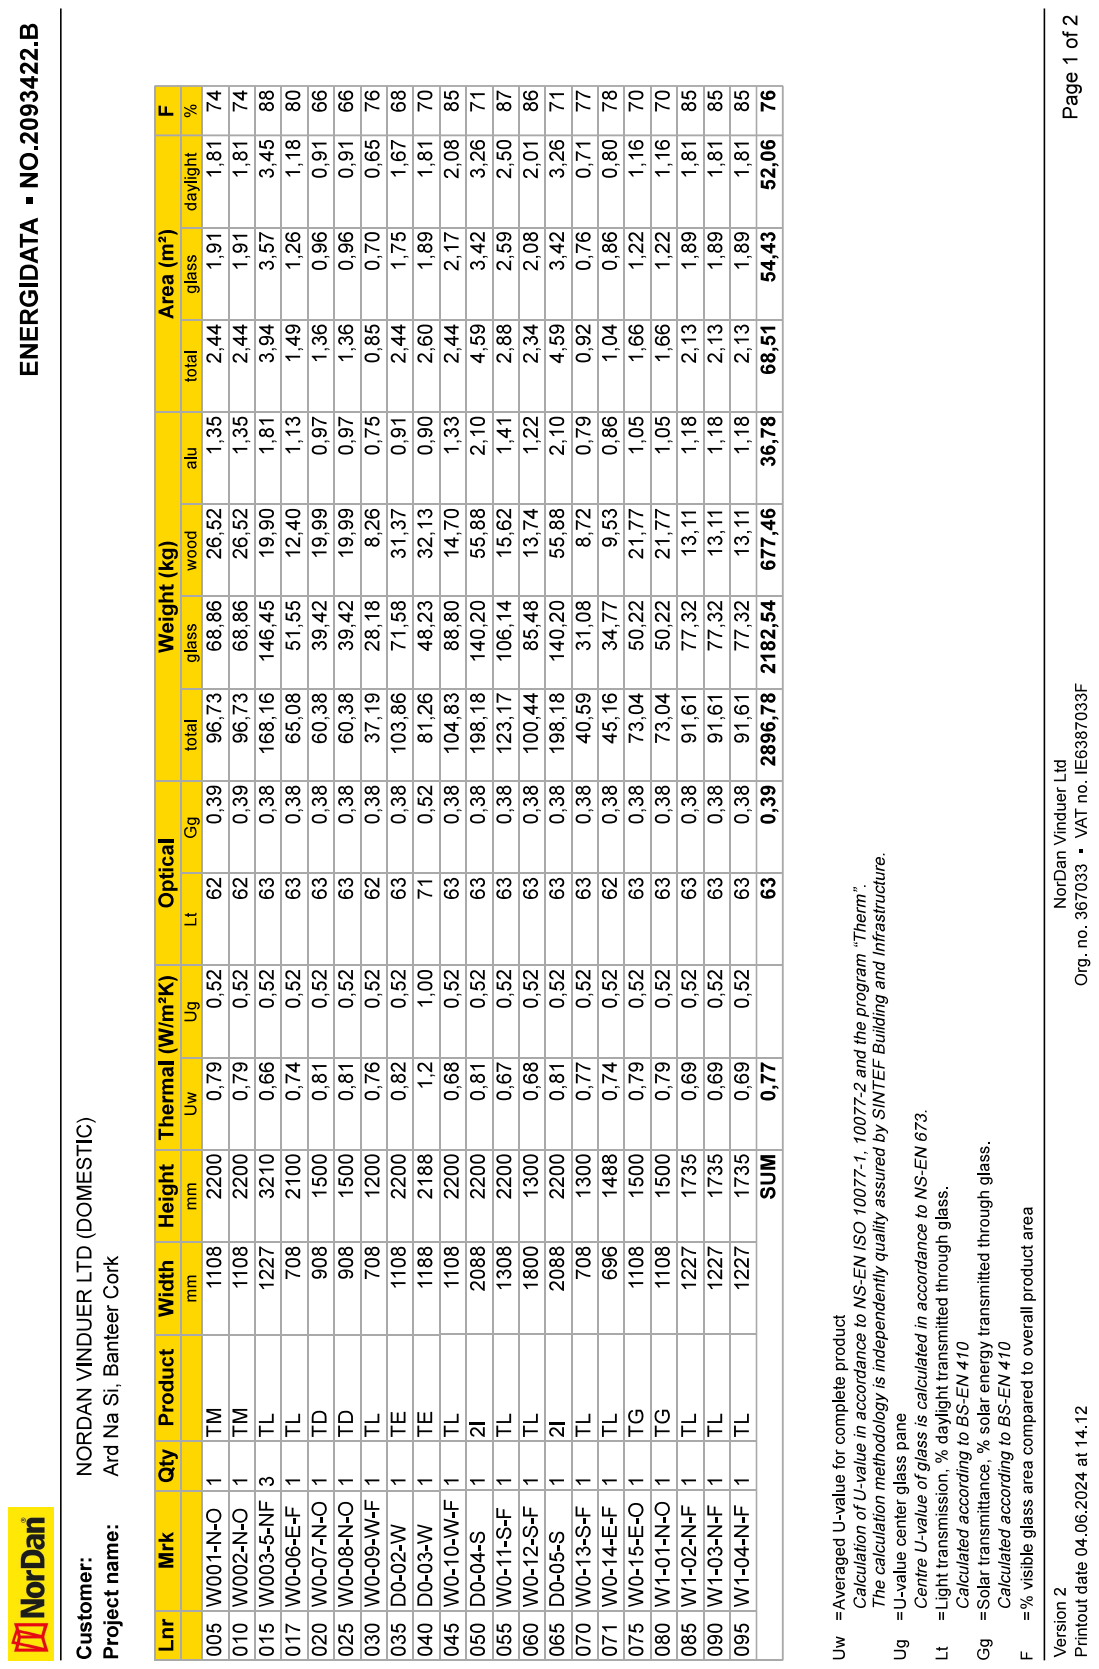
[picture p292: page 1]

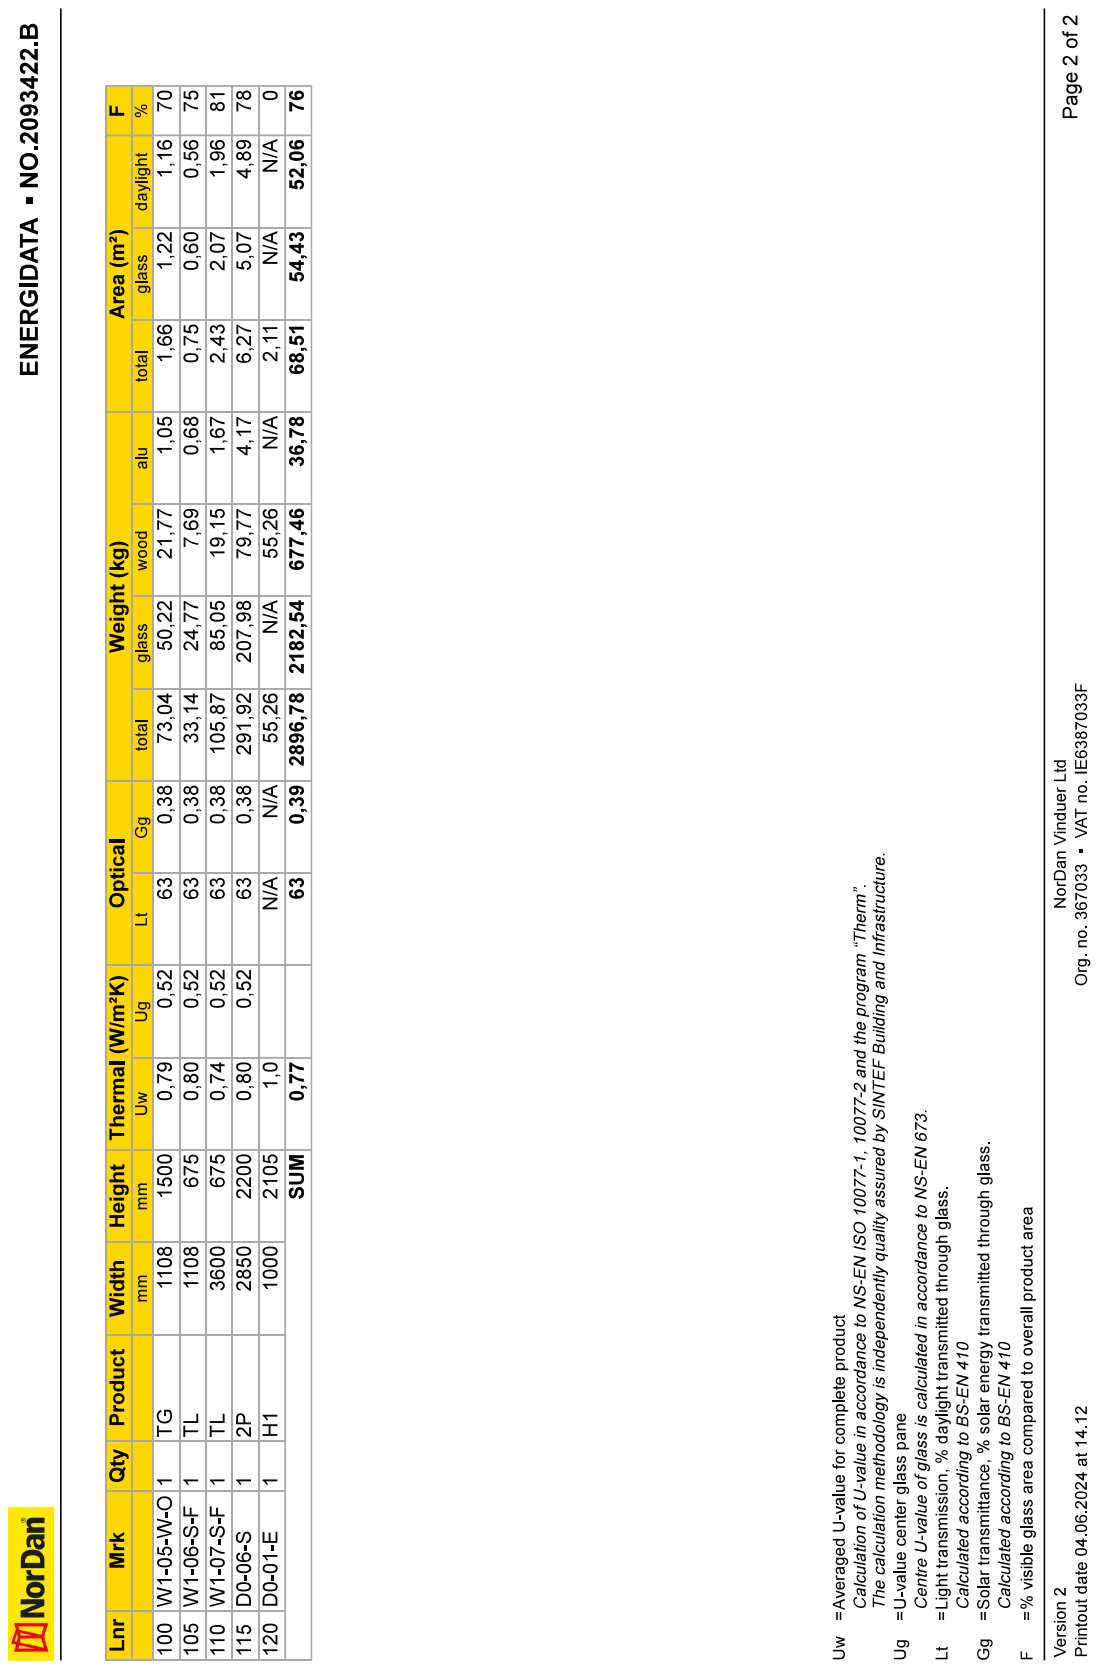
[picture p293: page 2]
