ned14/HouseBuild/surveys_maps_docs/water-quality-summary-2014.pdf

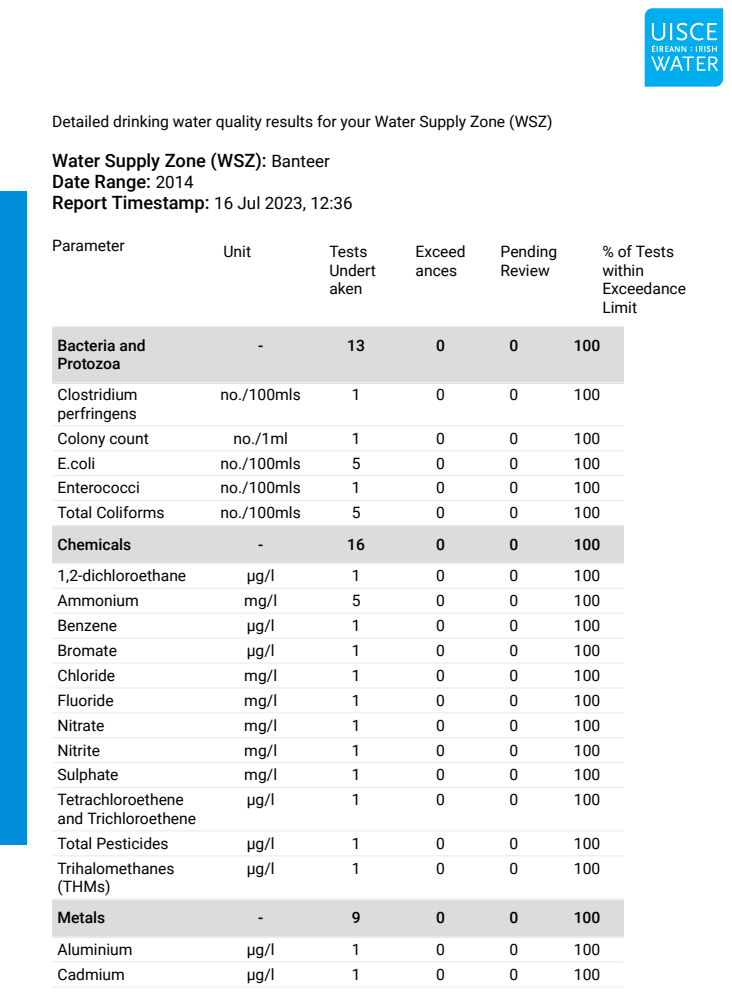
[picture p294: page 1]
Parameter; Unit; Tests; Undert aken; Exceed ances; Pending Review; % of Tests within Exceedance Limit; Bacteria and Protozoa; Clostridium perfringens; no./100mls; Colony count; E.coli; Enterococci; Total Coliforms; Chemicals; 1,2-dichloroethane; Ammonium; Benzene; Bromate; Chloride; Fluoride; Nitrate; Nitrite; Sulphate; Tetrachloroethene and Trichloroethene; Total Pesticides; Trihalomethanes (THMs); Metals; Aluminium; Cadmium

Detailed drinking water quality results for your Water Supply Zone (WSZ)
Water Supply Zone (WSZ): Banteer
Date Range: 2014
Report Timestamp: 16 Jul 2023, 12:36

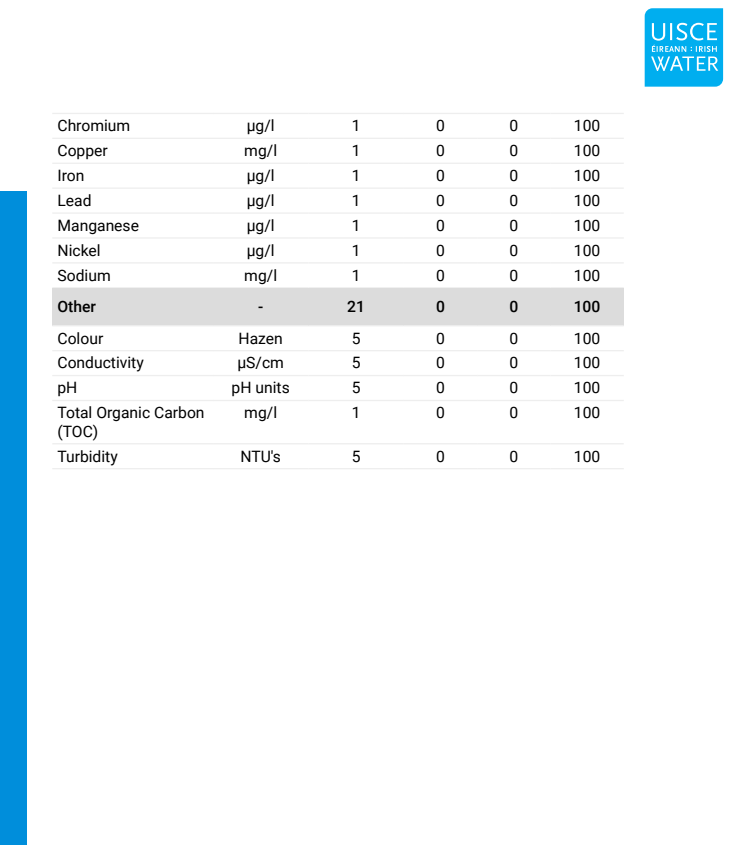
[picture p295: page 2]
Chromium; Copper; Iron; Lead; Manganese; Nickel; Sodium; Colour; Hazen; Conductivity; pH units; Turbidity; NTU's

Other
Total Organic Carbon
(TOC)
