ned14/HouseBuild/surveys_maps_docs/water-quality-summary-2016.pdf

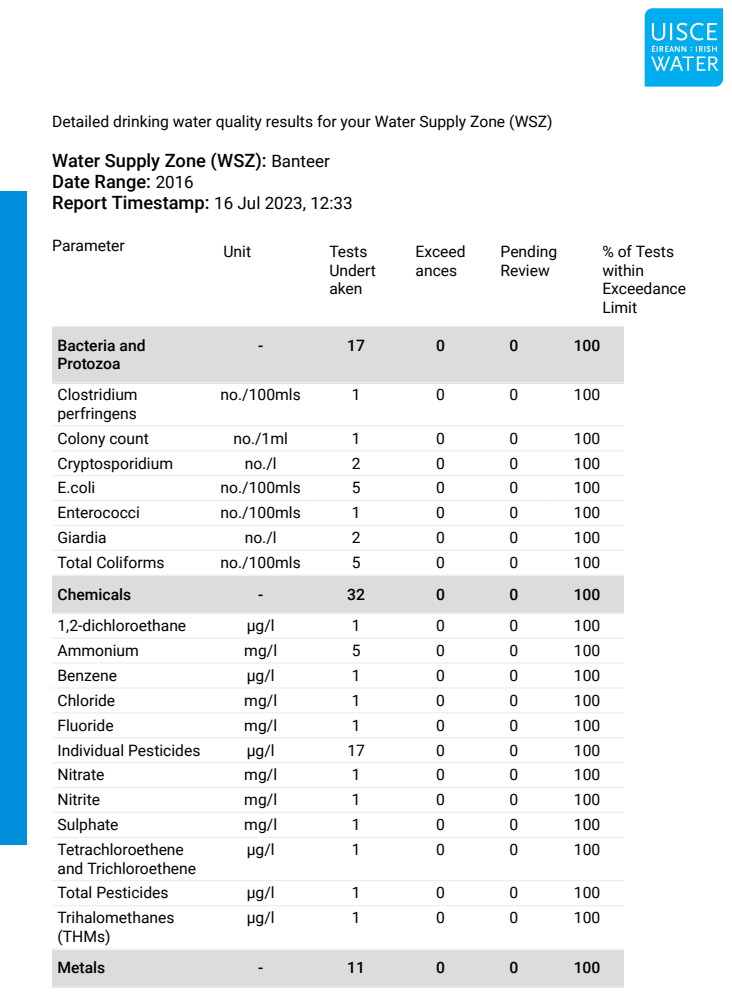
[picture p298: page 1]
Parameter; Unit; Tests; Undert aken; Exceed ances; Pending Review; % of Tests within Exceedance Limit; Bacteria and Protozoa; Clostridium perfringens; no./100mls; Colony count; Cryptosporidium; E.coli; Enterococci; Giardia; Total Coliforms; Chemicals; 1,2-dichloroethane; Ammonium; Benzene; Chloride; Fluoride; Individual Pesticides; Nitrate; Nitrite; Sulphate; Tetrachloroethene and Trichloroethene; Total Pesticides; Trihalomethanes (THMs); Metals

Detailed drinking water quality results for your Water Supply Zone (WSZ)
Water Supply Zone (WSZ): Banteer
Date Range: 2016
Report Timestamp: 16 Jul 2023, 12:33

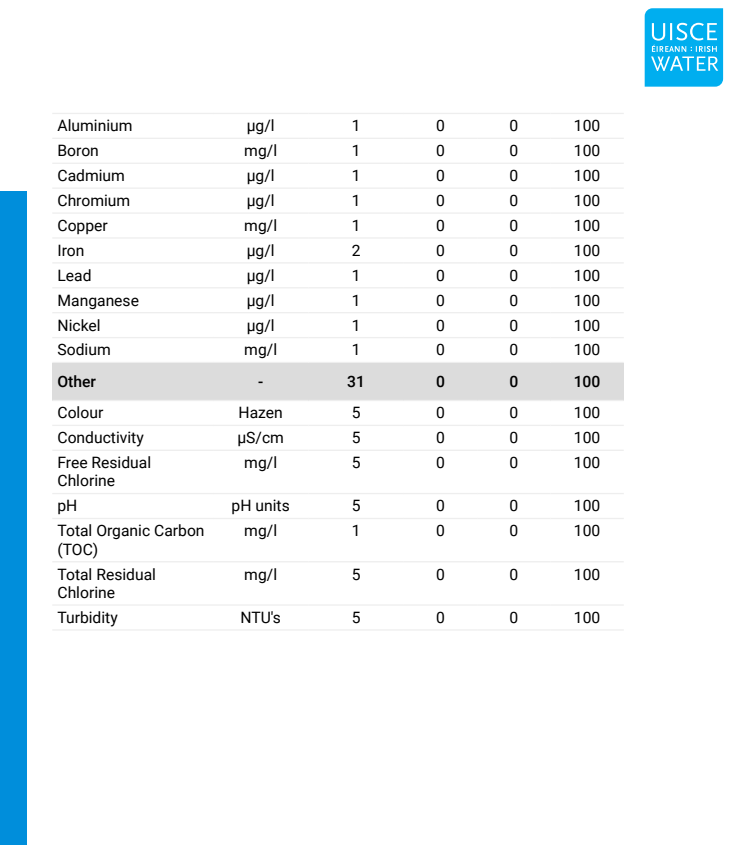
[picture p299: page 2]
Aluminium; Boron; Cadmium; Chromium; Copper; Iron; Lead; Manganese; Nickel; Sodium; Colour; Hazen; Conductivity; pH units; Turbidity; NTU's

Other
Free Residual
Chlorine
Total Organic Carbon
(TOC)
Total Residual
