ned14/HouseBuild/surveys_maps_docs/water-quality-summary-2018.pdf

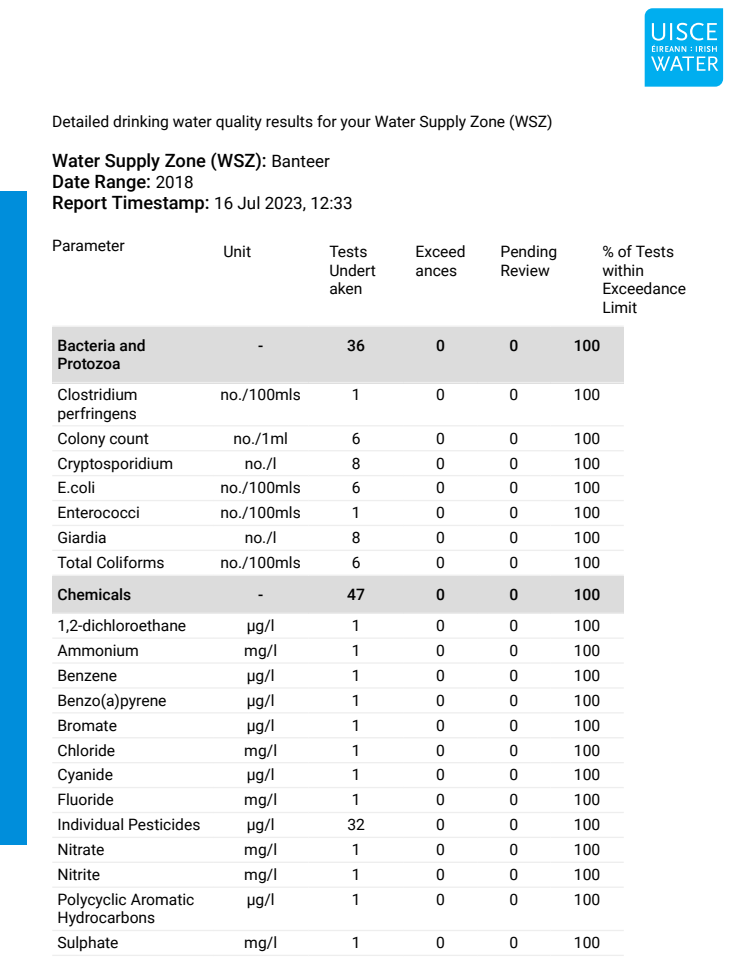
[picture p300: page 1]
Parameter; Unit; Tests; Undert aken; Exceed ances; Pending Review; % of Tests within Exceedance Limit; Bacteria and Protozoa; Clostridium perfringens; no./100mls; Colony count; Cryptosporidium; E.coli; Enterococci; Giardia; Total Coliforms; Chemicals; 1,2-dichloroethane; Ammonium; Benzene; Benzo(a)pyrene; Bromate; Chloride; Cyanide; Fluoride; Individual Pesticides; Nitrate; Nitrite; Polycyclic Aromatic Hydrocarbons; Sulphate

Detailed drinking water quality results for your Water Supply Zone (WSZ)
Water Supply Zone (WSZ): Banteer
Date Range: 2018
Report Timestamp: 16 Jul 2023, 12:33

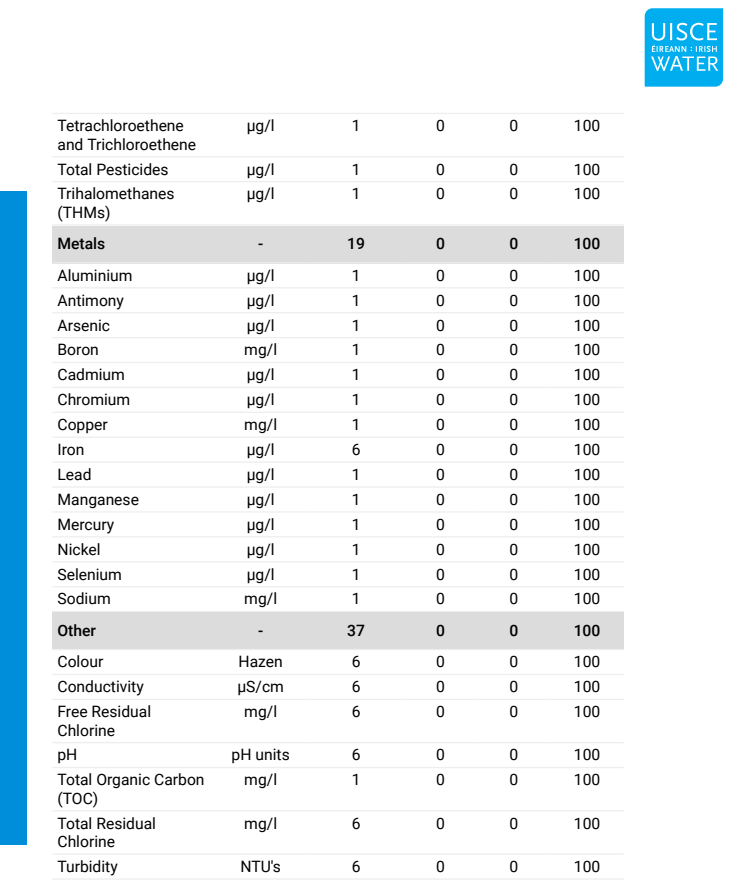
[picture p301: page 2]
Tetrachloroethene and Trichloroethene; Total Pesticides; Trihalomethanes (THMs); Metals; Aluminium; Antimony; Arsenic; Boron; Cadmium; Chromium; Copper; Iron; Lead; Manganese; Mercury; Nickel; Selenium; Sodium; Other; Colour; Hazen; Conductivity; Free Residual Chlorine; pH units; Total Organic Carbon (TOC); Total Residual Chlorine; Turbidity; NTU's
