ned14/HouseBuild/surveys_maps_docs/Geothermal Suitability.pdf

+
–

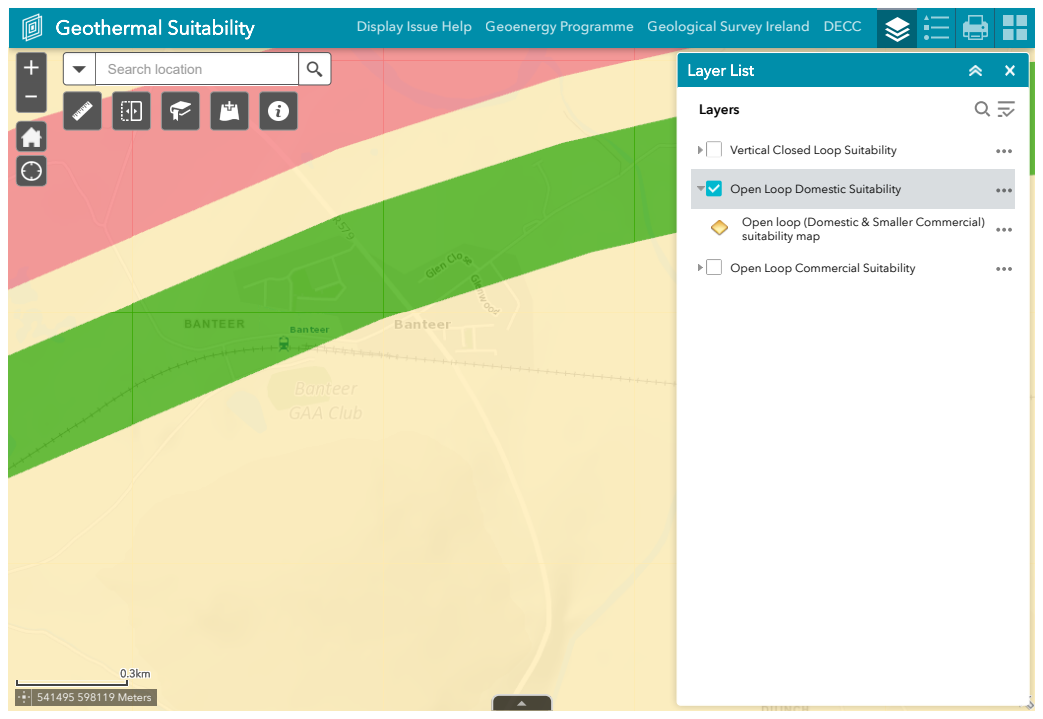
[picture p306: page 1]
.33kkmm; Search location; 541495 598119 Meters; Geothermal Suitability; Layer List

Display Issue Help (https://secure.dccae.gov.ie/GSI_DOWNLOAD/GSI/Viewers/Google_Chrome_browser_empty_cache_and_reload.pdf) Geoenergy Programme (https://www.gsi.ie/en-ie/programmes-and-projects/geoenergy/Pages/default.aspx) Geological Survey Ireland (https://www.gsi.ie/en-ie/Pages/default.aspx) DECC (https://www.gov.ie/en/organisation/department-of-the-environment-climate-and-communications/)

Layers Vertical Closed Loop Suitability

Open Loop Domestic Suitability

Open loop (Domestic & Smaller Commercial)
suitability map

Open Loop Commercial Suitability
