ned14/HouseBuild/quotes/20240604_NordanWindows2/Workshop Drawings.pdf

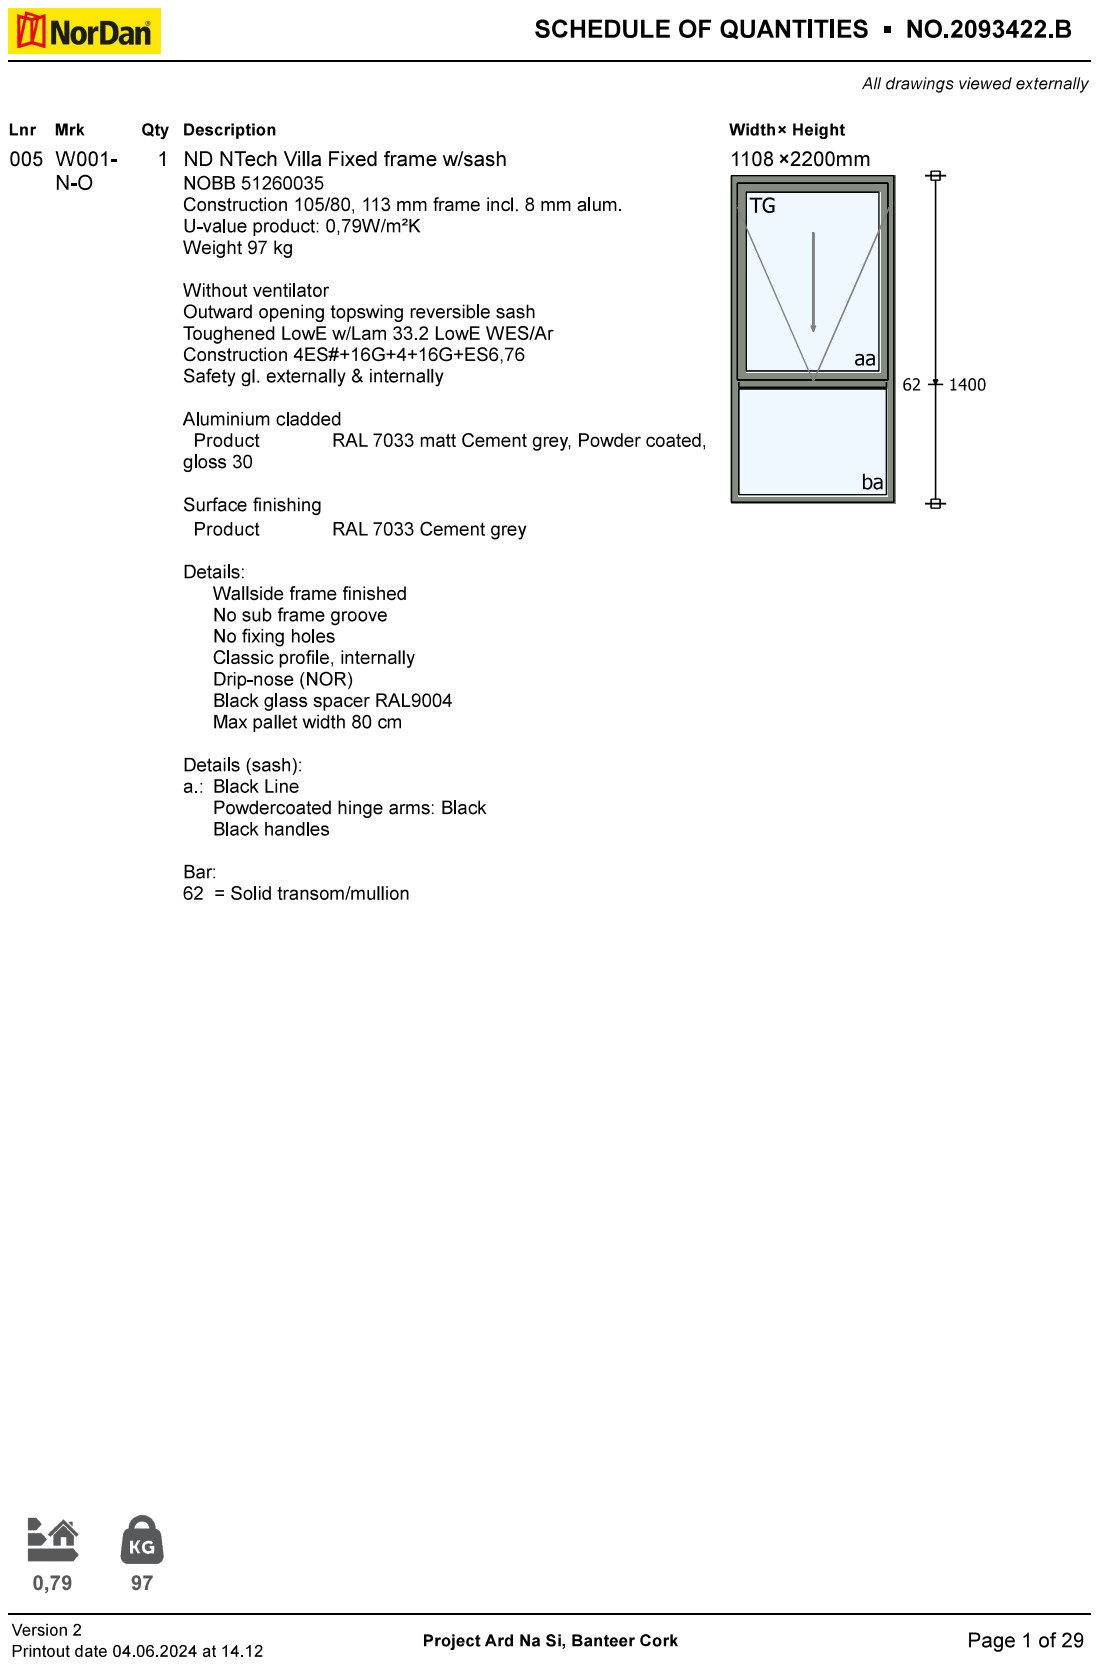
[picture p307: page 1]

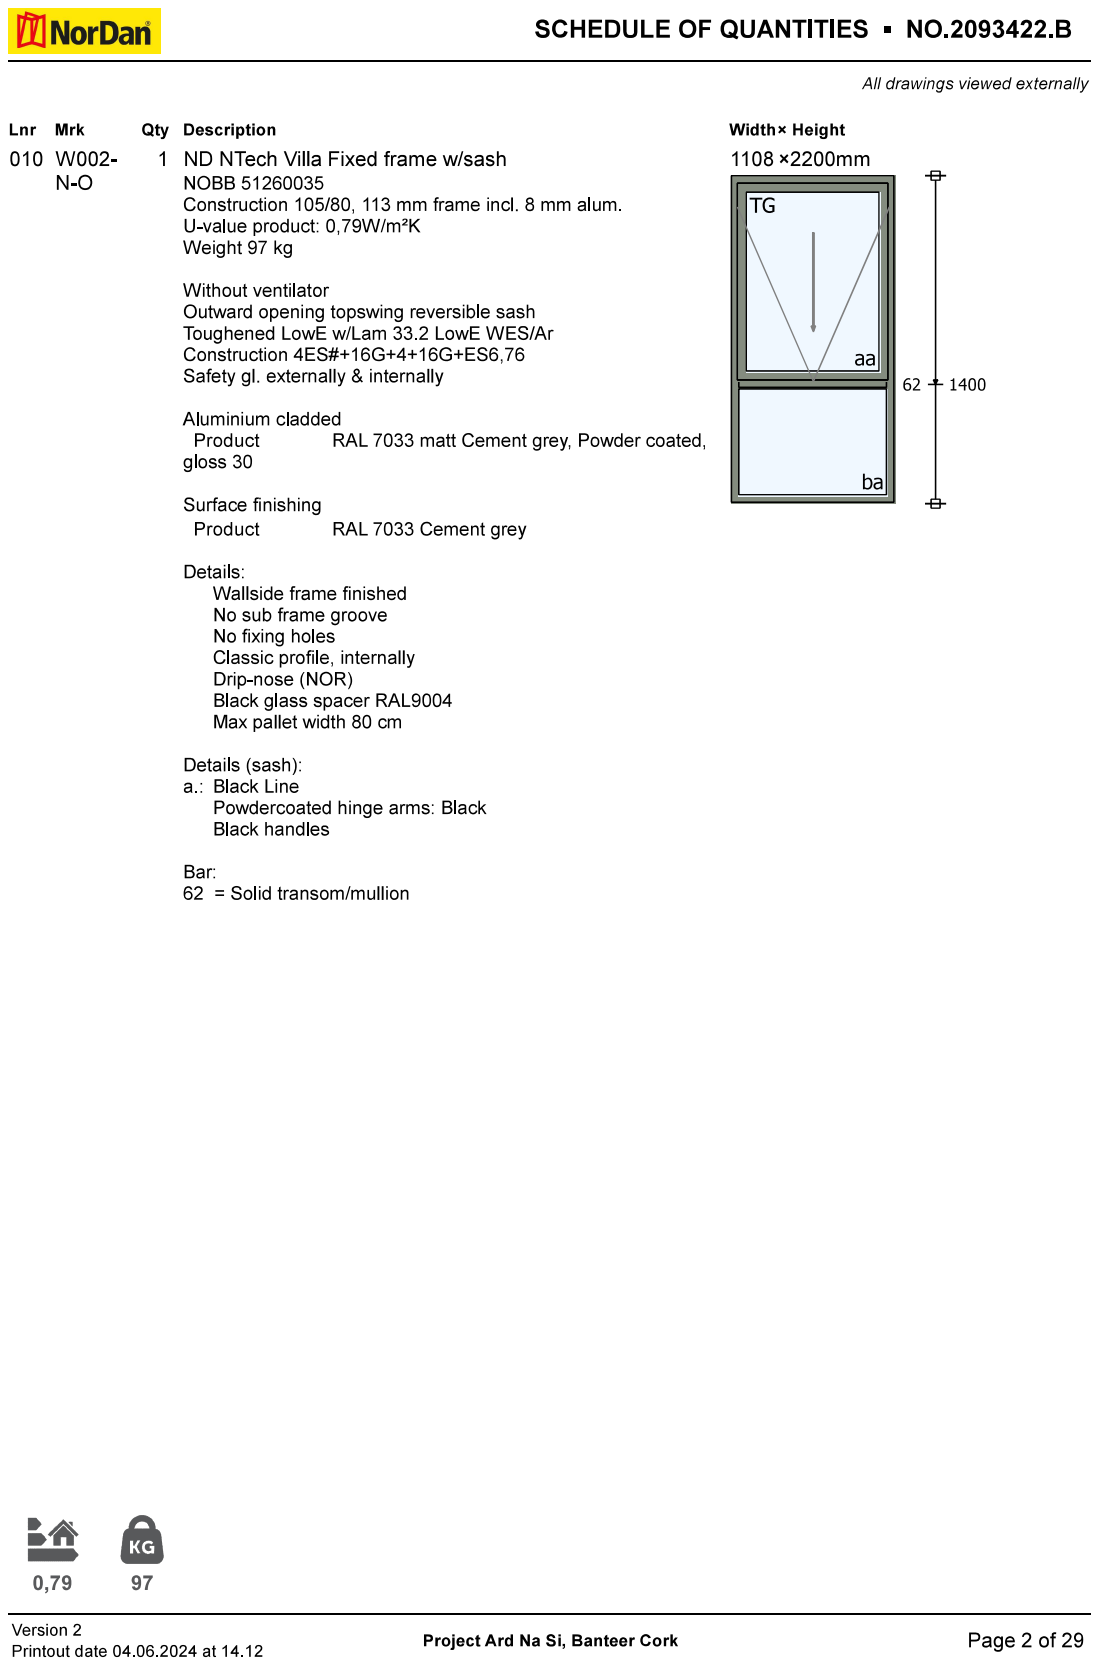
[picture p308: page 2]

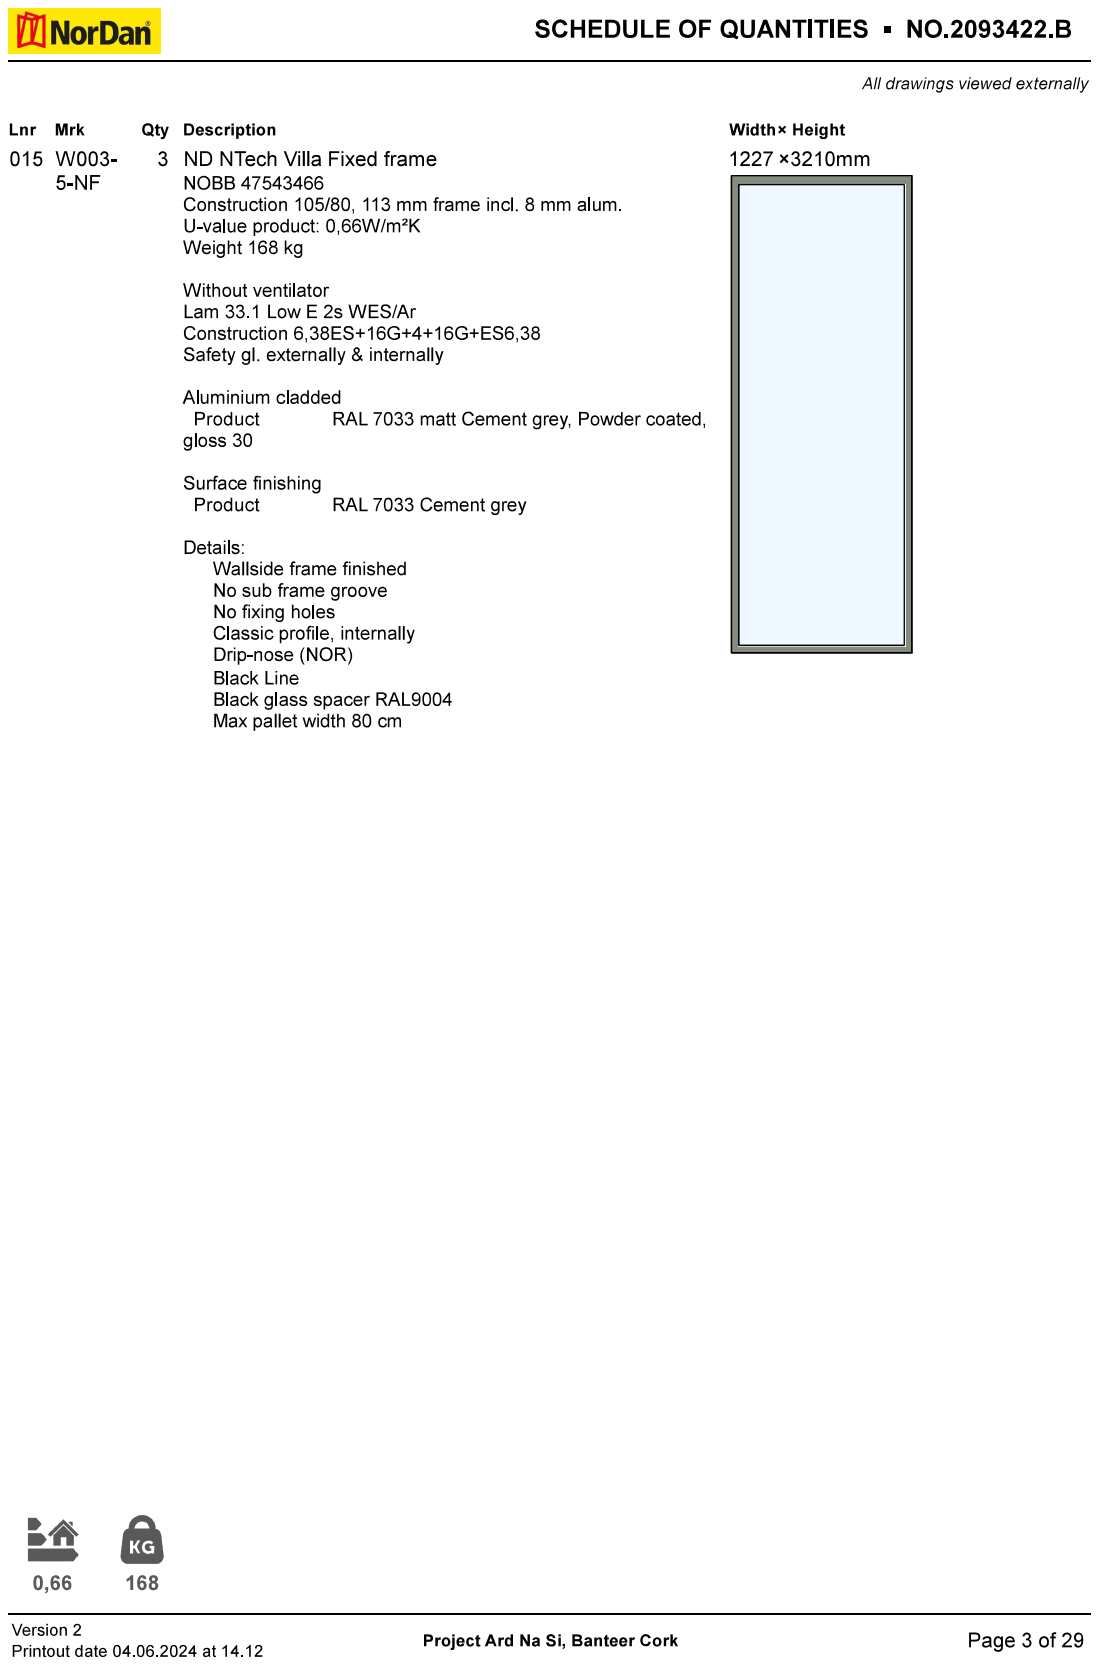
[picture p309: page 3]

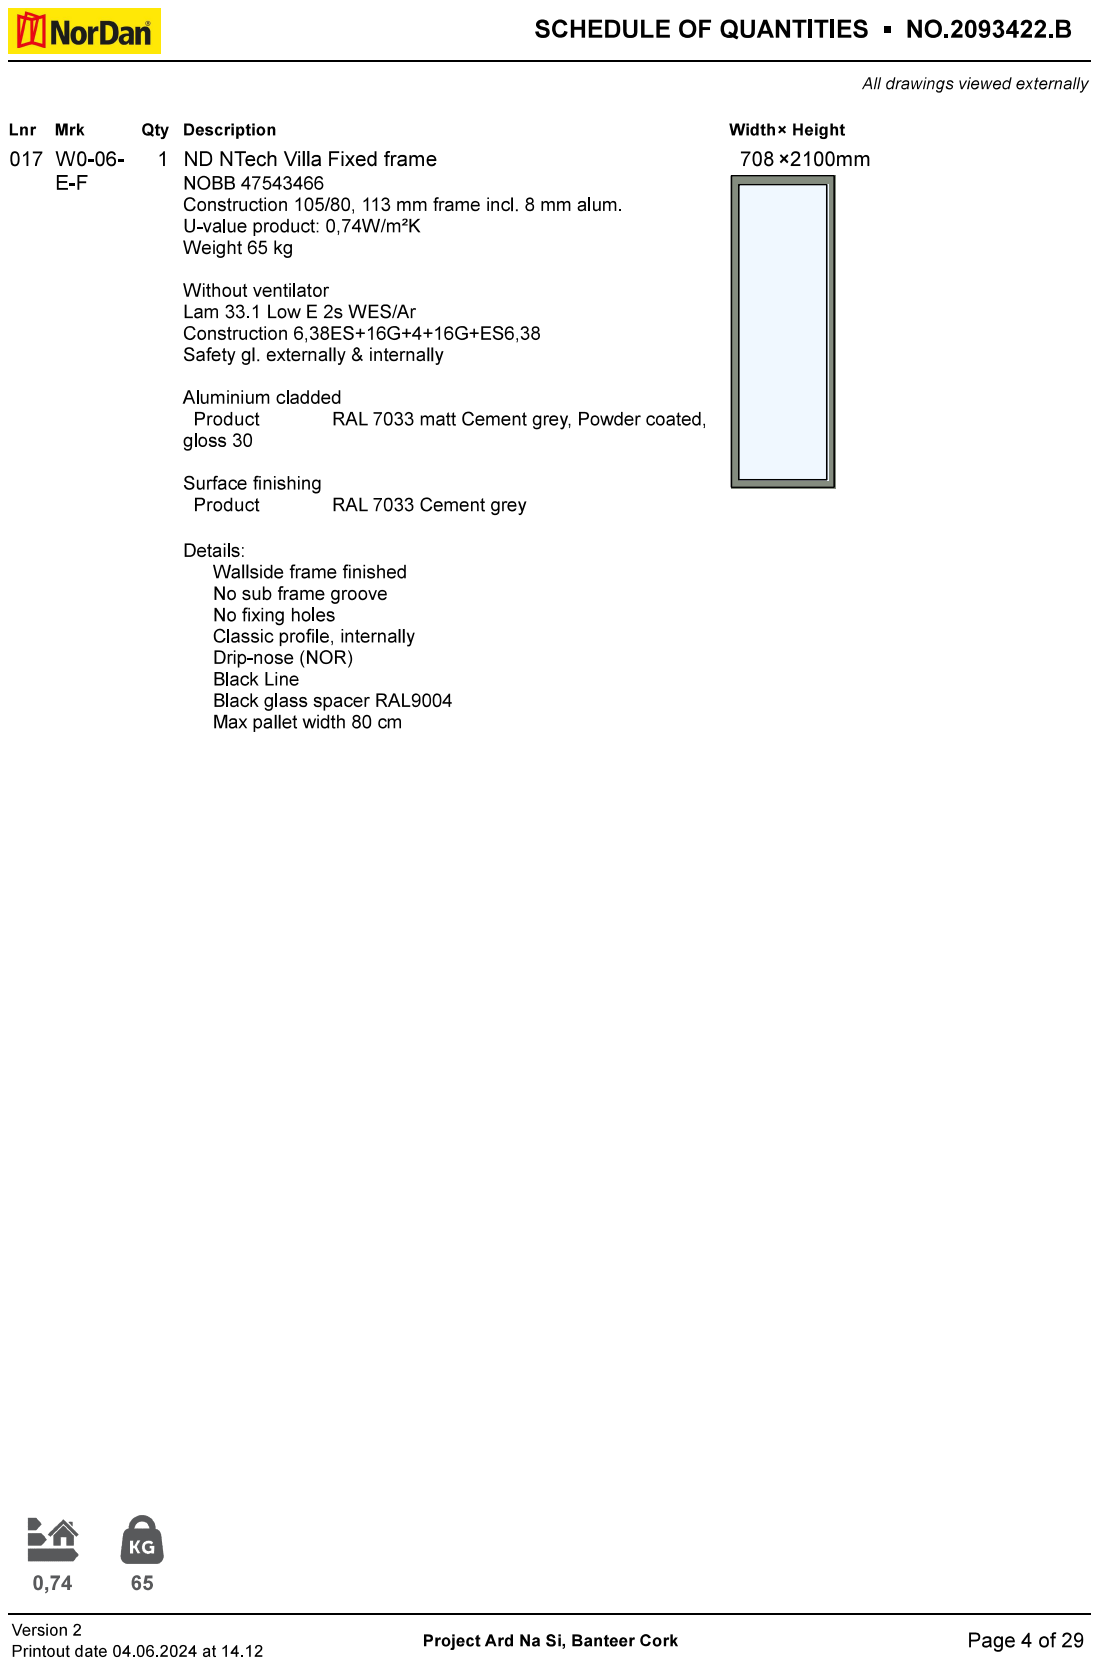
[picture p310: page 4]

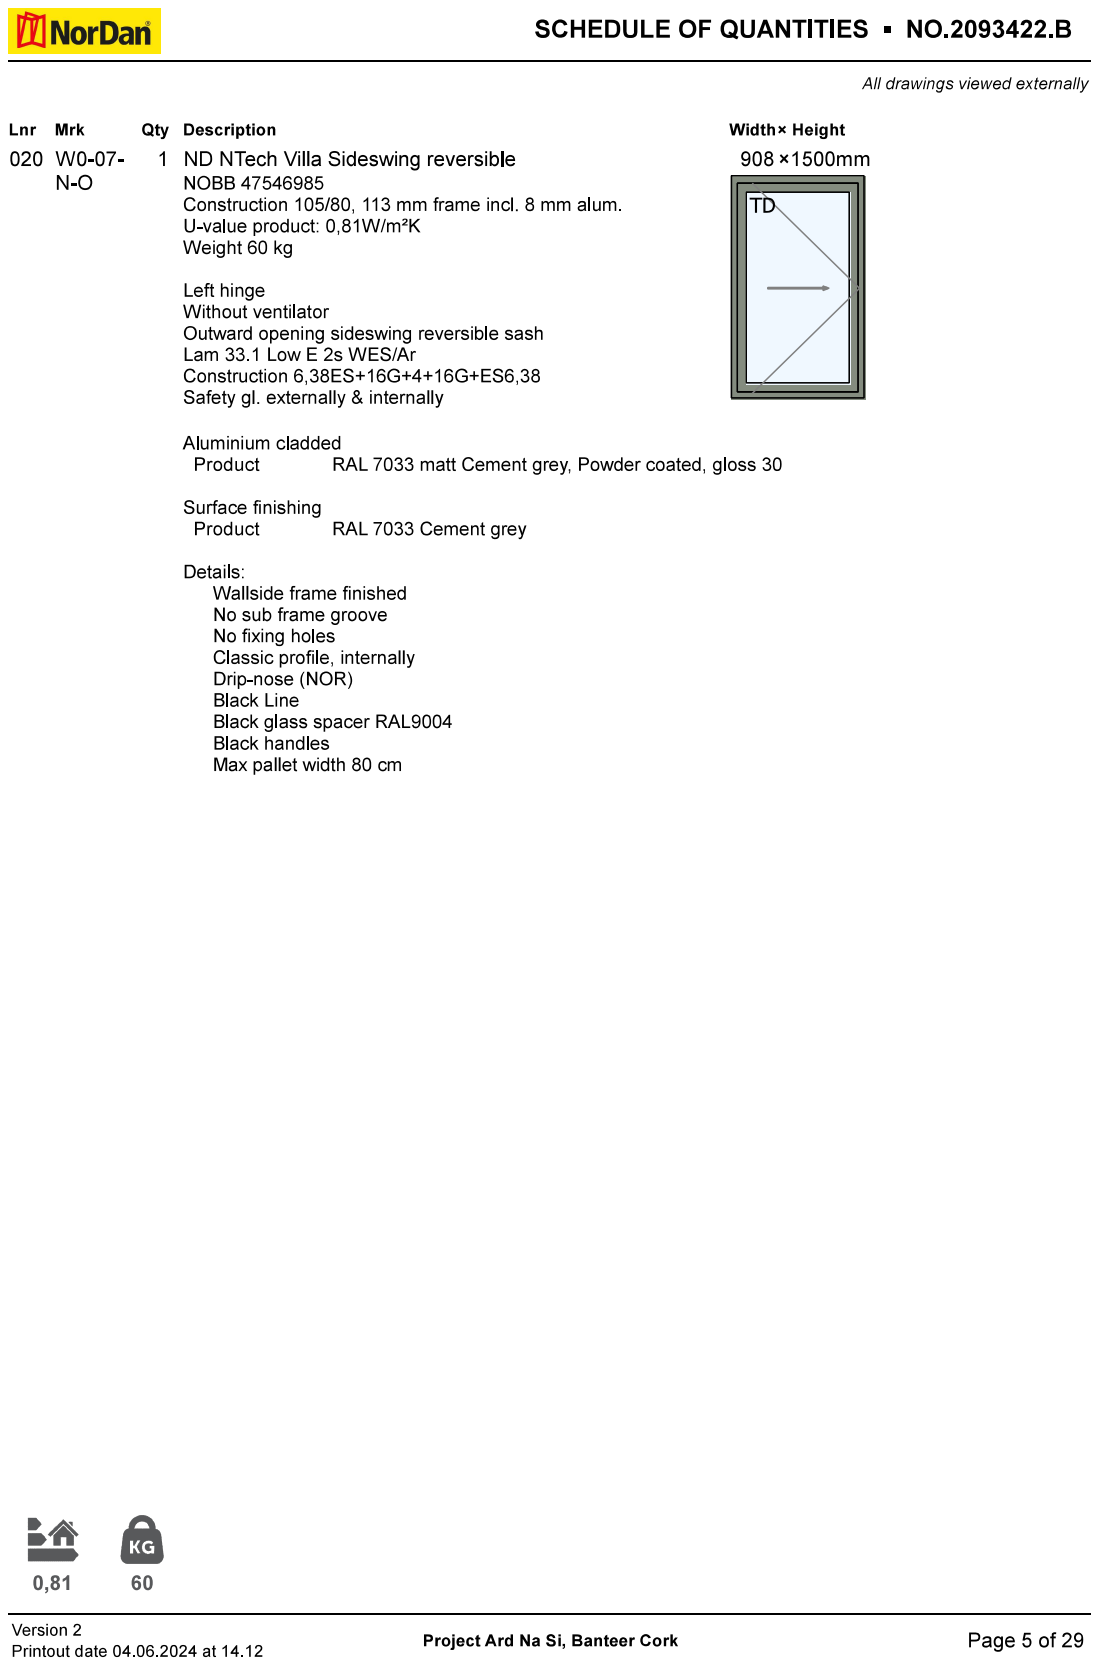
[picture p311: page 5]

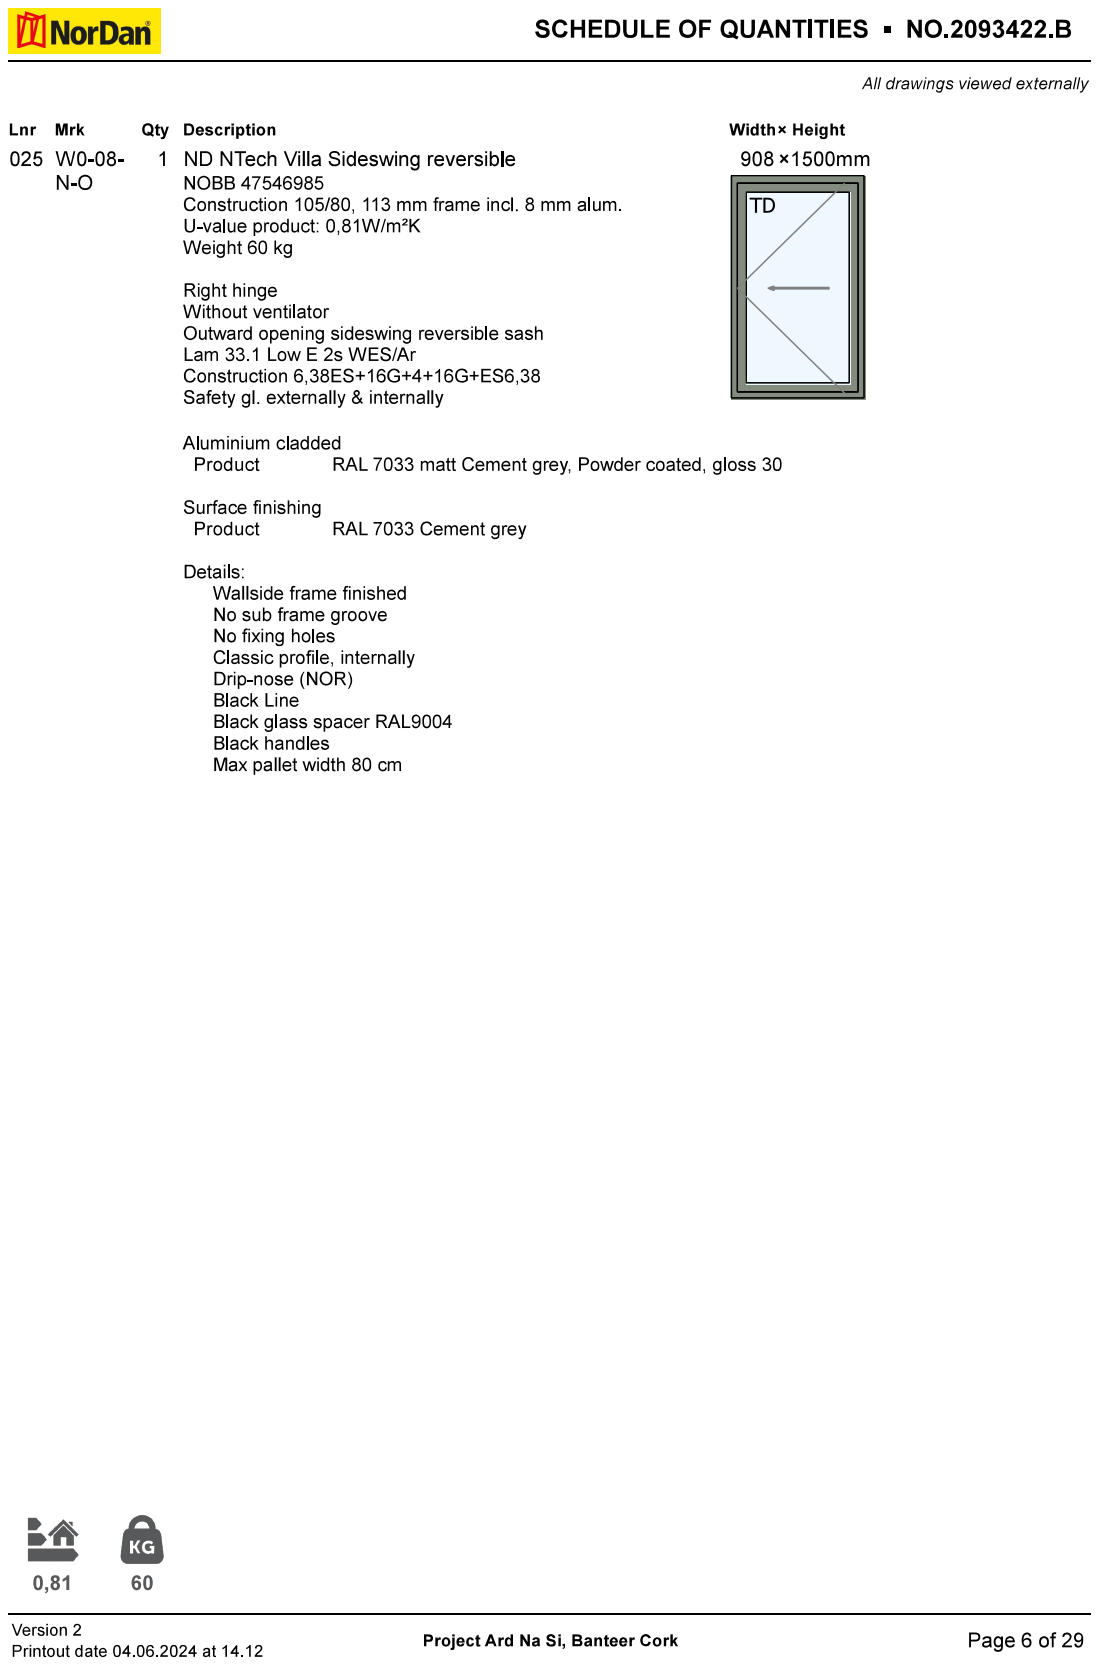
[picture p312: page 6]

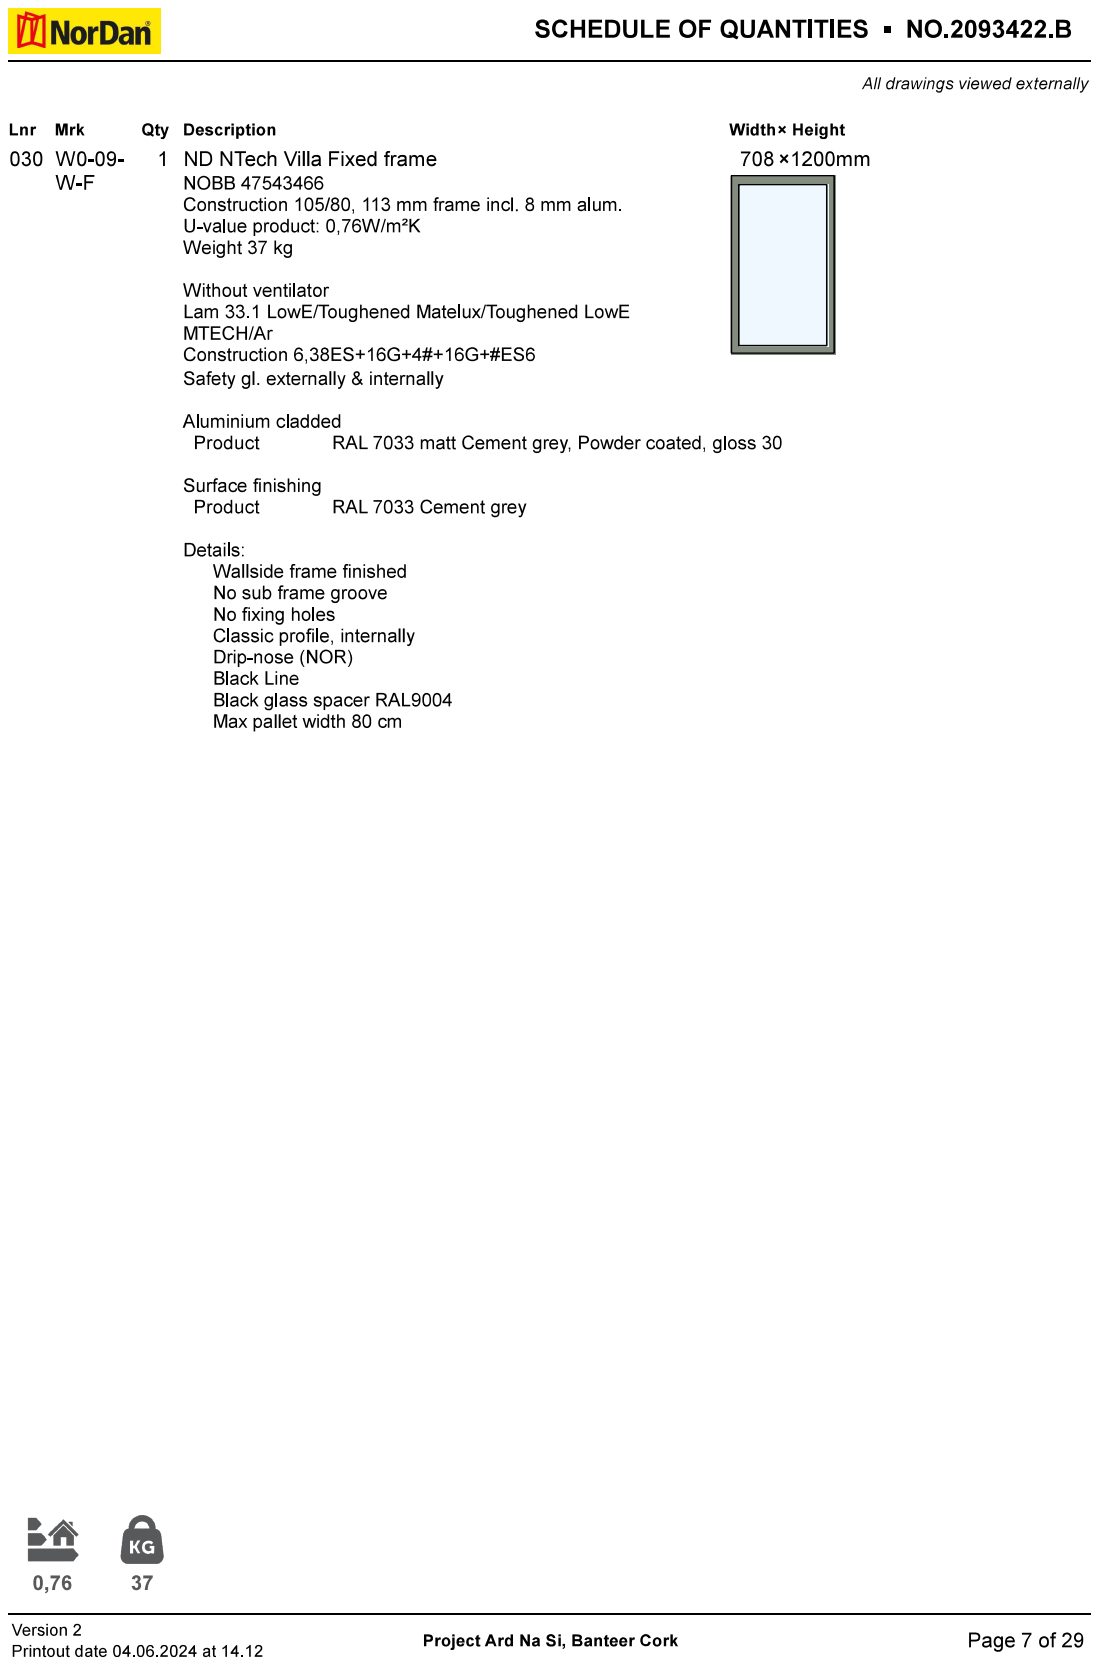
[picture p313: page 7]

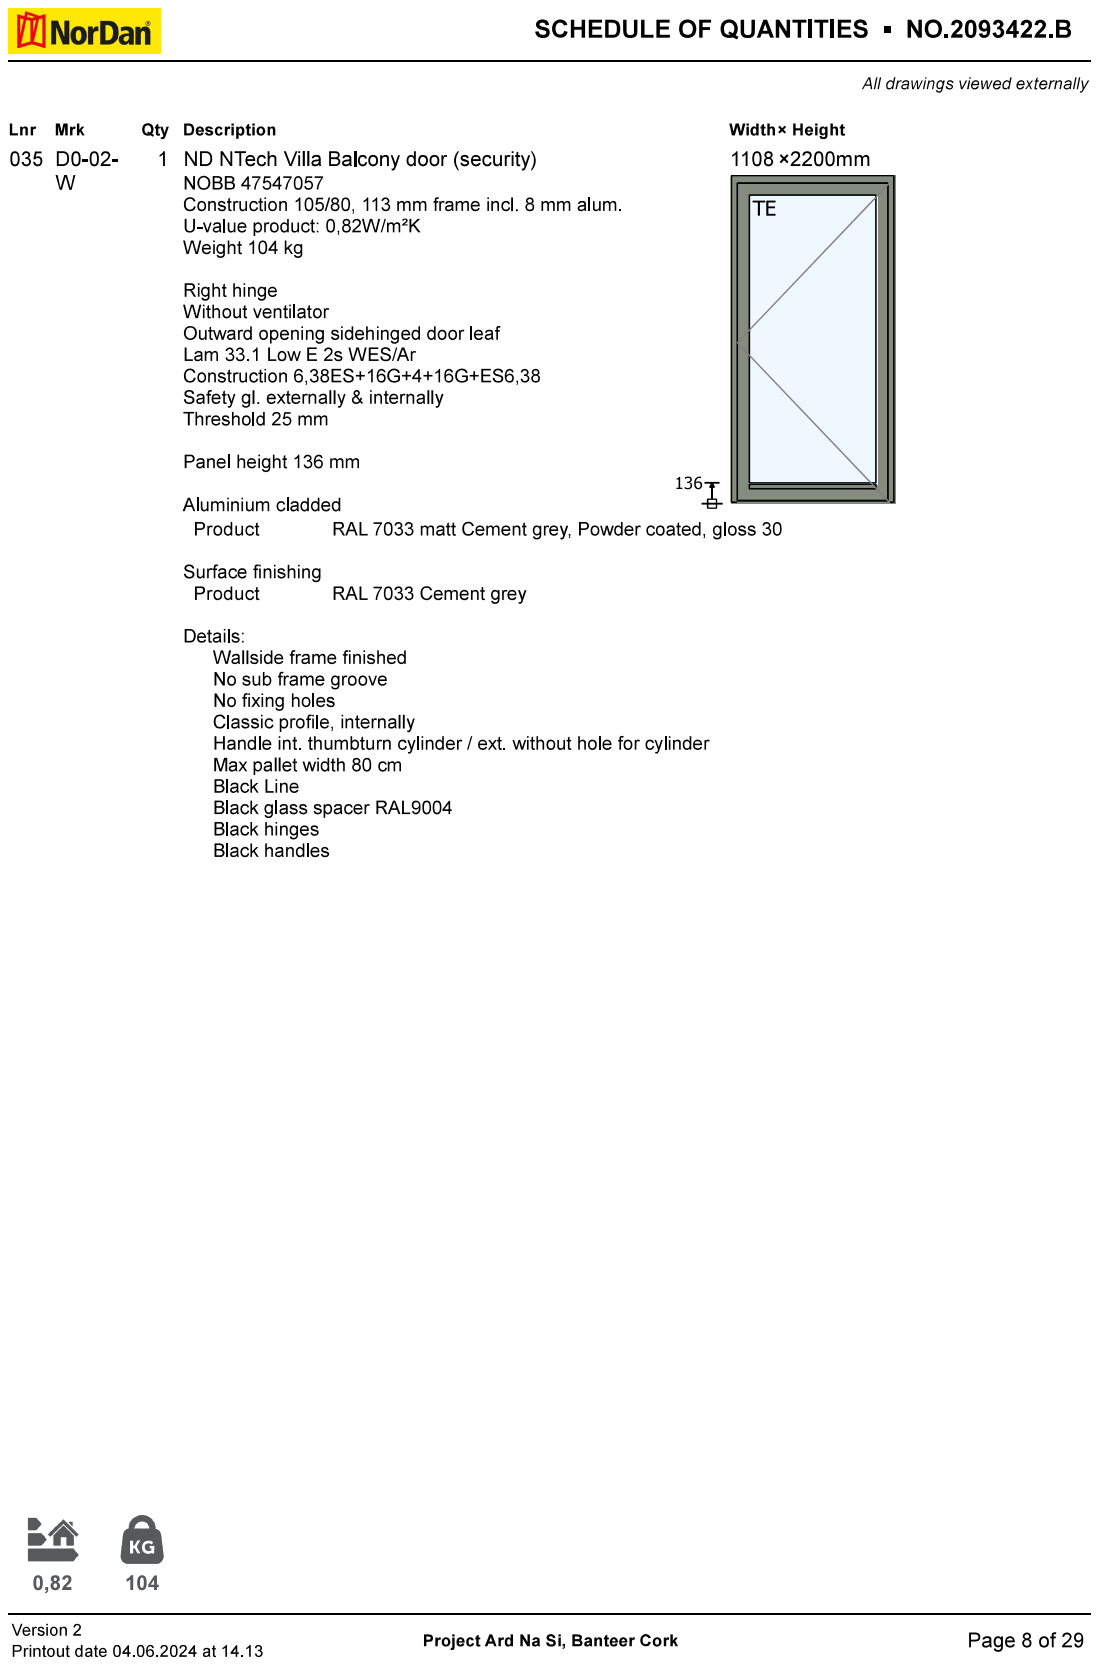
[picture p314: page 8]

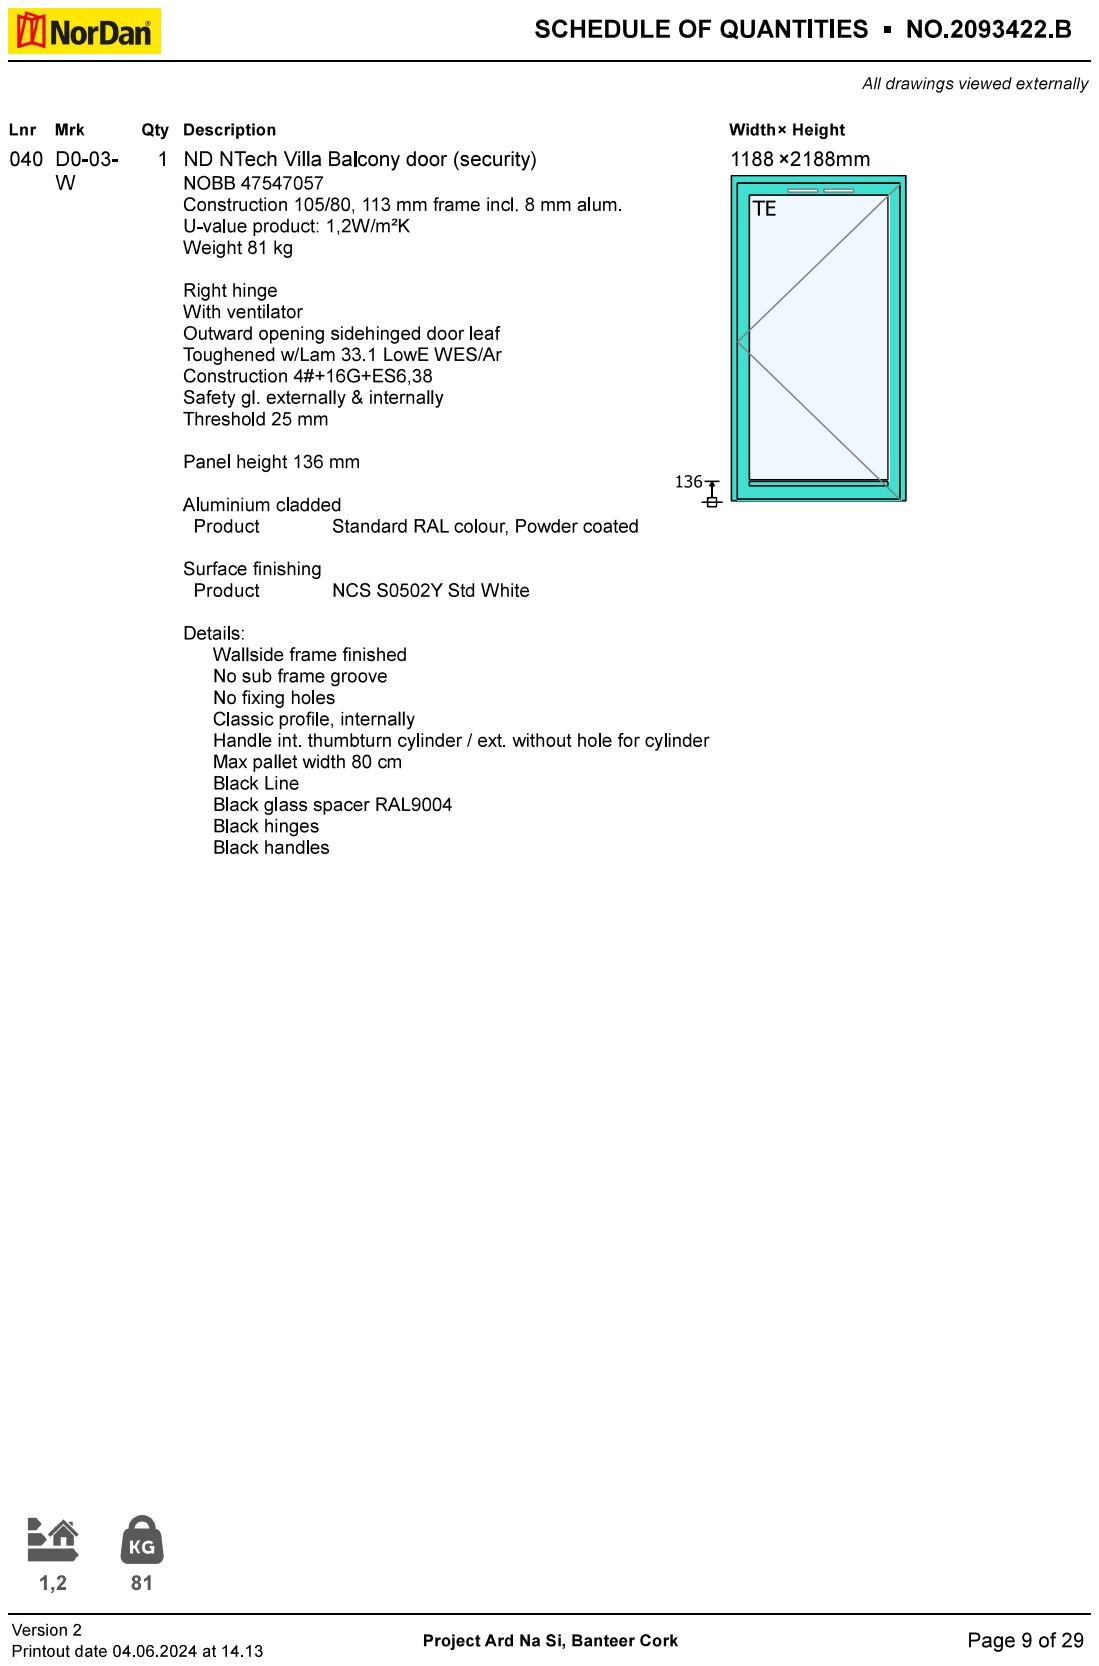
[picture p315: page 9]

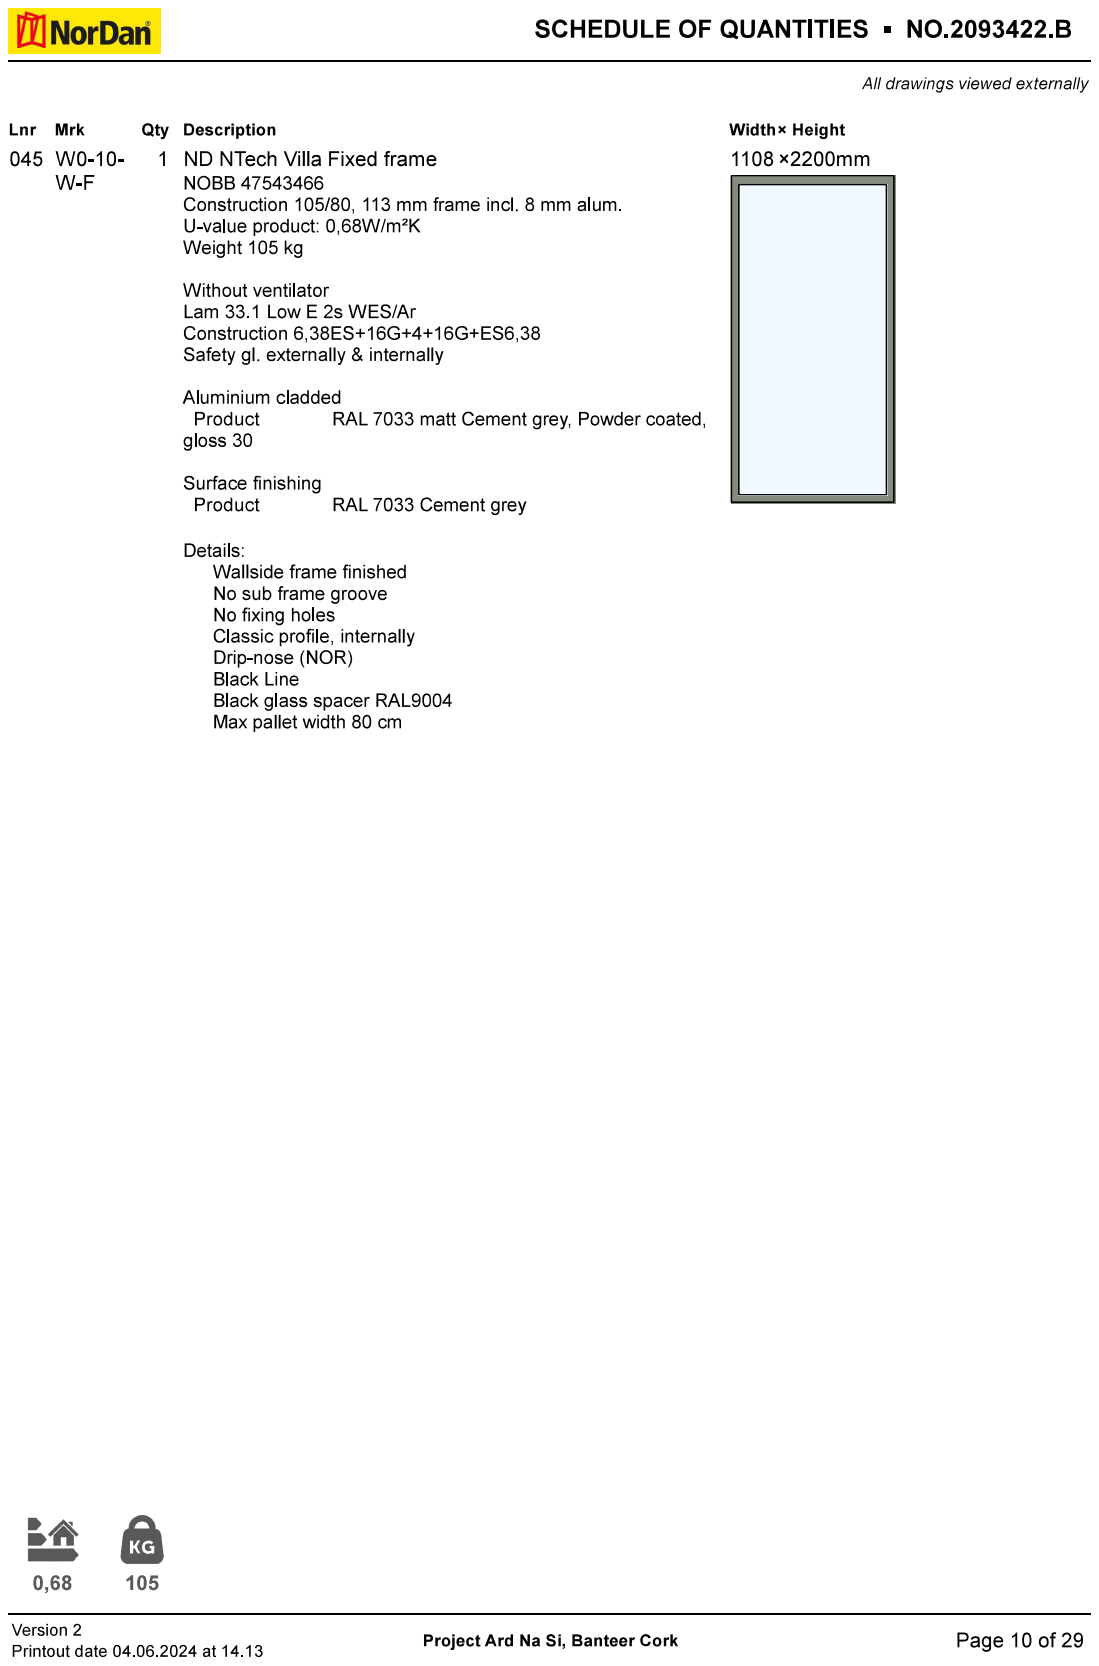
[picture p316: page 10]

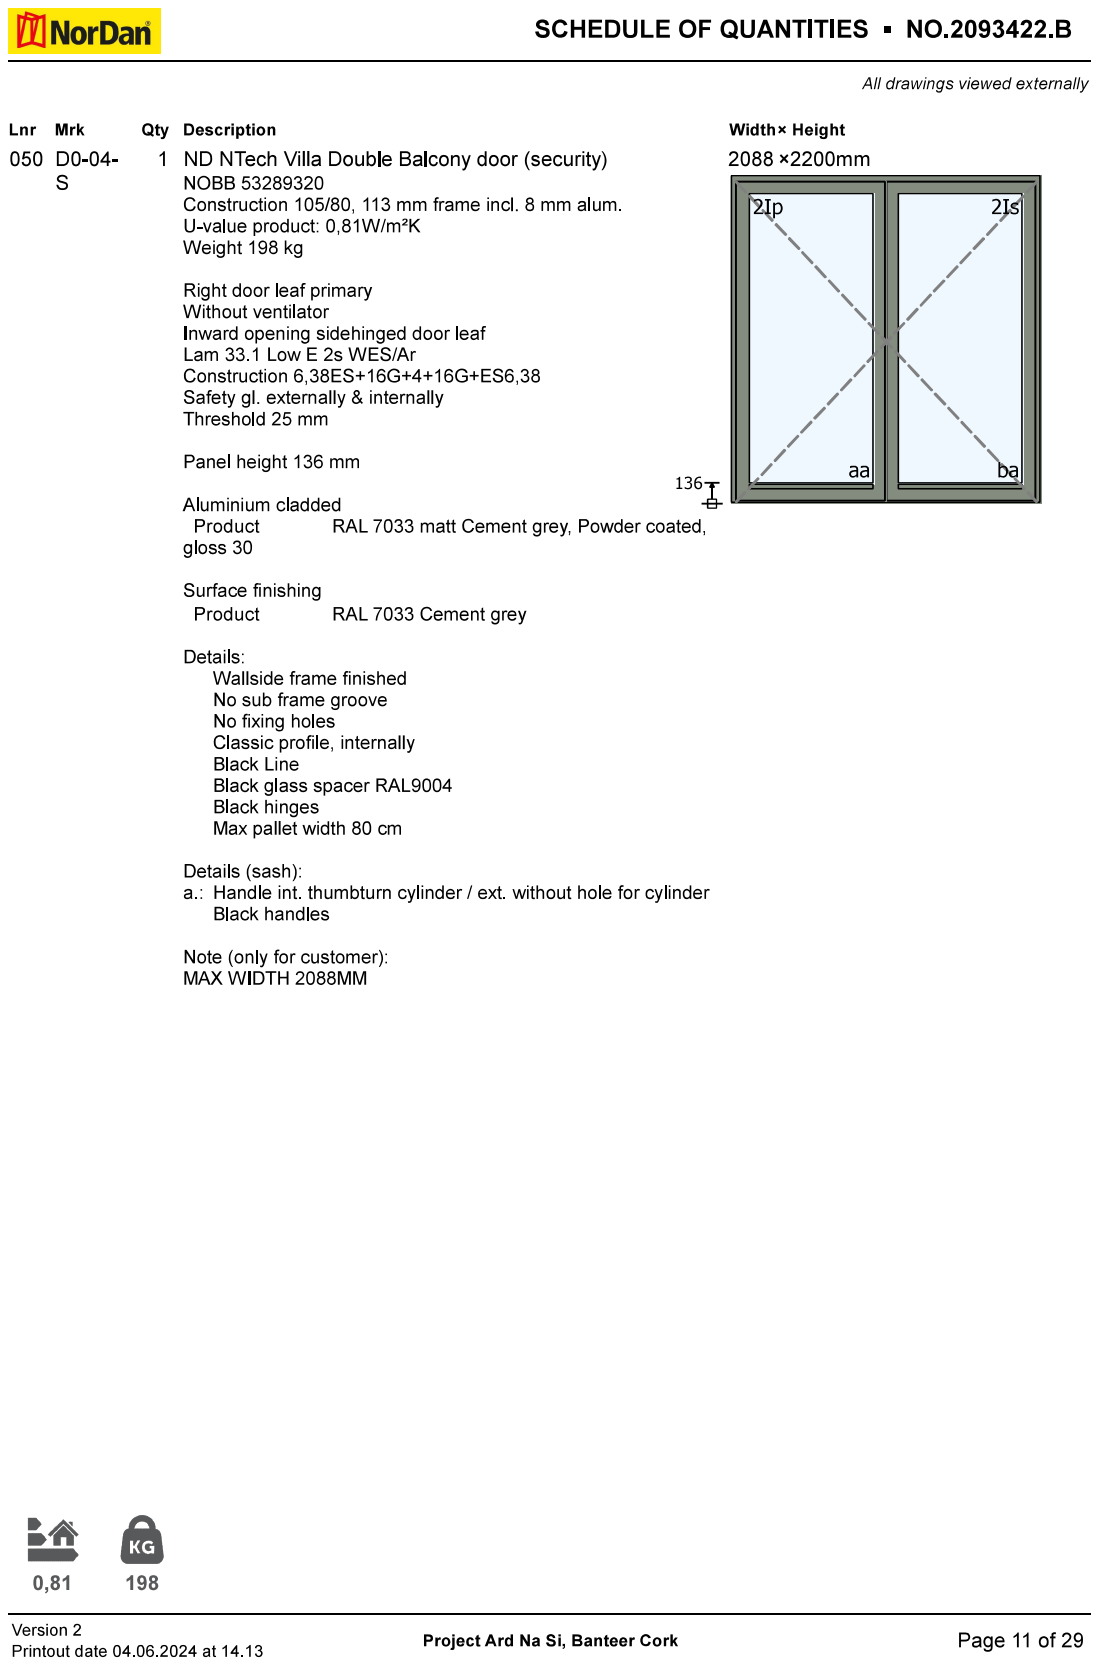
[picture p317: page 11]

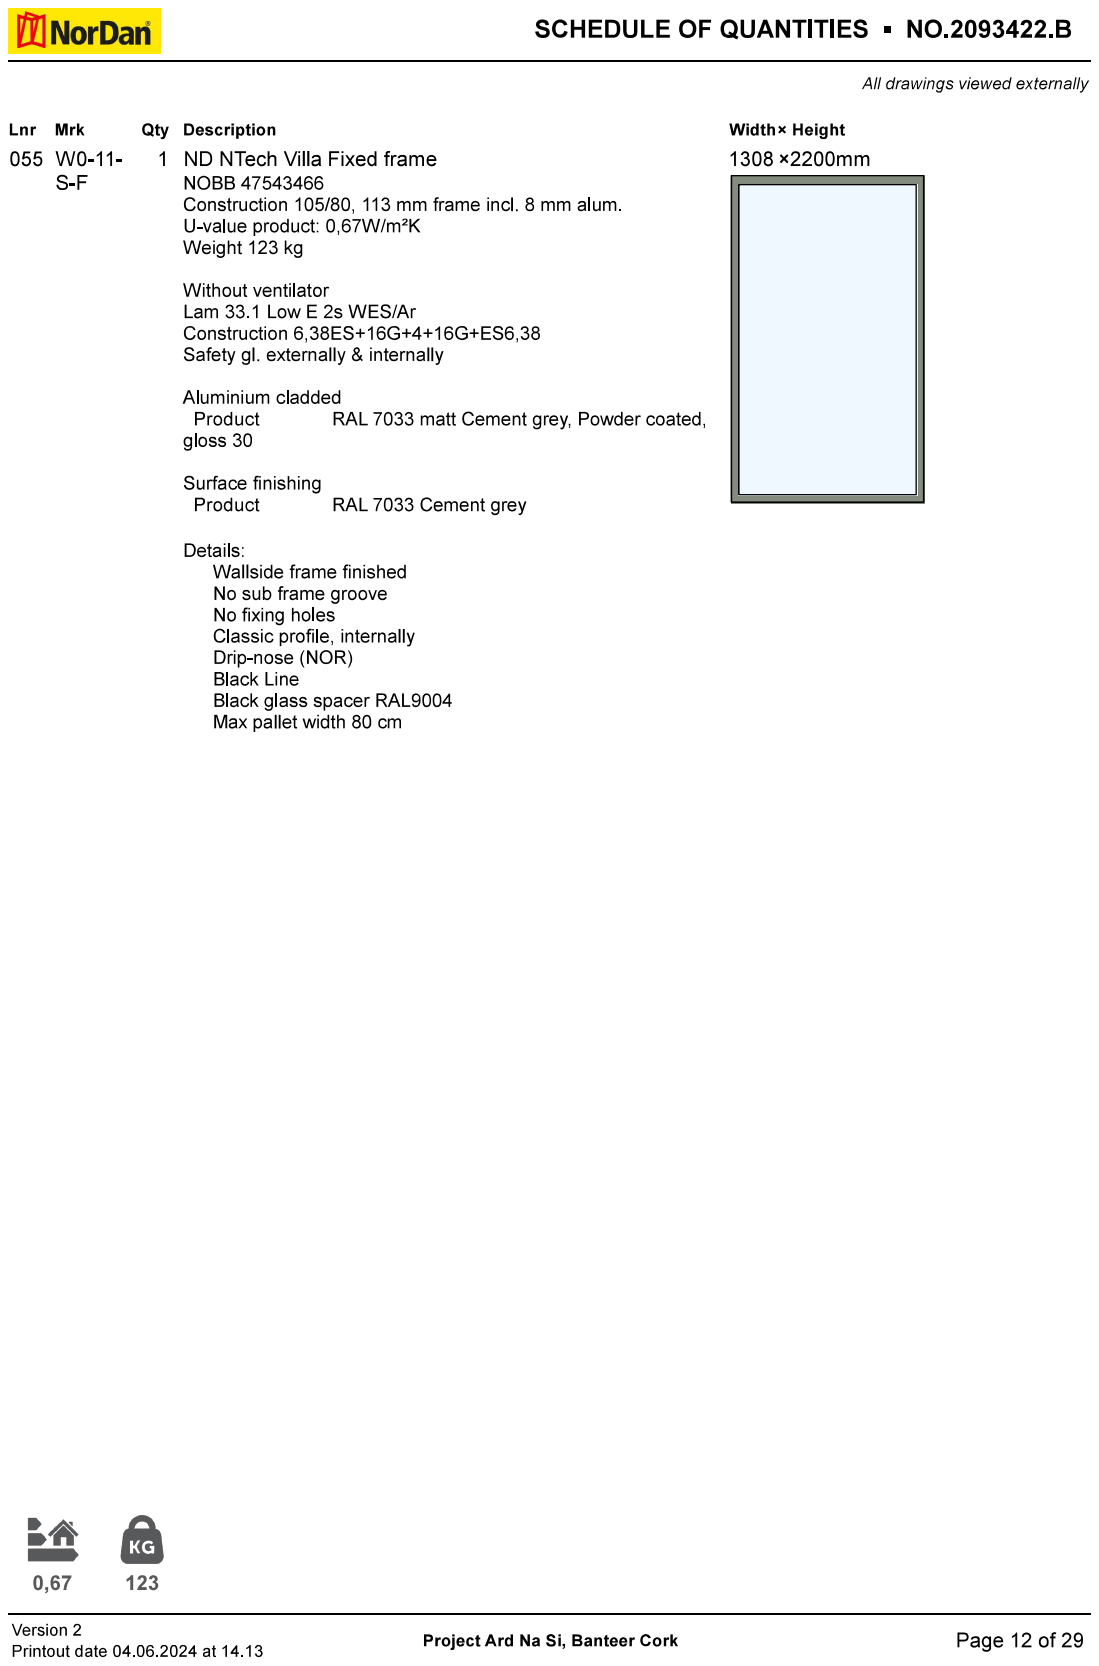
[picture p318: page 12]

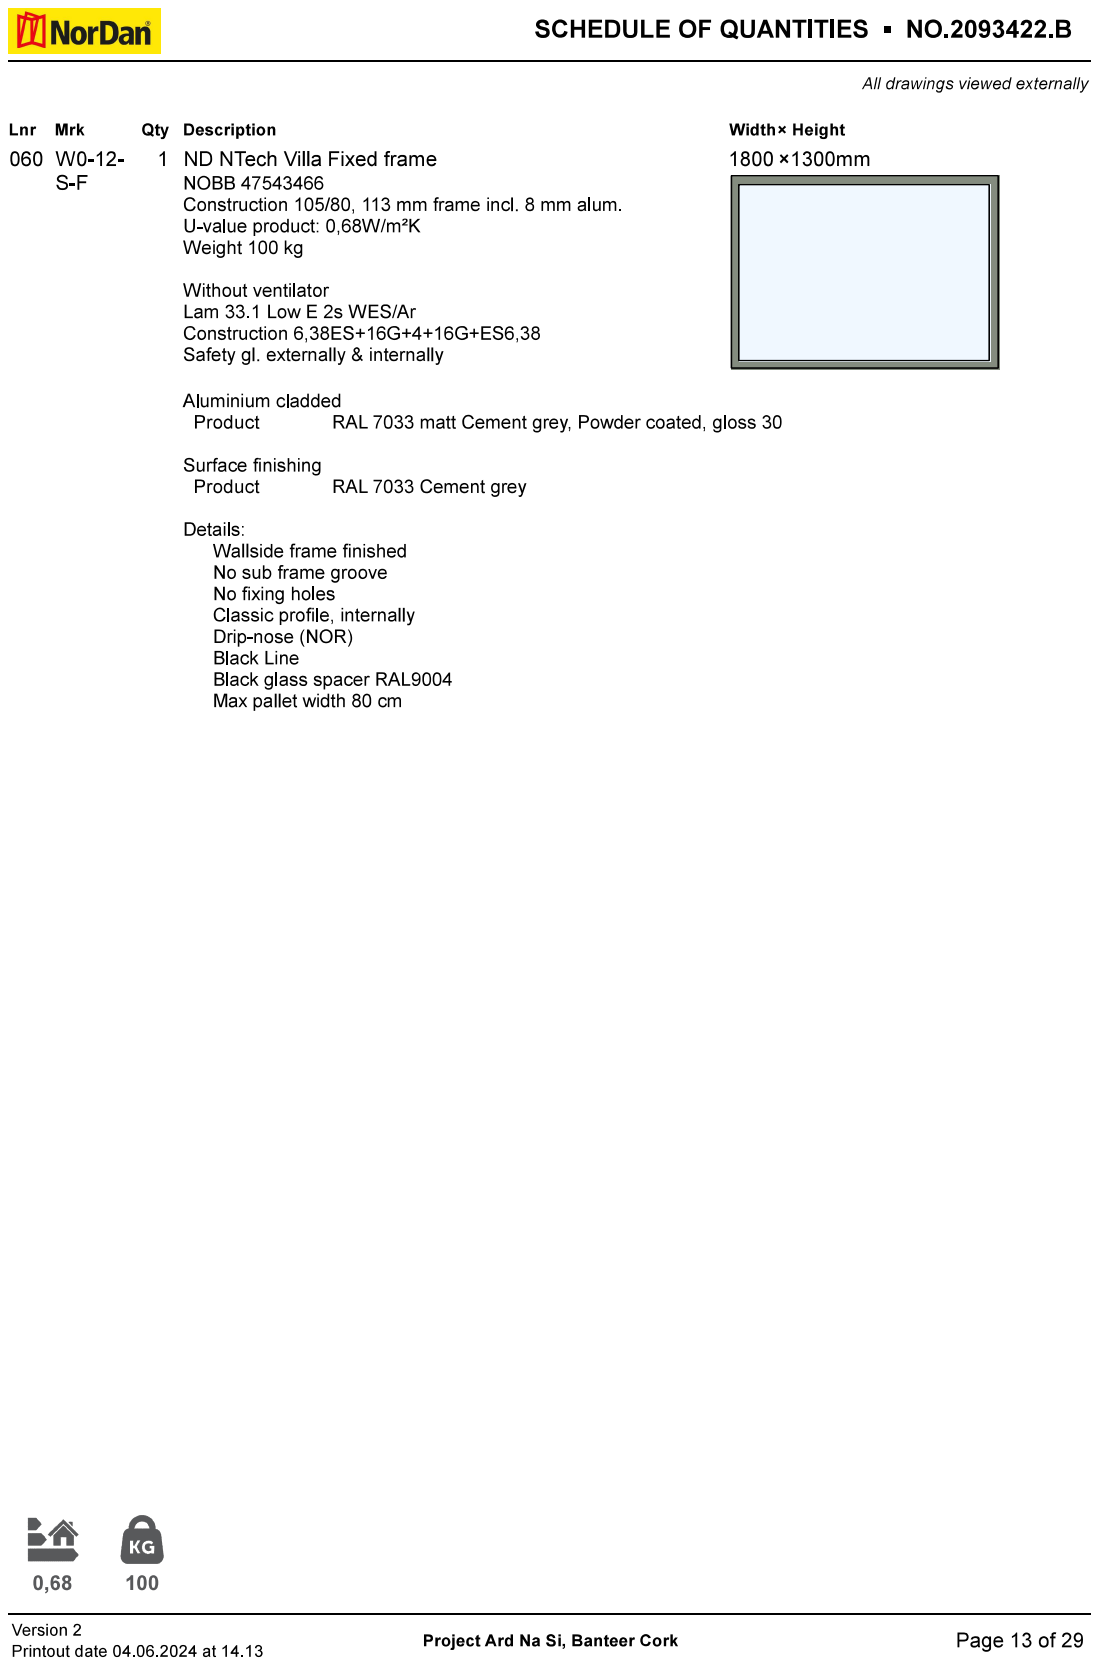
[picture p319: page 13]

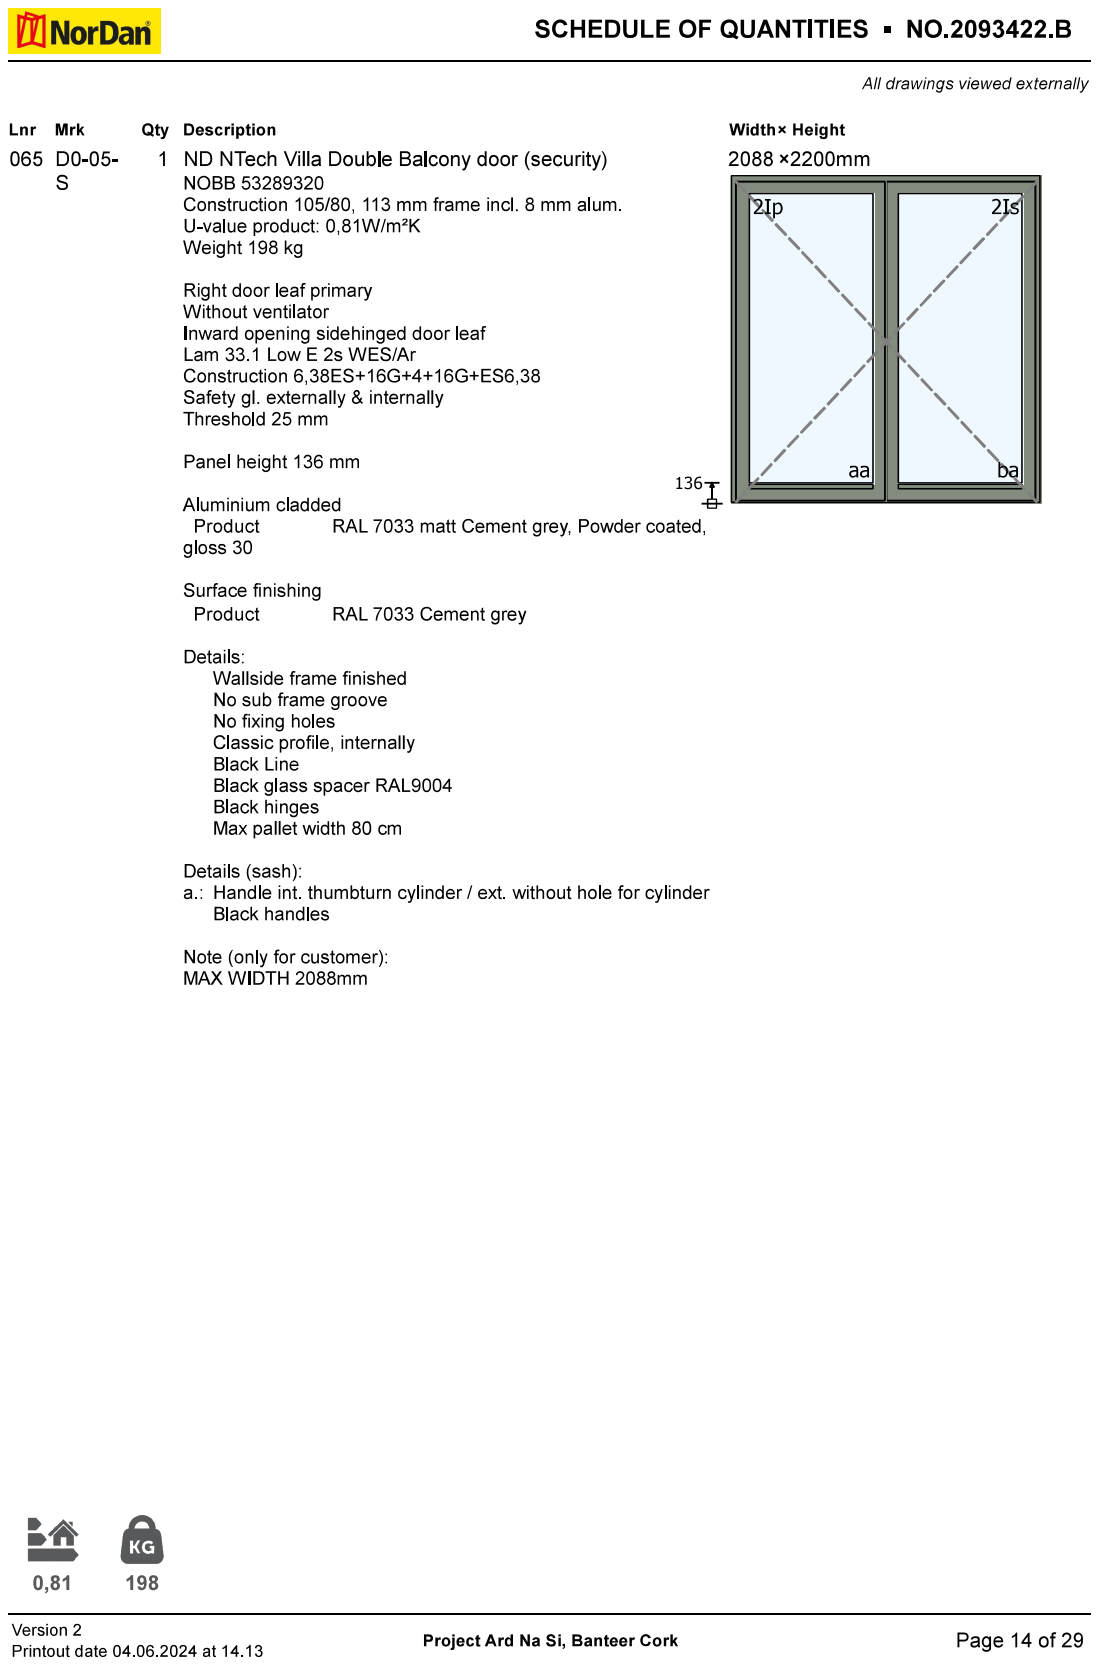
[picture p320: page 14]

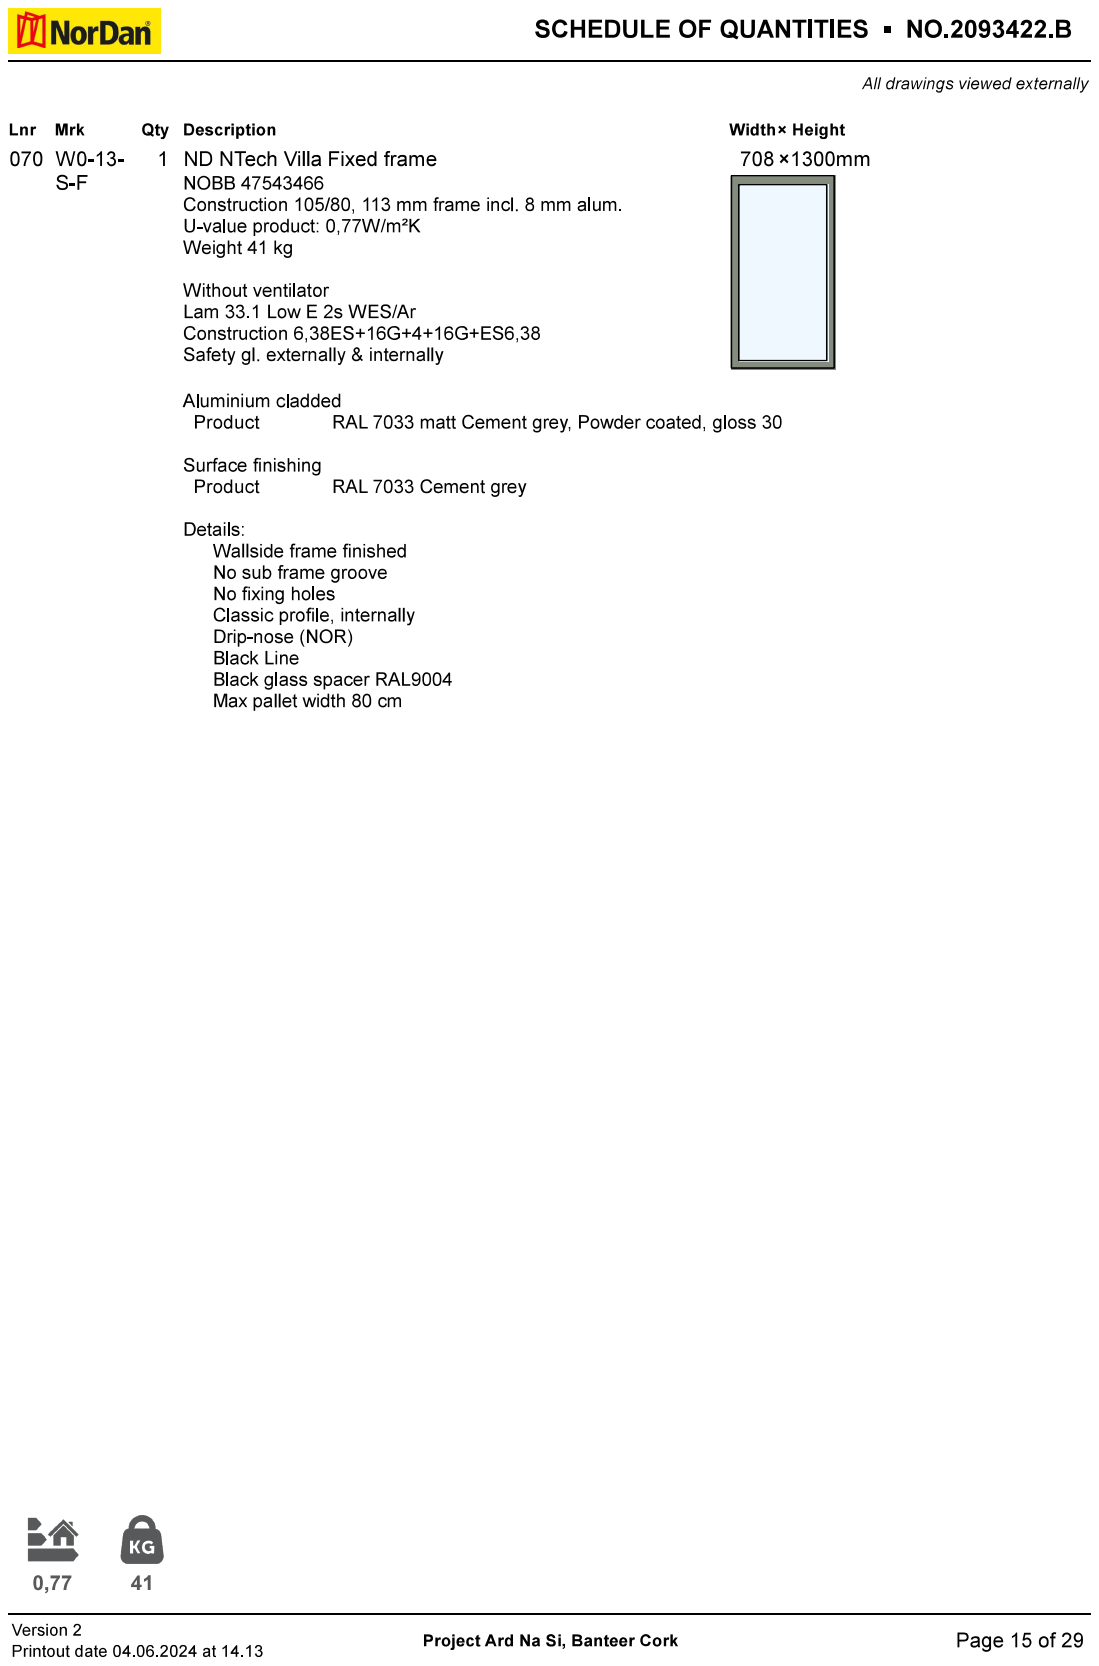
[picture p321: page 15]

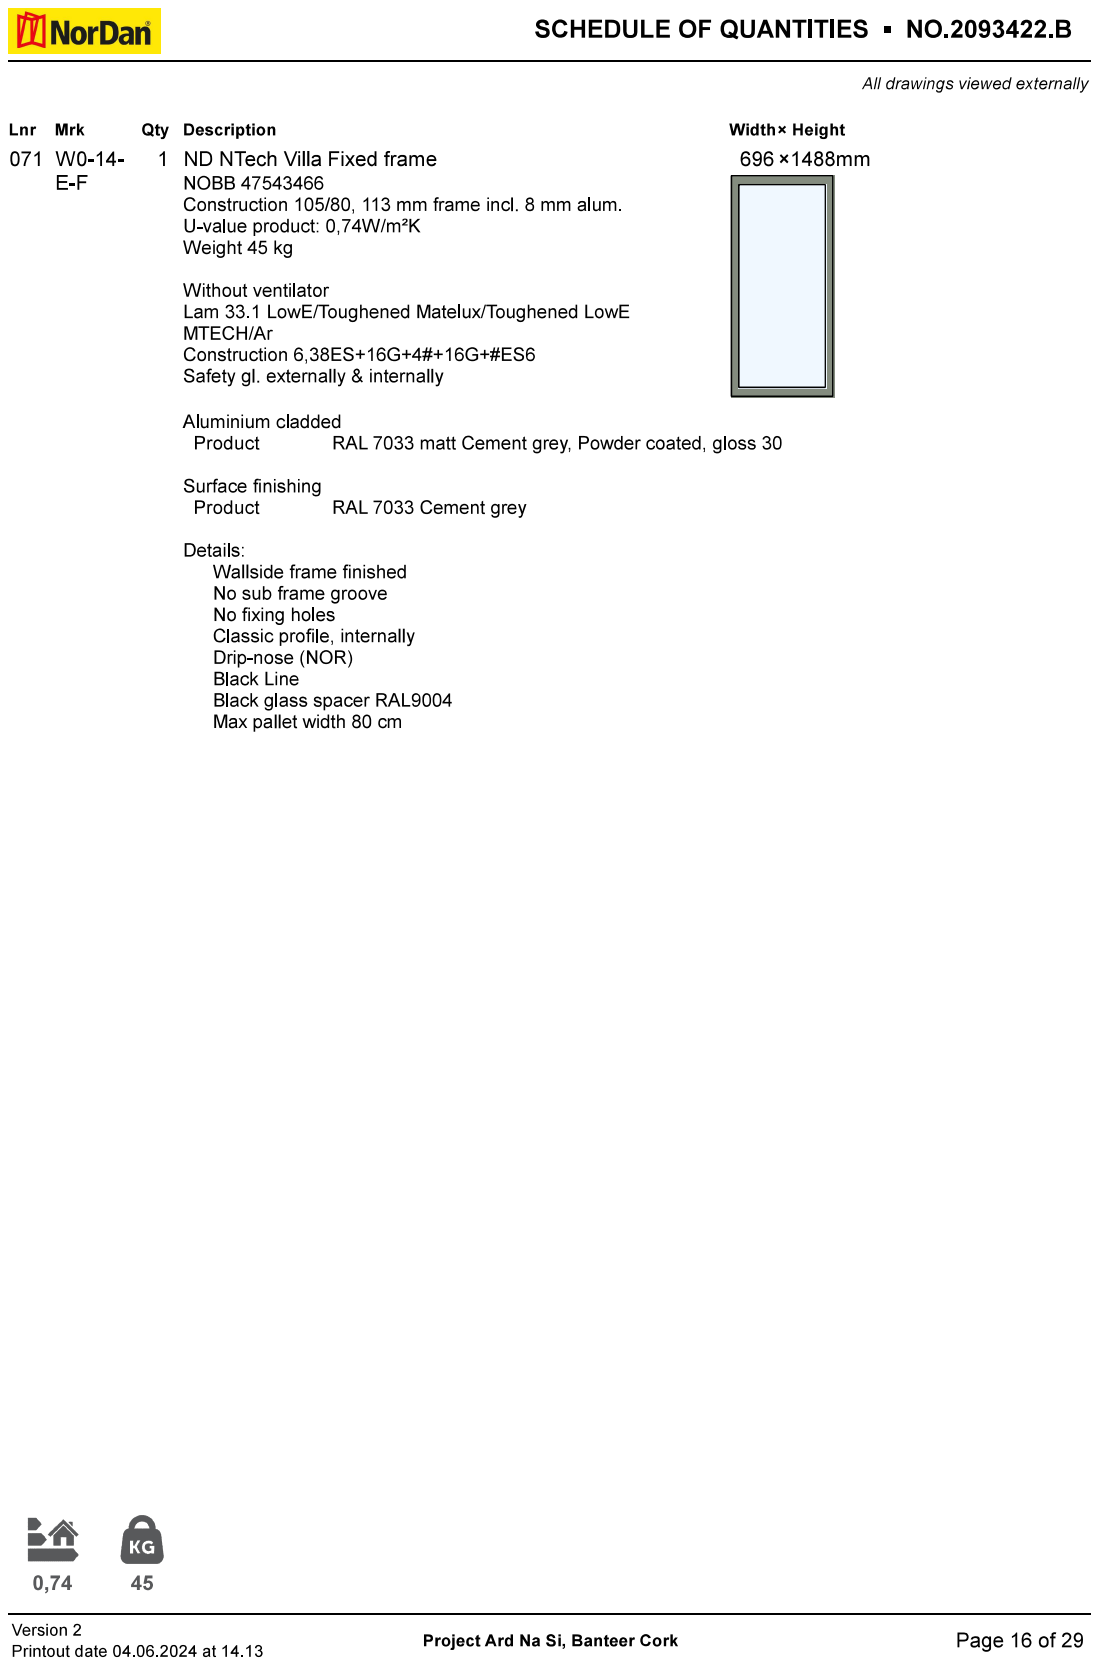
[picture p322: page 16]

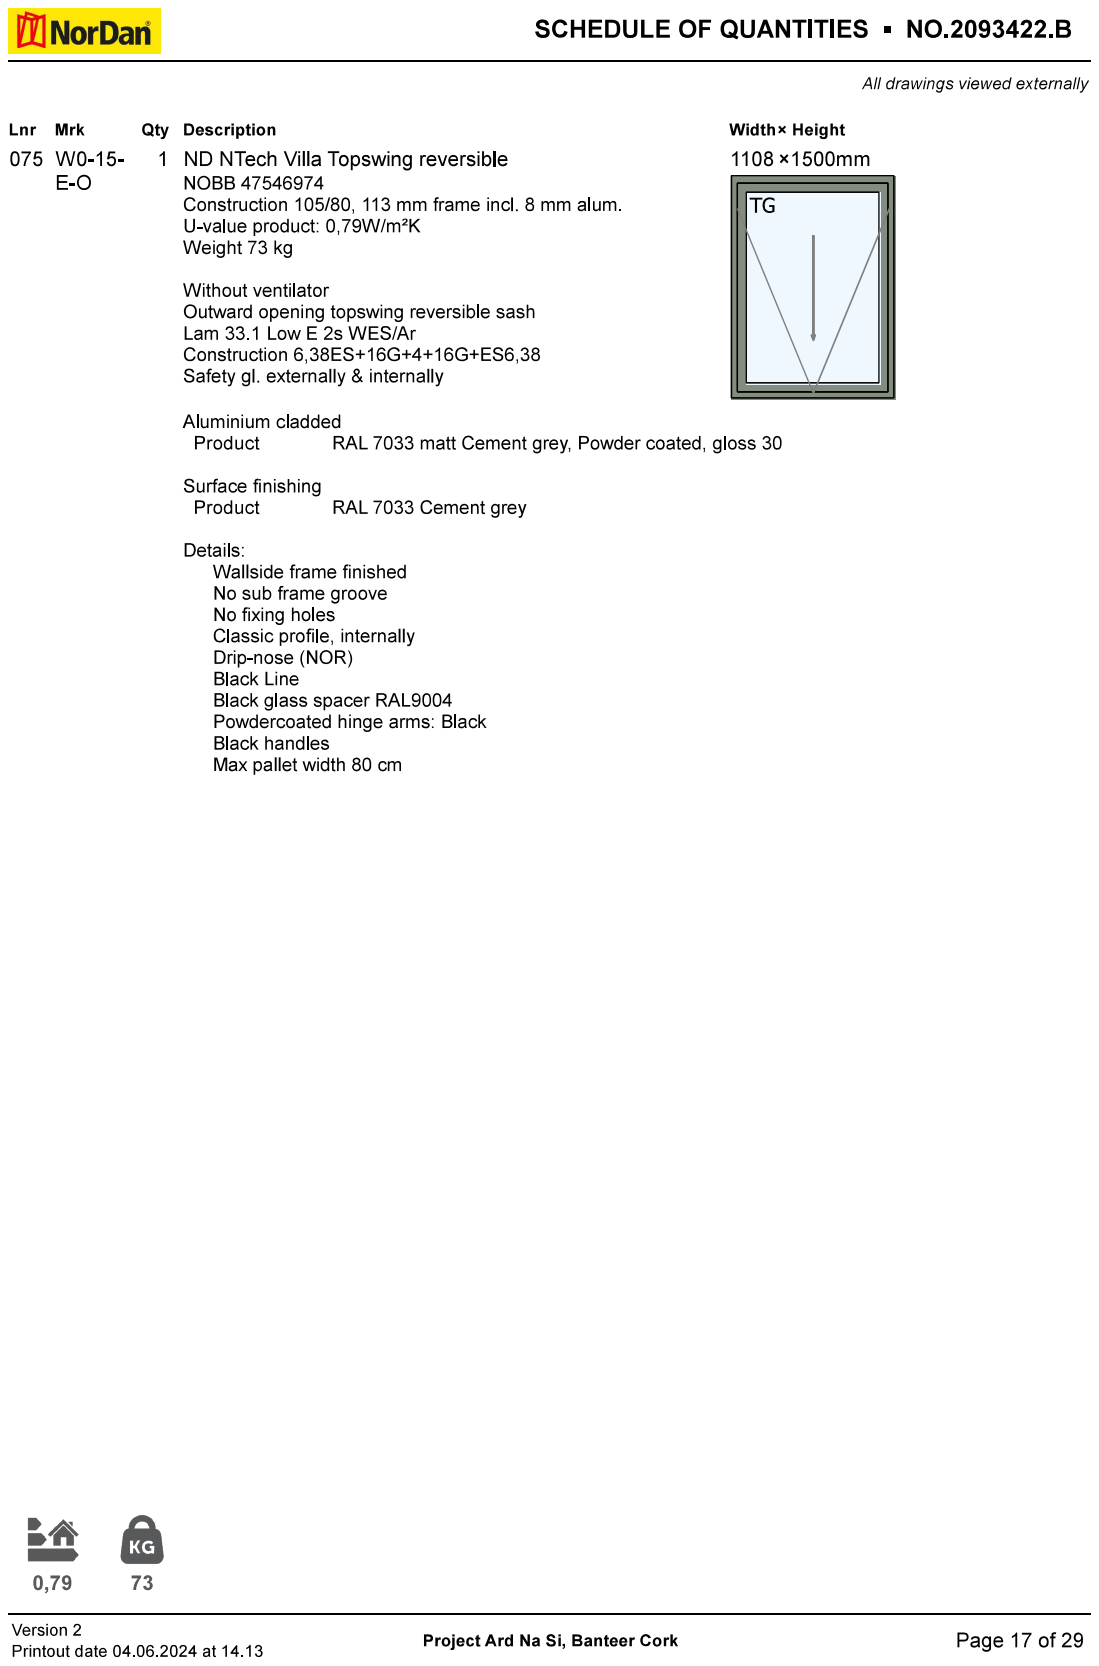
[picture p323: page 17]

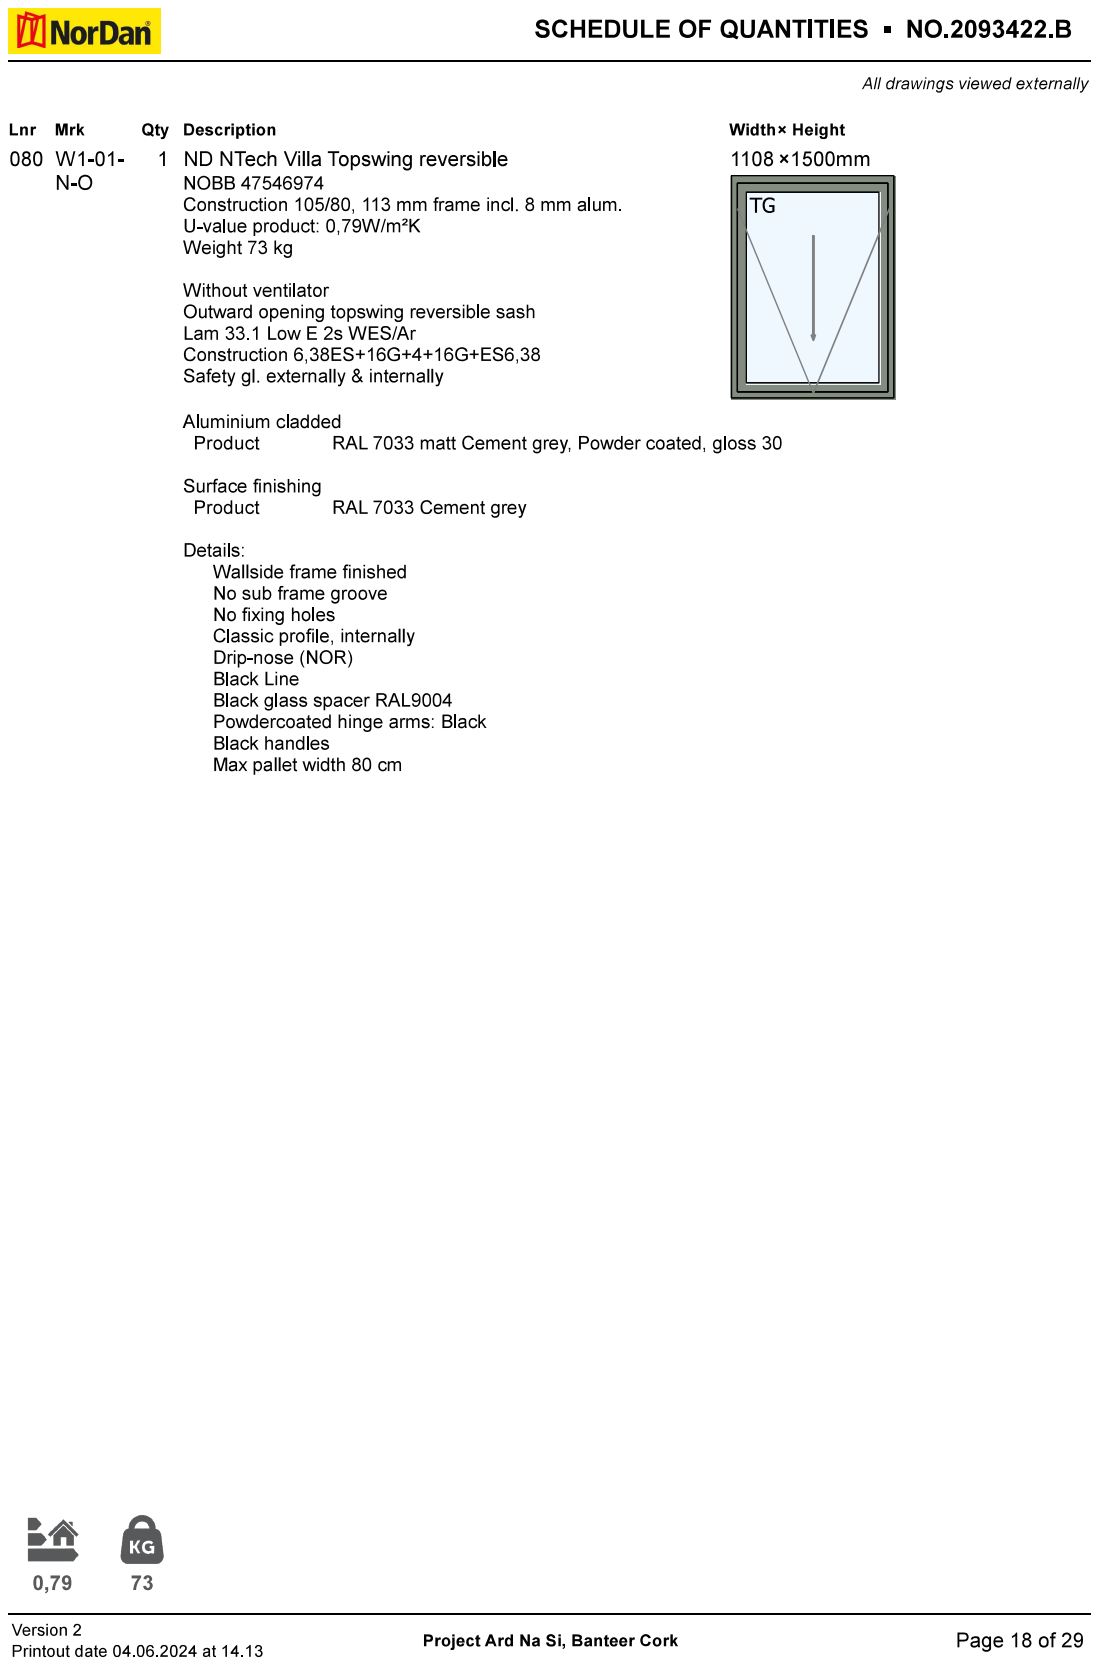
[picture p324: page 18]

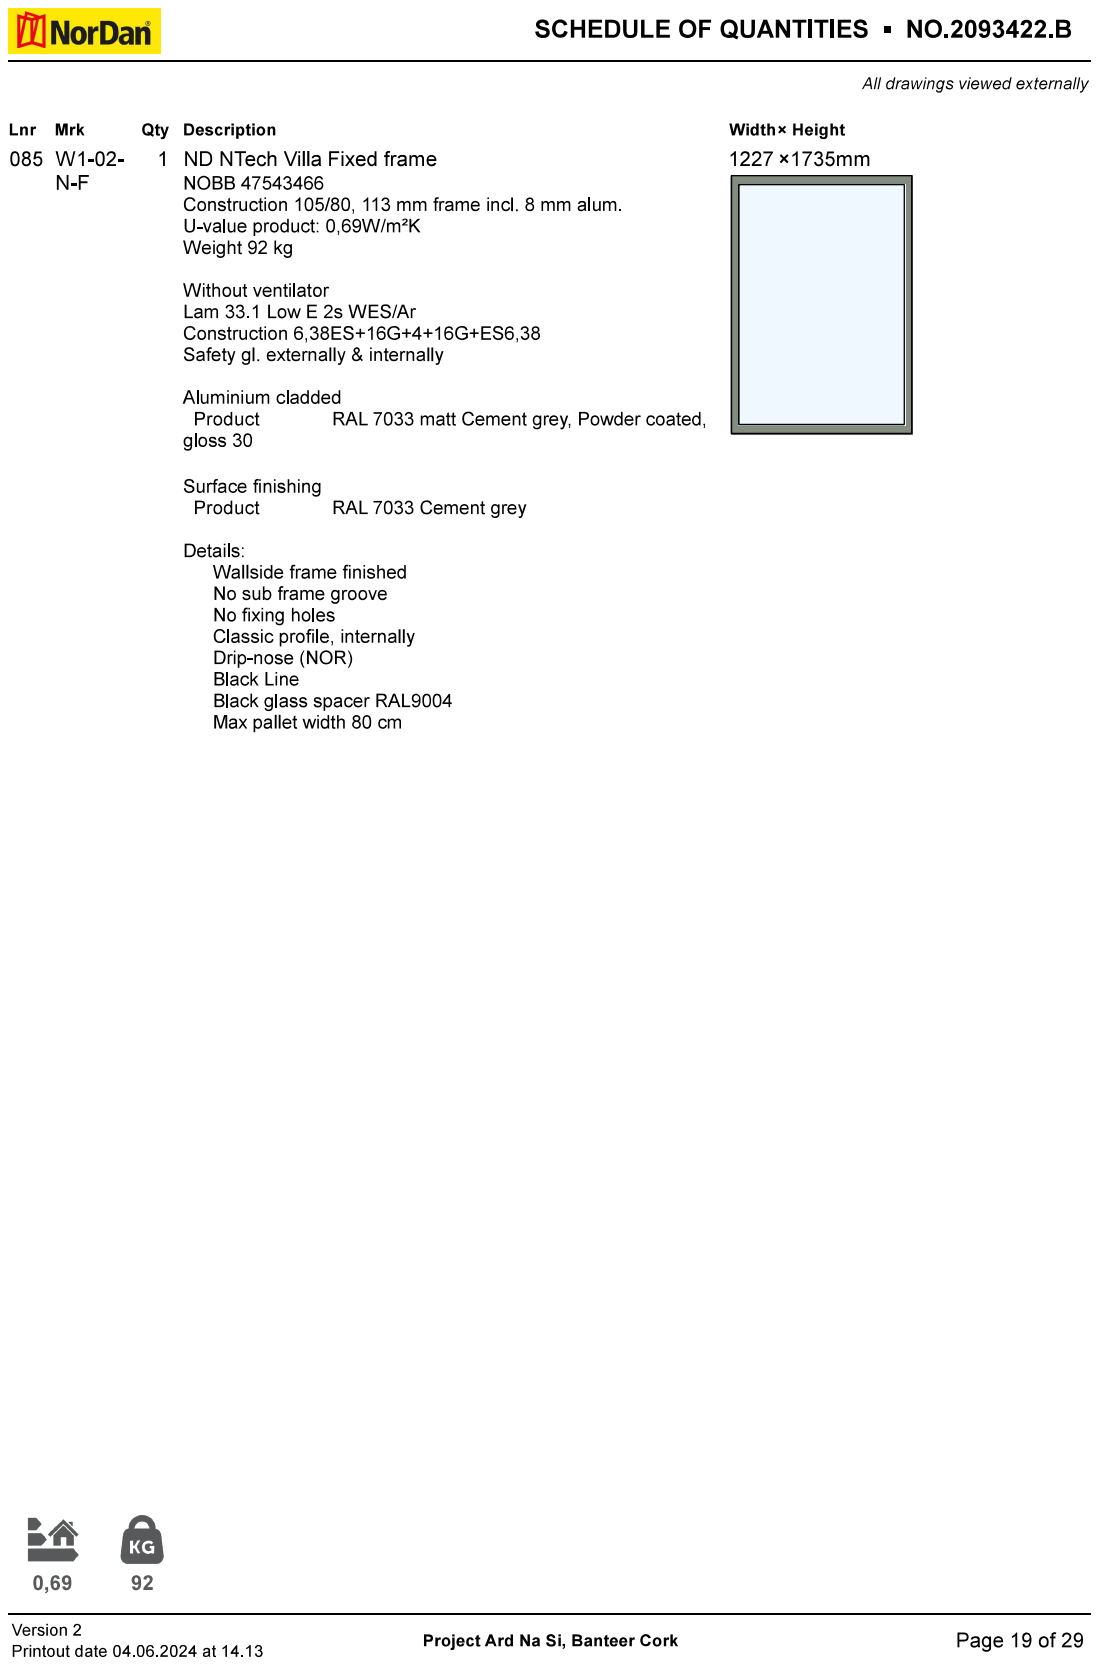
[picture p325: page 19]

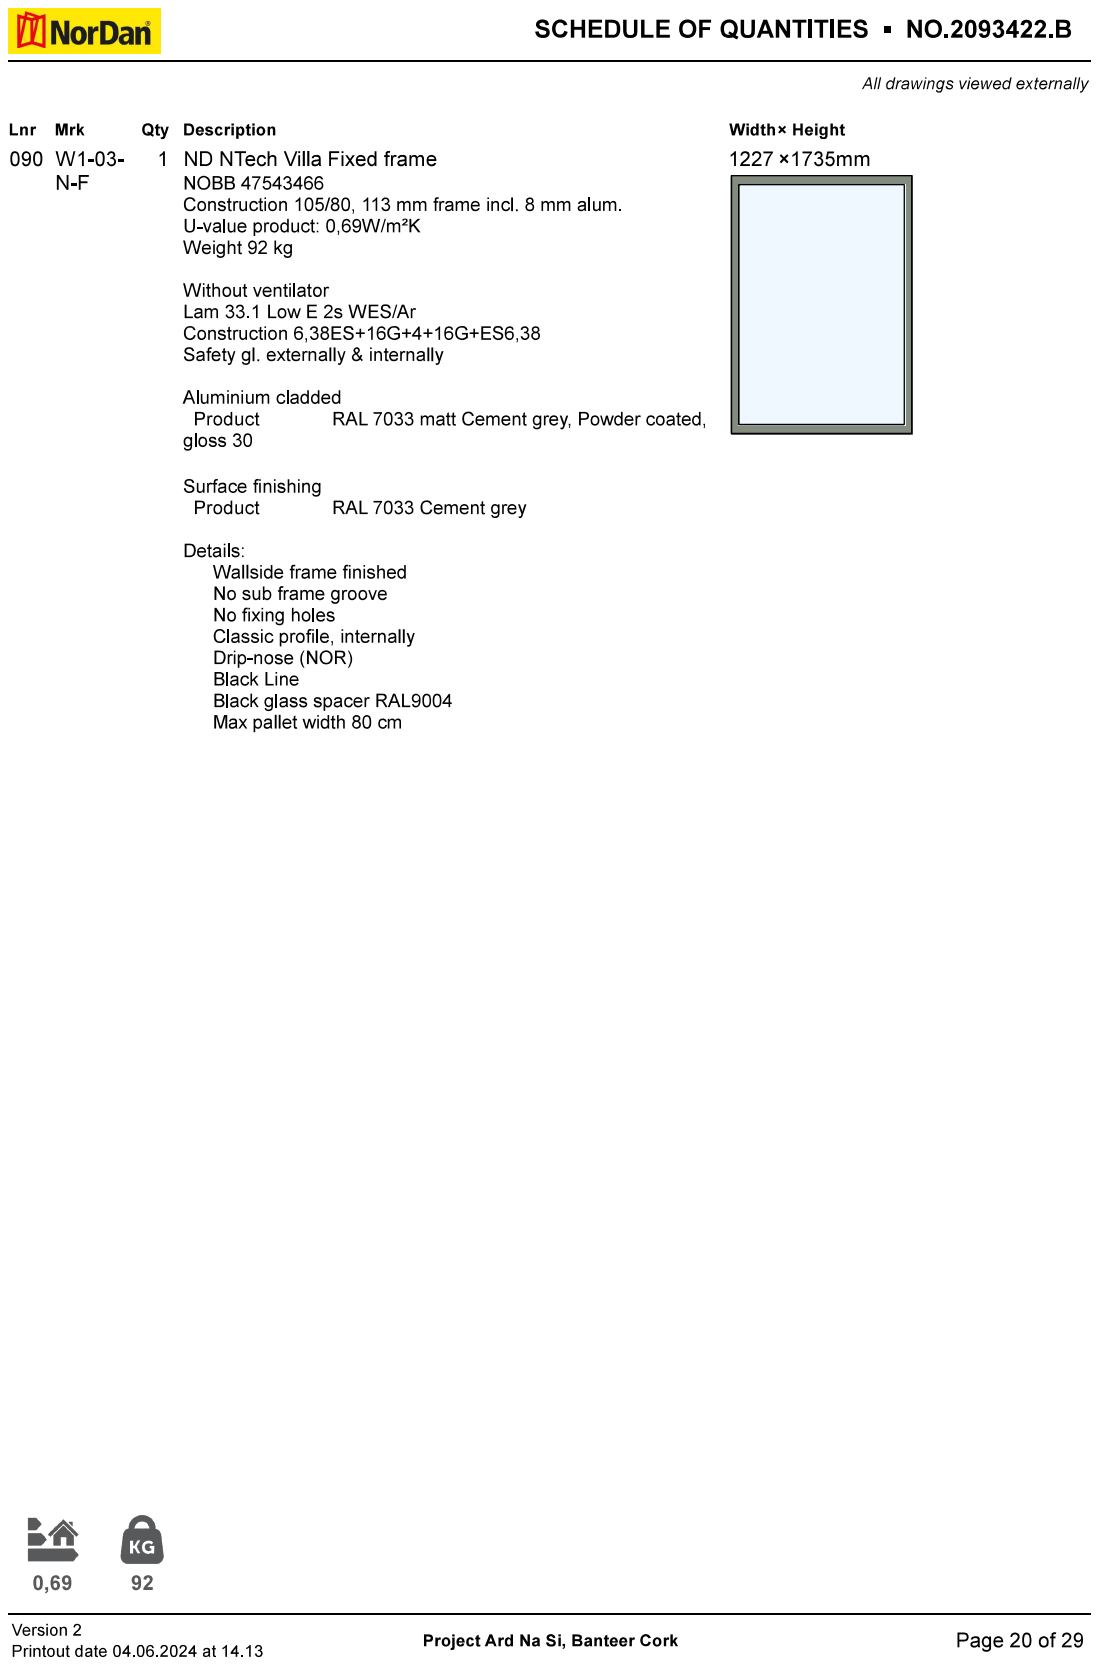
[picture p326: page 20]

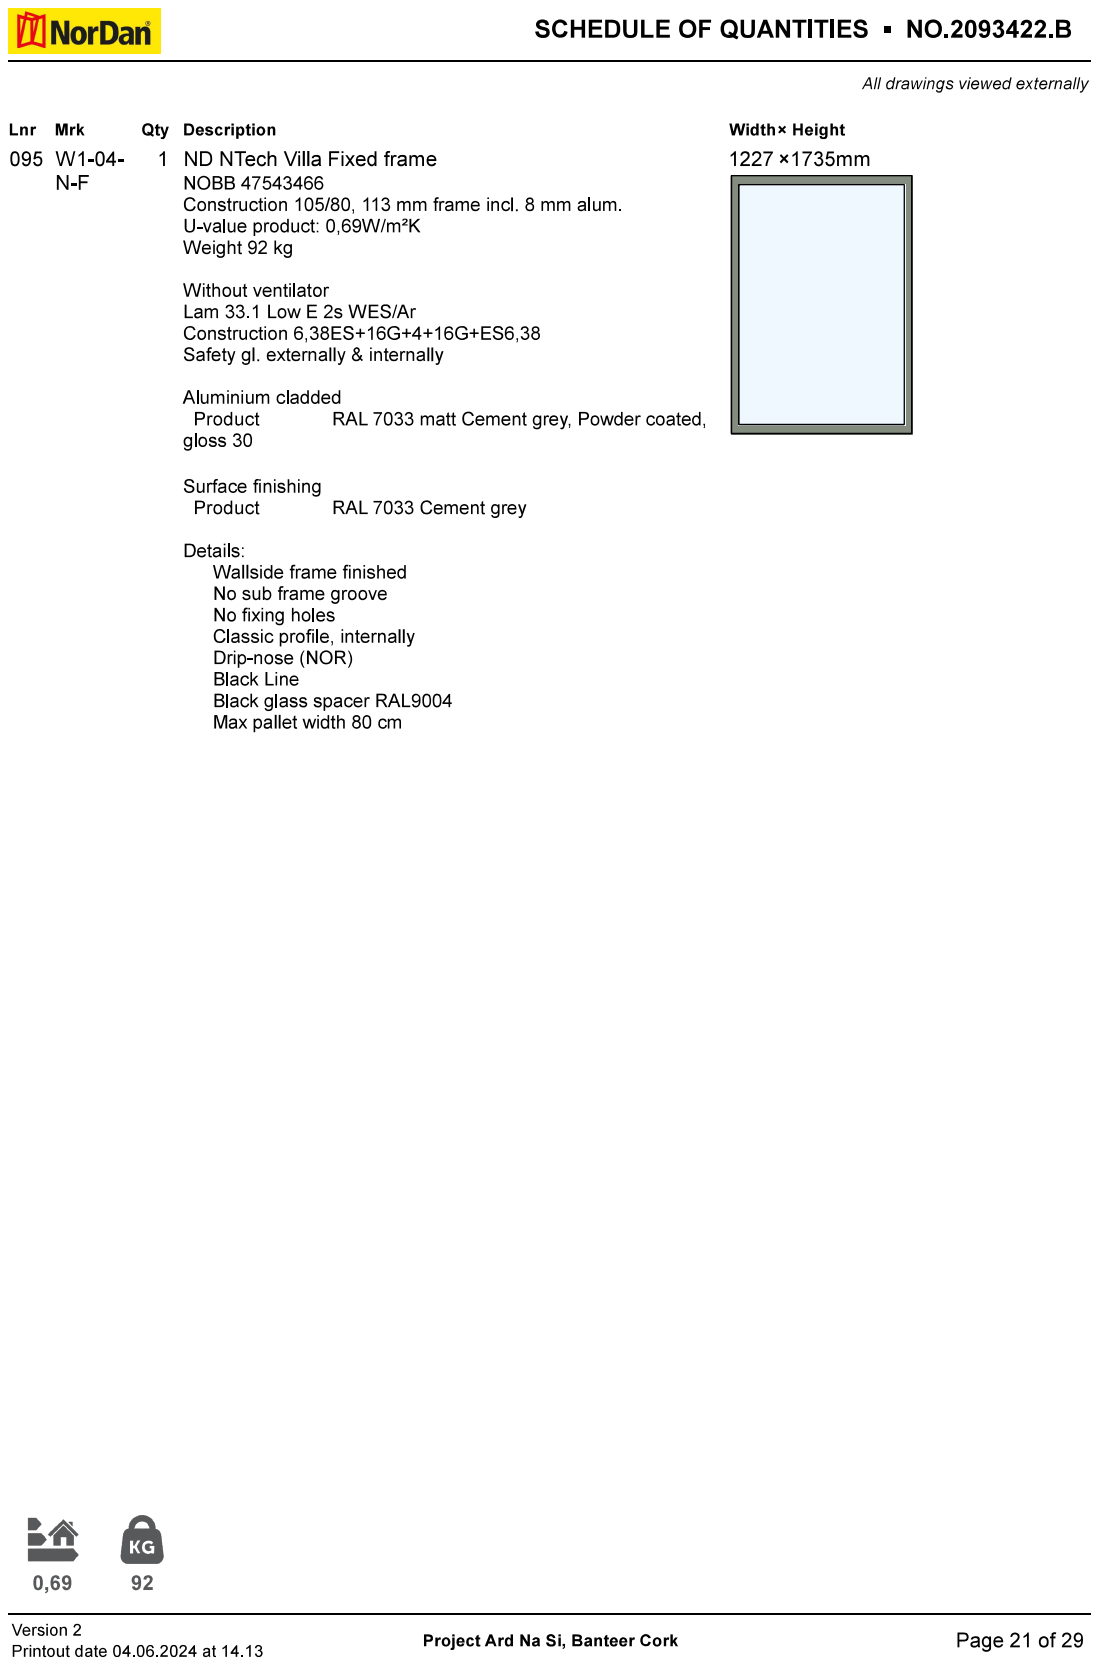
[picture p327: page 21]

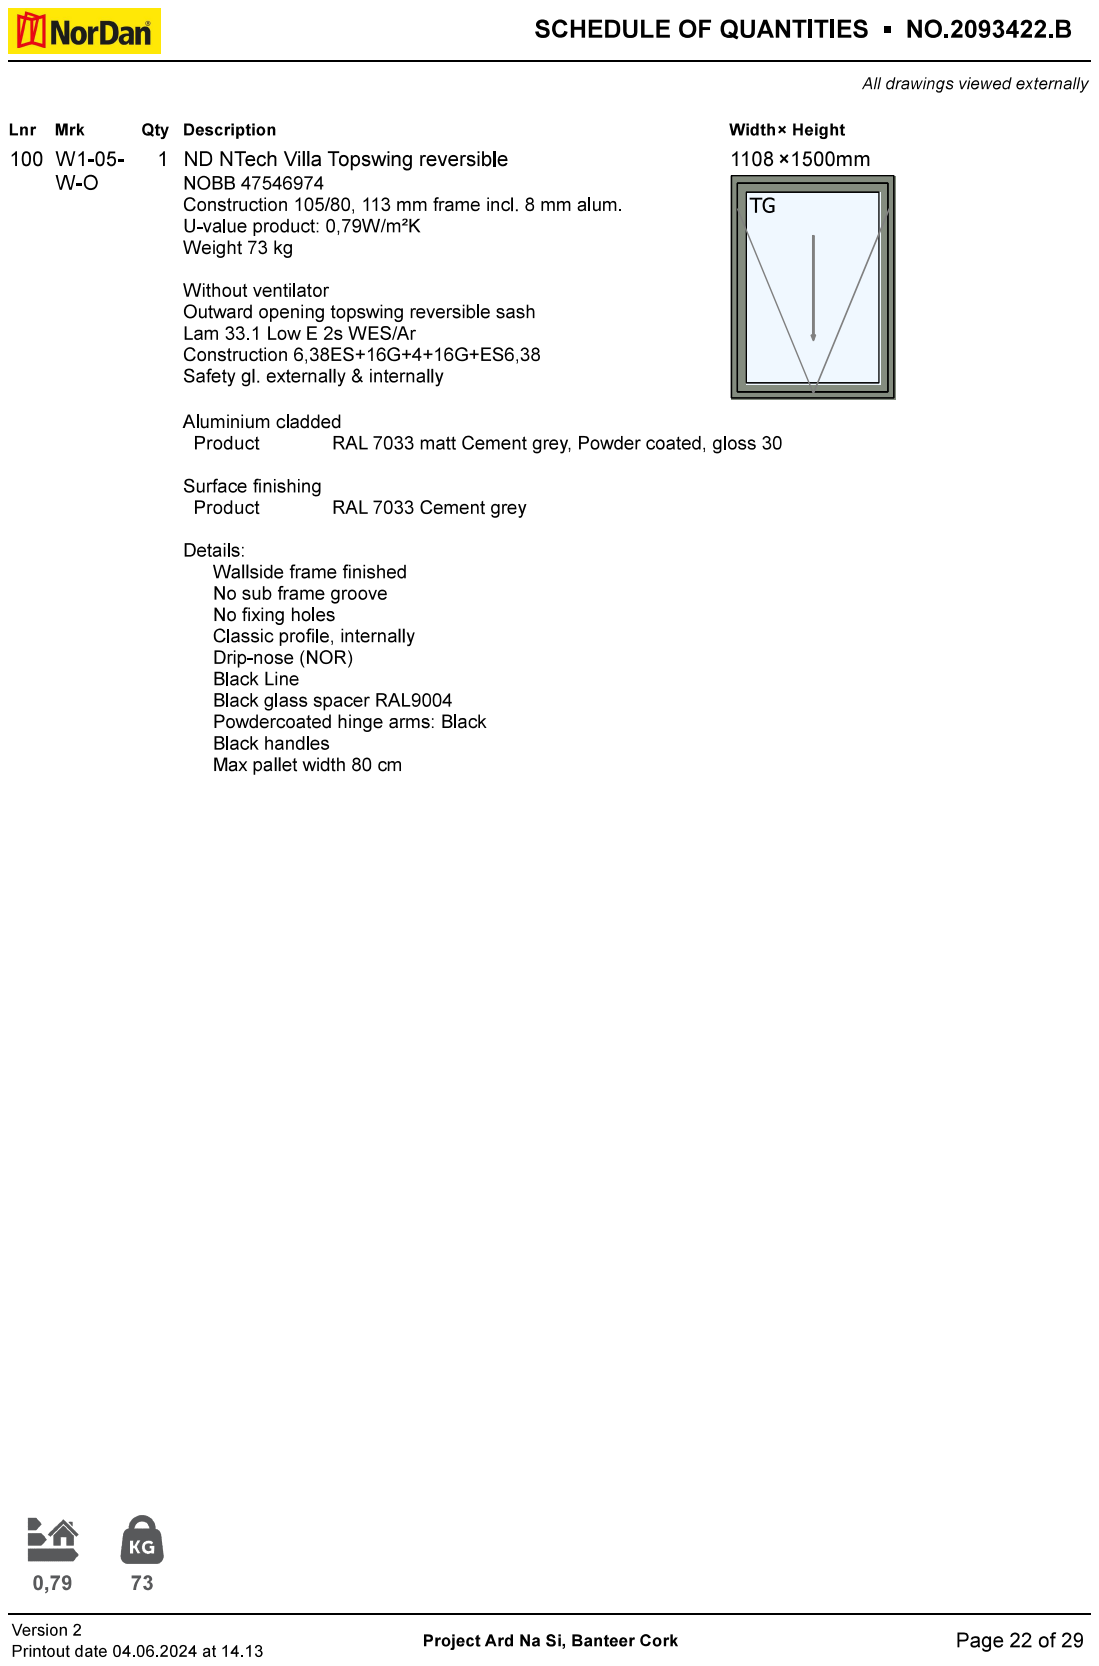
[picture p328: page 22]

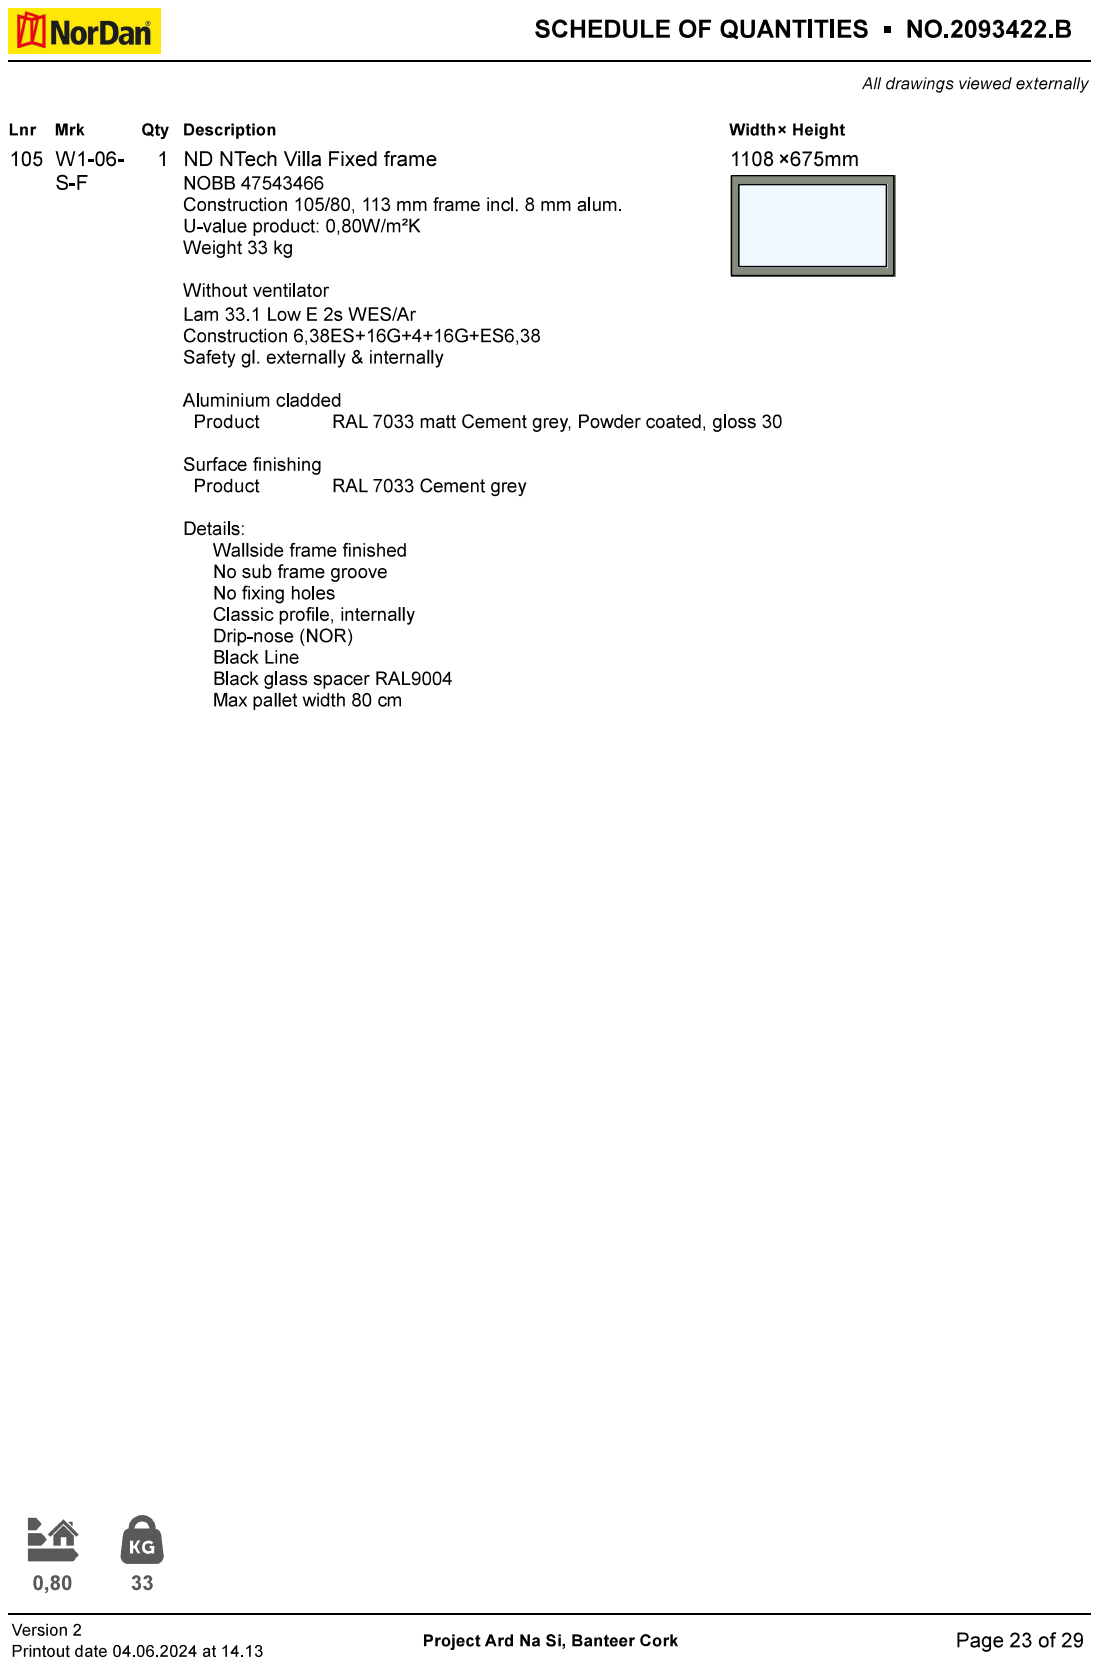
[picture p329: page 23]

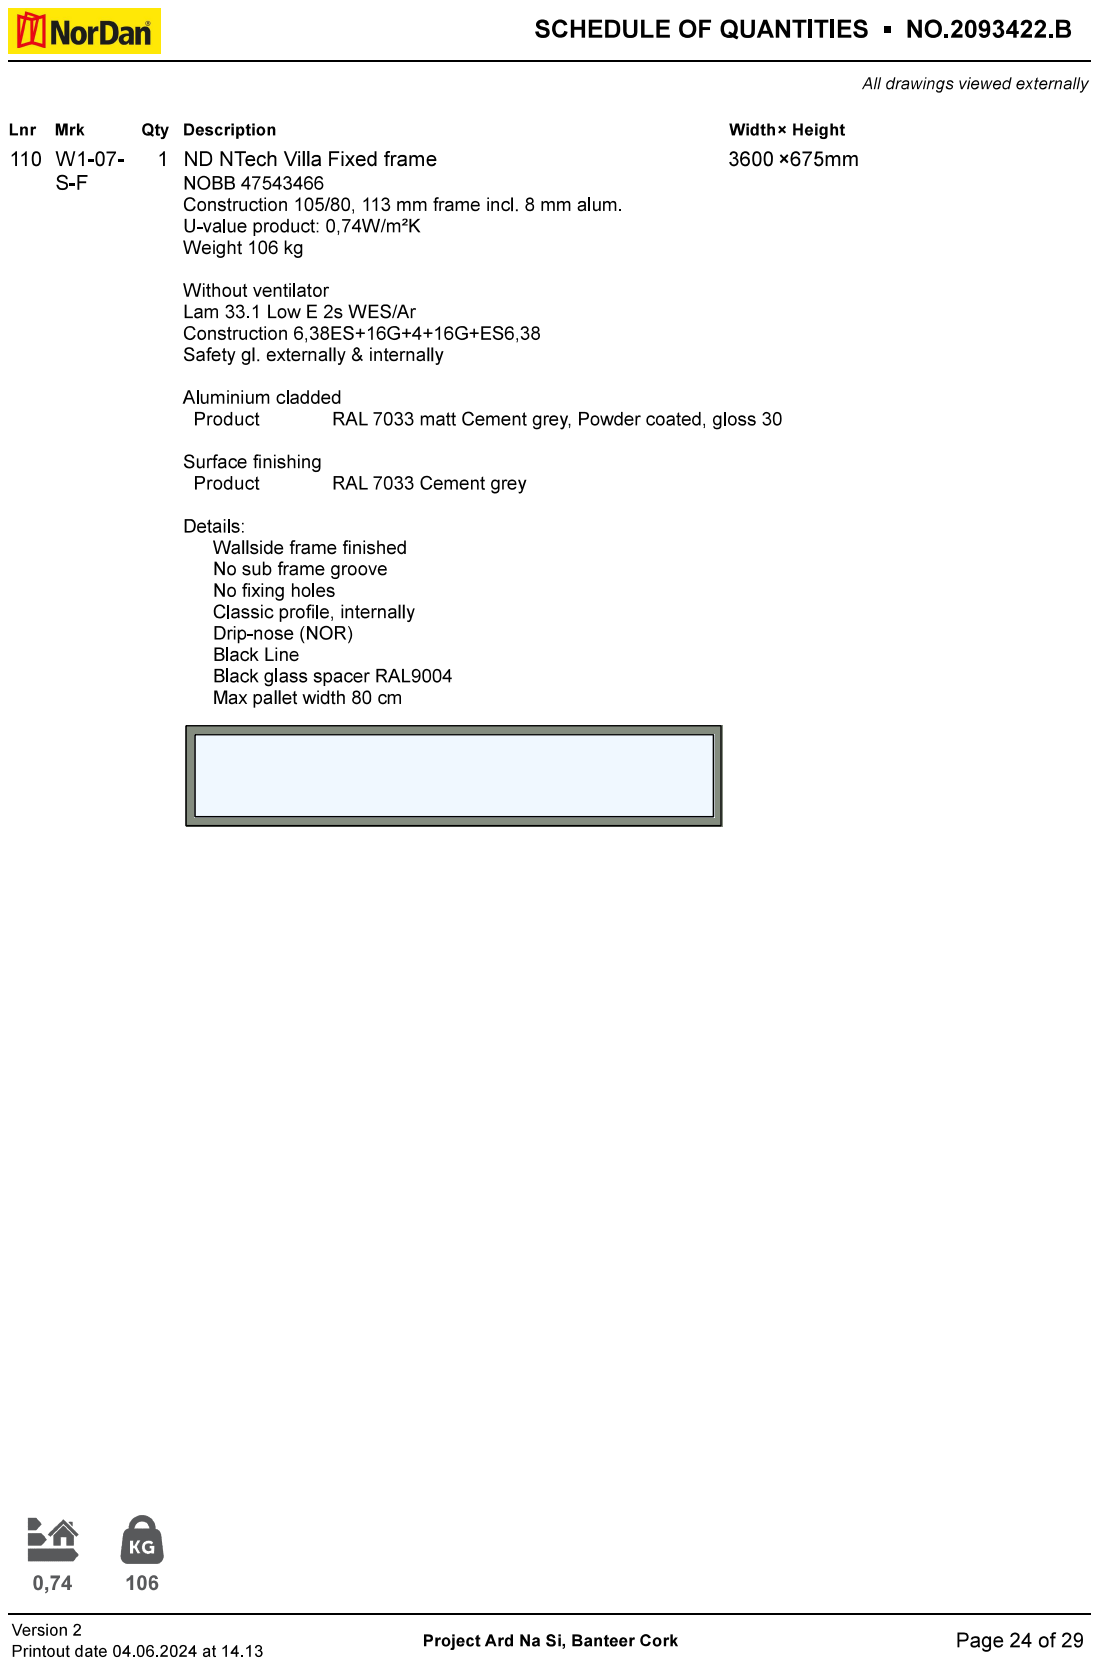
[picture p330: page 24]

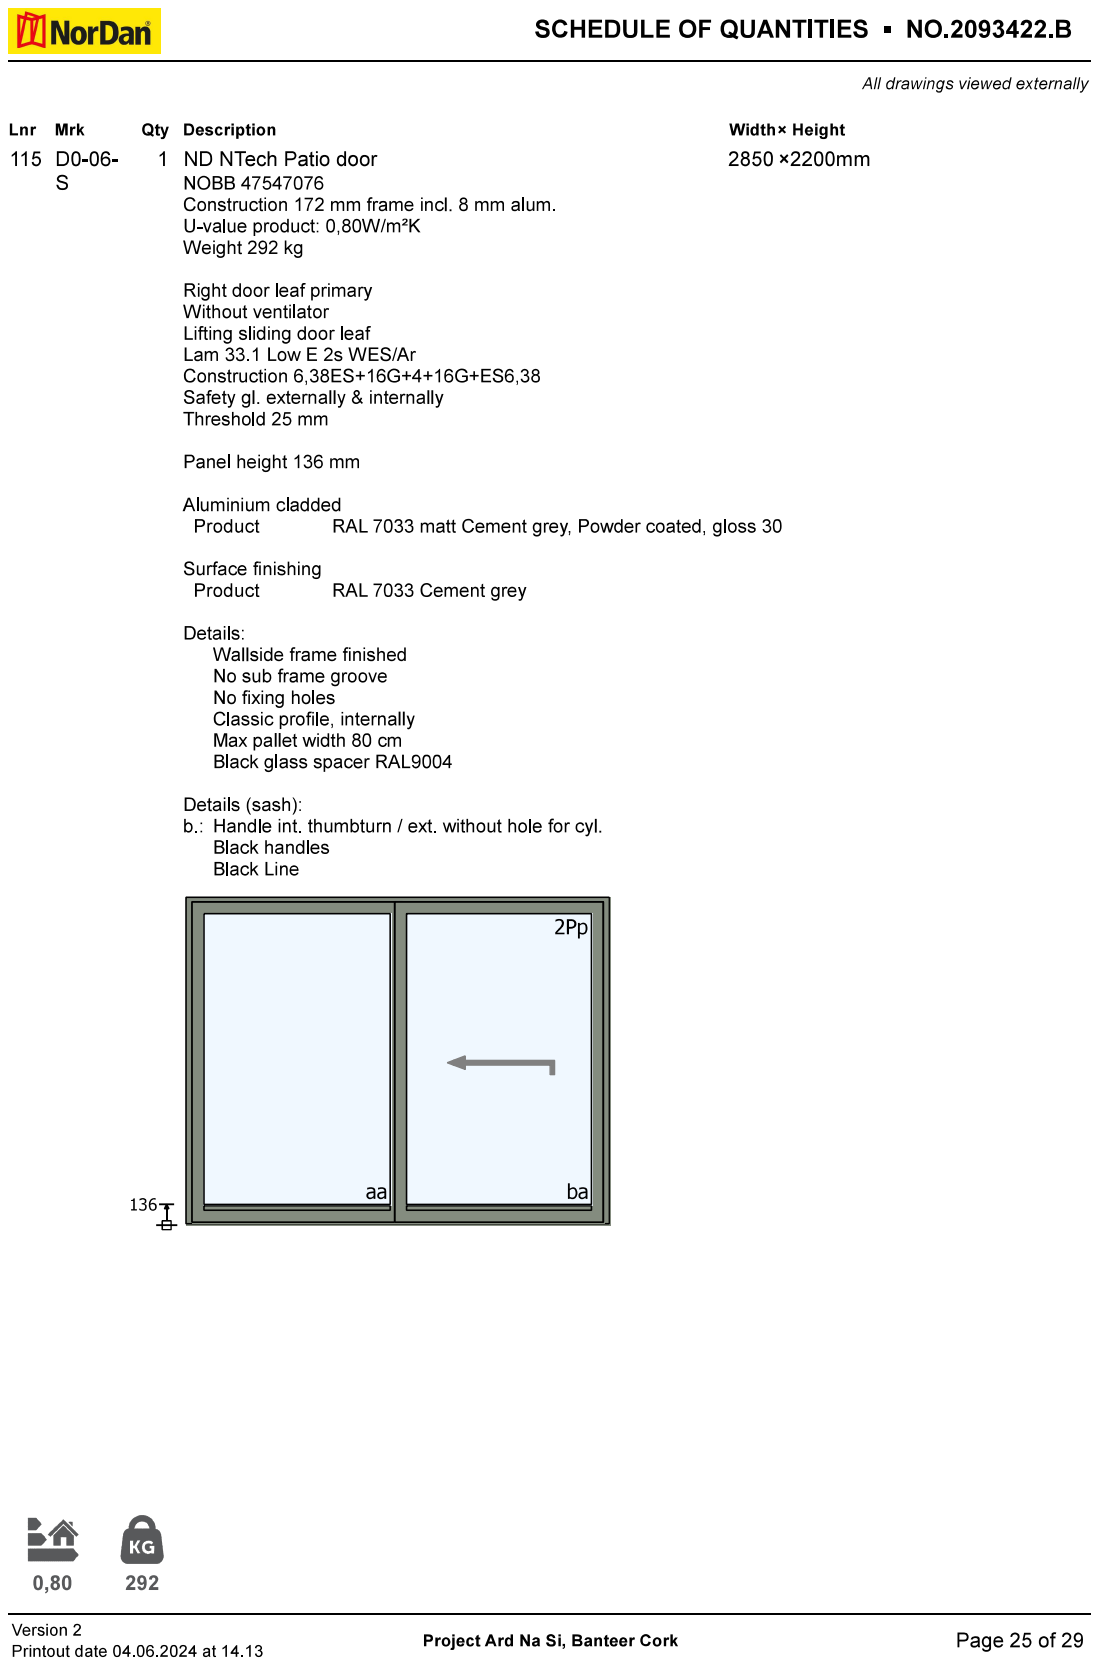
[picture p331: page 25]

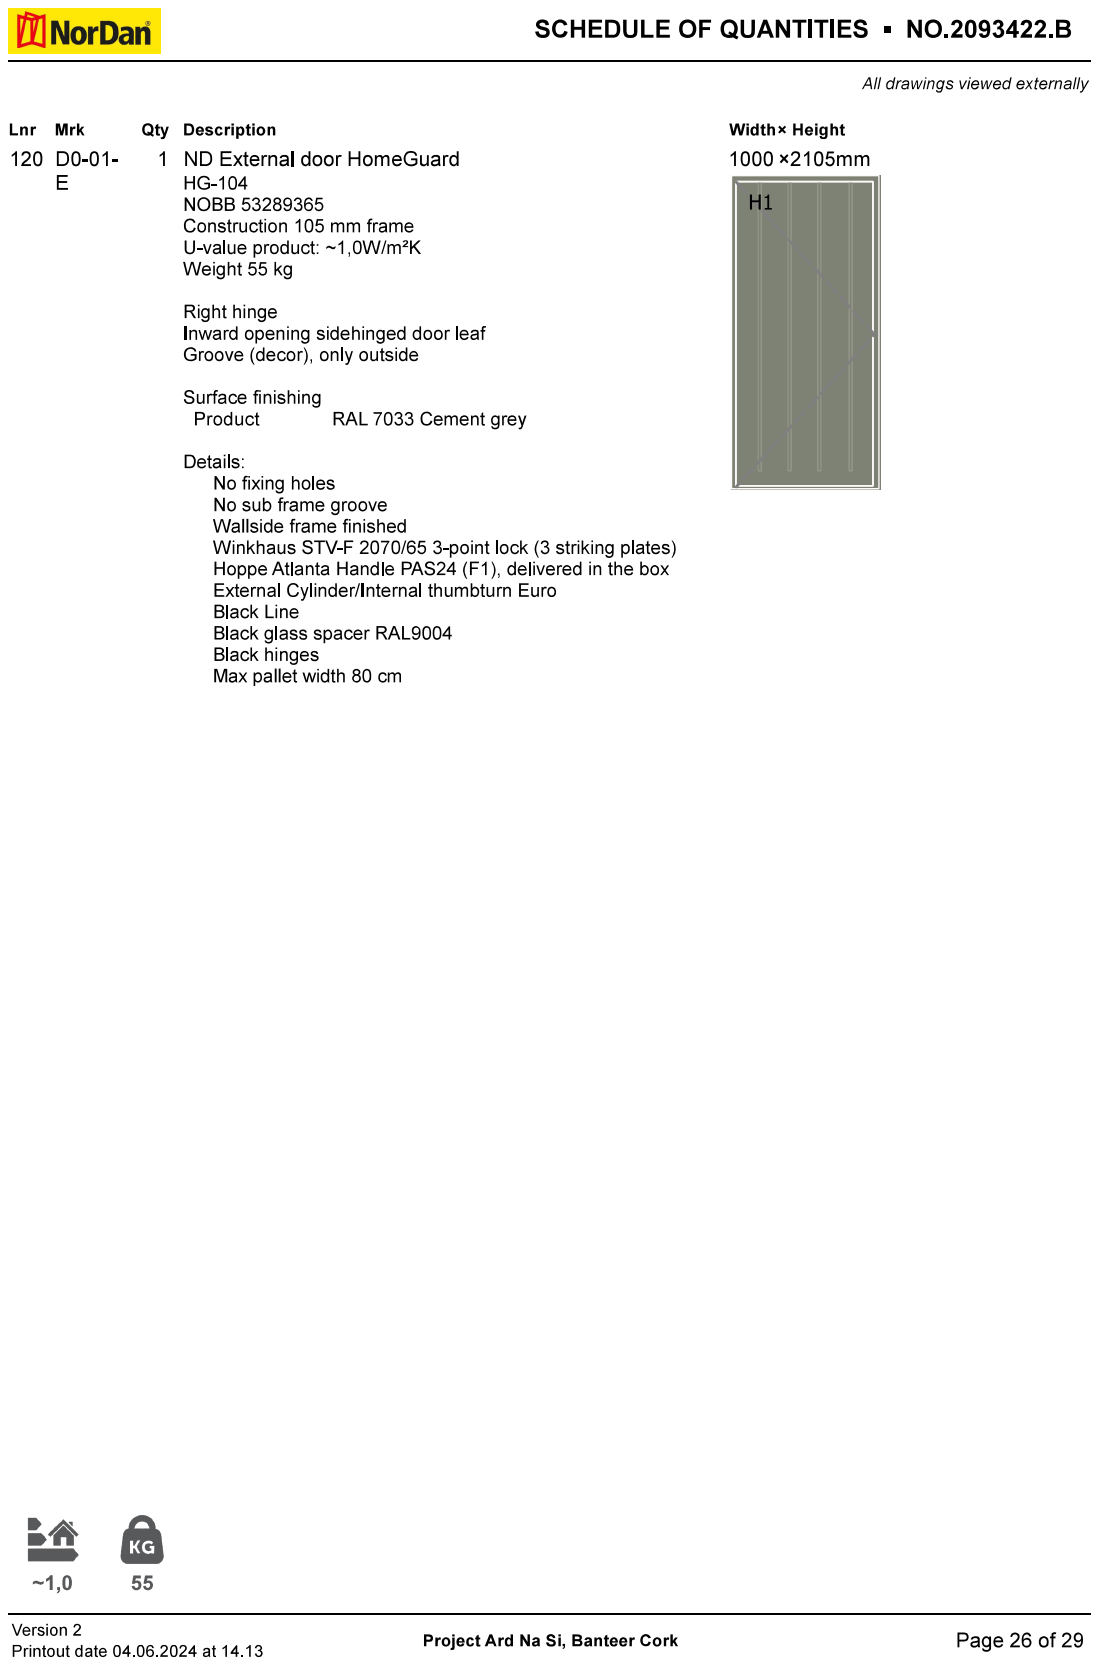
[picture p332: page 26]

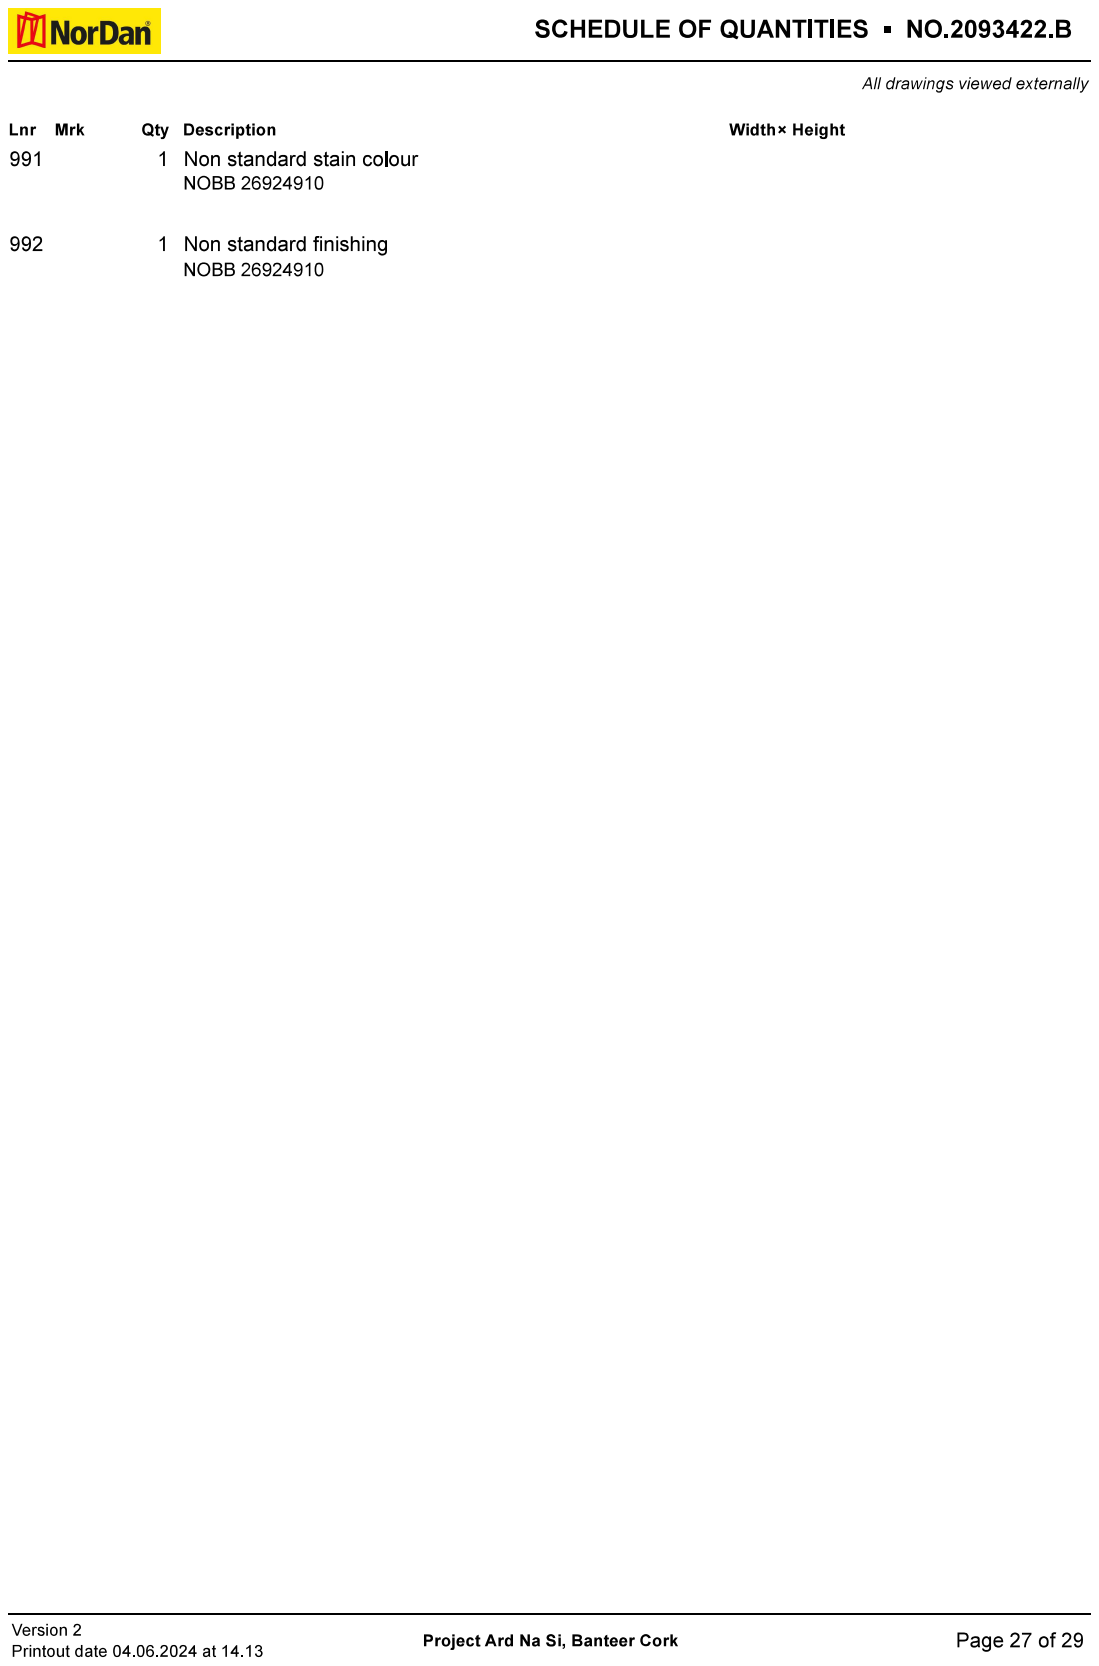
[picture p333: page 27]

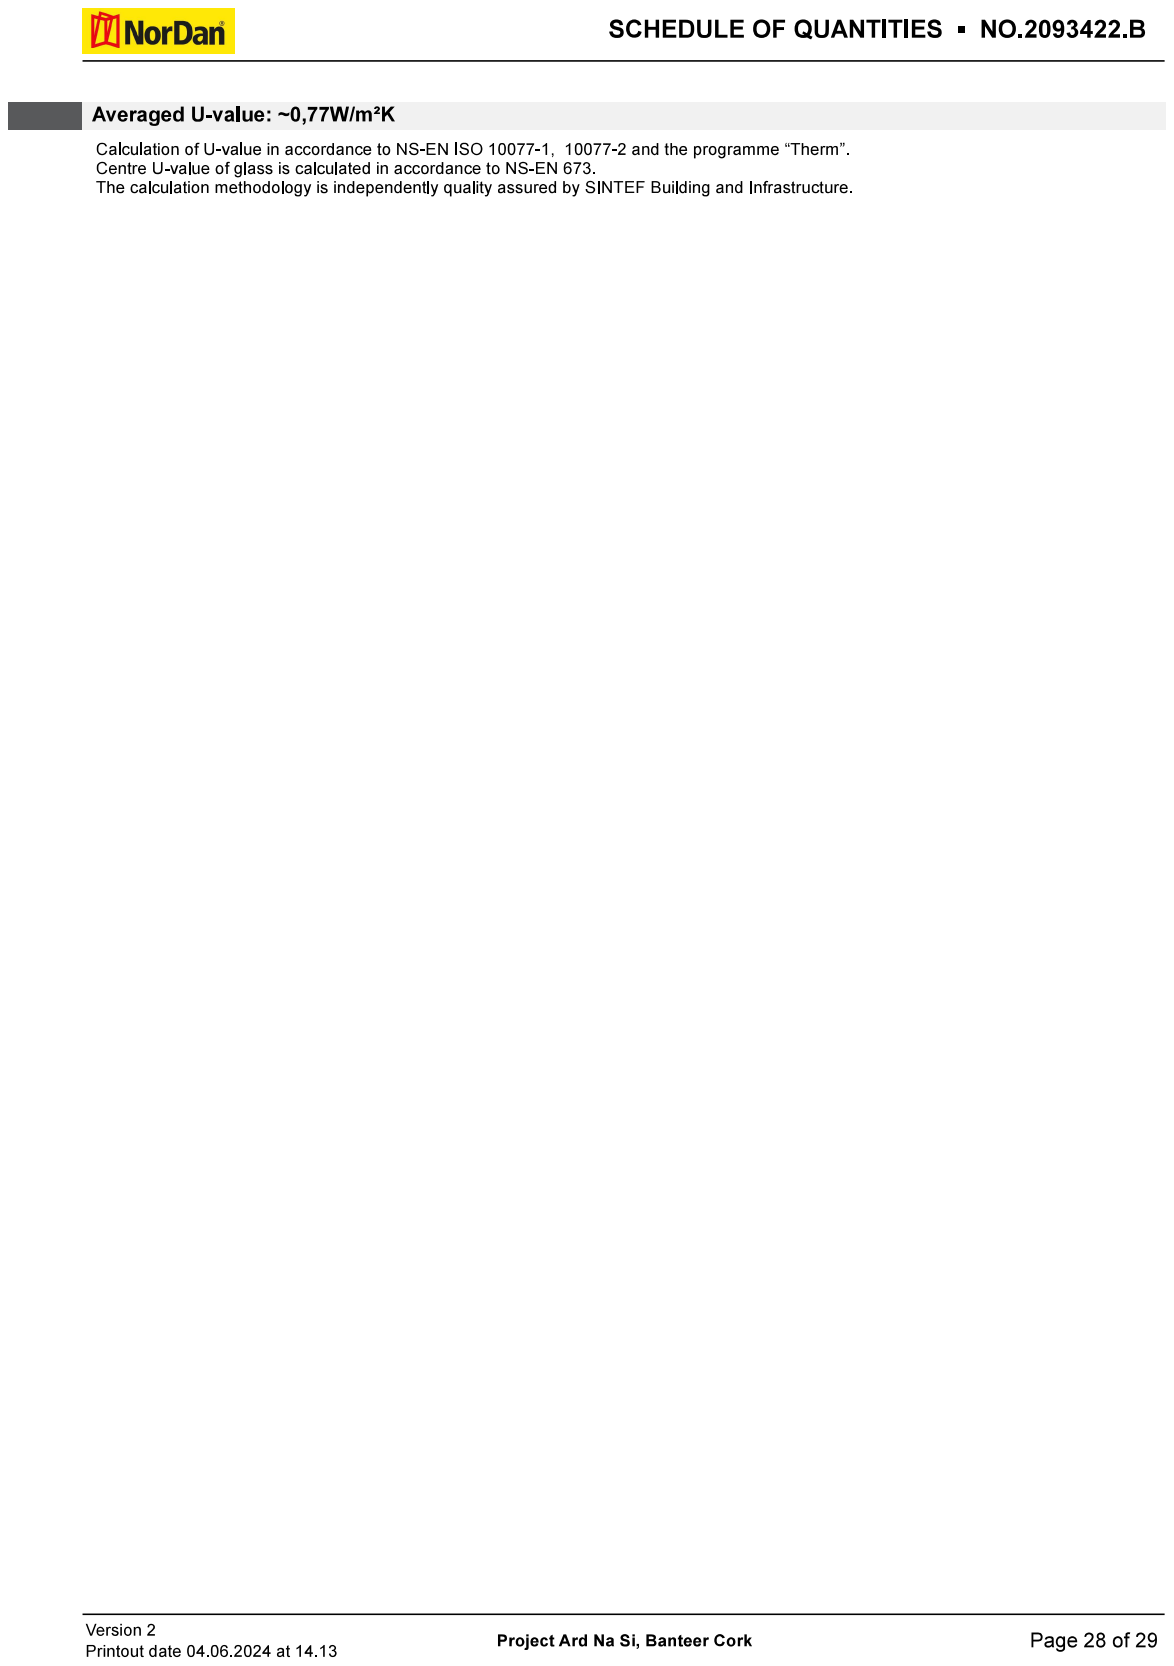
[picture p334: page 28]

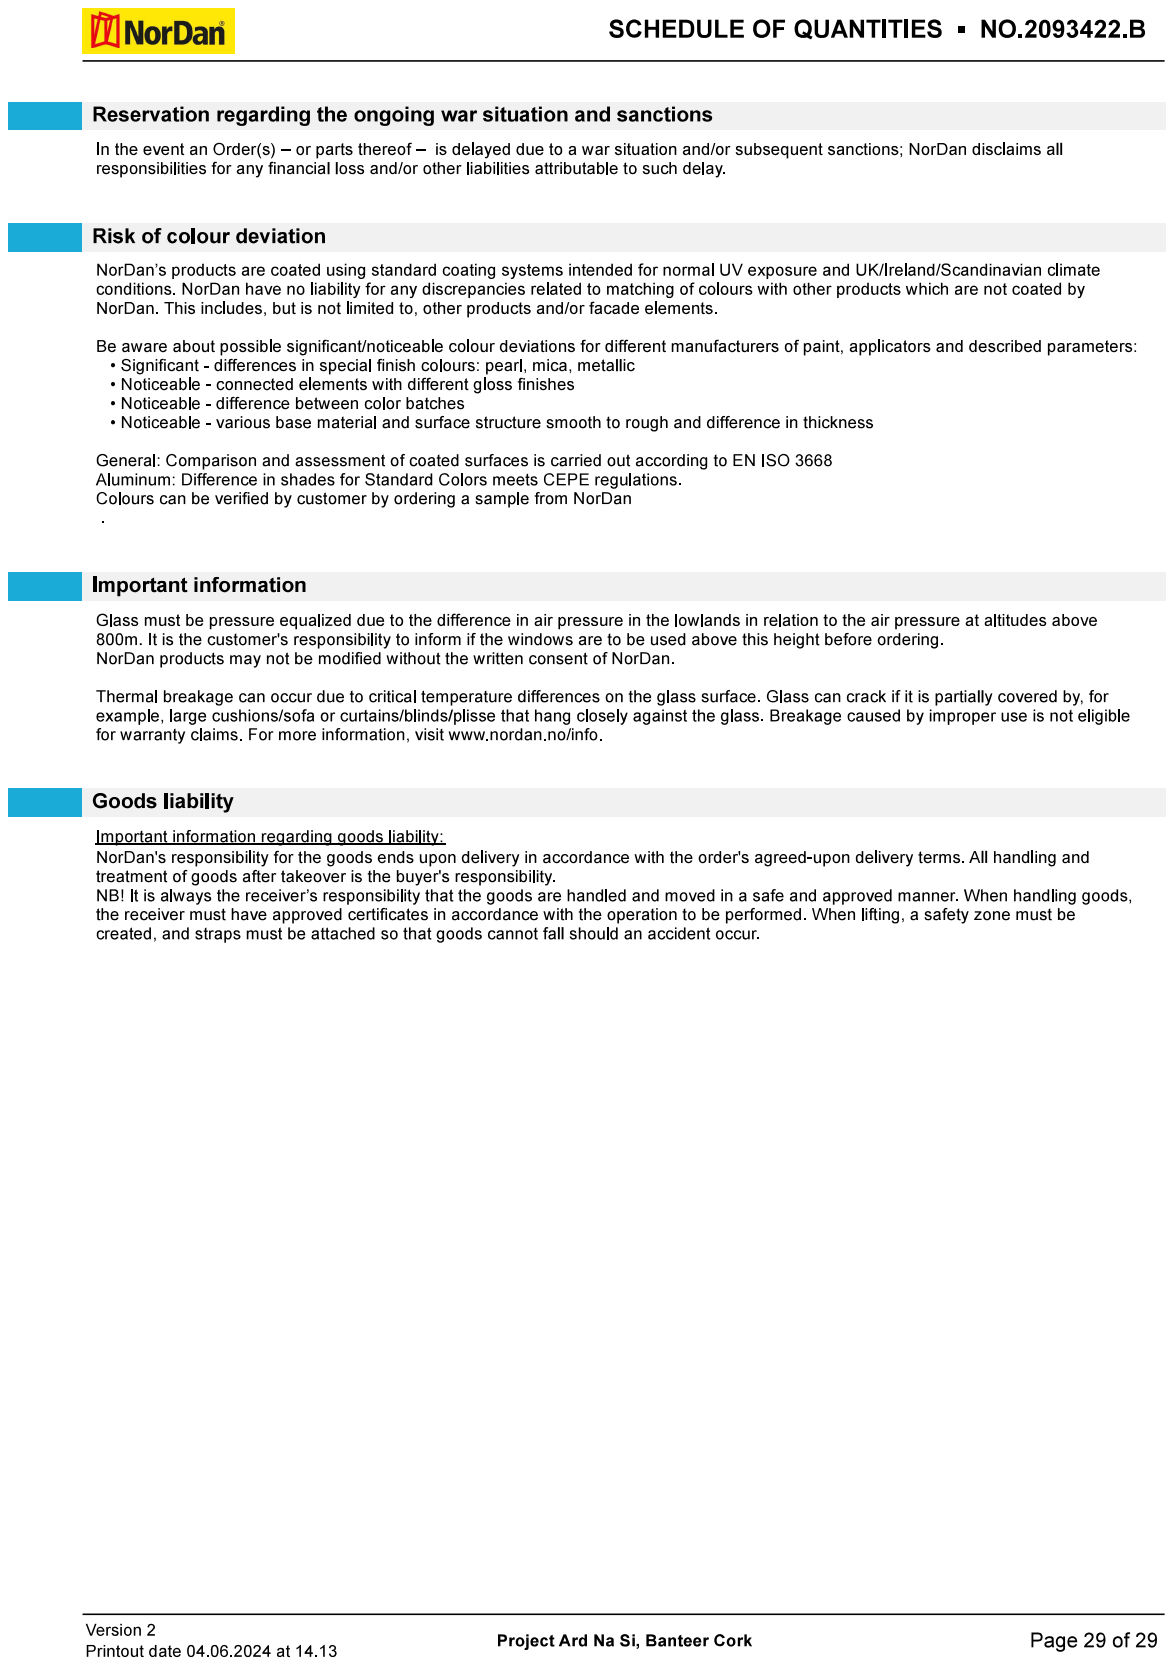
[picture p335: page 29]
