ned14/HouseBuild/images/202208/20220830_123849.jpg

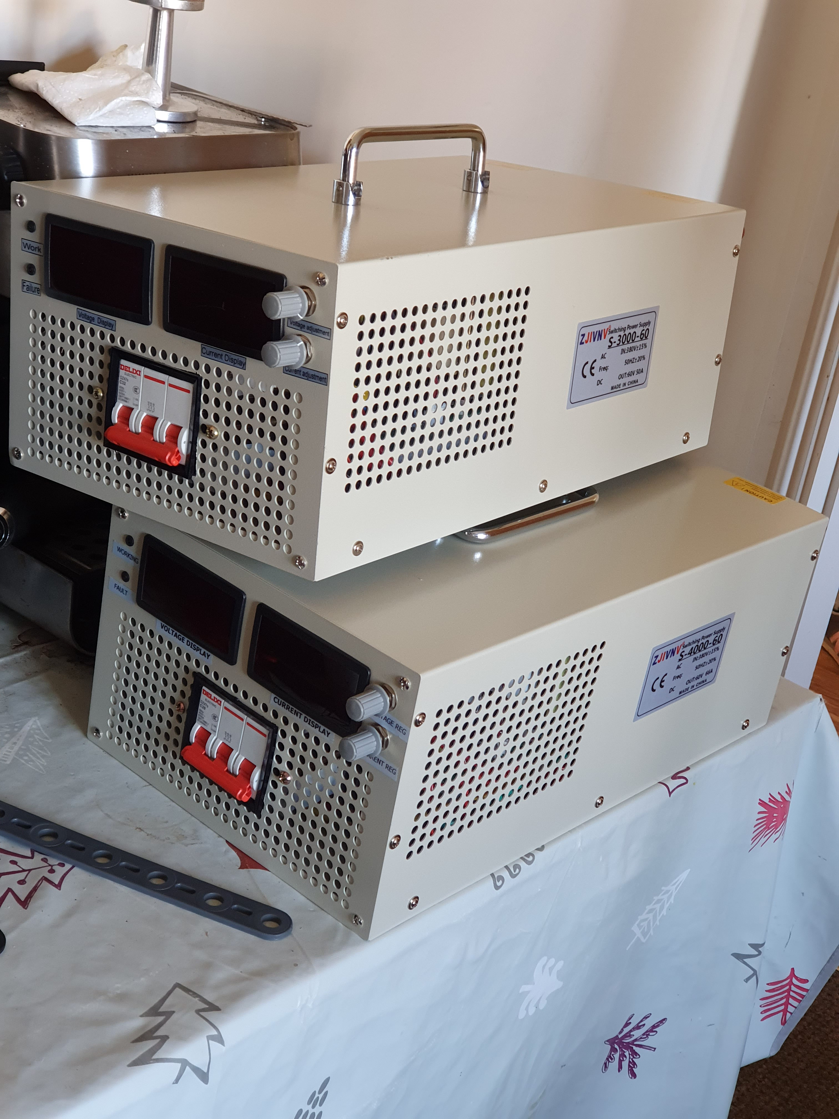
images/202208/20220830_123849.jpg
