ned14/HouseBuild/images/202209/20220919 Wngu5059960 - 1.jpg

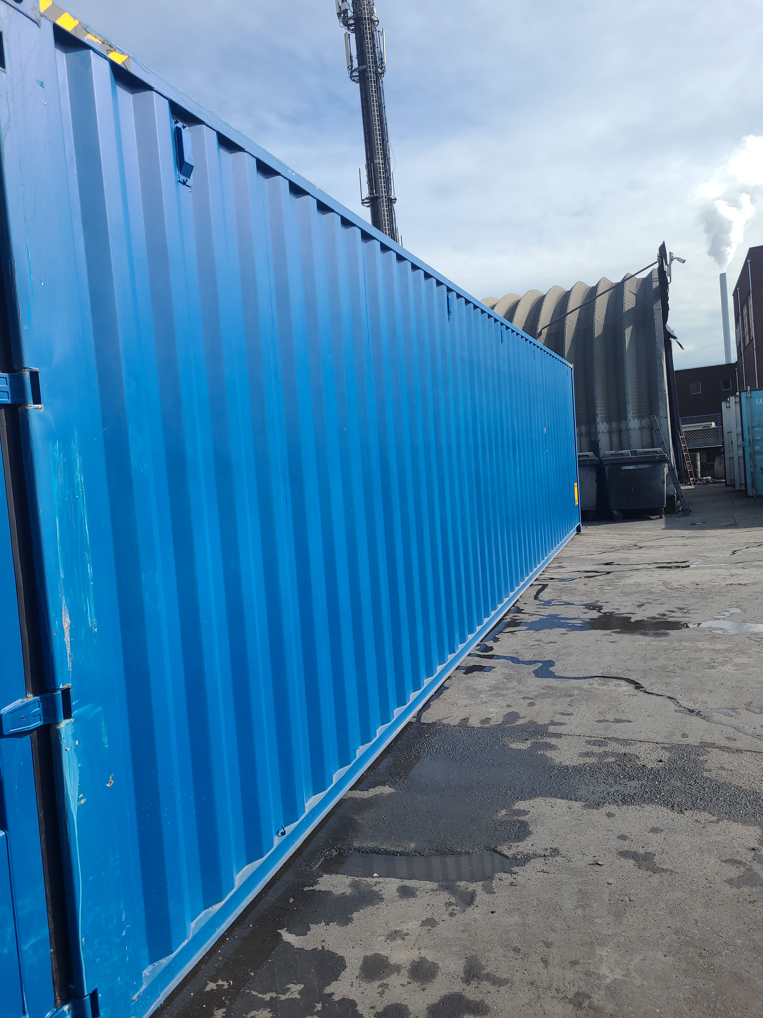
images/202209/20220919 Wngu5059960 - 1.jpg
