ned14/HouseBuild/images/202212/20221205_120620.jpg

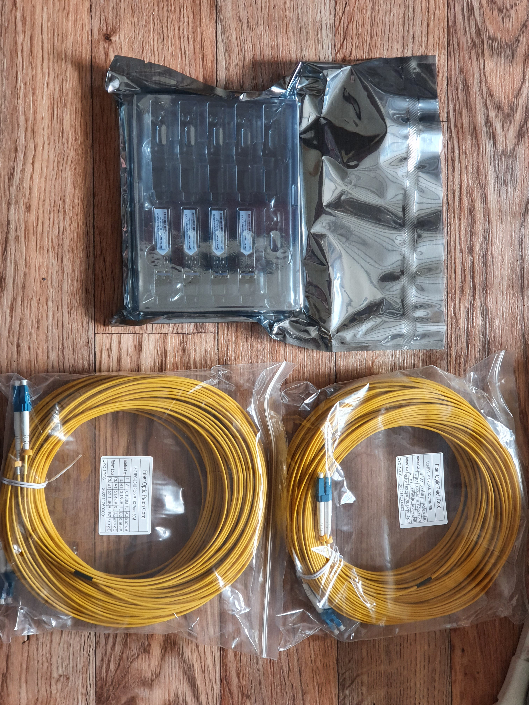
images/202212/20221205_120620.jpg
