ned14/HouseBuild/images/202212/20221210_172416.jpg

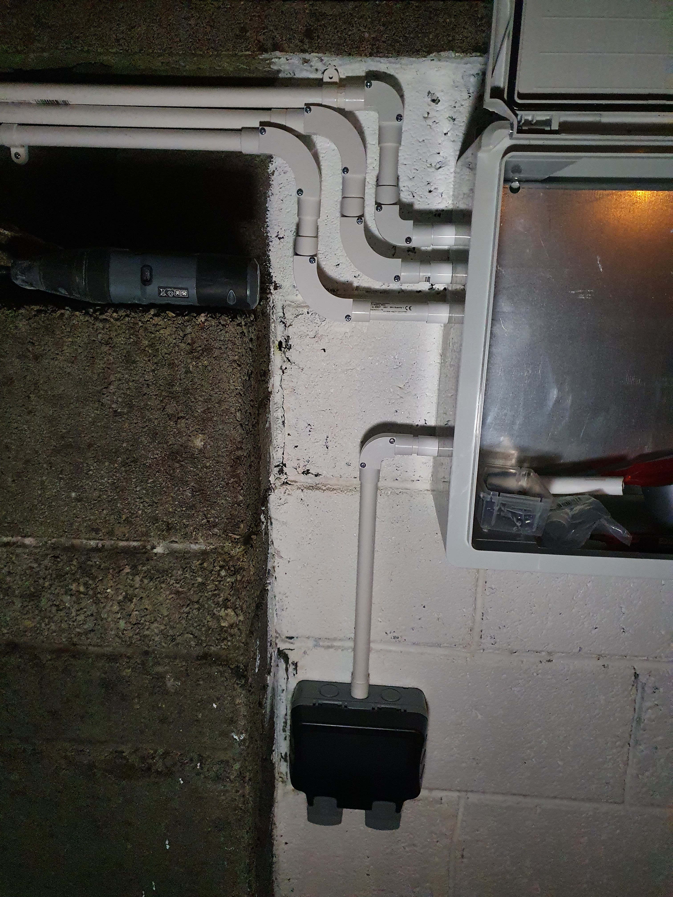
images/202212/20221210_172416.jpg
