ned14/HouseBuild/images/202301/20230114_024928.jpg

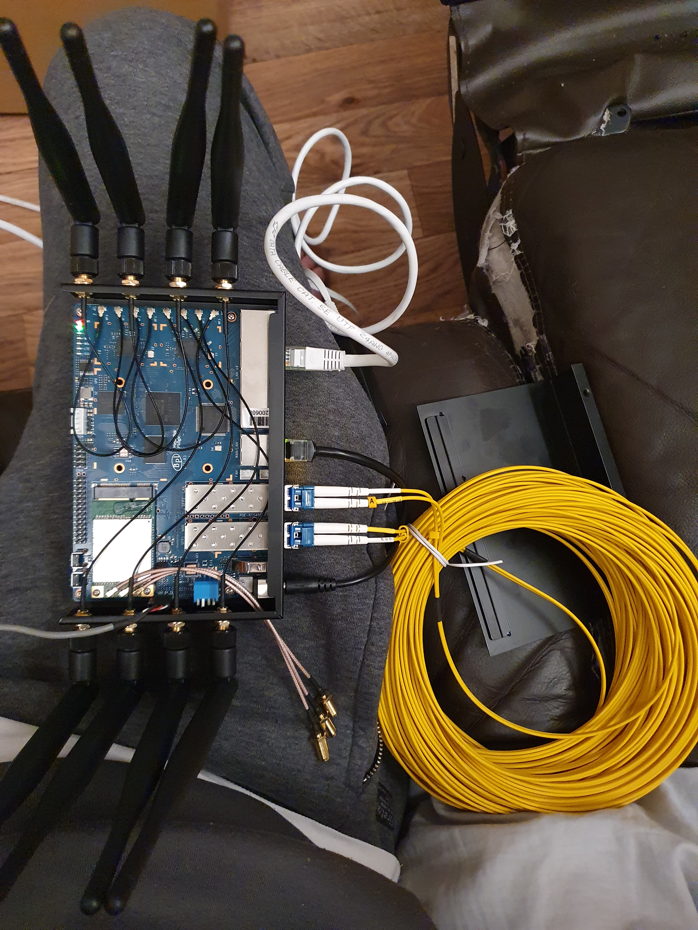
images/202301/20230114_024928.jpg
