ned14/HouseBuild/images/202301/20230116_142414.jpg

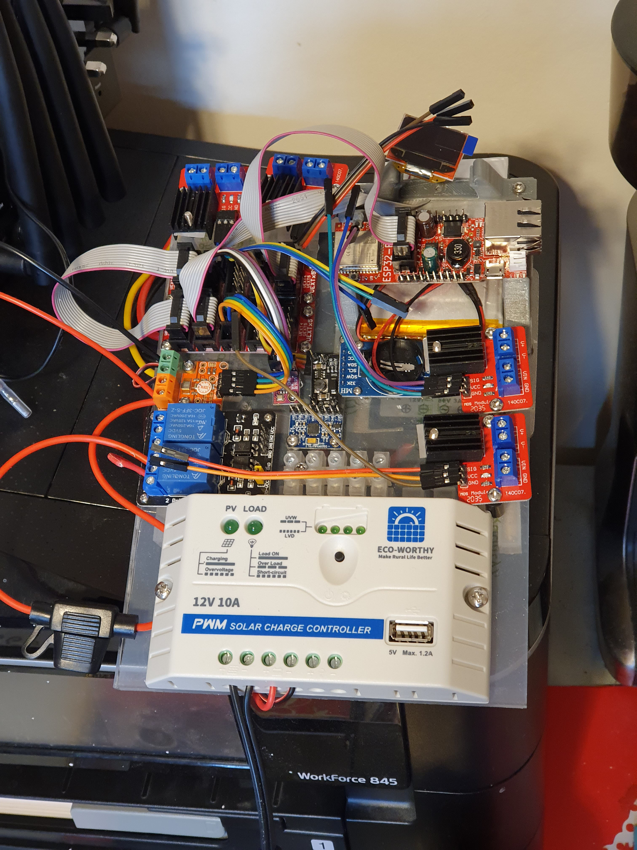
images/202301/20230116_142414.jpg
