ned14/HouseBuild/images/202302/20230202_111032.jpg

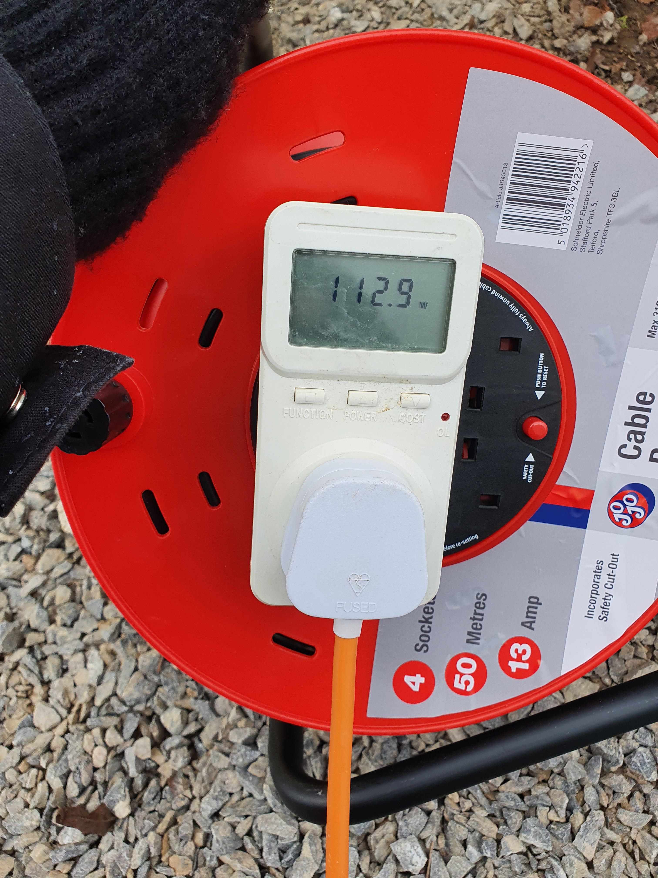
images/202302/20230202_111032.jpg
