ned14/HouseBuild/images/202302/20230202_112117.jpg

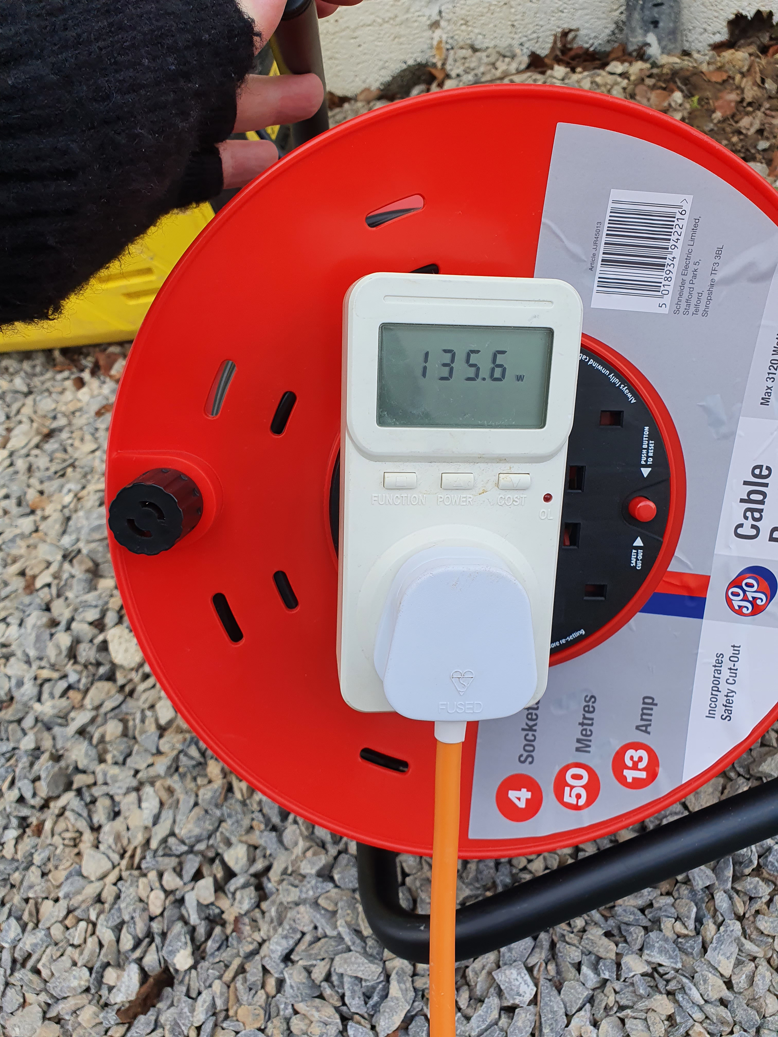
images/202302/20230202_112117.jpg
