ned14/HouseBuild/images/202304/20230403_144836.jpg

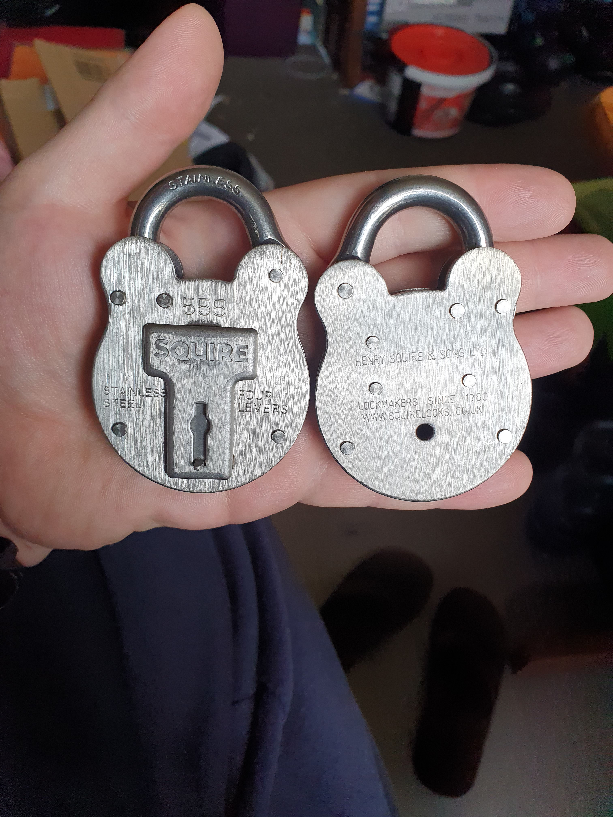
images/202304/20230403_144836.jpg
