ned14/HouseBuild/images/202307/20230730_195517.jpg

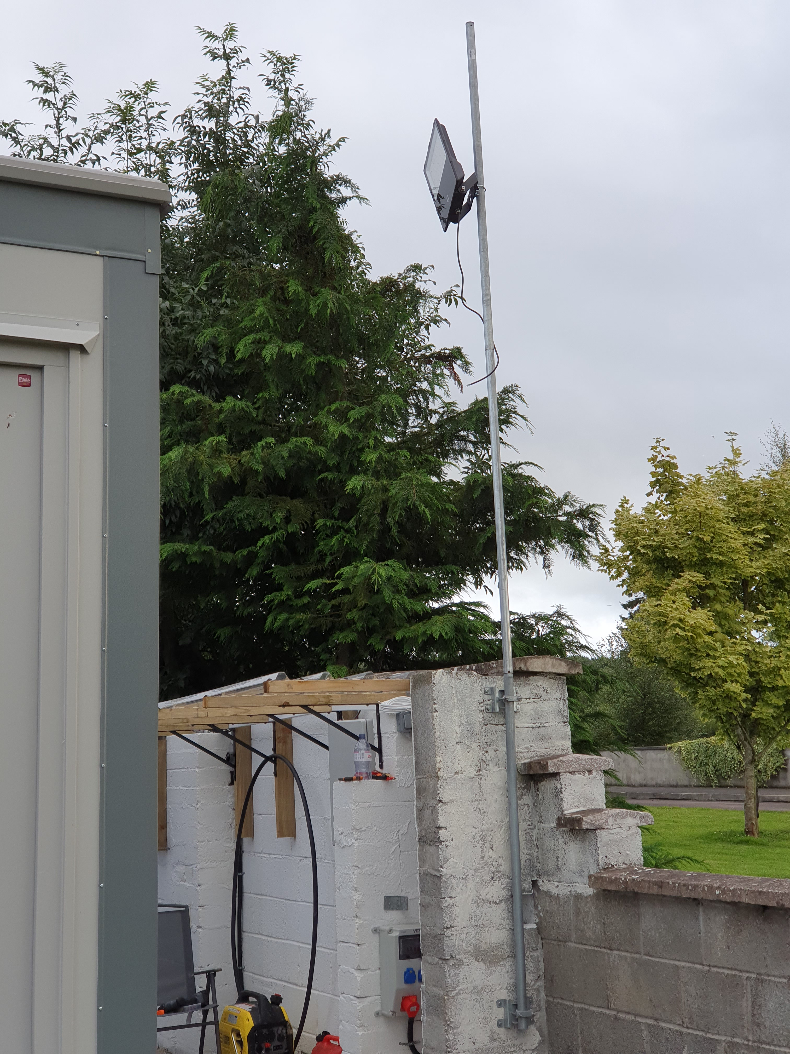
images/202307/20230730_195517.jpg
