ned14/HouseBuild/images/202308/20230806_201441.jpg

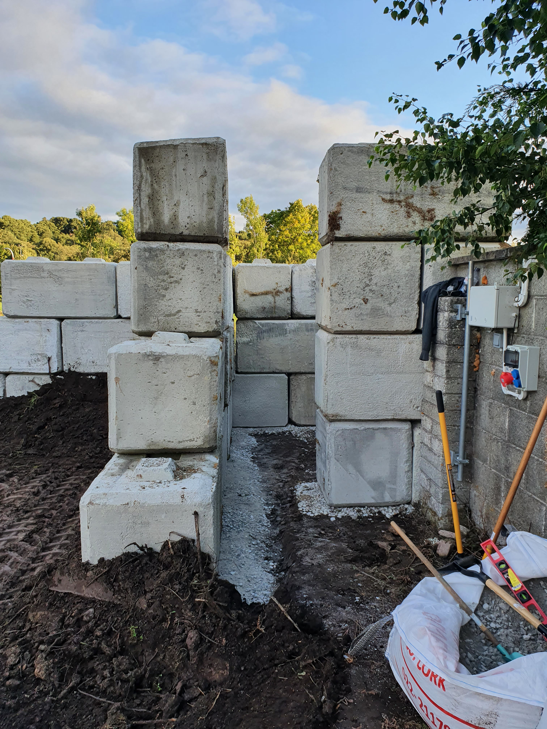
images/202308/20230806_201441.jpg
