ned14/HouseBuild/images/202308/20230815_114045.jpg

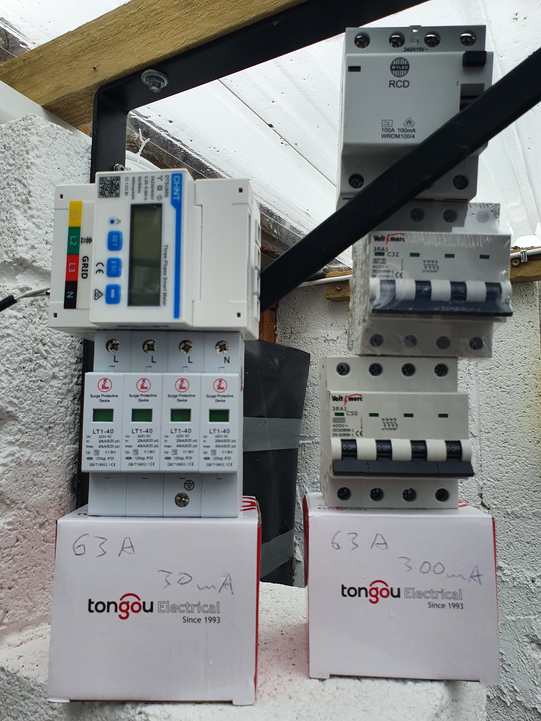
images/202308/20230815_114045.jpg
