ned14/HouseBuild/images/202309/20230910_150509.jpg

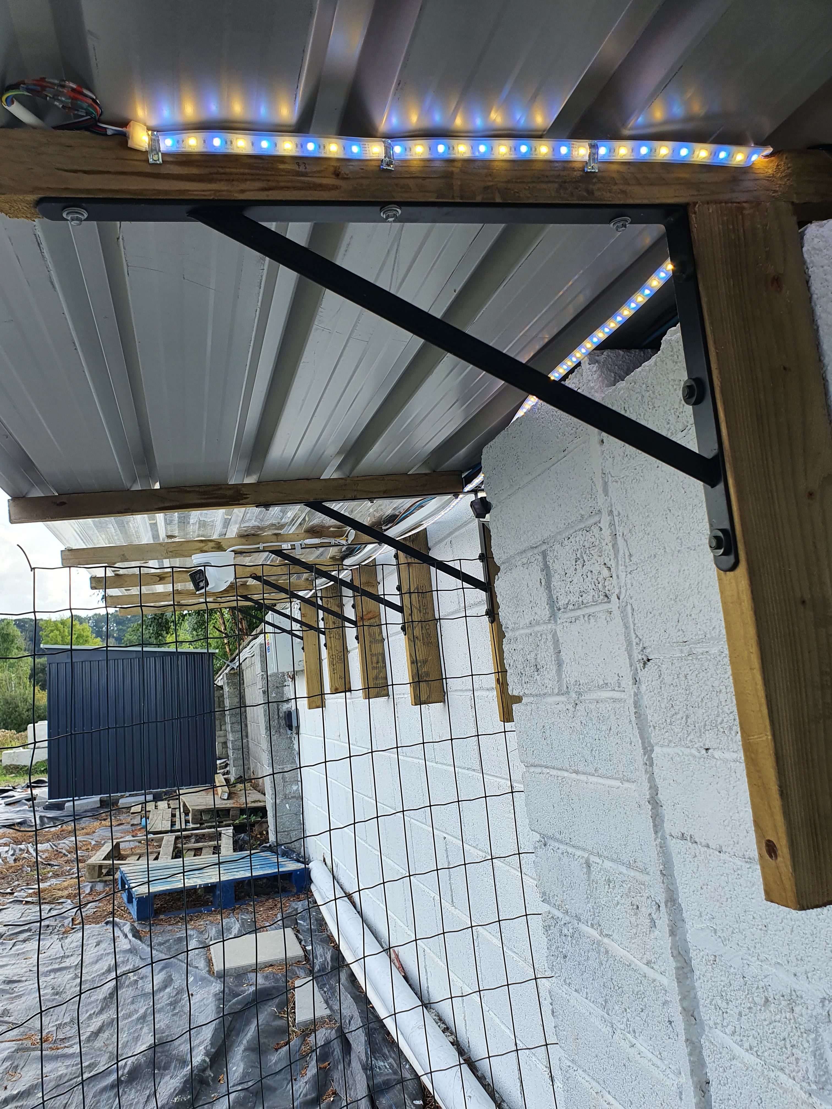
images/202309/20230910_150509.jpg
