ned14/HouseBuild/images/202309/20230910_175250.jpg

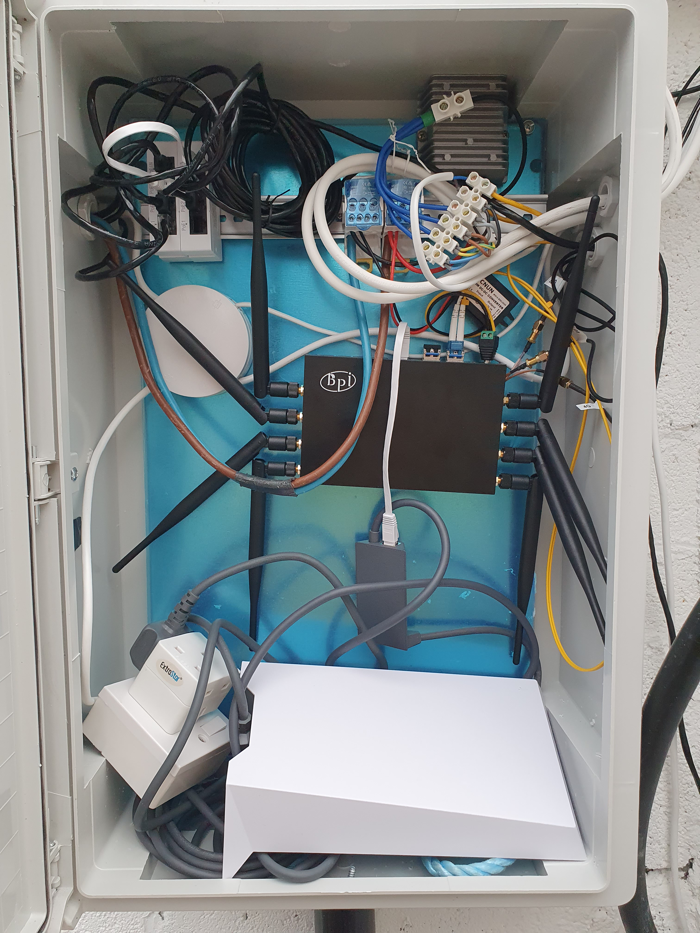
images/202309/20230910_175250.jpg
