ned14/HouseBuild/images/202309/20230916_143900.jpg

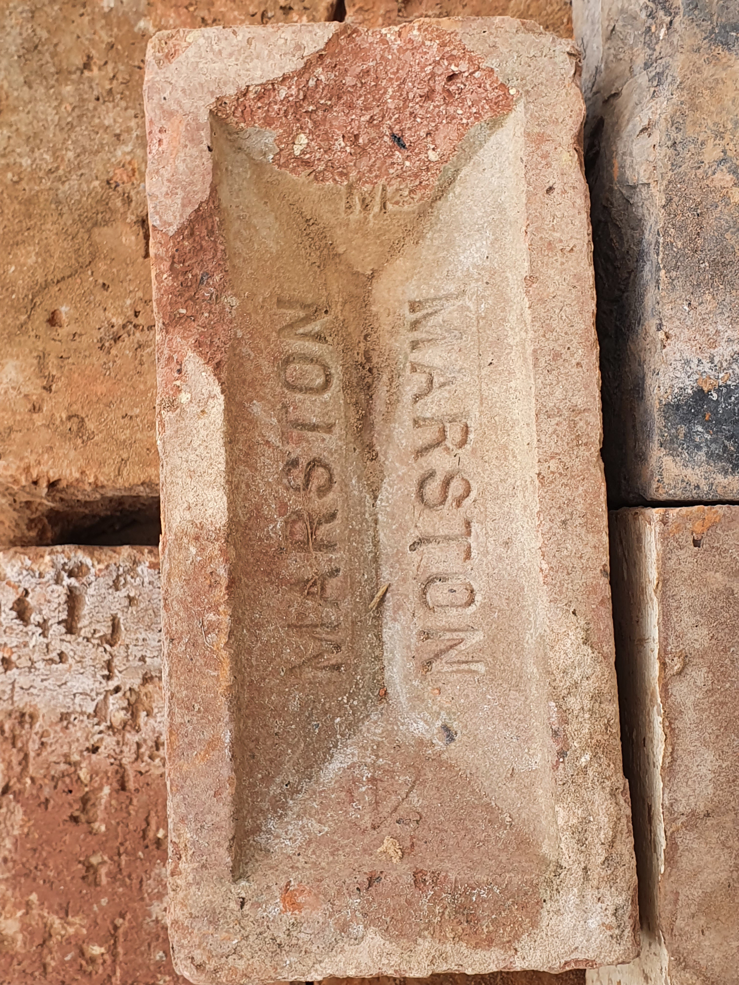
images/202309/20230916_143900.jpg
