ned14/HouseBuild/images/202309/20230918_090235.jpg

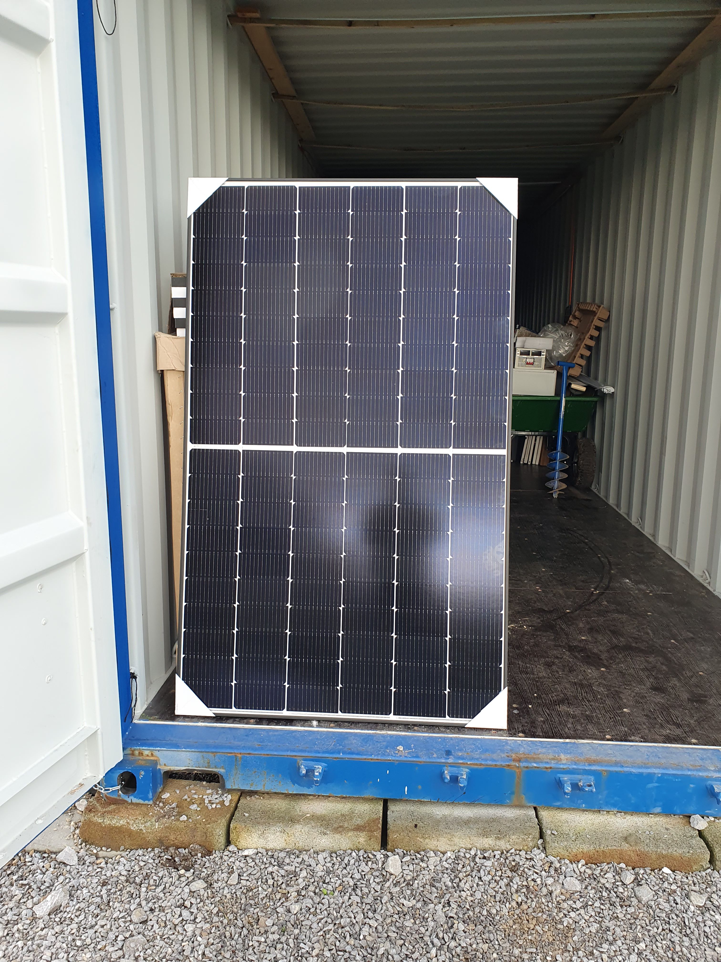
images/202309/20230918_090235.jpg
