ned14/HouseBuild/images/202310/20231014_192425.jpg

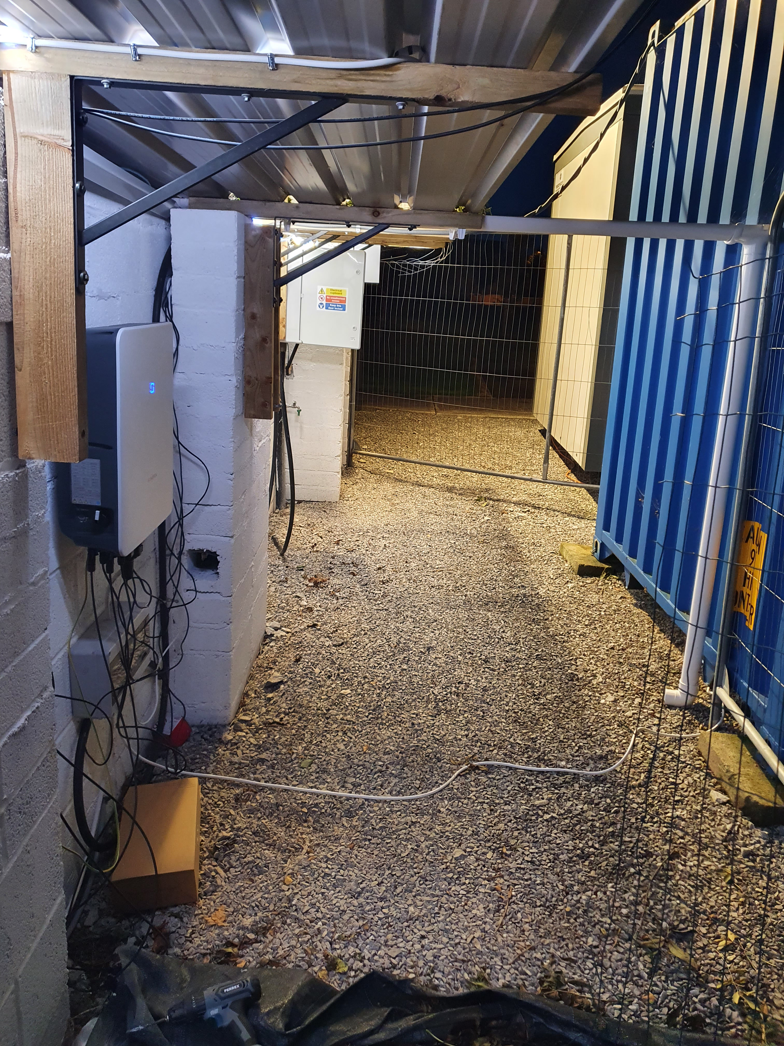
images/202310/20231014_192425.jpg
