ned14/HouseBuild/images/202312/20231214_141844.jpg

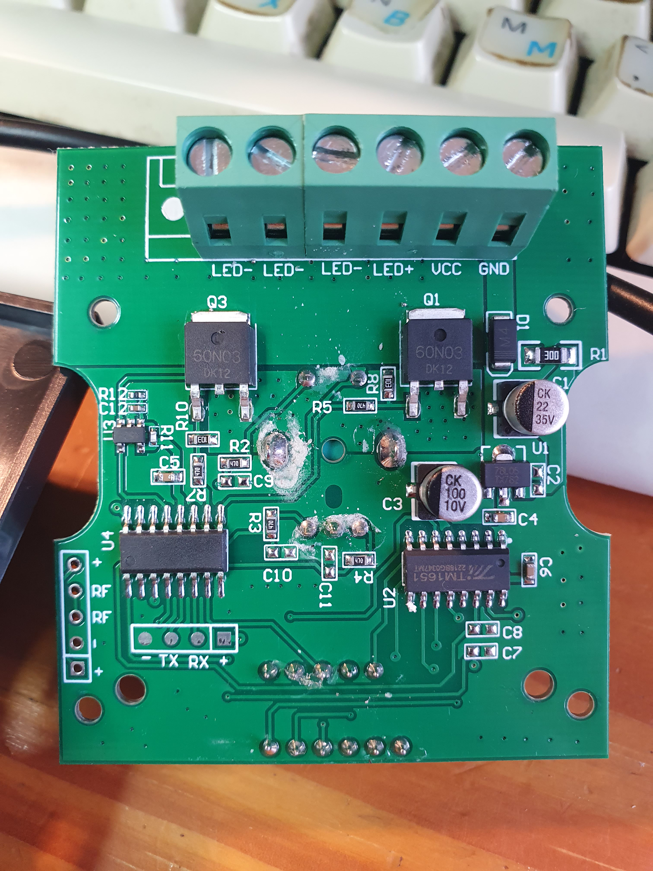
images/202312/20231214_141844.jpg
