ned14/HouseBuild/images/202312/20231217_021611.jpg

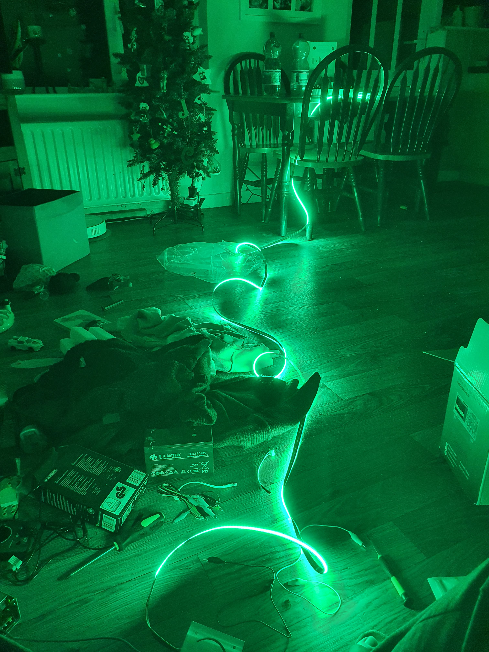
images/202312/20231217_021611.jpg
