ned14/HouseBuild/images/202403/20240323_114231.jpg

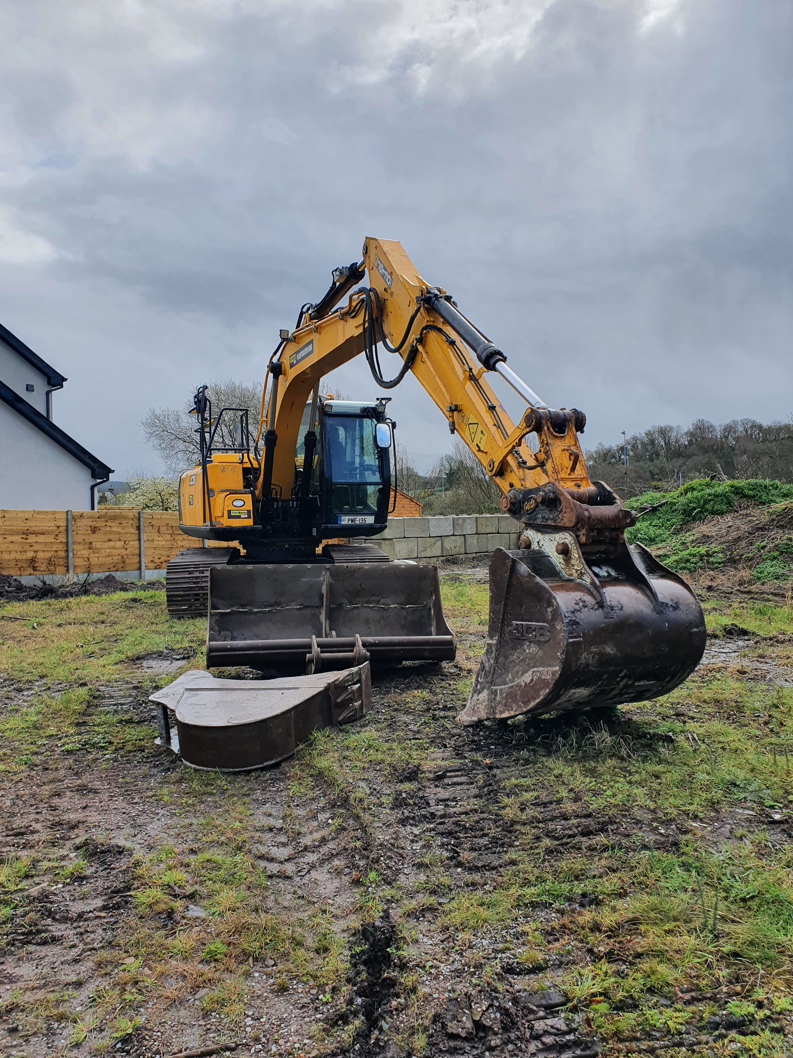
images/202403/20240323_114231.jpg
