ned14/HouseBuild/images/202406/20240628_104237.jpg

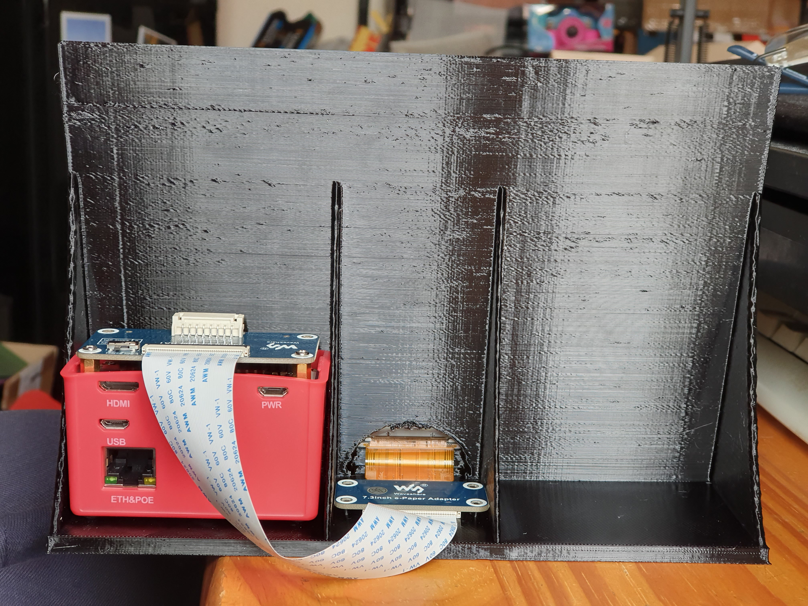
images/202406/20240628_104237.jpg
